nikolafilip/nibble/boards/03-sequencer/fab/sequencer-top.png

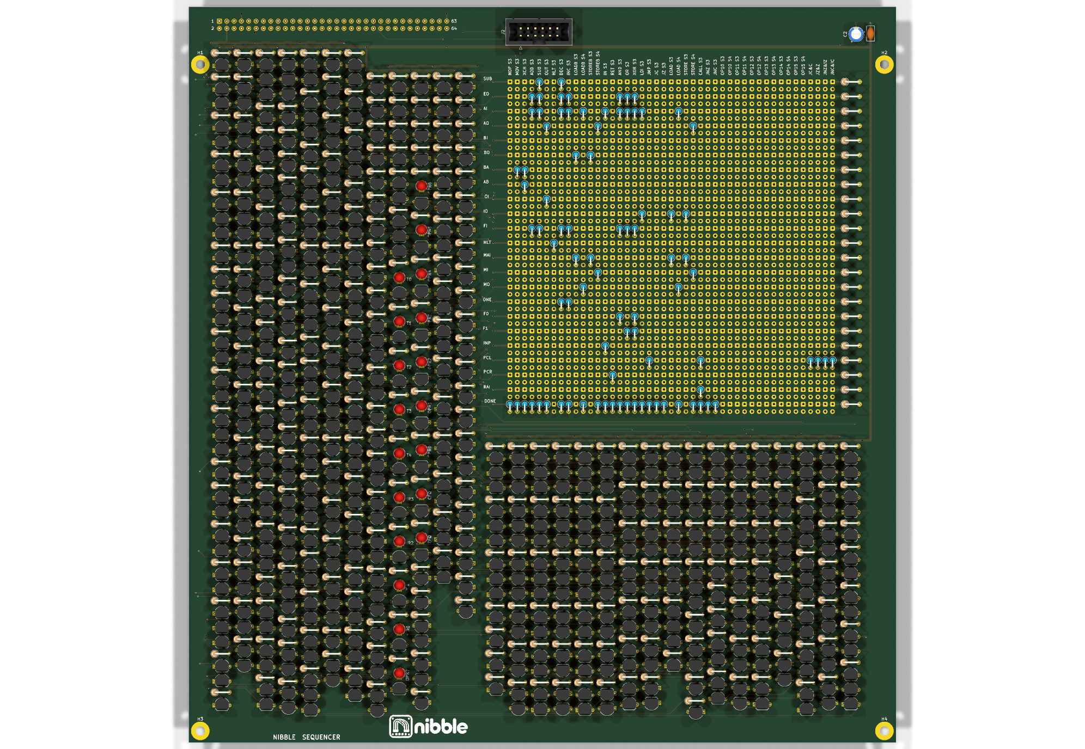
boards/03-sequencer/fab/sequencer-top.png
