nikolafilip/nibble/boards/01-alu/fab/alu-bottom.png

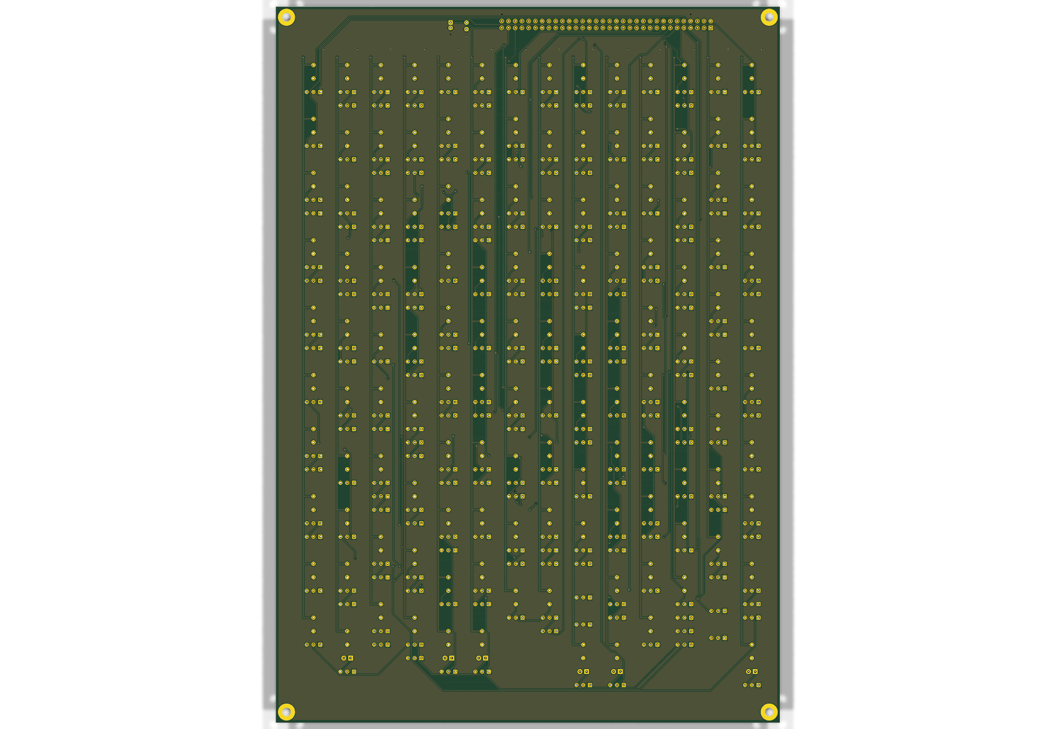
boards/01-alu/fab/alu-bottom.png
