nikolafilip/nibble/boards/01-alu/fab/alu-top.png

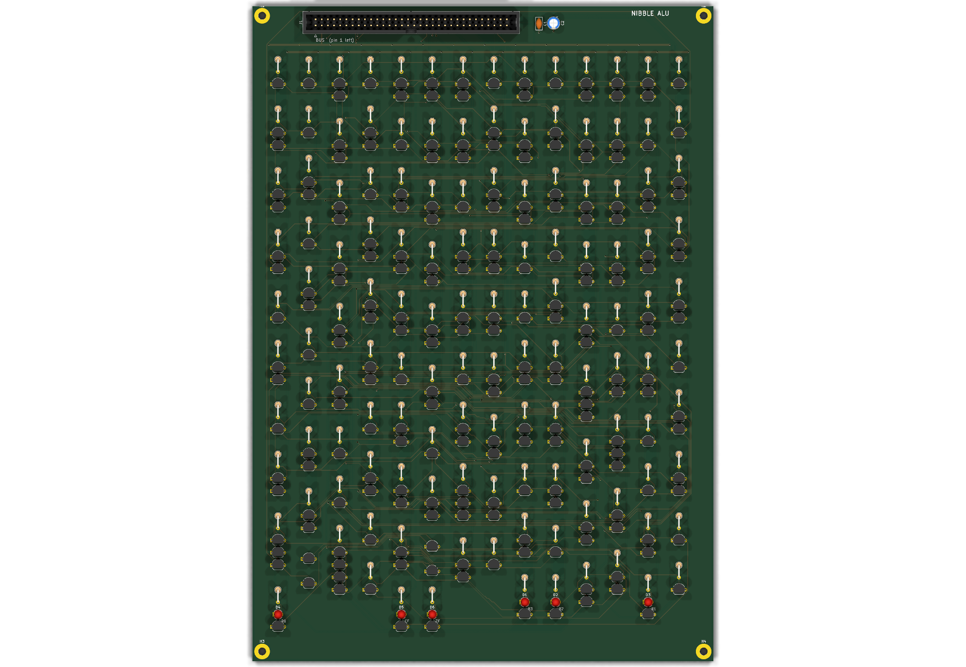
boards/01-alu/fab/alu-top.png
