nikolafilip/nibble/boards/03-sequencer/fab/sequencer-bottom.png

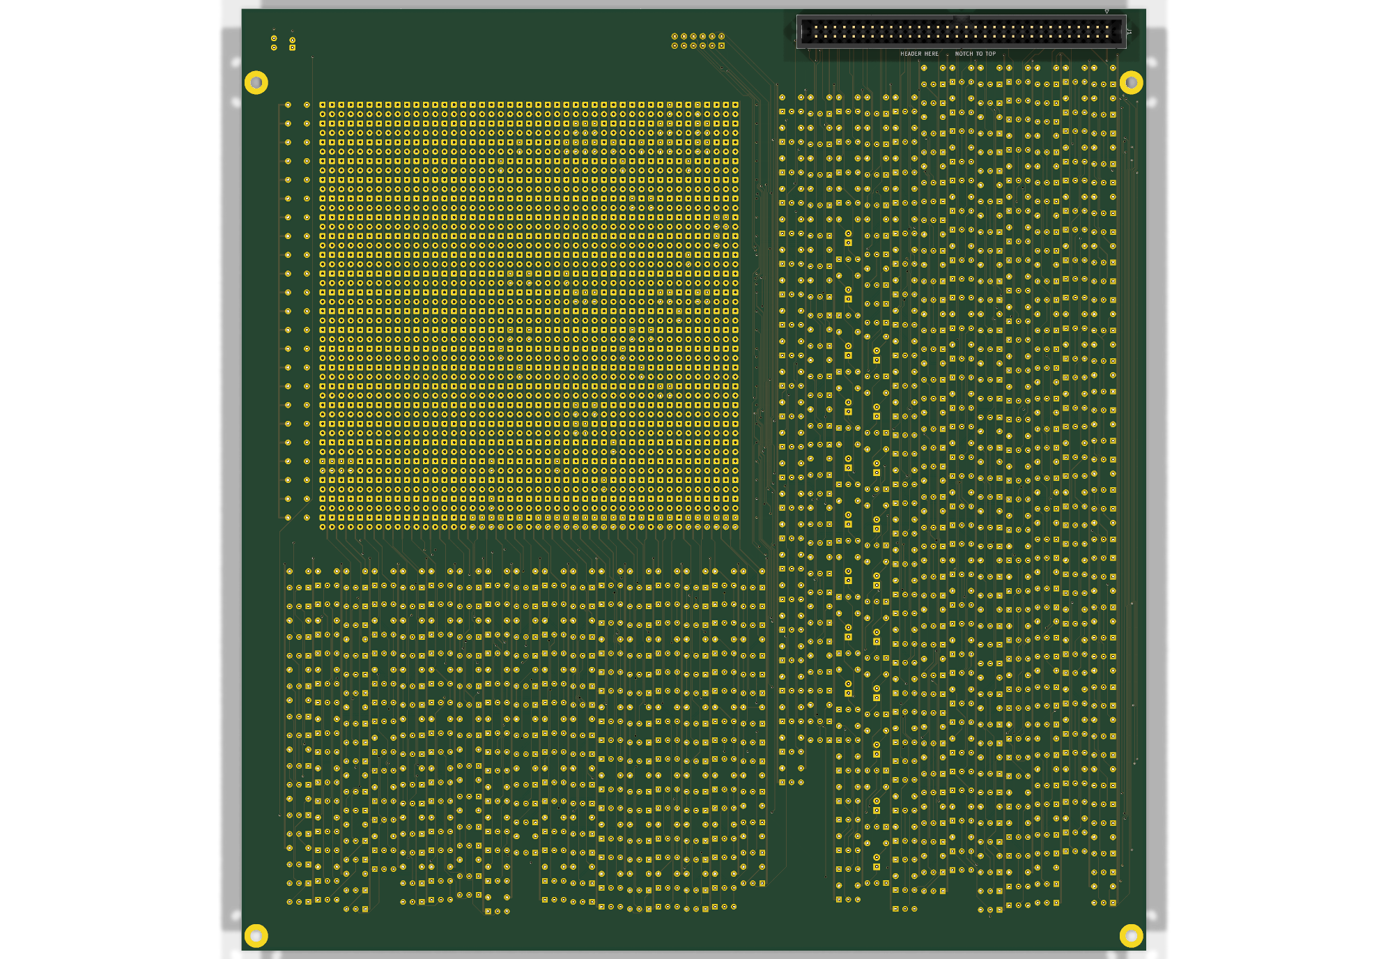
boards/03-sequencer/fab/sequencer-bottom.png
