nikolafilip/nibble/boards/06-panel/fab/panel-bottom.png

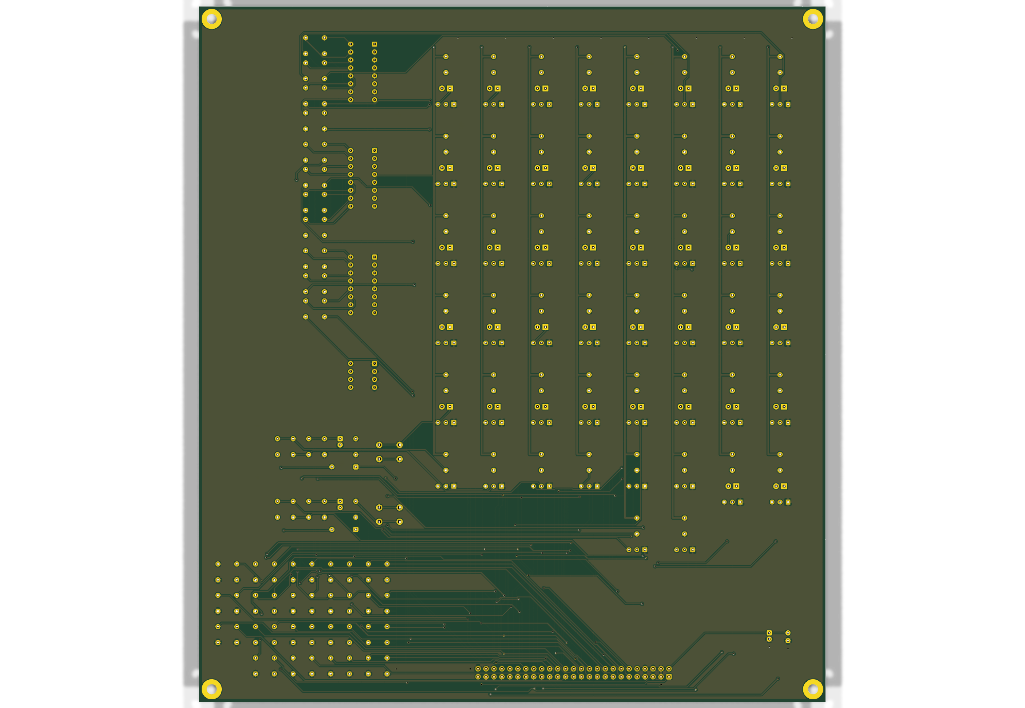
boards/06-panel/fab/panel-bottom.png
