nikolafilip/nibble/boards/06-panel/fab/panel-top.png

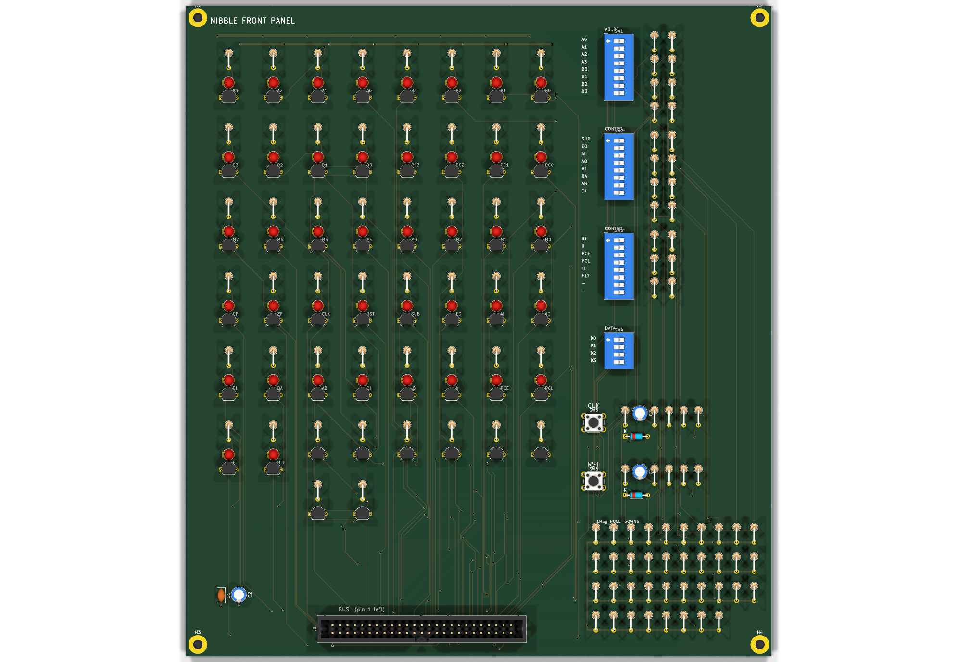
boards/06-panel/fab/panel-top.png
