nikolafilip/nibble/cards/alu0/fab/alu0-bottom.png

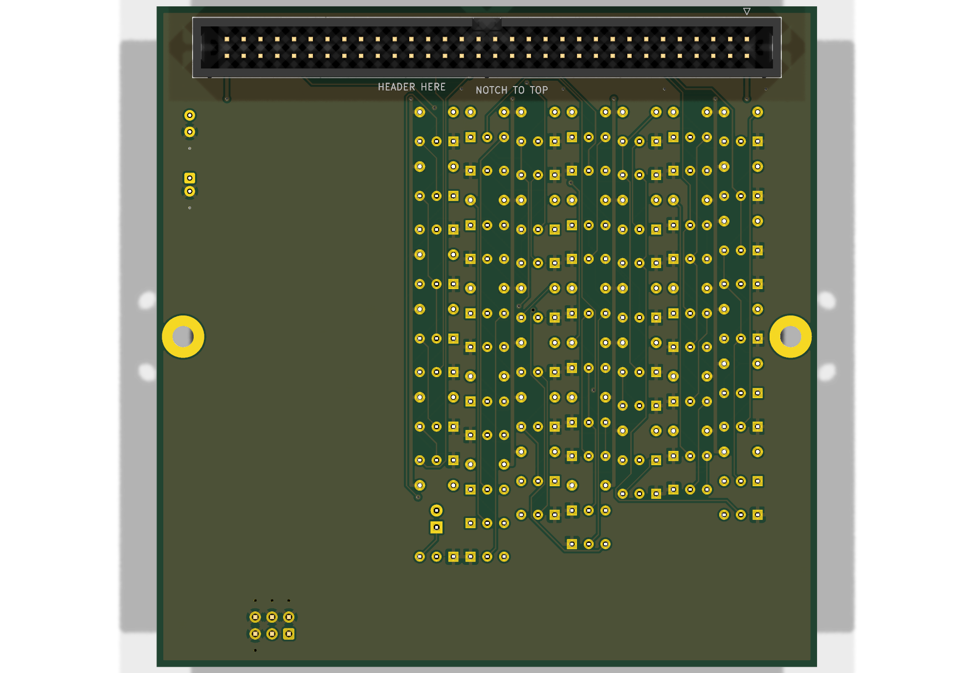
cards/alu0/fab/alu0-bottom.png
