nikolafilip/nibble/cards/alu0/fab/alu0-top.png

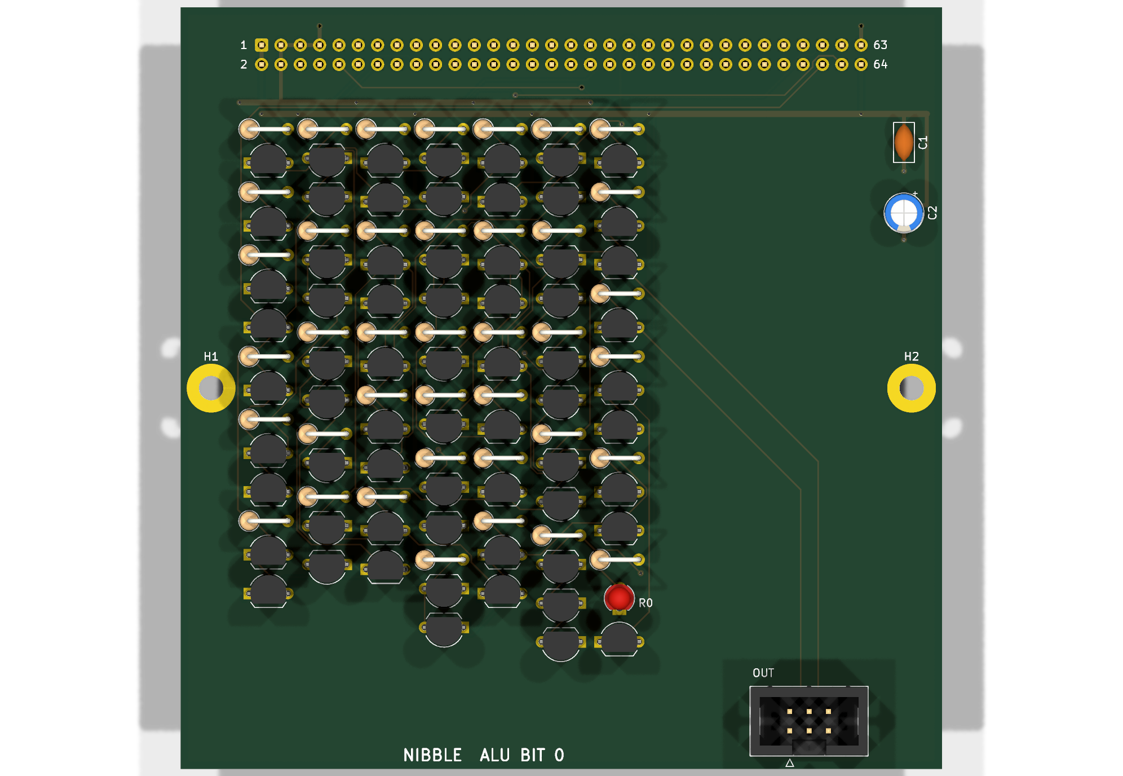
cards/alu0/fab/alu0-top.png
