nikolafilip/nibble/cards/alu1/fab/alu1-bottom.png

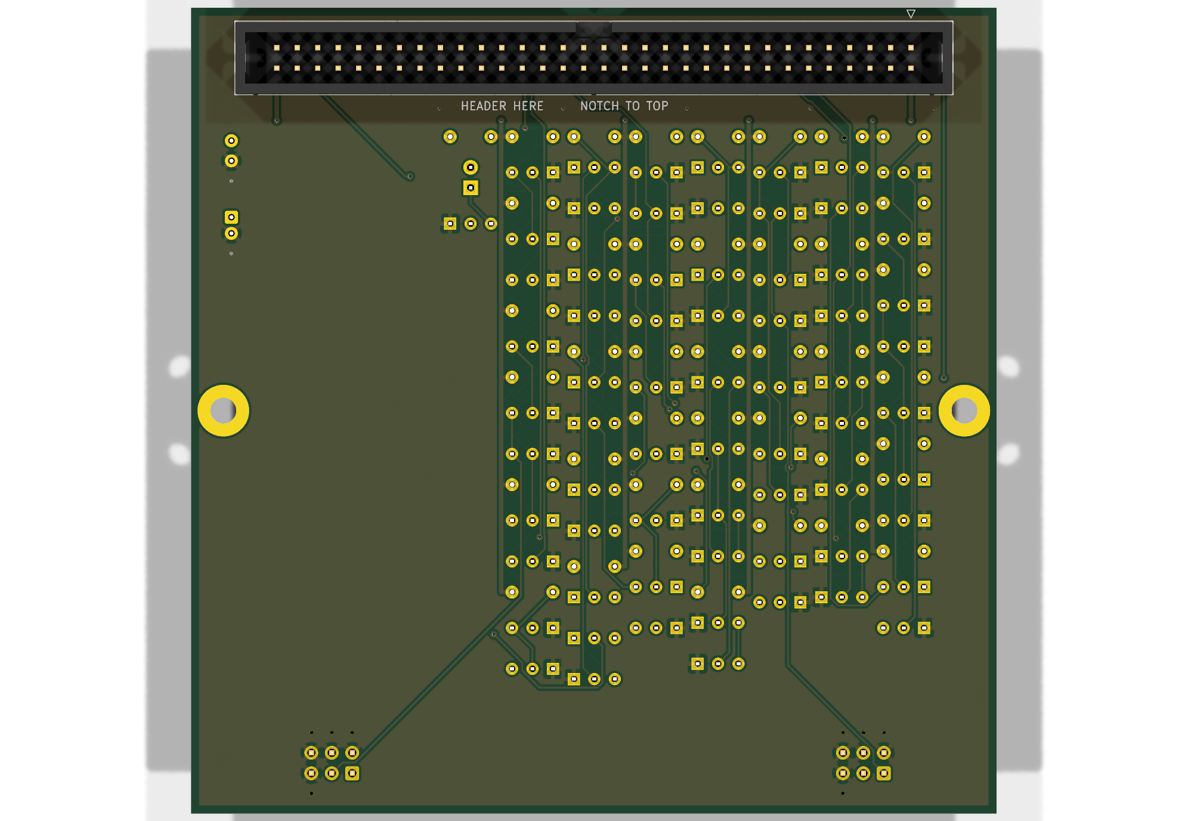
cards/alu1/fab/alu1-bottom.png
