nikolafilip/nibble/cards/alu2/fab/alu2-bottom.png

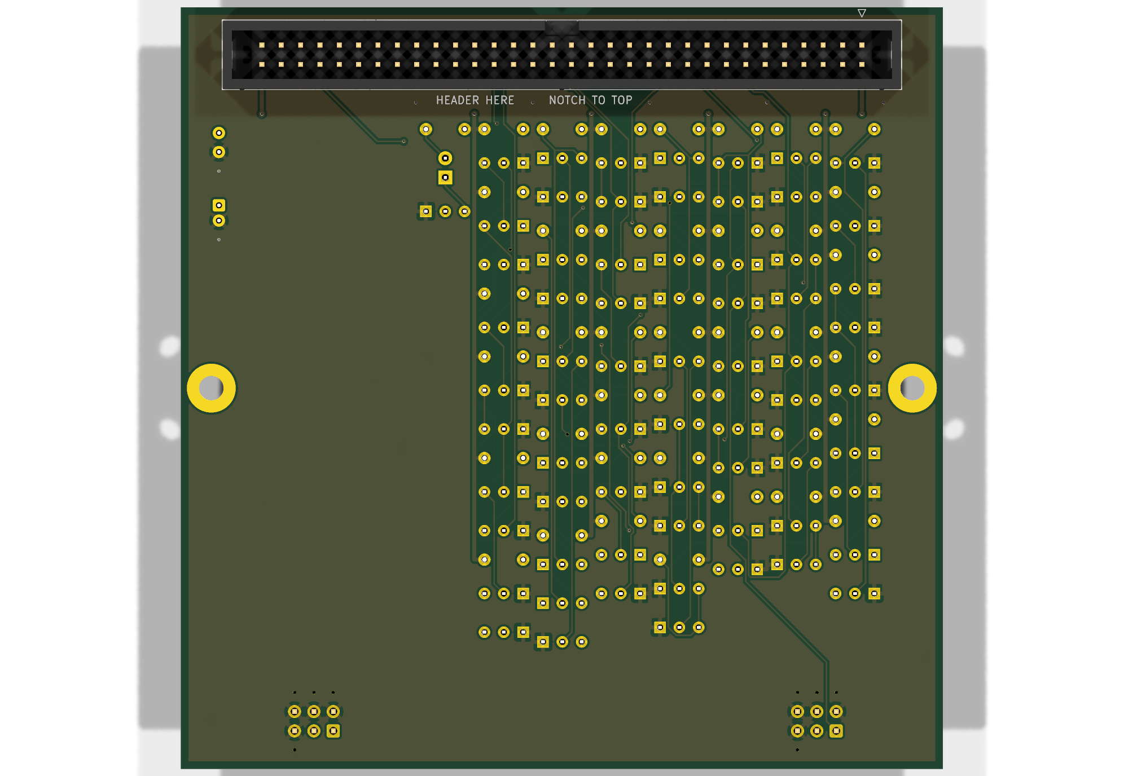
cards/alu2/fab/alu2-bottom.png
