nikolafilip/nibble/cards/clock/fab/clock-bottom.png

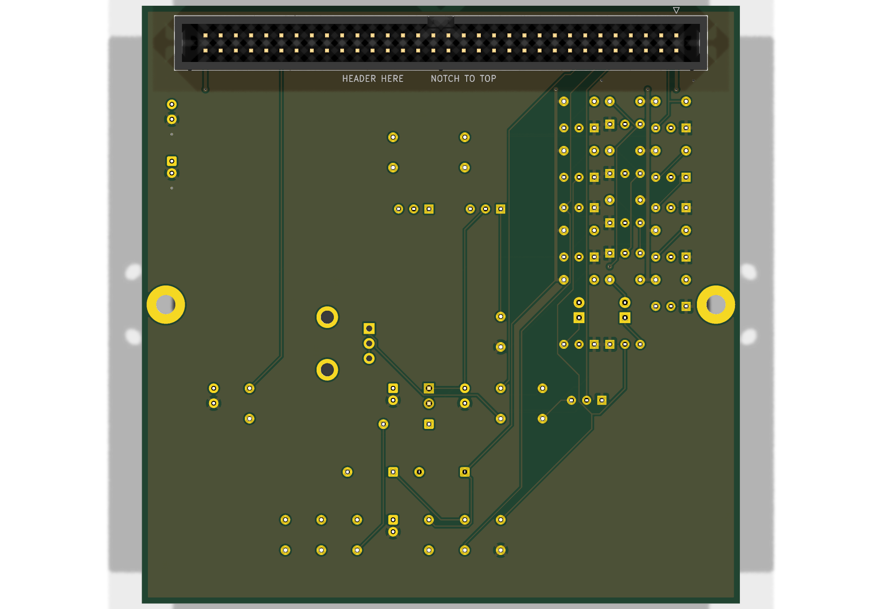
cards/clock/fab/clock-bottom.png
