nikolafilip/nibble/cards/clock/fab/clock-top.png

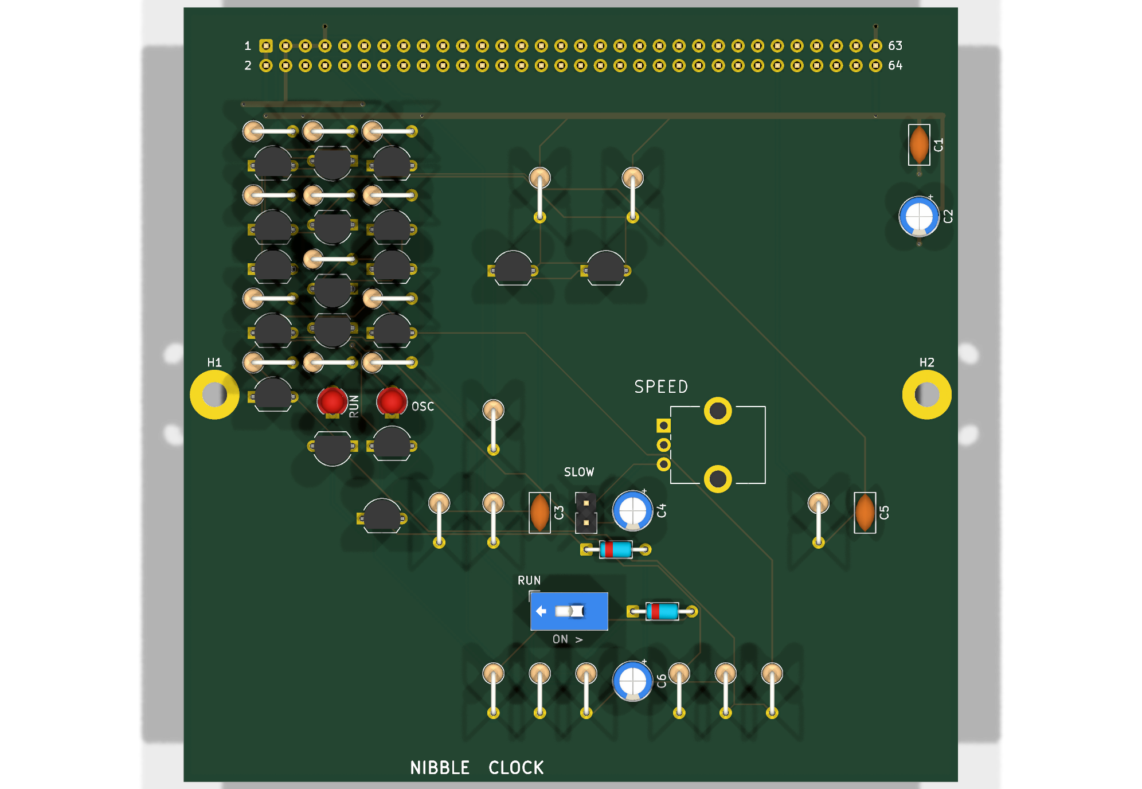
cards/clock/fab/clock-top.png
