nikolafilip/nibble/cards/coupon/fab/coupon-bottom.png

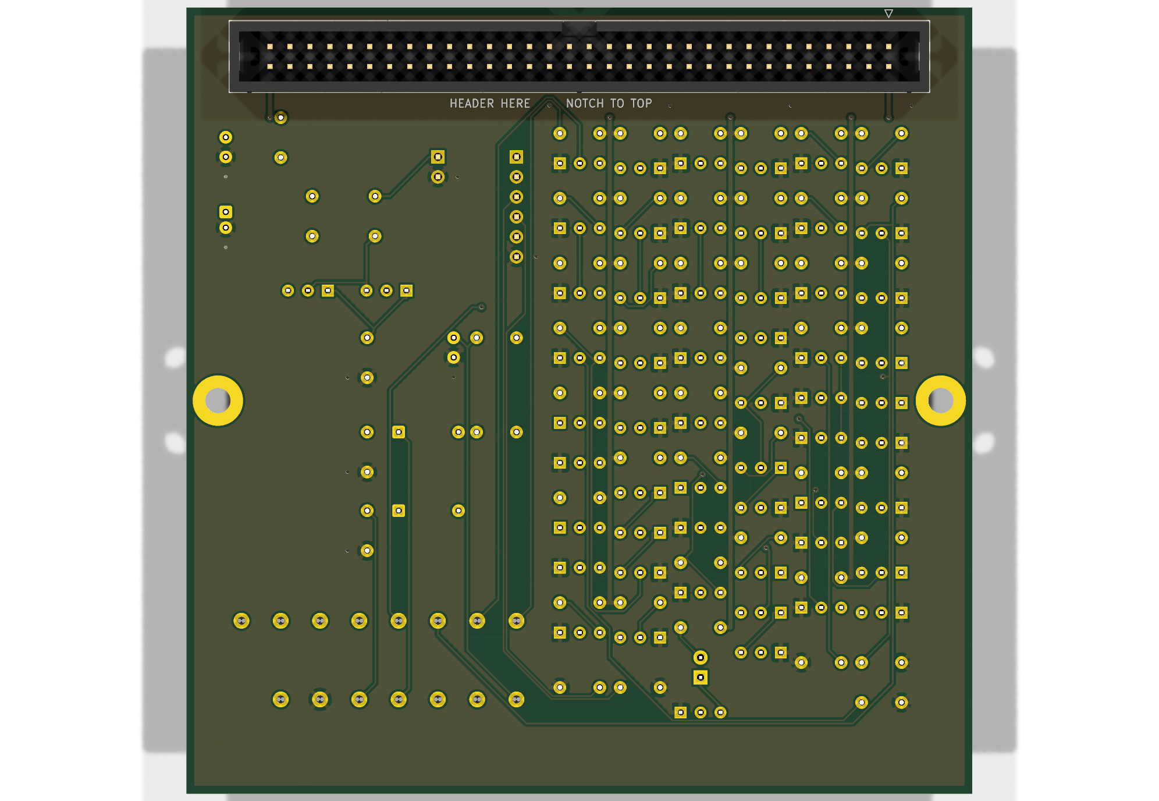
cards/coupon/fab/coupon-bottom.png
