nikolafilip/nibble/cards/coupon/fab/coupon-top.png

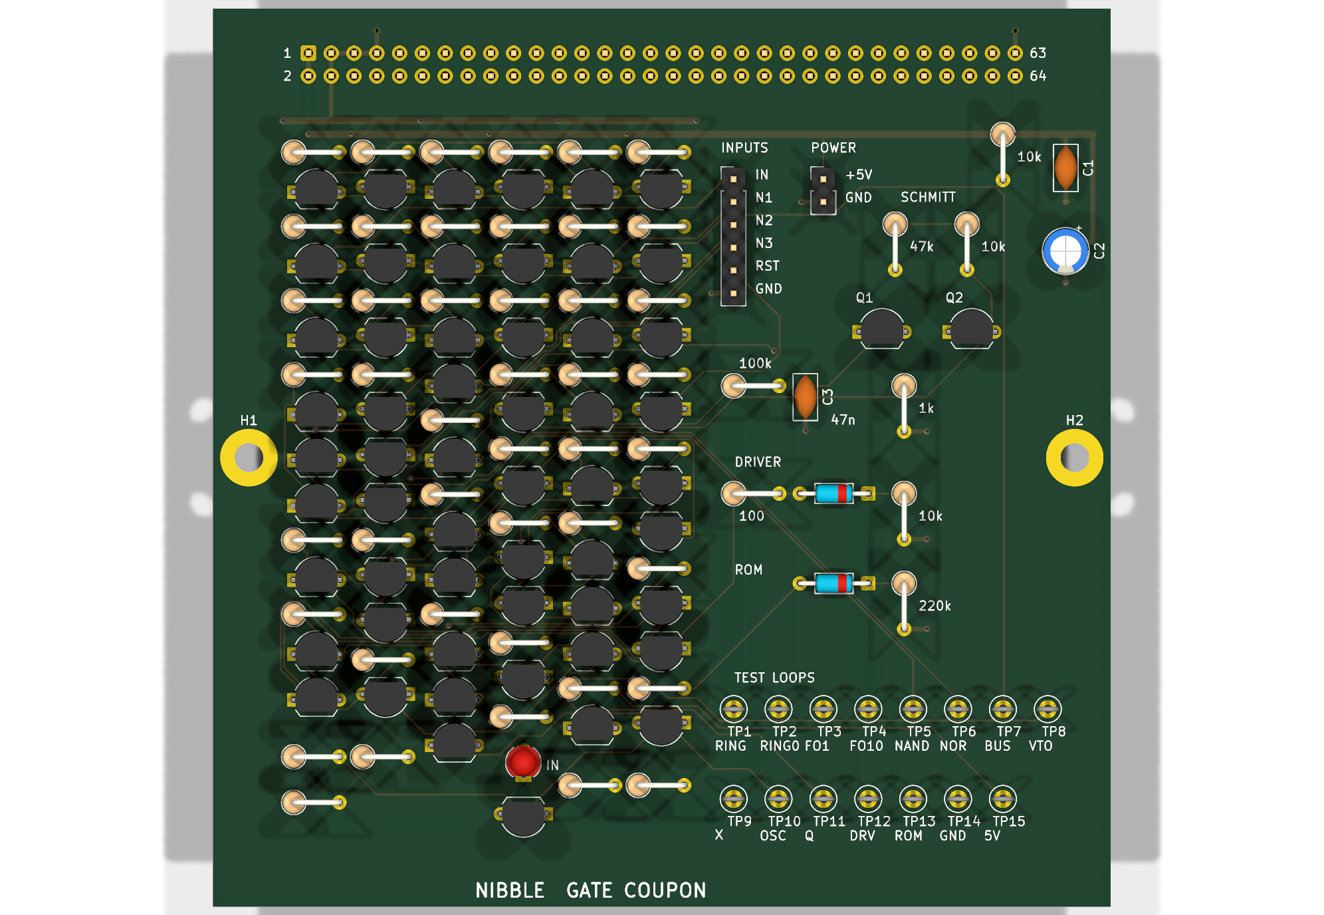
cards/coupon/fab/coupon-top.png
