nikolafilip/nibble/cards/ctr0/fab/ctr0-bottom.png

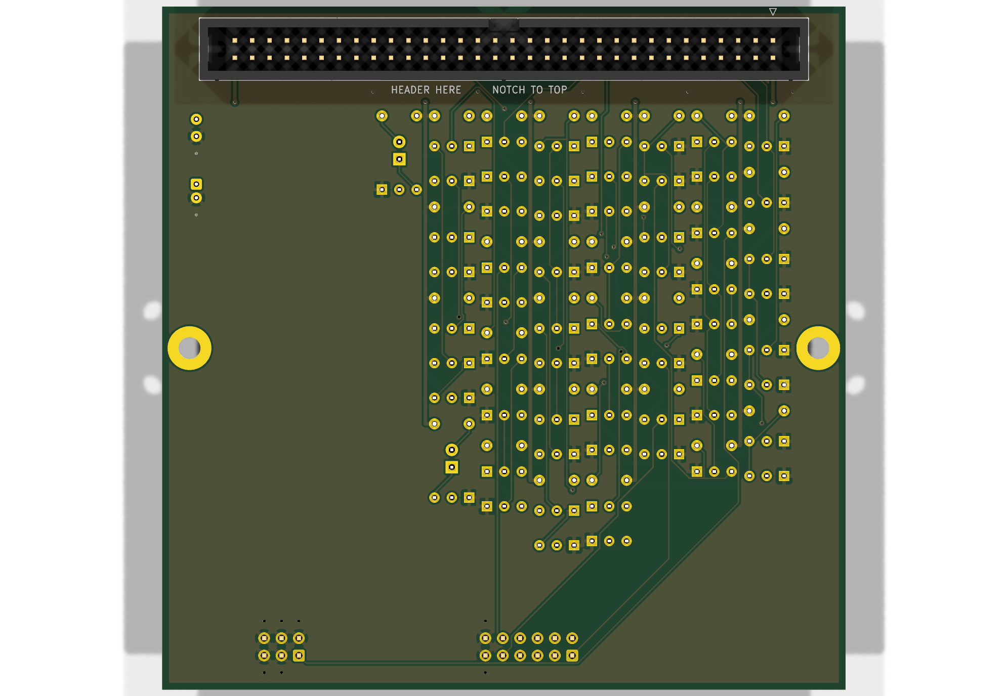
cards/ctr0/fab/ctr0-bottom.png
