nikolafilip/nibble/cards/ctr0/fab/ctr0-top.png

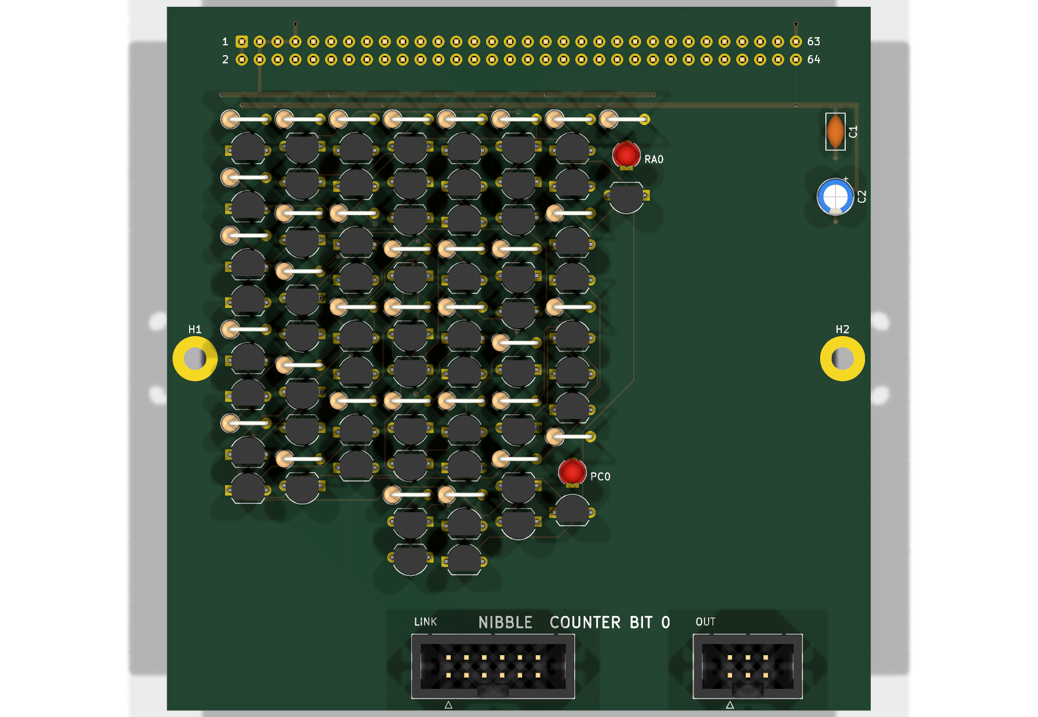
cards/ctr0/fab/ctr0-top.png
