nikolafilip/nibble/cards/ctr1/fab/ctr1-bottom.png

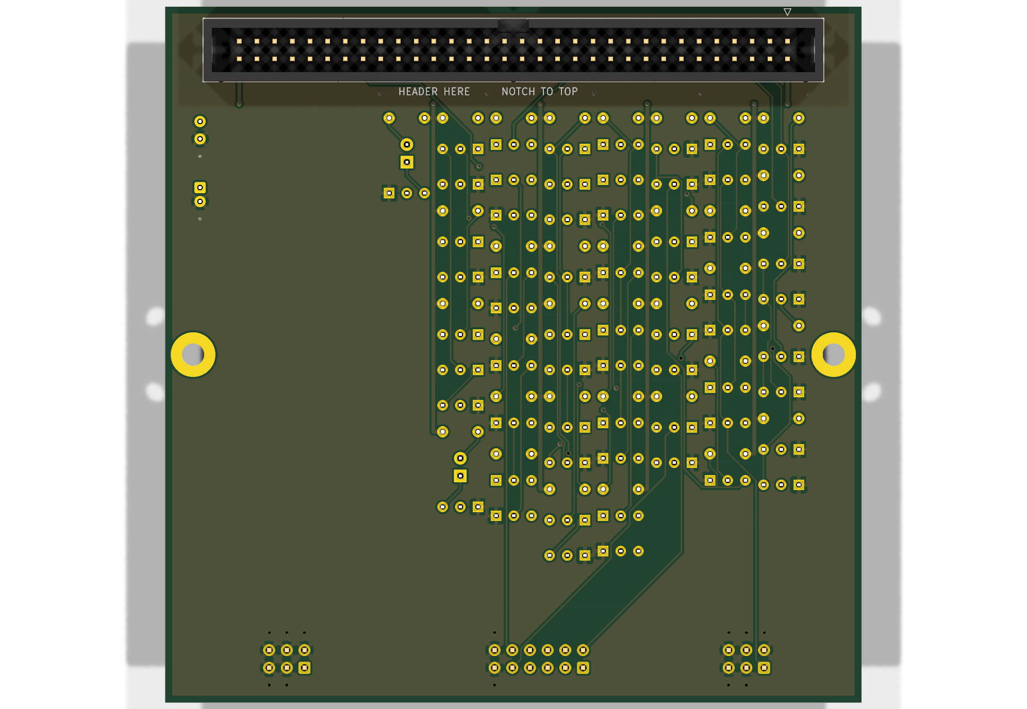
cards/ctr1/fab/ctr1-bottom.png
