nikolafilip/nibble/cards/ctr2/fab/ctr2-top.png

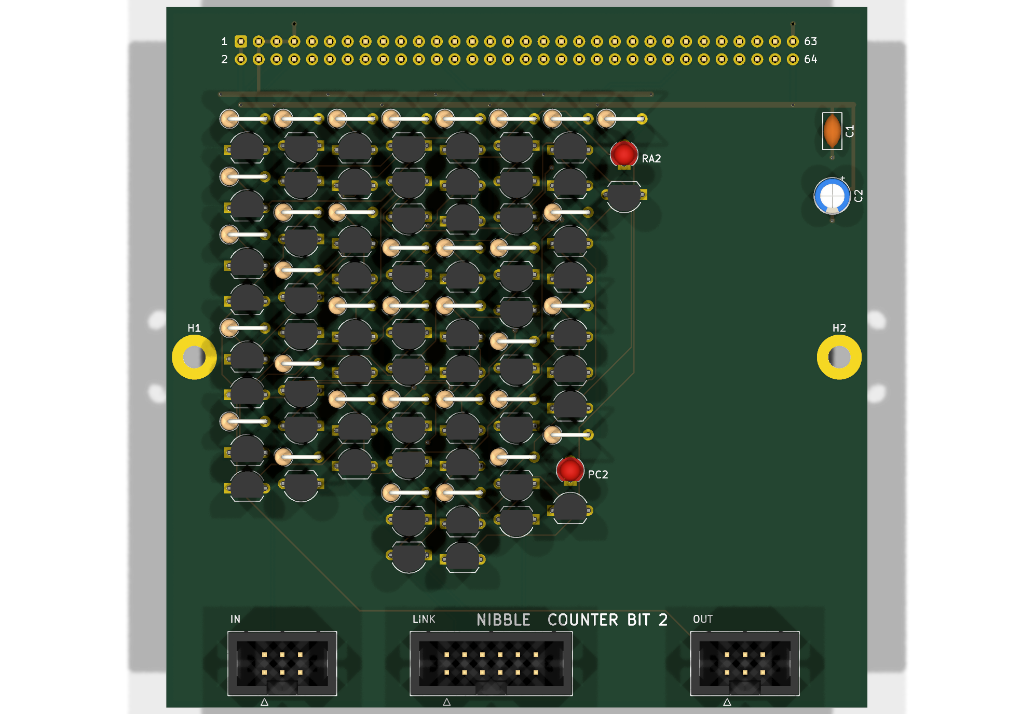
cards/ctr2/fab/ctr2-top.png
