nikolafilip/nibble/cards/ctr4/fab/ctr4-bottom.png

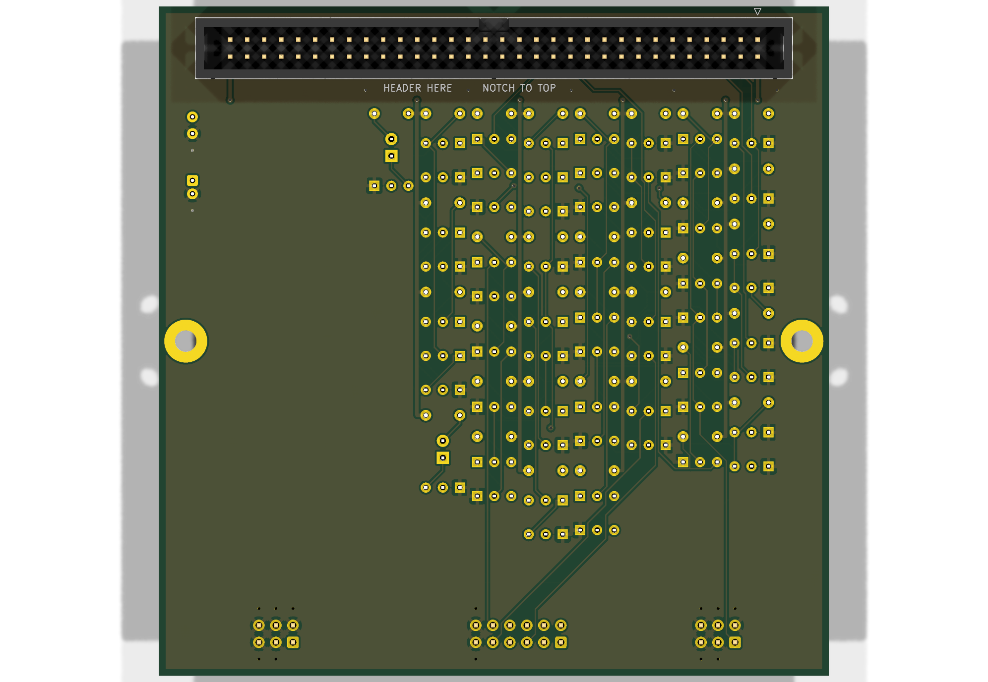
cards/ctr4/fab/ctr4-bottom.png
