nikolafilip/nibble/cards/ctr7/fab/ctr7-bottom.png

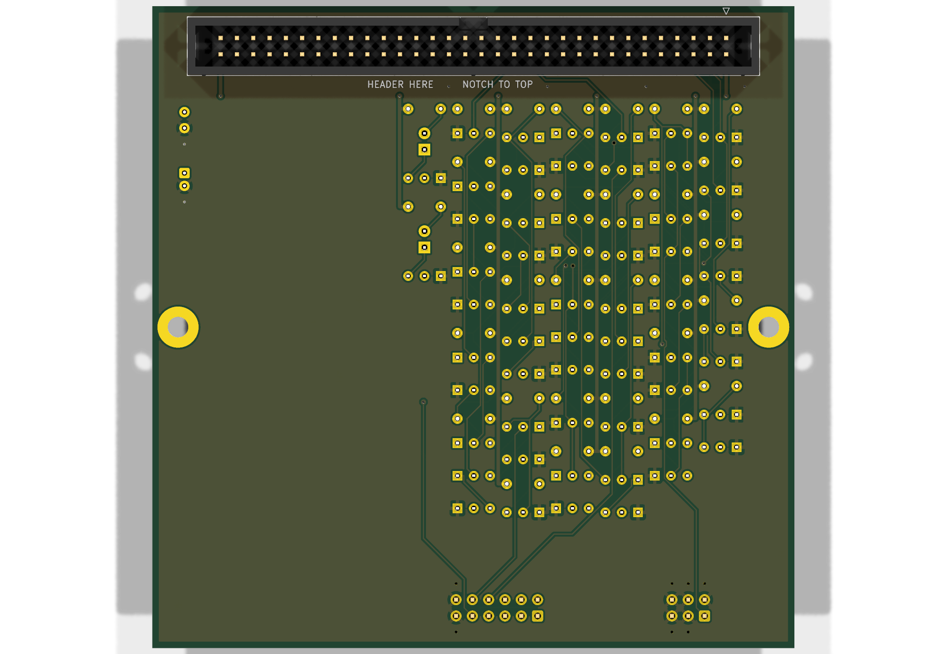
cards/ctr7/fab/ctr7-bottom.png
