nikolafilip/nibble/cards/ctr7/fab/ctr7-top.png

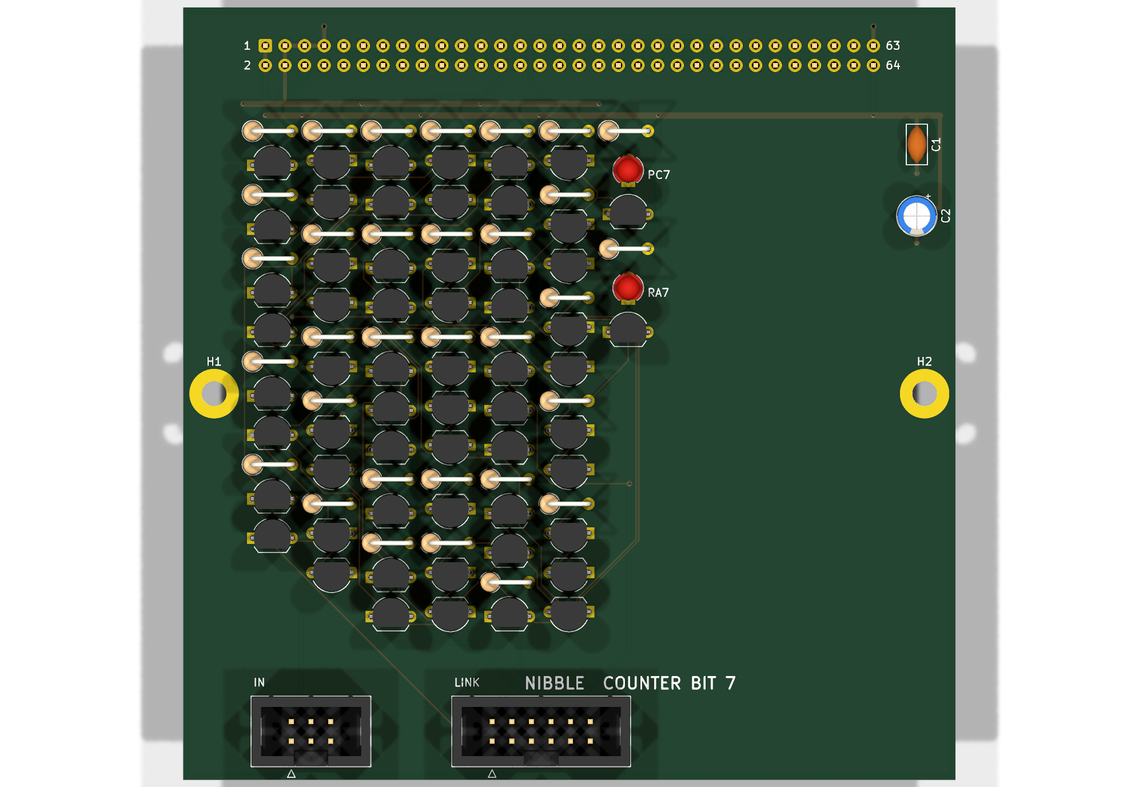
cards/ctr7/fab/ctr7-top.png
