nikolafilip/nibble/cards/hub/fab/hub-bottom.png

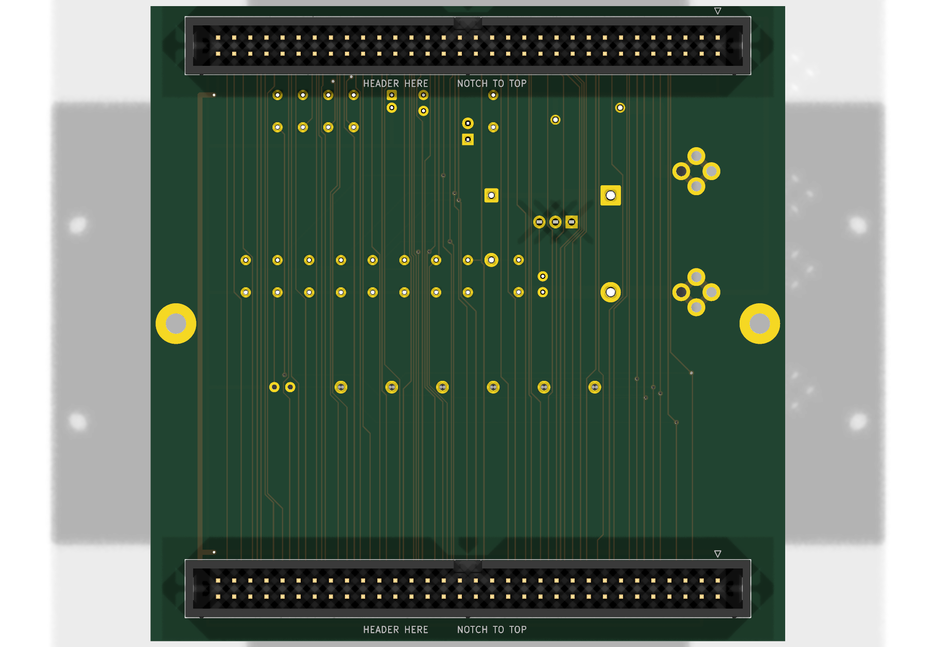
cards/hub/fab/hub-bottom.png
