nikolafilip/nibble/cards/hub/fab/hub-top.png

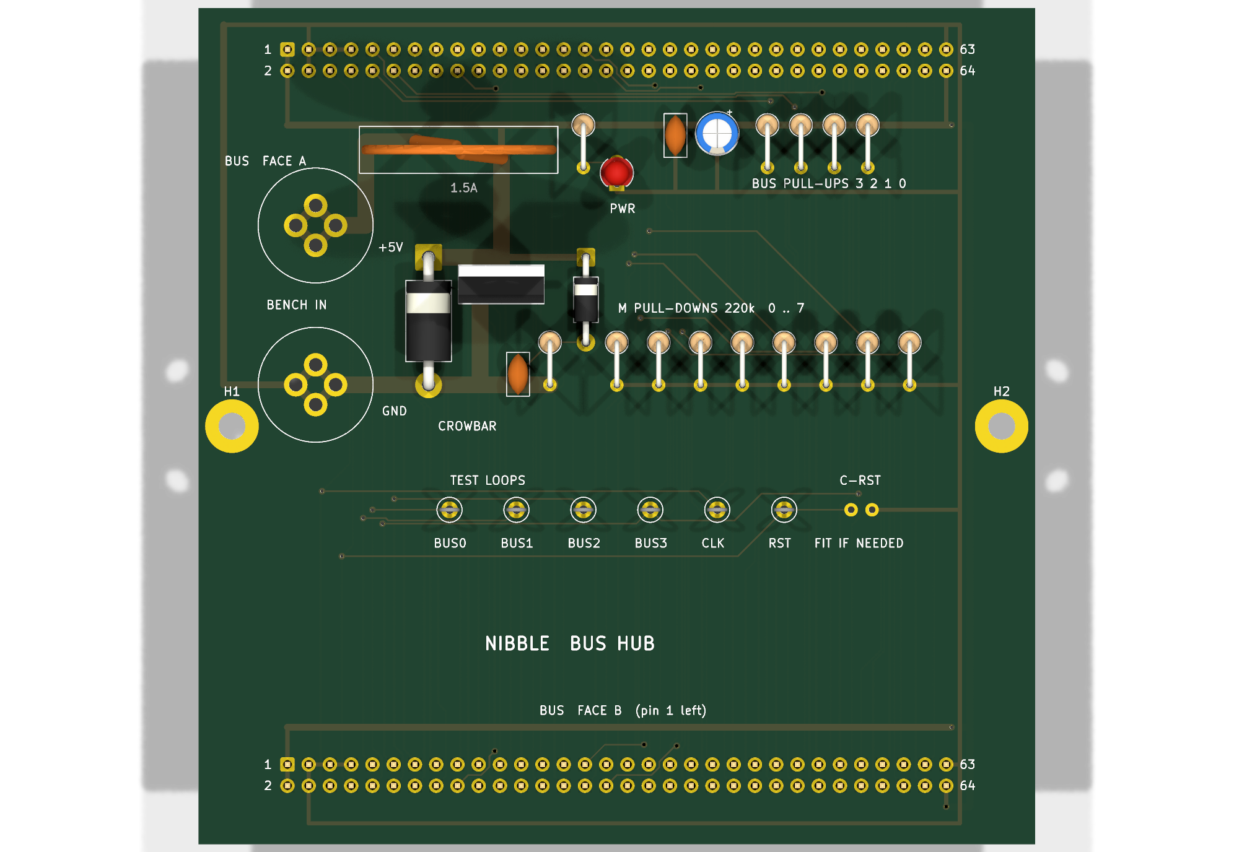
cards/hub/fab/hub-top.png
