nikolafilip/nibble/cards/memctl/fab/memctl-bottom.png

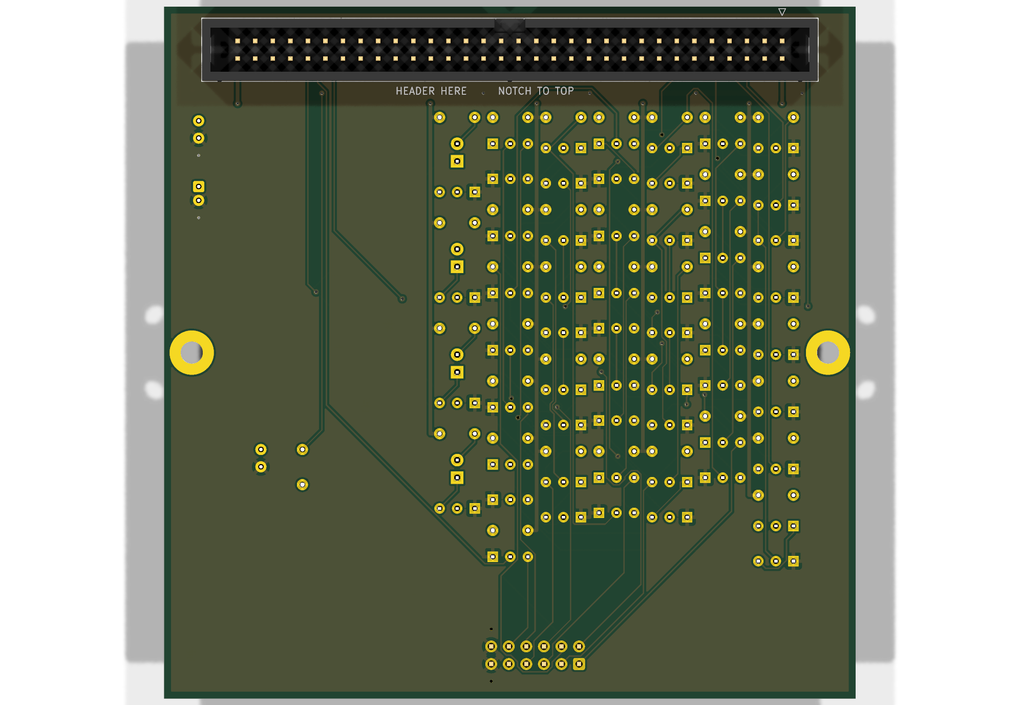
cards/memctl/fab/memctl-bottom.png
