nikolafilip/nibble/cards/memctl/fab/memctl-top.png

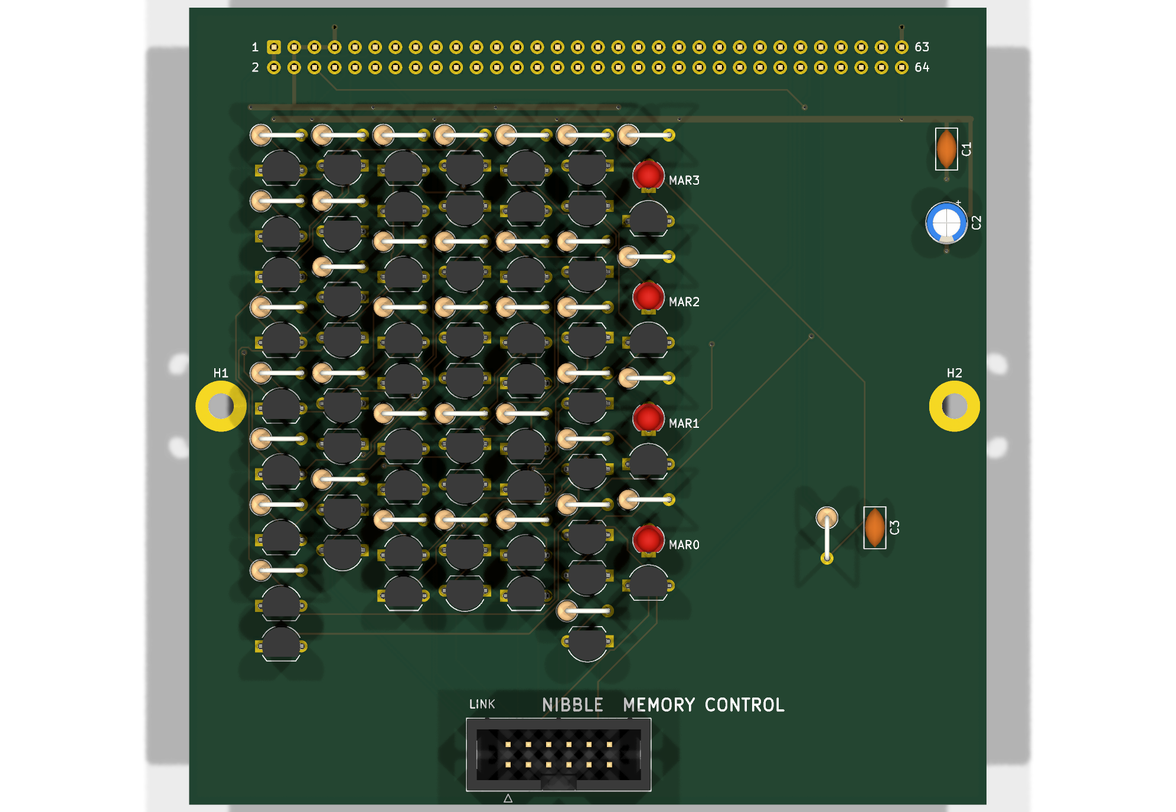
cards/memctl/fab/memctl-top.png
