nikolafilip/nibble/cards/memslot/fab/memslot-bottom.png

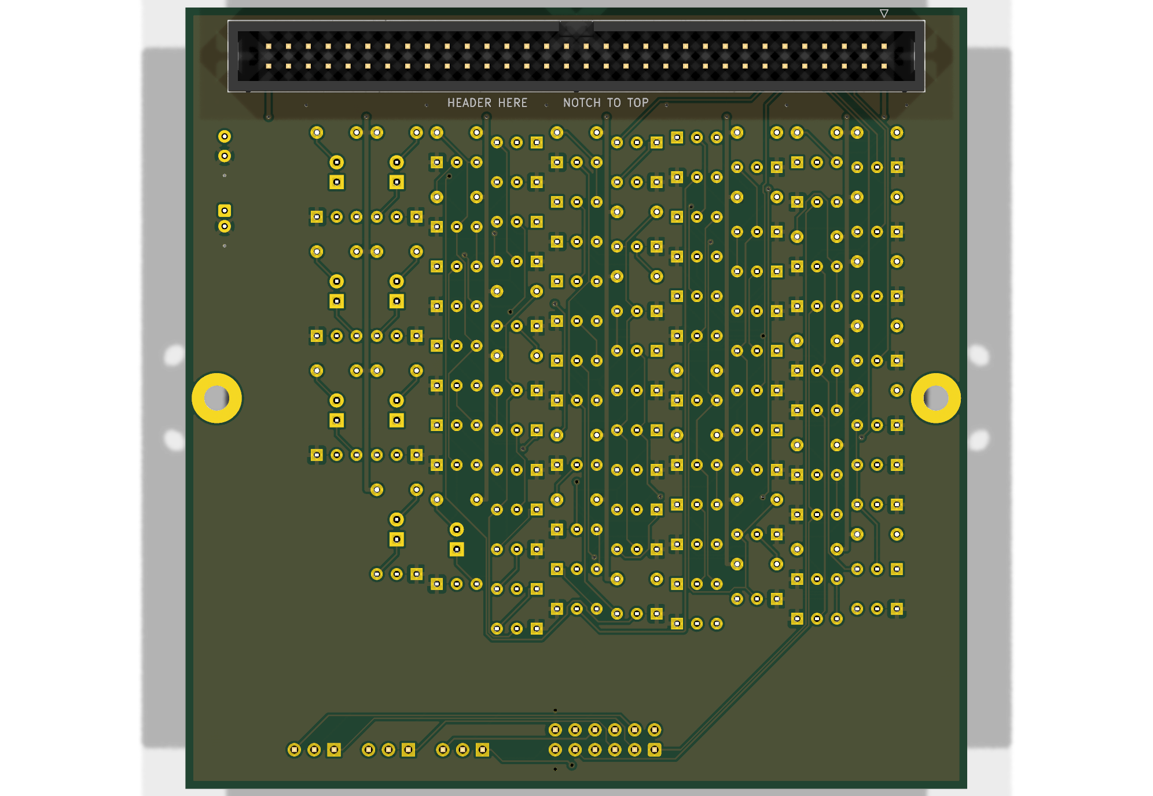
cards/memslot/fab/memslot-bottom.png
