nikolafilip/nibble/cards/memslot/fab/memslot-top.png

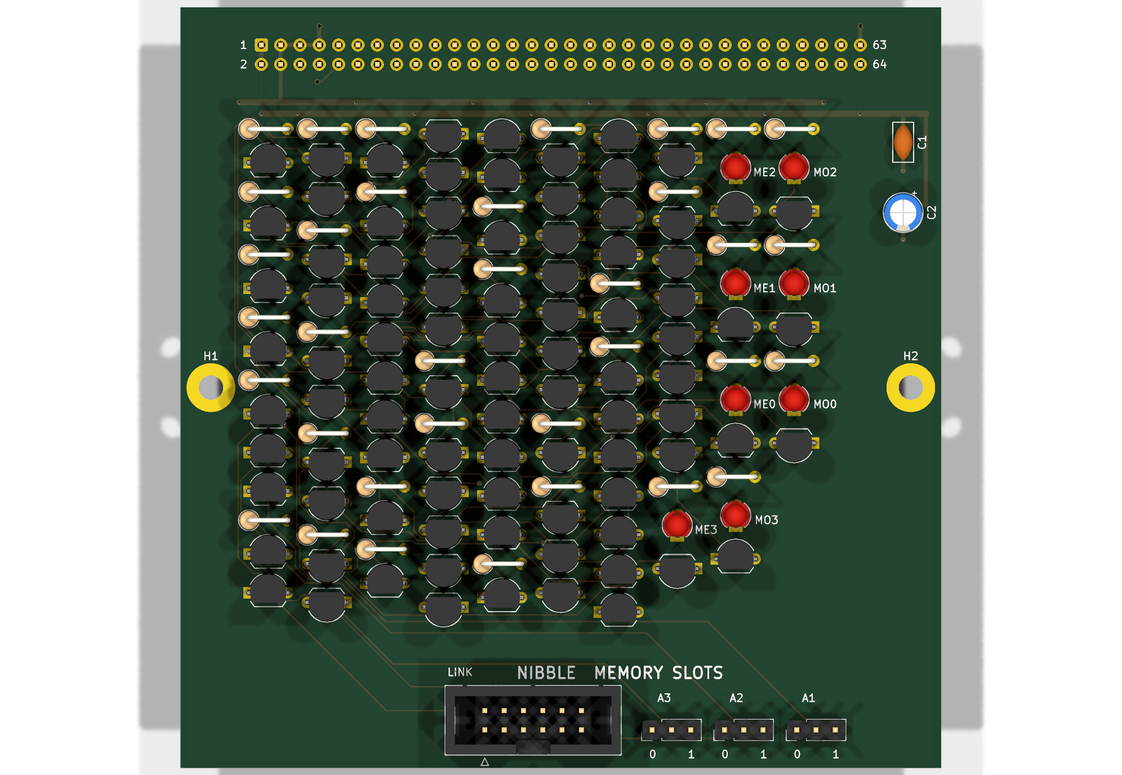
cards/memslot/fab/memslot-top.png
