nikolafilip/nibble/cards/panela/fab/panela-bottom.png

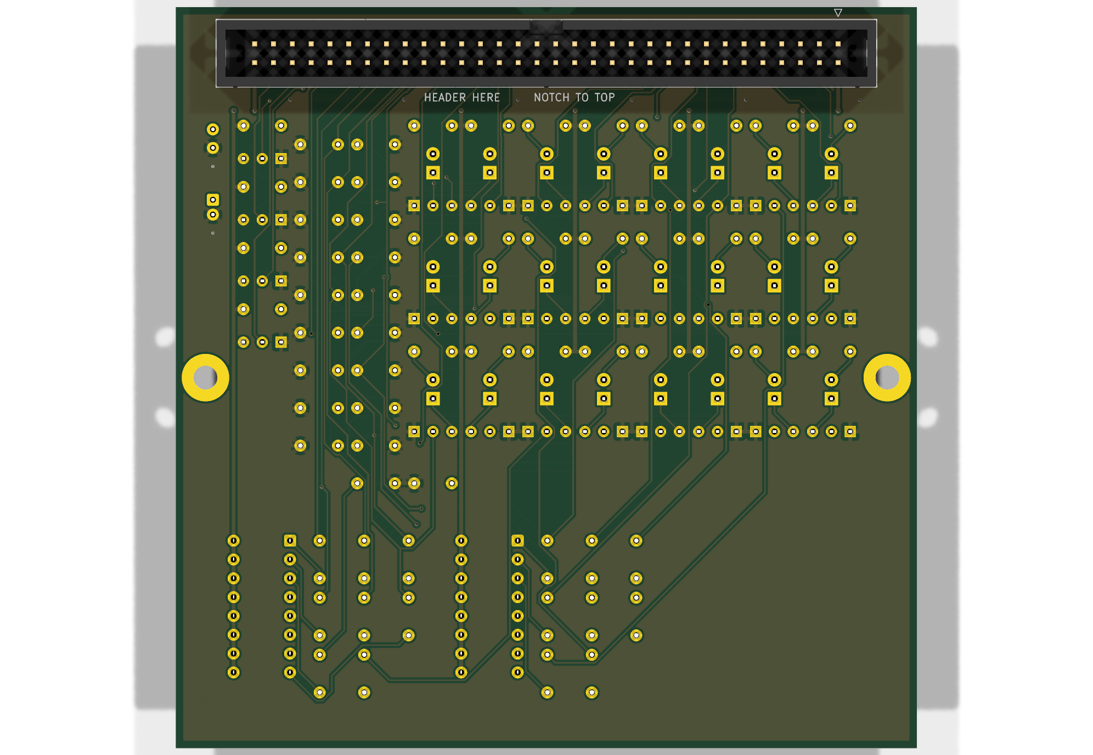
cards/panela/fab/panela-bottom.png
