nikolafilip/nibble/cards/panela/fab/panela-top.png

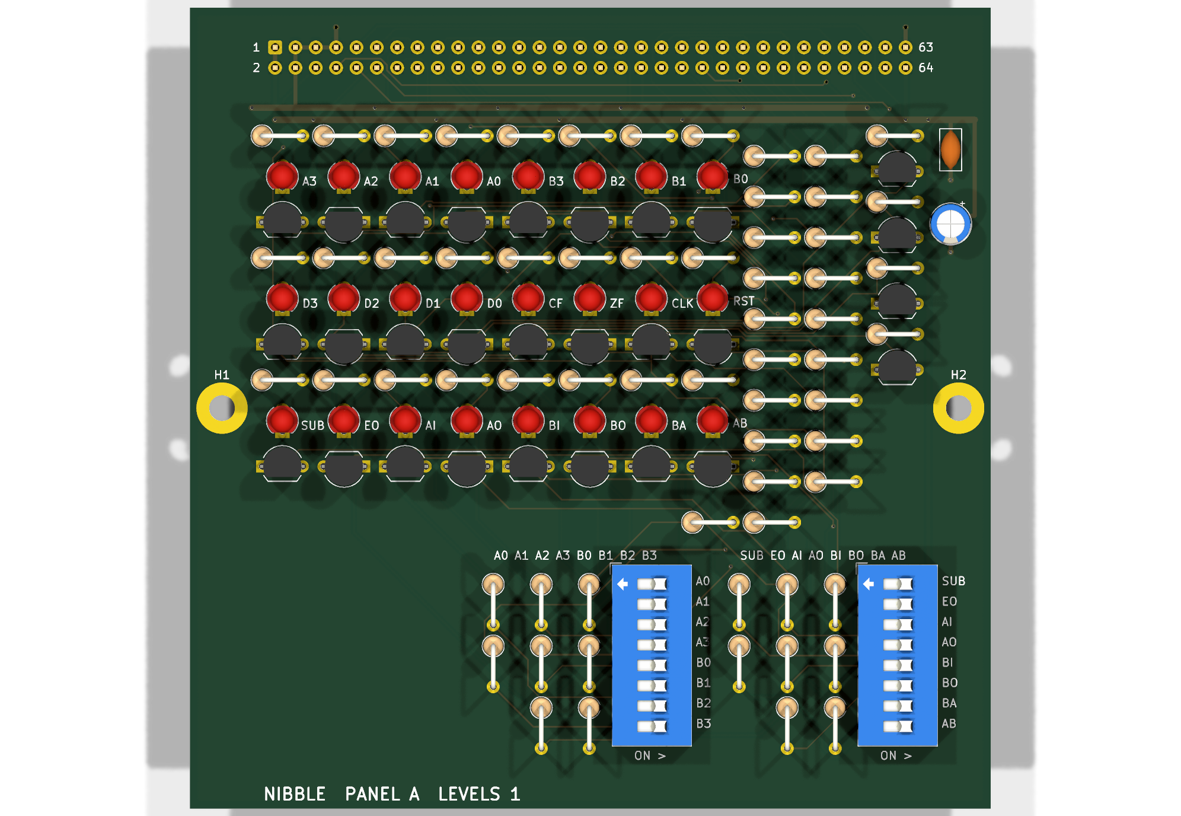
cards/panela/fab/panela-top.png
