nikolafilip/nibble/cards/panelb/fab/panelb-bottom.png

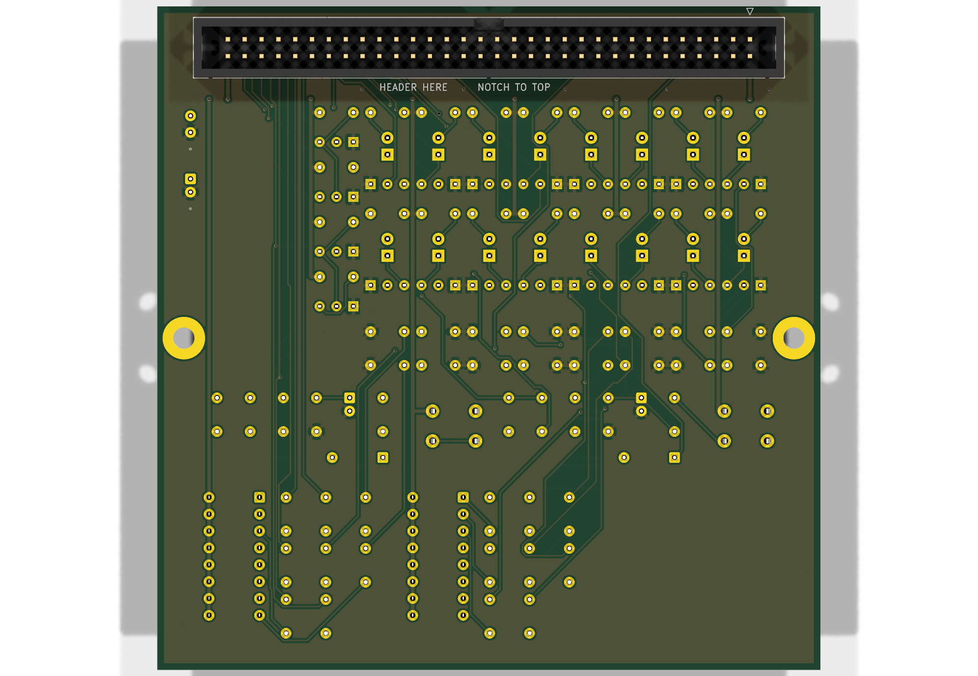
cards/panelb/fab/panelb-bottom.png
