nikolafilip/nibble/cards/panelb/fab/panelb-top.png

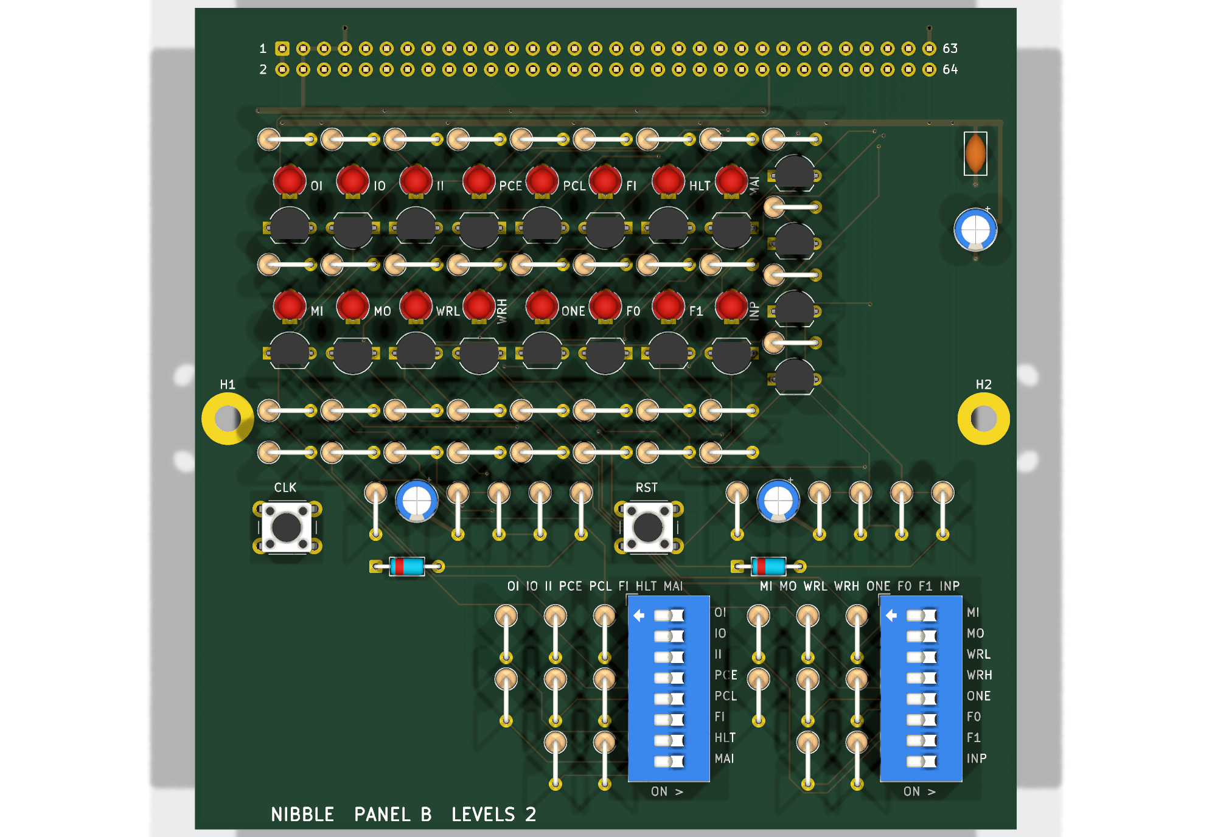
cards/panelb/fab/panelb-top.png
