nikolafilip/nibble/cards/panelc/fab/panelc-bottom.png

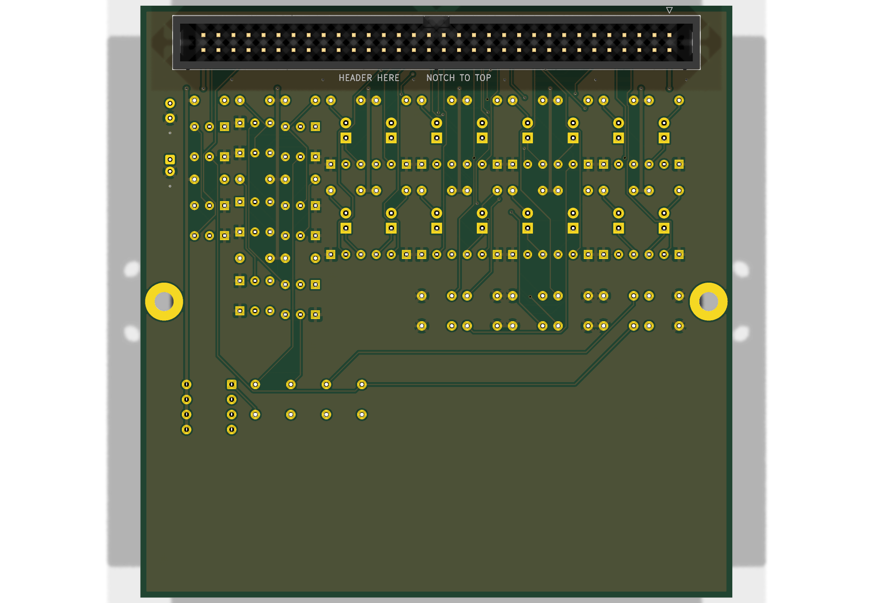
cards/panelc/fab/panelc-bottom.png
