nikolafilip/nibble/cards/panelc/fab/panelc-top.png

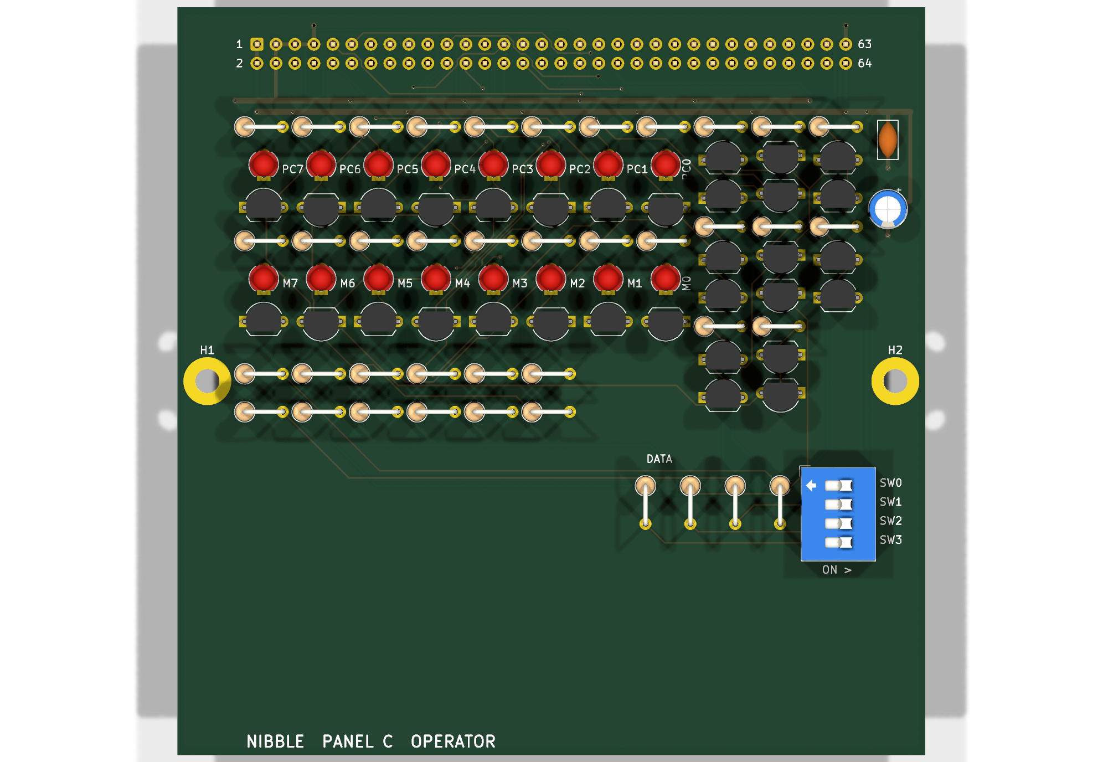
cards/panelc/fab/panelc-top.png
