nikolafilip/nibble/cards/prog/fab/prog-bottom.png

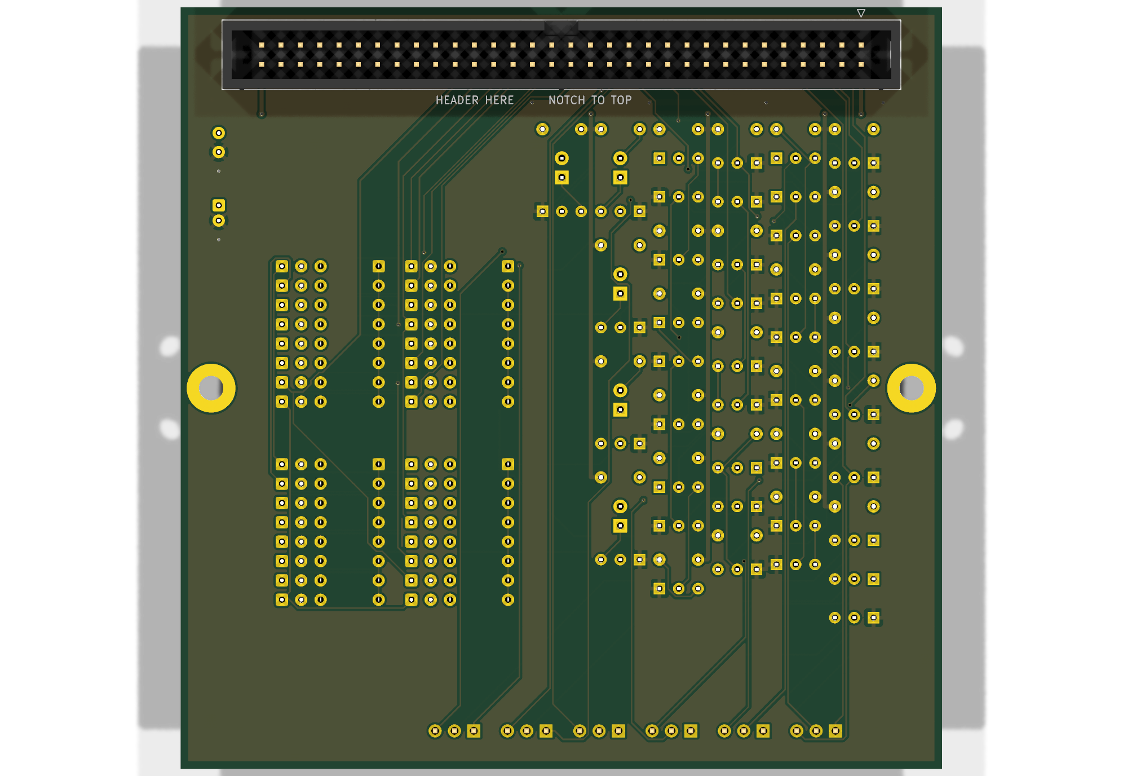
cards/prog/fab/prog-bottom.png
