nikolafilip/nibble/cards/prog/fab/prog-top.png

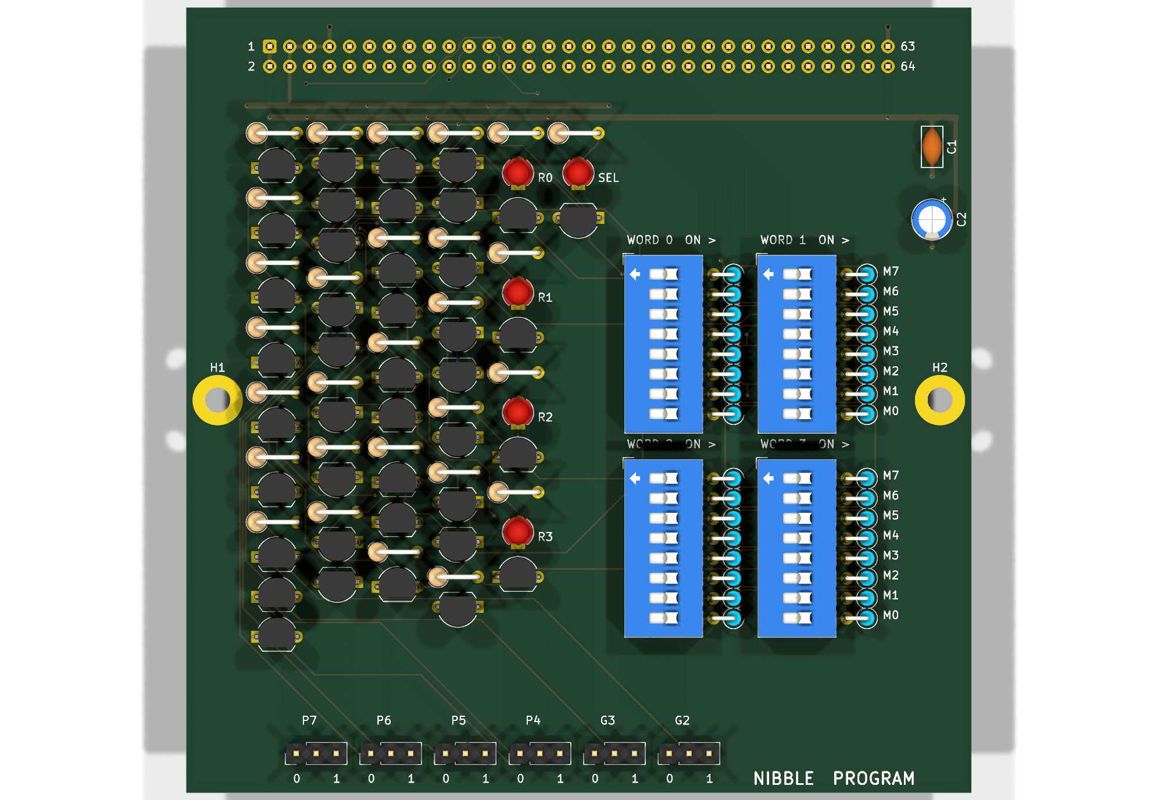
cards/prog/fab/prog-top.png
