nikolafilip/nibble/cards/reg0/fab/reg0-bottom.png

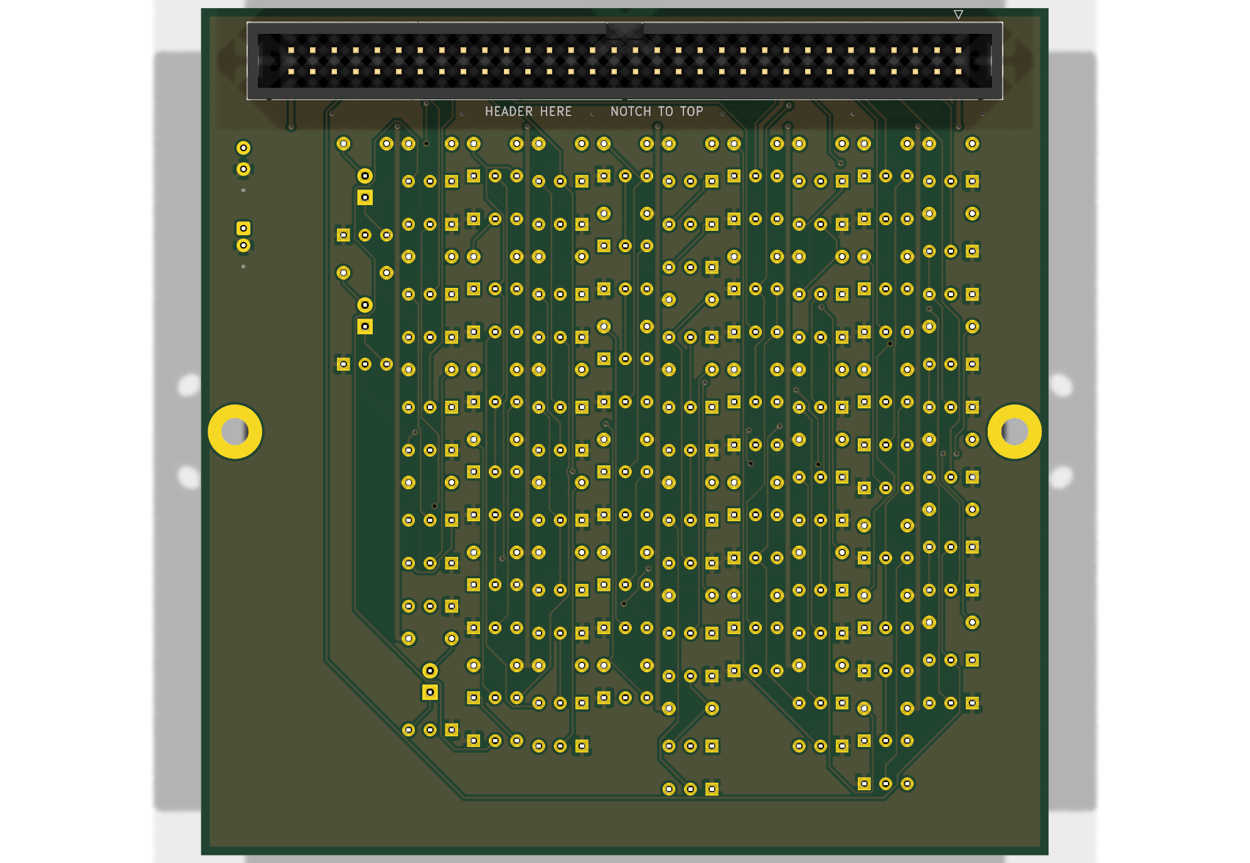
cards/reg0/fab/reg0-bottom.png
