nikolafilip/nibble/cards/reg0/fab/reg0-top.png

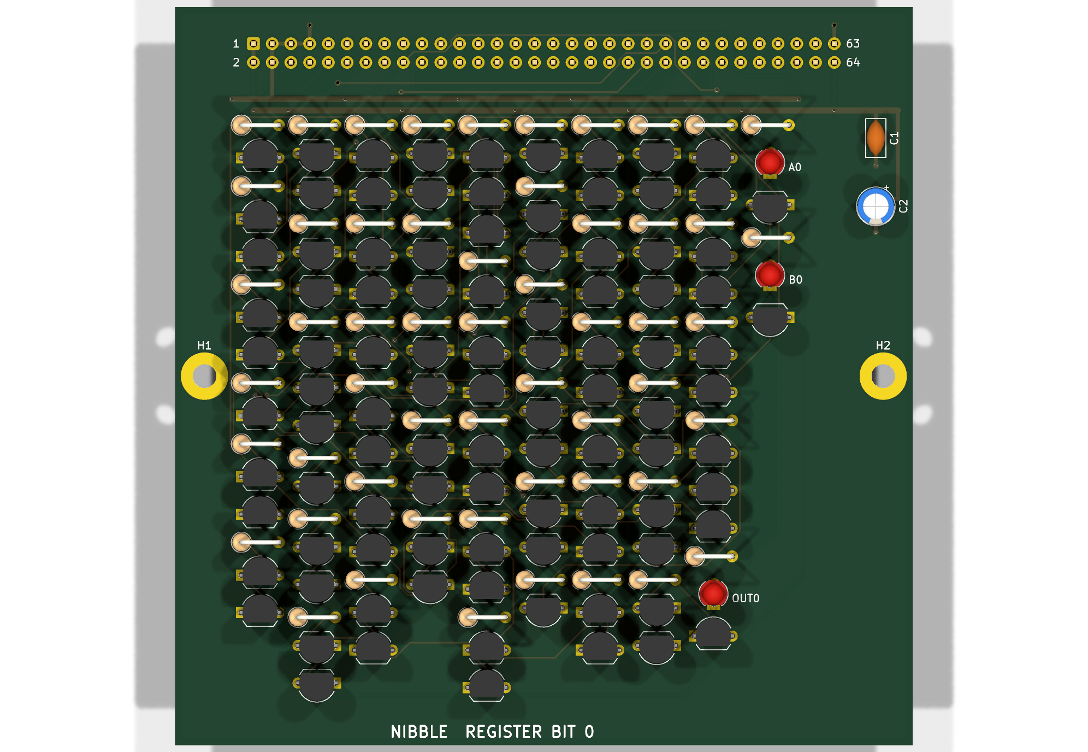
cards/reg0/fab/reg0-top.png
