nikolafilip/nibble/cards/reg2/fab/reg2-bottom.png

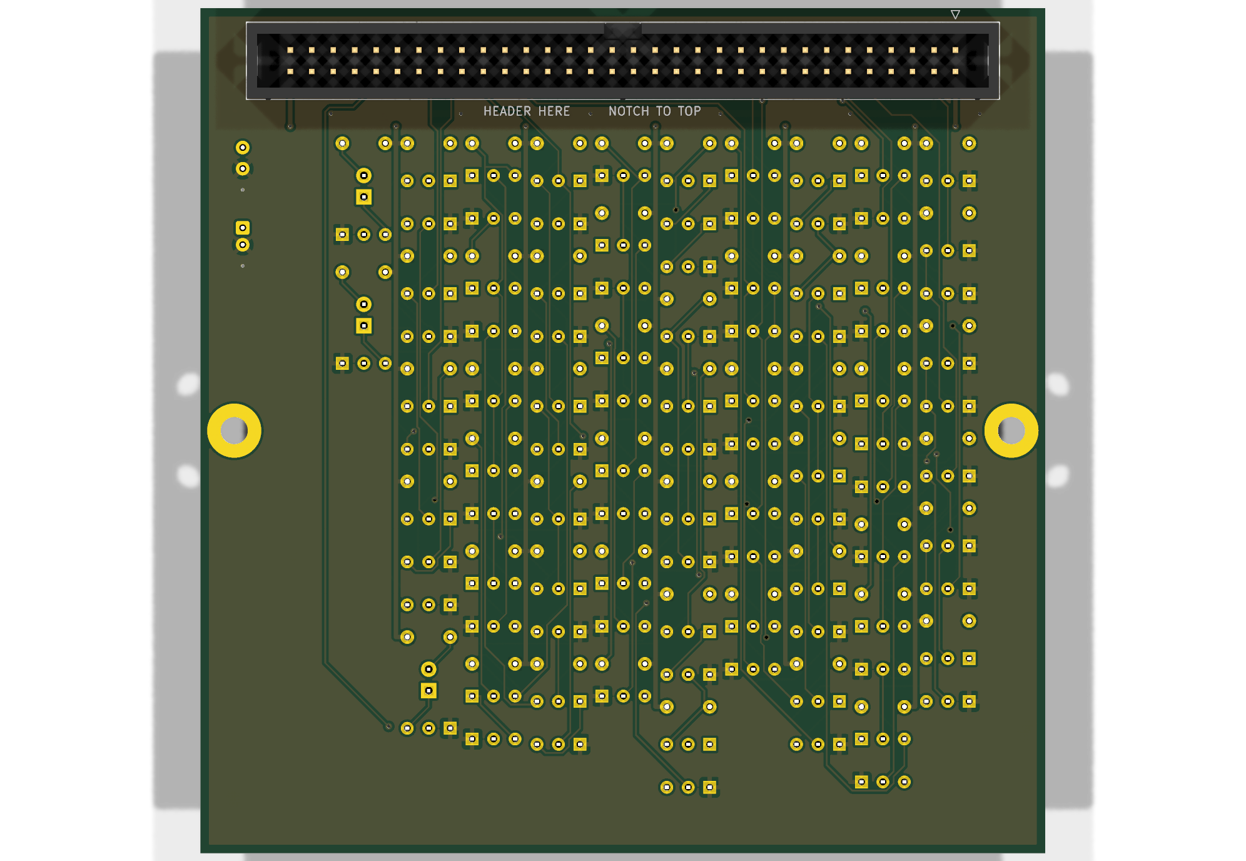
cards/reg2/fab/reg2-bottom.png
