nikolafilip/nibble/cards/reg3/fab/reg3-bottom.png

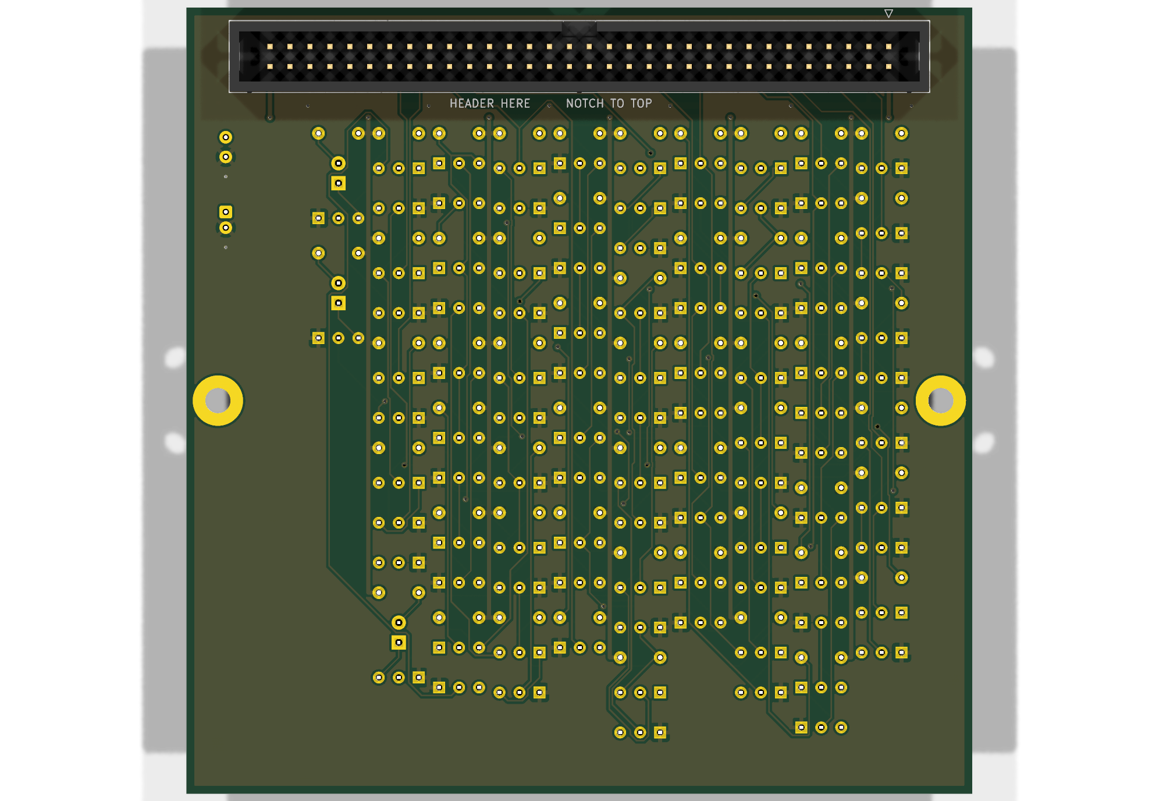
cards/reg3/fab/reg3-bottom.png
