nikolafilip/nibble/cards/reg1/fab/reg1-bom.csv

Reference | Value | Footprint | QUANTITY
C1 | 100n | Capacitor_THT:C_Disc_D5.0mm_W2.5mm_P2.50mm | 1
C2 | 10u | Capacitor_THT:CP_Radial_D5.0mm_P2.00mm | 1
D1-D3 | LED | LED_THT:LED_D3.0mm | 3
J1 | BUS | Connector_IDC:IDC-Header_2x32_P2.54mm_Vertical | 1
Q1-Q99 | 2N7000 | Package_TO_SOT_THT:TO-92_Inline_Wide | 99
R1,R4-R17,R19-R32,R34-R51 | 47k | Resistor_THT:R_Axial_DIN0207_L6.3mm_D2.5mm_P5.08mm_Vertical | 47
R2,R3 | 10k | Resistor_THT:R_Axial_DIN0207_L6.3mm_D2.5mm_P5.08mm_Vertical | 2
R18,R33 | 22k | Resistor_THT:R_Axial_DIN0207_L6.3mm_D2.5mm_P5.08mm_Vertical | 2
R52-R54 | 1k | Resistor_THT:R_Axial_DIN0207_L6.3mm_D2.5mm_P5.08mm_Vertical | 3
