nikolafilip/nibble/sim/results/gate25_nop.md

# Machine gate: boards aluc,hubc,regc,seq,ctrc,memc,progc,pnl,clkc
Generated 2026-09-26 04:11 by sim/gate.py. Corners: LO, HI; MIX seeds [1].

| program | corner | result | time |
|---|---|---|---|
| nop.asm | LO | pass: 33 ticks, 0 mismatches | 798 s |
| nop.asm | HI | pass: 33 ticks, 0 mismatches | 2303 s |
