nikolafilip/nibble/sim/results/gate25_vdd425.md

# Machine gate: boards aluc,hubc,regc,seq,ctrc,memc,progc,pnl,clkc
Generated 2026-09-27 21:29 by sim/gate.py. Corners: HI; MIX seeds [1].

| program | corner | result | time |
|---|---|---|---|
| fib.asm | HI | pass: 127 ticks, 0 mismatches | 4416 s |
| logic.asm | HI | pass: 986 ticks, 0 mismatches | 20611 s |
| call.asm | HI | pass: 84 ticks, 0 mismatches | 3840 s |
