nikolafilip/nibble/sim/results/gate26_mix34.md

# Machine gate: boards aluc,hubc,regc,seq,ctrc,memc,progc,pnl,clkc
Generated 2026-10-04 08:27 by sim/gate.py. Corners: MIX; MIX seeds [3, 4].

| program | corner | result | time |
|---|---|---|---|
| fib.asm | MIX3 | pass: 127 ticks, 0 mismatches | 3743 s |
| fib.asm | MIX4 | pass: 127 ticks, 0 mismatches | 3687 s |
| alu.asm | MIX3 | pass: 75 ticks, 0 mismatches | 2928 s |
| alu.asm | MIX4 | pass: 75 ticks, 0 mismatches | 2312 s |
| gcd.asm | MIX3 | pass: 160 ticks, 0 mismatches | 9620 s |
| gcd.asm | MIX4 | pass: 160 ticks, 0 mismatches | 9827 s |
| list.asm | MIX3 | pass: 210 ticks, 0 mismatches | 7553 s |
| list.asm | MIX4 | pass: 210 ticks, 0 mismatches | 6422 s |
| logic.asm | MIX3 | pass: 986 ticks, 0 mismatches | 29057 s |
| logic.asm | MIX4 | pass: 986 ticks, 0 mismatches | 28980 s |
| call.asm | MIX3 | pass: 84 ticks, 0 mismatches | 2470 s |
| call.asm | MIX4 | pass: 84 ticks, 0 mismatches | 2333 s |
