nikolafilip/nibble/sim/results/gate26_vdd45.md

# Machine gate: boards aluc,hubc,regc,seq,ctrc,memc,progc,pnl,clkc
Generated 2026-10-03 11:44 by sim/gate.py. Corners: TYP, HI; MIX seeds [1].

| program | corner | result | time |
|---|---|---|---|
| fib.asm | TYP | pass: 127 ticks, 0 mismatches | 2690 s |
| fib.asm | HI | pass: 127 ticks, 0 mismatches | 3233 s |
| alu.asm | TYP | pass: 75 ticks, 0 mismatches | 2114 s |
| alu.asm | HI | pass: 75 ticks, 0 mismatches | 2703 s |
| gcd.asm | TYP | pass: 160 ticks, 0 mismatches | 5542 s |
| gcd.asm | HI | pass: 160 ticks, 0 mismatches | 6168 s |
| list.asm | TYP | pass: 210 ticks, 0 mismatches | 4962 s |
| list.asm | HI | pass: 210 ticks, 0 mismatches | 5577 s |
| logic.asm | TYP | pass: 986 ticks, 0 mismatches | 19907 s |
| logic.asm | HI | pass: 986 ticks, 0 mismatches | 21240 s |
| call.asm | TYP | pass: 84 ticks, 0 mismatches | 2095 s |
| call.asm | HI | pass: 84 ticks, 0 mismatches | 2716 s |
