nikolafilip/nibble/sim/results/gate26_500pF_HI.md

# Machine gate: boards aluc,hubc,regc,seq,ctrc,memc,progc,pnl,clkc
Generated 2026-10-03 00:37 by sim/gate.py. Corners: HI; MIX seeds [1].

| program | corner | result | time |
|---|---|---|---|
| fib.asm | HI | pass: 127 ticks, 0 mismatches | 3117 s |
| alu.asm | HI | pass: 75 ticks, 0 mismatches | 2531 s |
| gcd.asm | HI | pass: 160 ticks, 0 mismatches | 6046 s |
| list.asm | HI | pass: 210 ticks, 0 mismatches | 5406 s |
| logic.asm | HI | pass: 986 ticks, 0 mismatches | 19912 s |
| call.asm | HI | pass: 84 ticks, 0 mismatches | 2510 s |
