nikolafilip/nibble/sim/results/gate26_corners.md

# Machine gate: boards aluc,hubc,regc,seq,ctrc,memc,progc,pnl,clkc
Generated 2026-10-02 16:22 by sim/gate.py. Corners: LO, HI, MIX; MIX seeds [1, 2].

| program | corner | result | time |
|---|---|---|---|
| fib.asm | LO | pass: 127 ticks, 0 mismatches | 3217 s |
| fib.asm | HI | pass: 127 ticks, 0 mismatches | 3753 s |
| fib.asm | MIX1 | pass: 127 ticks, 0 mismatches | 3806 s |
| fib.asm | MIX2 | pass: 127 ticks, 0 mismatches | 4500 s |
| alu.asm | LO | pass: 75 ticks, 0 mismatches | 1848 s |
| alu.asm | HI | pass: 75 ticks, 0 mismatches | 2562 s |
| alu.asm | MIX1 | pass: 75 ticks, 0 mismatches | 2765 s |
| alu.asm | MIX2 | pass: 75 ticks, 0 mismatches | 2461 s |
| gcd.asm | LO | pass: 160 ticks, 0 mismatches | 5067 s |
| gcd.asm | HI | pass: 160 ticks, 0 mismatches | 6035 s |
| gcd.asm | MIX1 | pass: 160 ticks, 0 mismatches | 8267 s |
| gcd.asm | MIX2 | pass: 160 ticks, 0 mismatches | 8696 s |
| list.asm | LO | pass: 210 ticks, 0 mismatches | 4944 s |
| list.asm | HI | pass: 210 ticks, 0 mismatches | 5488 s |
| list.asm | MIX1 | pass: 210 ticks, 0 mismatches | 6811 s |
| list.asm | MIX2 | pass: 210 ticks, 0 mismatches | 6533 s |
| logic.asm | LO | pass: 986 ticks, 0 mismatches | 21950 s |
| logic.asm | HI | pass: 986 ticks, 0 mismatches | 21035 s |
| logic.asm | MIX1 | pass: 986 ticks, 0 mismatches | 30968 s |
| logic.asm | MIX2 | pass: 986 ticks, 0 mismatches | 30673 s |
| call.asm | LO | pass: 84 ticks, 0 mismatches | 2047 s |
| call.asm | HI | pass: 84 ticks, 0 mismatches | 2476 s |
| call.asm | MIX1 | pass: 84 ticks, 0 mismatches | 3311 s |
| call.asm | MIX2 | pass: 84 ticks, 0 mismatches | 2915 s |
