nikolafilip/nibble/sim/results/gate26_TYP.md

# Machine gate: boards aluc,hubc,regc,seq,ctrc,memc,progc,pnl,clkc
Generated 2026-10-01 13:24 by sim/gate.py. Corners: TYP; MIX seeds [1].

| program | corner | result | time |
|---|---|---|---|
| alu.asm | TYP | pass: 75 ticks, 0 mismatches | 1992 s |
| calc.asm | TYP | pass: 616 ticks, 0 mismatches | 21444 s |
| call.asm | TYP | pass: 84 ticks, 0 mismatches | 1956 s |
| count.asm | TYP | pass: 444 ticks, 0 mismatches | 8957 s |
| fib.asm | TYP | pass: 127 ticks, 0 mismatches | 2576 s |
| gcd.asm | TYP | pass: 160 ticks, 0 mismatches | 5472 s |
| lfsr.asm | TYP | pass: 1497 ticks, 0 mismatches | 33191 s |
| list.asm | TYP | pass: 210 ticks, 0 mismatches | 4738 s |
| logic.asm | TYP | pass: 986 ticks, 0 mismatches | 19878 s |
| loops.asm | TYP | pass: 125 ticks, 0 mismatches | 2756 s |
| mul.asm | TYP | pass: 314 ticks, 0 mismatches | 7212 s |
| nop.asm | TYP | pass: 33 ticks, 0 mismatches | 1004 s |
| sort.asm | TYP | pass: 974 ticks, 0 mismatches | 38706 s |
