nikolafilip/nibble/sim/results/gate26_smoke.md

# Machine gate: boards aluc,hubc,regc,seq,ctrc,memc,progc,pnl,clkc, first 12 ticks of every program (smoke)
Generated 2026-09-30 11:19 by sim/gate.py. Corners: TYP; MIX seeds [1].

| program | corner | result | time |
|---|---|---|---|
| alu.asm | TYP | pass: 12 ticks, 0 mismatches | 1983 s |
| calc.asm | TYP | pass: 12 ticks, 0 mismatches | 3013 s |
| call.asm | TYP | pass: 12 ticks, 0 mismatches | 1896 s |
| count.asm | TYP | pass: 12 ticks, 0 mismatches | 1917 s |
| fib.asm | TYP | pass: 12 ticks, 0 mismatches | 1760 s |
| gcd.asm | TYP | pass: 12 ticks, 0 mismatches | 2923 s |
| lfsr.asm | TYP | pass: 12 ticks, 0 mismatches | 2010 s |
| list.asm | TYP | pass: 12 ticks, 0 mismatches | 2088 s |
| logic.asm | TYP | pass: 12 ticks, 0 mismatches | 1903 s |
| loops.asm | TYP | pass: 12 ticks, 0 mismatches | 1913 s |
| mul.asm | TYP | pass: 12 ticks, 0 mismatches | 1968 s |
| nop.asm | TYP | pass: 12 ticks, 0 mismatches | 969 s |
| sort.asm | TYP | pass: 12 ticks, 0 mismatches | 3159 s |
