nikolafilip/nibble/sim/results/gate25_500pF_HI.md

# Machine gate: boards aluc,hubc,regc,seq,ctrc,memc,progc,pnl,clkc
Generated 2026-09-26 12:35 by sim/gate.py. Corners: HI; MIX seeds [1].

| program | corner | result | time |
|---|---|---|---|
| fib.asm | HI | pass: 127 ticks, 0 mismatches | 3977 s |
| alu.asm | HI | pass: 75 ticks, 0 mismatches | 3625 s |
| gcd.asm | HI | pass: 160 ticks, 0 mismatches | 8043 s |
| list.asm | HI | pass: 210 ticks, 0 mismatches | 6251 s |
| logic.asm | HI | pass: 986 ticks, 0 mismatches | 19967 s |
| call.asm | HI | pass: 84 ticks, 0 mismatches | 3373 s |
