nikolafilip/nibble/sim/results/gate25_cross.md

# Machine gate: boards aluc,hubc,regc,seq,ctrc,memc,progc,pnl,clkc
Generated 2026-09-27 13:16 by sim/gate.py. Corners: TYP, HI; MIX seeds [1].

| program | corner | result | time |
|---|---|---|---|
| fib.asm | TYP | pass: 127 ticks, 0 mismatches | 3184 s |
| fib.asm | HI | pass: 127 ticks, 0 mismatches | 4126 s |
| alu.asm | TYP | pass: 75 ticks, 0 mismatches | 2640 s |
| alu.asm | HI | pass: 75 ticks, 0 mismatches | 3653 s |
| gcd.asm | TYP | pass: 160 ticks, 0 mismatches | 6649 s |
| gcd.asm | HI | pass: 160 ticks, 0 mismatches | 8194 s |
| list.asm | TYP | pass: 210 ticks, 0 mismatches | 5221 s |
| list.asm | HI | pass: 210 ticks, 0 mismatches | 6289 s |
| logic.asm | TYP | pass: 986 ticks, 0 mismatches | 20551 s |
| logic.asm | HI | pass: 986 ticks, 0 mismatches | 21875 s |
| call.asm | TYP | pass: 84 ticks, 0 mismatches | 2548 s |
| call.asm | HI | pass: 84 ticks, 0 mismatches | 3560 s |
