nikolafilip/nibble/sim/results/gate25_mix34.md

# Machine gate: boards aluc,hubc,regc,seq,ctrc,memc,progc,pnl,clkc
Generated 2026-09-28 14:03 by sim/gate.py. Corners: MIX; MIX seeds [3, 4].

| program | corner | result | time |
|---|---|---|---|
| fib.asm | MIX3 | pass: 127 ticks, 0 mismatches | 3501 s |
| fib.asm | MIX4 | pass: 127 ticks, 0 mismatches | 4750 s |
| alu.asm | MIX3 | pass: 75 ticks, 0 mismatches | 3814 s |
| alu.asm | MIX4 | pass: 75 ticks, 0 mismatches | 2662 s |
| gcd.asm | MIX3 | pass: 160 ticks, 0 mismatches | 11822 s |
| gcd.asm | MIX4 | pass: 160 ticks, 0 mismatches | 12008 s |
| list.asm | MIX3 | pass: 210 ticks, 0 mismatches | 7971 s |
| list.asm | MIX4 | pass: 210 ticks, 0 mismatches | 6431 s |
| logic.asm | MIX3 | pass: 986 ticks, 0 mismatches | 29270 s |
| logic.asm | MIX4 | pass: 986 ticks, 0 mismatches | 30026 s |
| call.asm | MIX3 | pass: 84 ticks, 0 mismatches | 2908 s |
| call.asm | MIX4 | pass: 84 ticks, 0 mismatches | 2471 s |
