nikolafilip/nibble/sim/results/gate25_vdd45.md

# Machine gate: boards aluc,hubc,regc,seq,ctrc,memc,progc,pnl,clkc
Generated 2026-09-27 00:57 by sim/gate.py. Corners: HI, TYP; MIX seeds [1].

| program | corner | result | time |
|---|---|---|---|
| fib.asm | HI | pass: 127 ticks, 0 mismatches | 4233 s |
| fib.asm | TYP | pass: 127 ticks, 0 mismatches | 3202 s |
| alu.asm | HI | pass: 75 ticks, 0 mismatches | 3923 s |
| alu.asm | TYP | pass: 75 ticks, 0 mismatches | 2737 s |
| gcd.asm | HI | pass: 160 ticks, 0 mismatches | 8331 s |
| gcd.asm | TYP | pass: 160 ticks, 0 mismatches | 6613 s |
| list.asm | HI | pass: 210 ticks, 0 mismatches | 6539 s |
| list.asm | TYP | pass: 210 ticks, 0 mismatches | 5260 s |
| logic.asm | HI | pass: 986 ticks, 0 mismatches | 21672 s |
| logic.asm | TYP | pass: 986 ticks, 0 mismatches | 19573 s |
| call.asm | HI | pass: 84 ticks, 0 mismatches | 3786 s |
| call.asm | TYP | pass: 84 ticks, 0 mismatches | 2564 s |
