nikolafilip/nibble/sim/results/gate25_corners.md

# Machine gate: boards aluc,hubc,regc,seq,ctrc,memc,progc,pnl,clkc
Generated 2026-09-26 03:31 by sim/gate.py. Corners: LO, HI, MIX; MIX seeds [1, 2].

| program | corner | result | time |
|---|---|---|---|
| fib.asm | LO | pass: 127 ticks, 0 mismatches | 2515 s |
| fib.asm | HI | pass: 127 ticks, 0 mismatches | 4031 s |
| fib.asm | MIX1 | pass: 127 ticks, 0 mismatches | 3727 s |
| fib.asm | MIX2 | pass: 127 ticks, 0 mismatches | 5567 s |
| alu.asm | LO | pass: 75 ticks, 0 mismatches | 1778 s |
| alu.asm | HI | pass: 75 ticks, 0 mismatches | 3611 s |
| alu.asm | MIX1 | pass: 75 ticks, 0 mismatches | 3694 s |
| alu.asm | MIX2 | pass: 75 ticks, 0 mismatches | 2574 s |
| gcd.asm | LO | pass: 160 ticks, 0 mismatches | 5064 s |
| gcd.asm | HI | pass: 160 ticks, 0 mismatches | 7986 s |
| gcd.asm | MIX1 | pass: 160 ticks, 0 mismatches | 8152 s |
| gcd.asm | MIX2 | pass: 160 ticks, 0 mismatches | 10077 s |
| list.asm | LO | pass: 210 ticks, 0 mismatches | 4663 s |
| list.asm | HI | pass: 210 ticks, 0 mismatches | 6360 s |
| list.asm | MIX1 | pass: 210 ticks, 0 mismatches | 7650 s |
| list.asm | MIX2 | pass: 210 ticks, 0 mismatches | 6418 s |
| logic.asm | LO | pass: 986 ticks, 0 mismatches | 20738 s |
| logic.asm | HI | pass: 986 ticks, 0 mismatches | 21488 s |
| logic.asm | MIX1 | pass: 986 ticks, 0 mismatches | 31538 s |
| logic.asm | MIX2 | pass: 986 ticks, 0 mismatches | 31658 s |
| call.asm | LO | pass: 84 ticks, 0 mismatches | 1850 s |
| call.asm | HI | pass: 84 ticks, 0 mismatches | 3595 s |
| call.asm | MIX1 | pass: 84 ticks, 0 mismatches | 5162 s |
| call.asm | MIX2 | pass: 84 ticks, 0 mismatches | 5030 s |
