nikolafilip/nibble/sim/results/gate25_smoke_t12.md

# Machine gate: boards aluc,hubc,regc,seq,ctrc,memc,progc,pnl,clkc, first 12 ticks of every program (smoke)
Generated 2026-09-23 19:19 by sim/gate.py. Corners: TYP; MIX seeds [1].

| program | corner | result | time |
|---|---|---|---|
| alu.asm | TYP | pass: 12 ticks, 0 mismatches | 2613 s |
| calc.asm | TYP | pass: 12 ticks, 0 mismatches | 4101 s |
| call.asm | TYP | pass: 12 ticks, 0 mismatches | 2461 s |
| count.asm | TYP | pass: 12 ticks, 0 mismatches | 2510 s |
| fib.asm | TYP | pass: 12 ticks, 0 mismatches | 2356 s |
| gcd.asm | TYP | pass: 12 ticks, 0 mismatches | 4005 s |
| lfsr.asm | TYP | pass: 12 ticks, 0 mismatches | 2713 s |
| list.asm | TYP | pass: 12 ticks, 0 mismatches | 2683 s |
| logic.asm | TYP | pass: 12 ticks, 0 mismatches | 2513 s |
| loops.asm | TYP | pass: 12 ticks, 0 mismatches | 2463 s |
| mul.asm | TYP | pass: 12 ticks, 0 mismatches | 2658 s |
| nop.asm | TYP | pass: 12 ticks, 0 mismatches | 1527 s |
| sort.asm | TYP | pass: 12 ticks, 0 mismatches | 4321 s |
