nikolafilip/nibble/sim/results/gate25_TYP.md

# Machine gate: boards aluc,hubc,regc,seq,ctrc,memc,progc,pnl,clkc
Generated 2026-09-24 22:59 by sim/gate.py. Corners: TYP; MIX seeds [1].

| program | corner | result | time |
|---|---|---|---|
| alu.asm | TYP | pass: 75 ticks, 0 mismatches | 2641 s |
| calc.asm | TYP | pass: 616 ticks, 0 mismatches | 22116 s |
| call.asm | TYP | pass: 84 ticks, 0 mismatches | 2526 s |
| count.asm | TYP | pass: 444 ticks, 0 mismatches | 9362 s |
| fib.asm | TYP | pass: 127 ticks, 0 mismatches | 3123 s |
| gcd.asm | TYP | pass: 160 ticks, 0 mismatches | 6561 s |
| lfsr.asm | TYP | pass: 1497 ticks, 0 mismatches | 34033 s |
| list.asm | TYP | pass: 210 ticks, 0 mismatches | 5245 s |
| logic.asm | TYP | pass: 986 ticks, 0 mismatches | 20020 s |
| loops.asm | TYP | pass: 125 ticks, 0 mismatches | 3291 s |
| mul.asm | TYP | pass: 314 ticks, 0 mismatches | 7807 s |
| nop.asm | TYP | pass: 33 ticks, 0 mismatches | 1561 s |
| sort.asm | TYP | pass: 974 ticks, 0 mismatches | 41866 s |
