nikolafilip/nibble/boards/01-alu/sim_results/tran_alu_demo.png

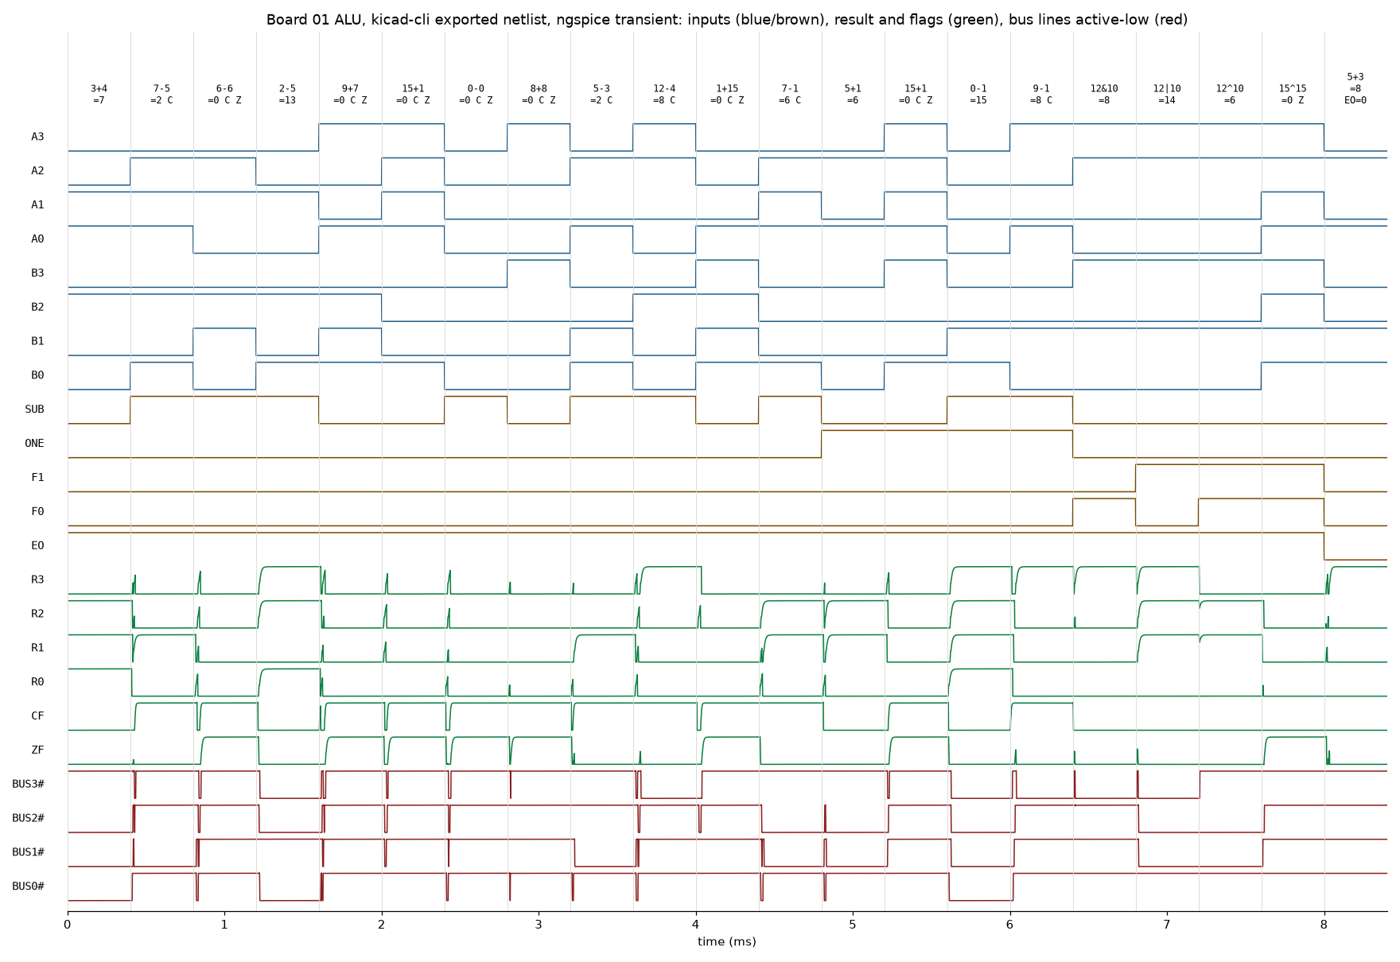
boards/01-alu/sim_results/tran_alu_demo.png
