nikolafilip/nibble/boards/01-alu/sim_results/tran_alu_zoom.png

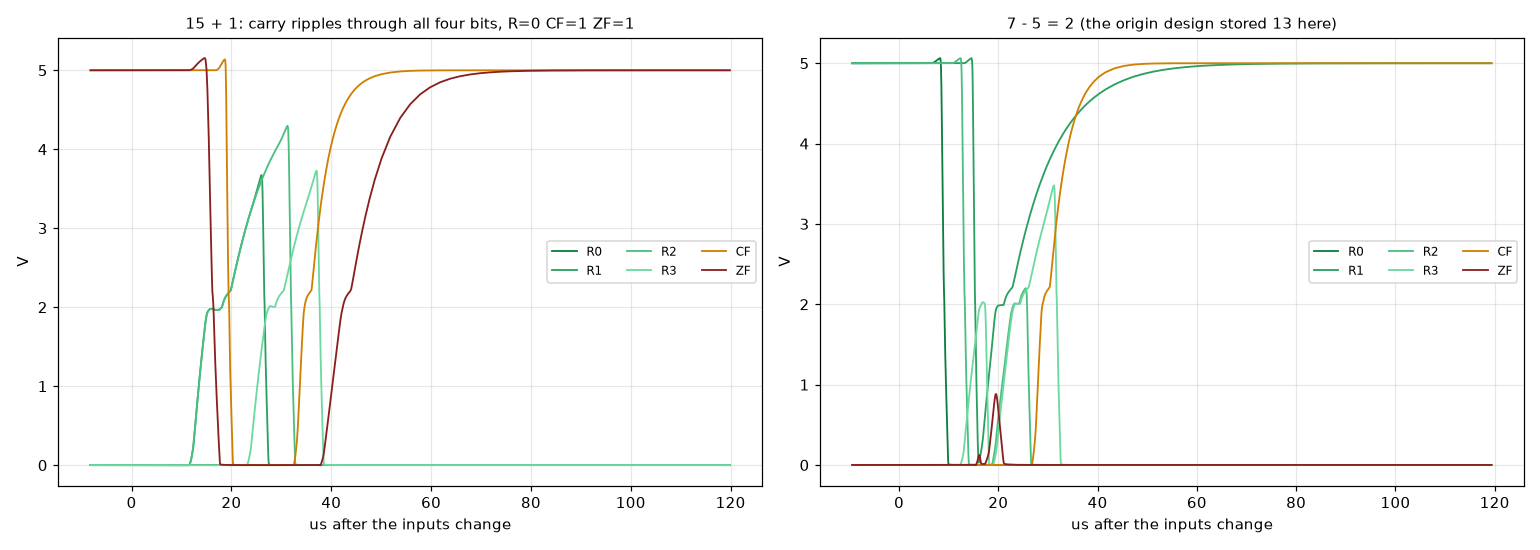
boards/01-alu/sim_results/tran_alu_zoom.png
