nikolafilip/nibble/experiments/muldiv/sim_results/tran_div_7by2.png

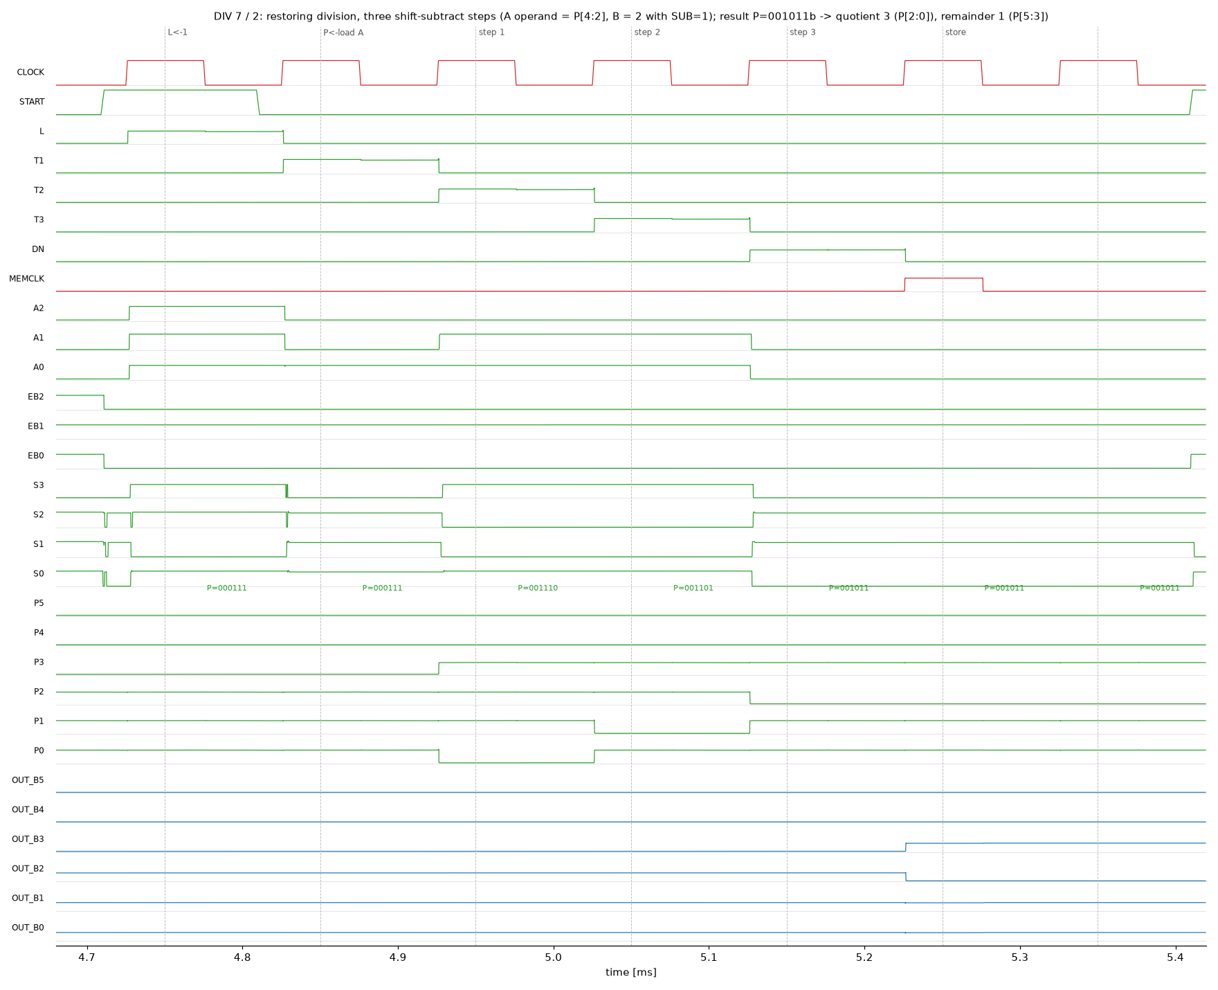
experiments/muldiv/sim_results/tran_div_7by2.png
