nikolafilip/nibble/experiments/muldiv/sim_results/tran_mul_7x7.png

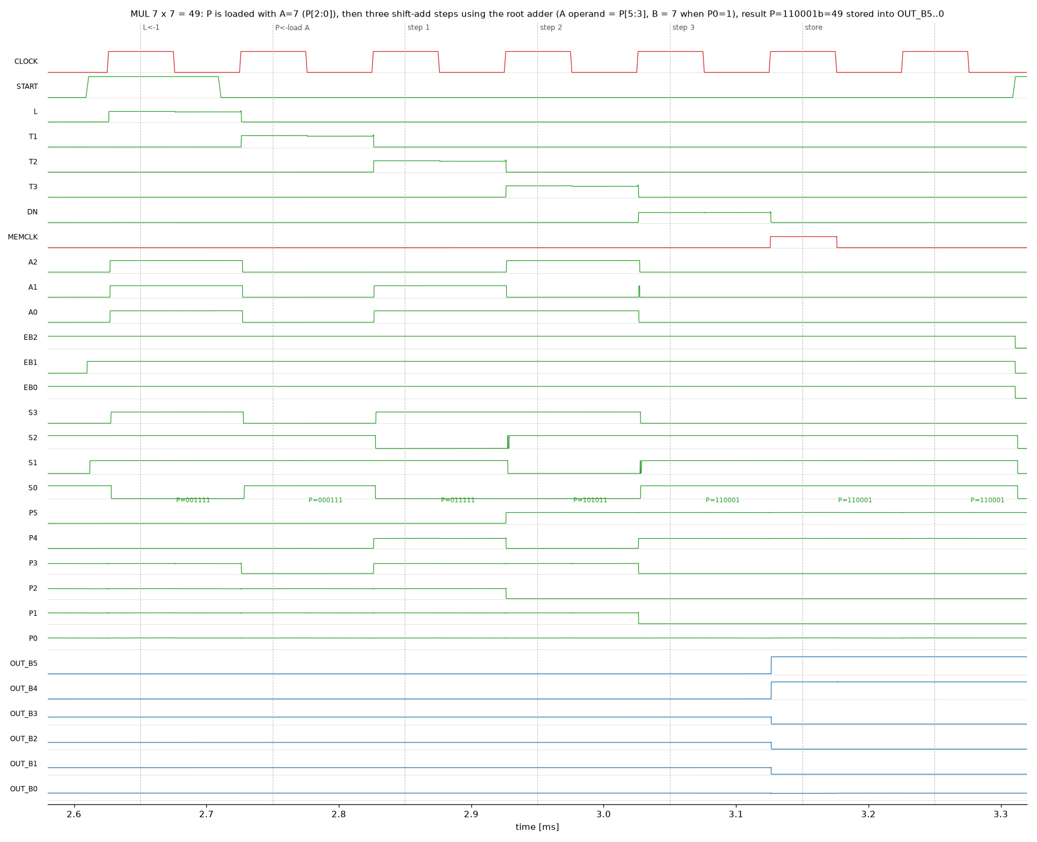
experiments/muldiv/sim_results/tran_mul_7x7.png
