nikolafilip/nibble/experiments/muldiv/sim_results/tran_sub_fix.png

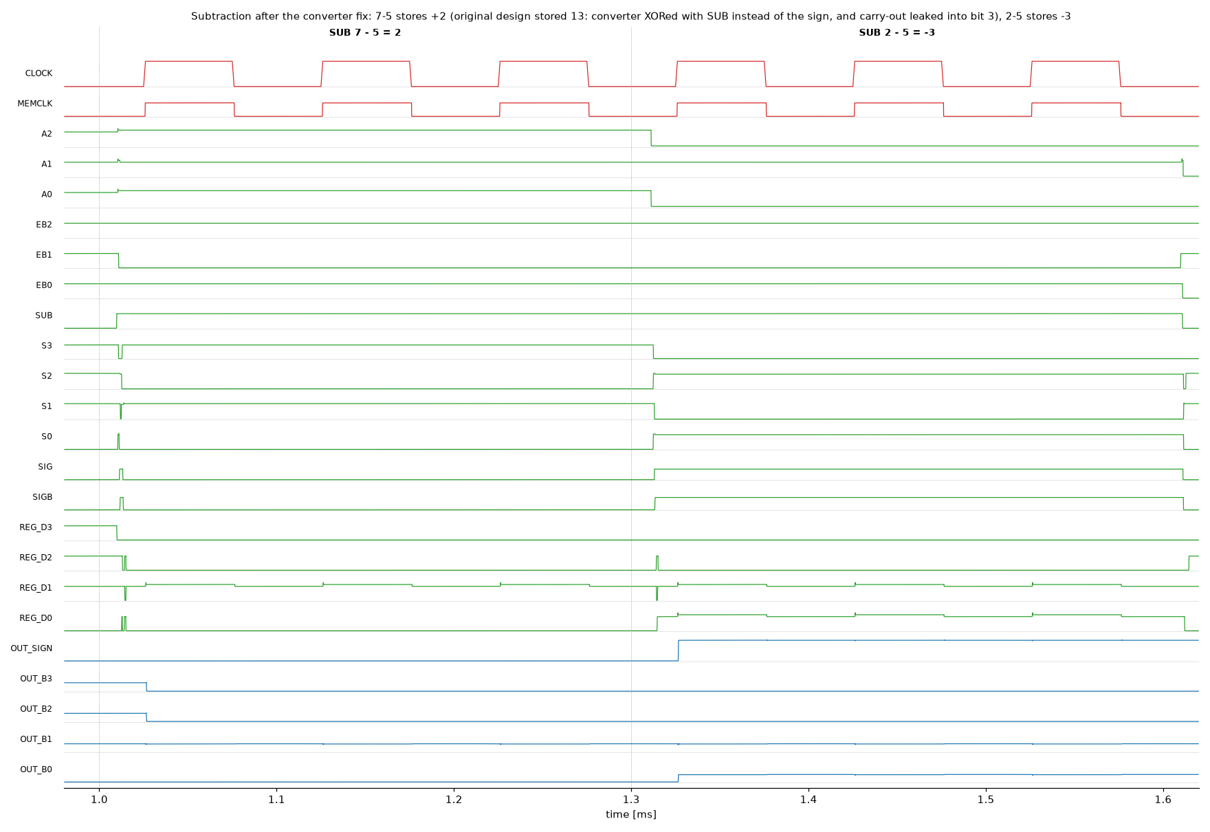
experiments/muldiv/sim_results/tran_sub_fix.png
