nikolafilip/nibble/experiments/muldiv/sim_results/kicad_exported_netlist.cir

.title KiCad schematic
.include "/Users/nikolafilip/Desktop/2N3904.lib"
.ic v(L)=0 v(T1)=0 v(T2)=0 v(T3)=0 v(DN)=0 v(P0)=0 v(P1)=0 v(P2)=0 v(P3)=0 v(P4)=0 v(P5)=0 v(OUT_B4)=0 v(OUT_B5)=0 v(OUT_SIGN)=0 v(OUT_B3)=0 v(OUT_B2)=0 v(OUT_B1)=0 v(OUT_B0)=0
.tran 1u 0.0093
R788 +5V Net-_Q300-C_ 4.7k
Q300 Net-_Q300-C_ Net-_Q300-B_ Net-_Q300-E_ 2N3904
Q295 Net-_Q295-C_ Net-_Q295-B_ Net-_Q295-E_ 2N3904
R766 Net-_Q290-C_ Net-_Q295-B_ 10k
R775 +5V Net-_Q295-C_ 4.7k
Q301 Net-_Q300-E_ Net-_Q301-B_ GND 2N3904
R797 GND Net-_Q306-B_ 22k
Q306 Net-_Q306-C_ Net-_Q306-B_ Net-_Q306-E_ 2N3904
Q307 Net-_Q306-E_ Net-_Q307-B_ GND 2N3904
R795 GND Net-_Q307-B_ 22k
R793 Net-_Q302-C_ Net-_Q307-B_ 10k
R799 +5V Net-_Q306-C_ 4.7k
R792 OUT_B0 Net-_Q306-B_ 10k
R789 +5V Net-_Q302-C_ 4.7k
Q303 Net-_Q302-E_ Net-_Q303-B_ GND 2N3904
Q302 Net-_Q302-C_ Net-_Q302-B_ Net-_Q302-E_ 2N3904
R794 GND Net-_Q305-B_ 22k
Q305 Net-_Q304-E_ Net-_Q305-B_ GND 2N3904
R791 Net-_Q306-C_ Net-_Q305-B_ 10k
R796 GND Net-_Q304-B_ 22k
R790 Net-_Q300-C_ Net-_Q304-B_ 10k
Q304 OUT_B0 Net-_Q304-B_ Net-_Q304-E_ 2N3904
R798 +5V OUT_B0 2.2k
R740 OUT_B1 Net-_Q286-B_ 10k
Q286 Net-_Q286-C_ Net-_Q286-B_ Net-_Q286-E_ 2N3904
R745 GND Net-_Q286-B_ 22k
R741 Net-_Q282-C_ Net-_Q287-B_ 10k
Q287 Net-_Q286-E_ Net-_Q287-B_ GND 2N3904
R743 GND Net-_Q287-B_ 22k
R733 GND Net-_Q283-B_ 22k
Q283 Net-_Q282-E_ Net-_Q283-B_ GND 2N3904
R725 Net-_Q275-C_ Net-_Q279-B_ 10k
R730 Net-_Q274-C_ Net-_Q282-B_ 10k
R731 Net-_Q279-C_ Net-_Q283-B_ 10k
R727 +5V Net-_Q279-C_ 4.7k
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
R895 +5V /F_OUT7 4.7k
Q339 Net-_Q338-E_ Net-_Q339-B_ GND 2N3904
R874 GND Net-_Q339-B_ 22k
R892 GND Net-_Q347-B_ 22k
Q340 Net-_Q340-C_ Net-_Q340-B_ Net-_Q340-E_ 2N3904
R879 GND Net-_Q340-B_ 22k
R884 +5V Net-_Q340-C_ 4.7k
R887 Net-_Q336-C_ Net-_Q346-B_ 10k
R882 +5V Net-_Q336-C_ 4.7k
Q335 Net-_Q334-E_ Net-_Q335-B_ GND 2N3904
R894 +5V /F_OUT6 4.7k
R890 GND Net-_Q346-B_ 22k
Q346 /F_OUT6 Net-_Q346-B_ GND 2N3904
R1037 GND Net-_Q394-B_ 22k
R1023 OUT_B0 Net-_Q395-B_ 10k
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
