nikolafilip/nibble/cards/panela/panela.kicad_pcb

## KiCad design cards/panela/panela.kicad_pcb (2026-10-01)

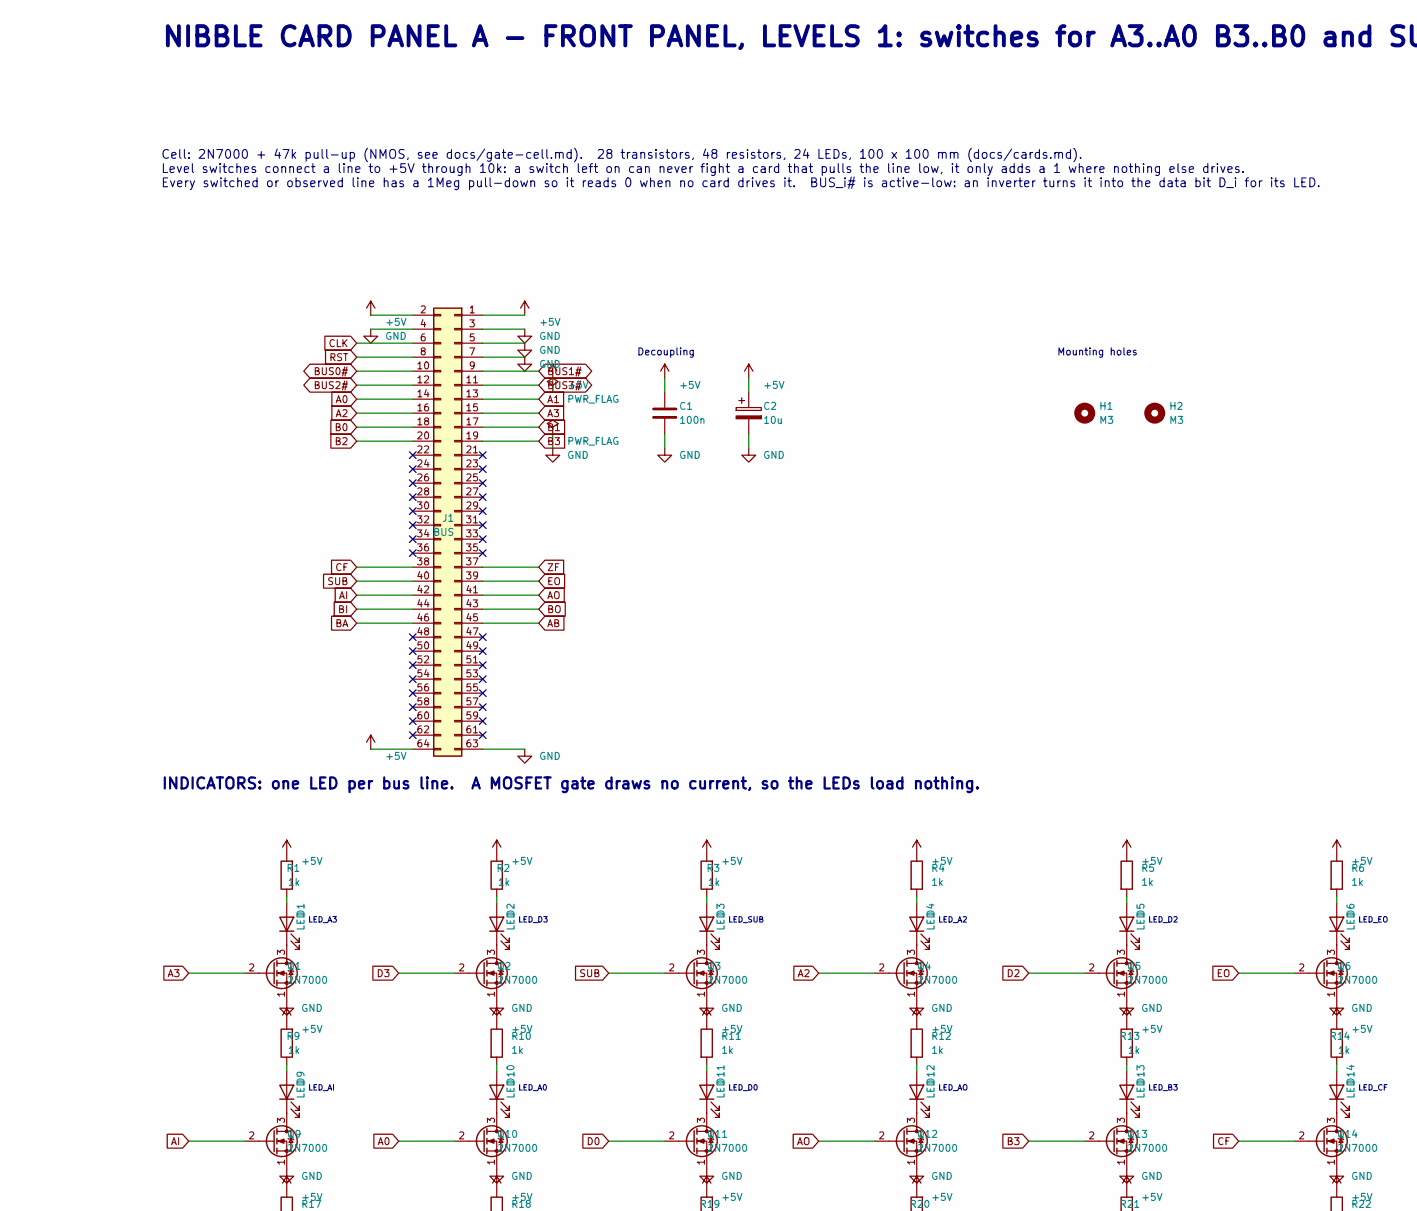
[picture p64: schematic panela.kicad_sch, part in row 1, column 1]

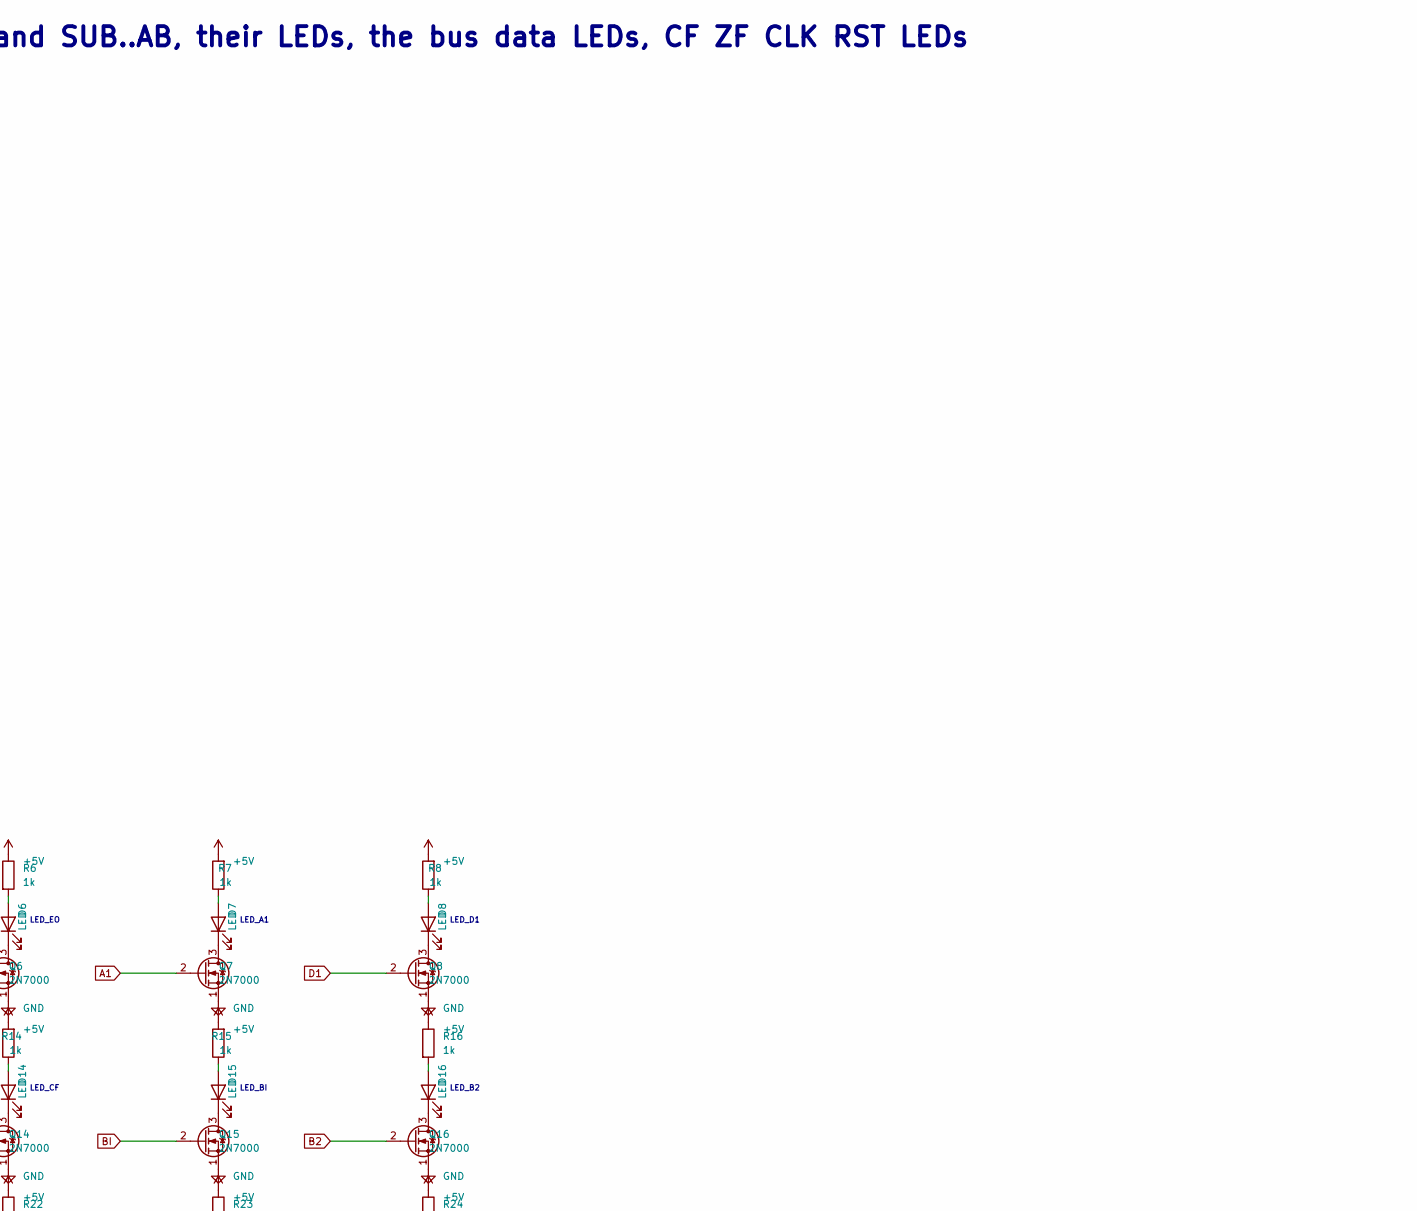
[picture p65: schematic panela.kicad_sch, part in row 1, column 2]

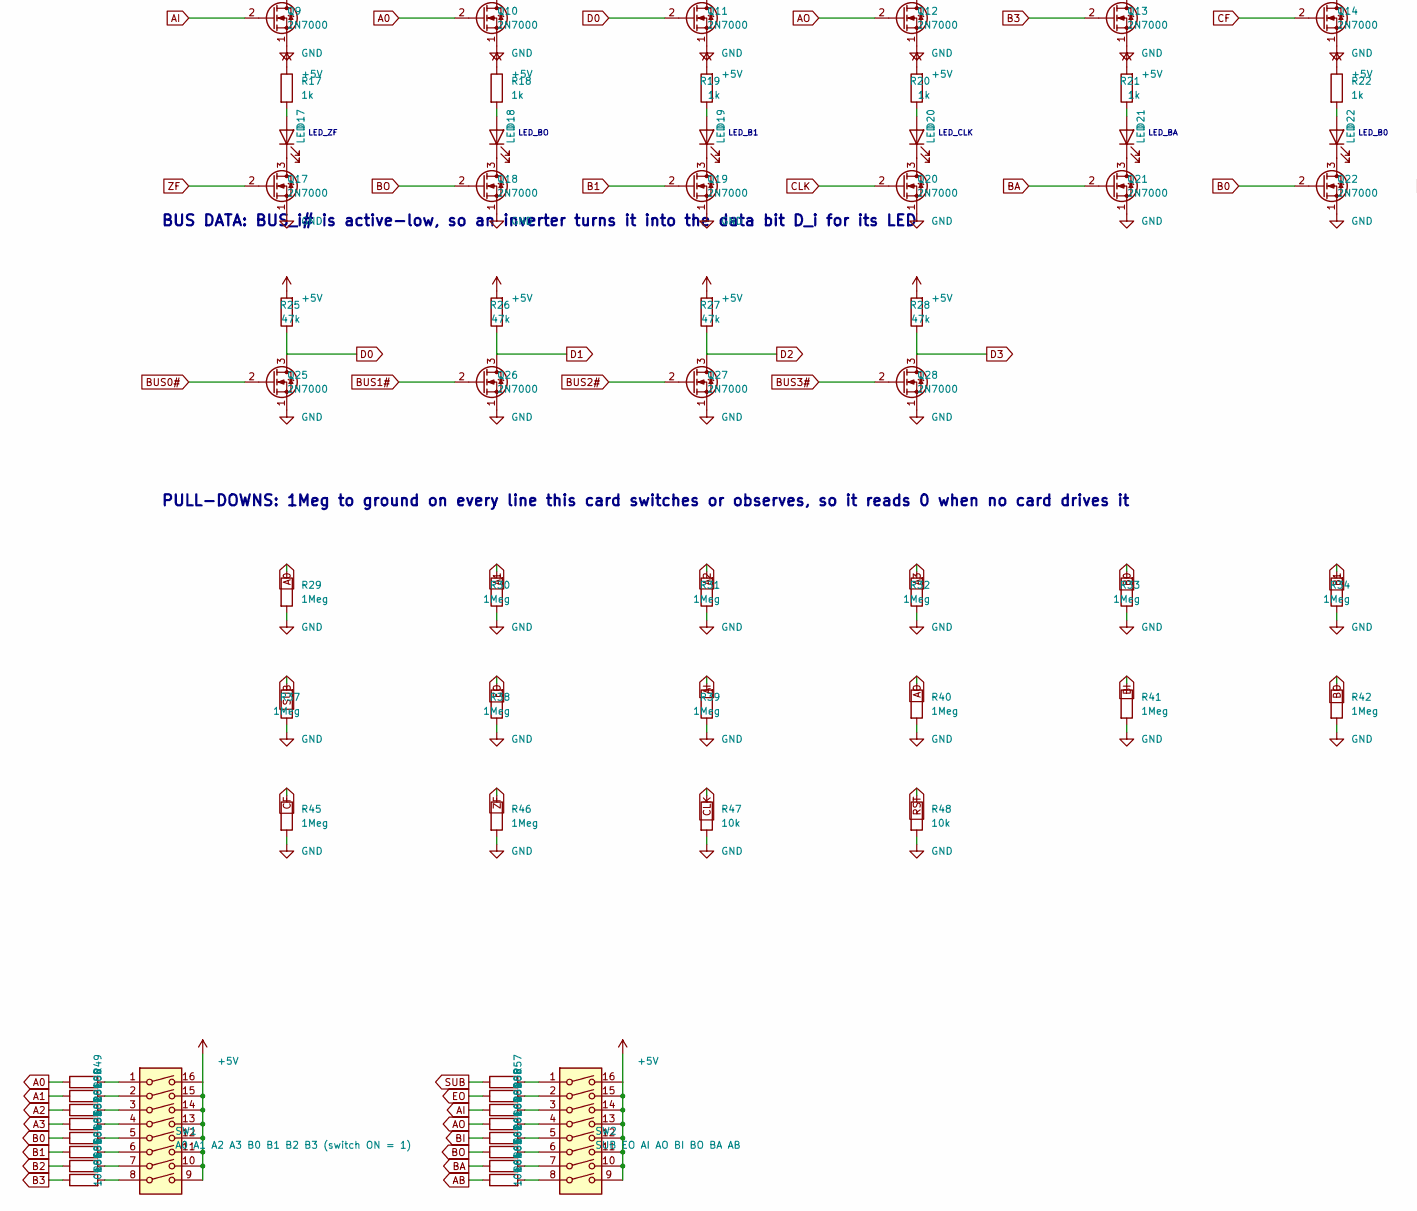
[picture p66: schematic panela.kicad_sch, part in row 2, column 1]

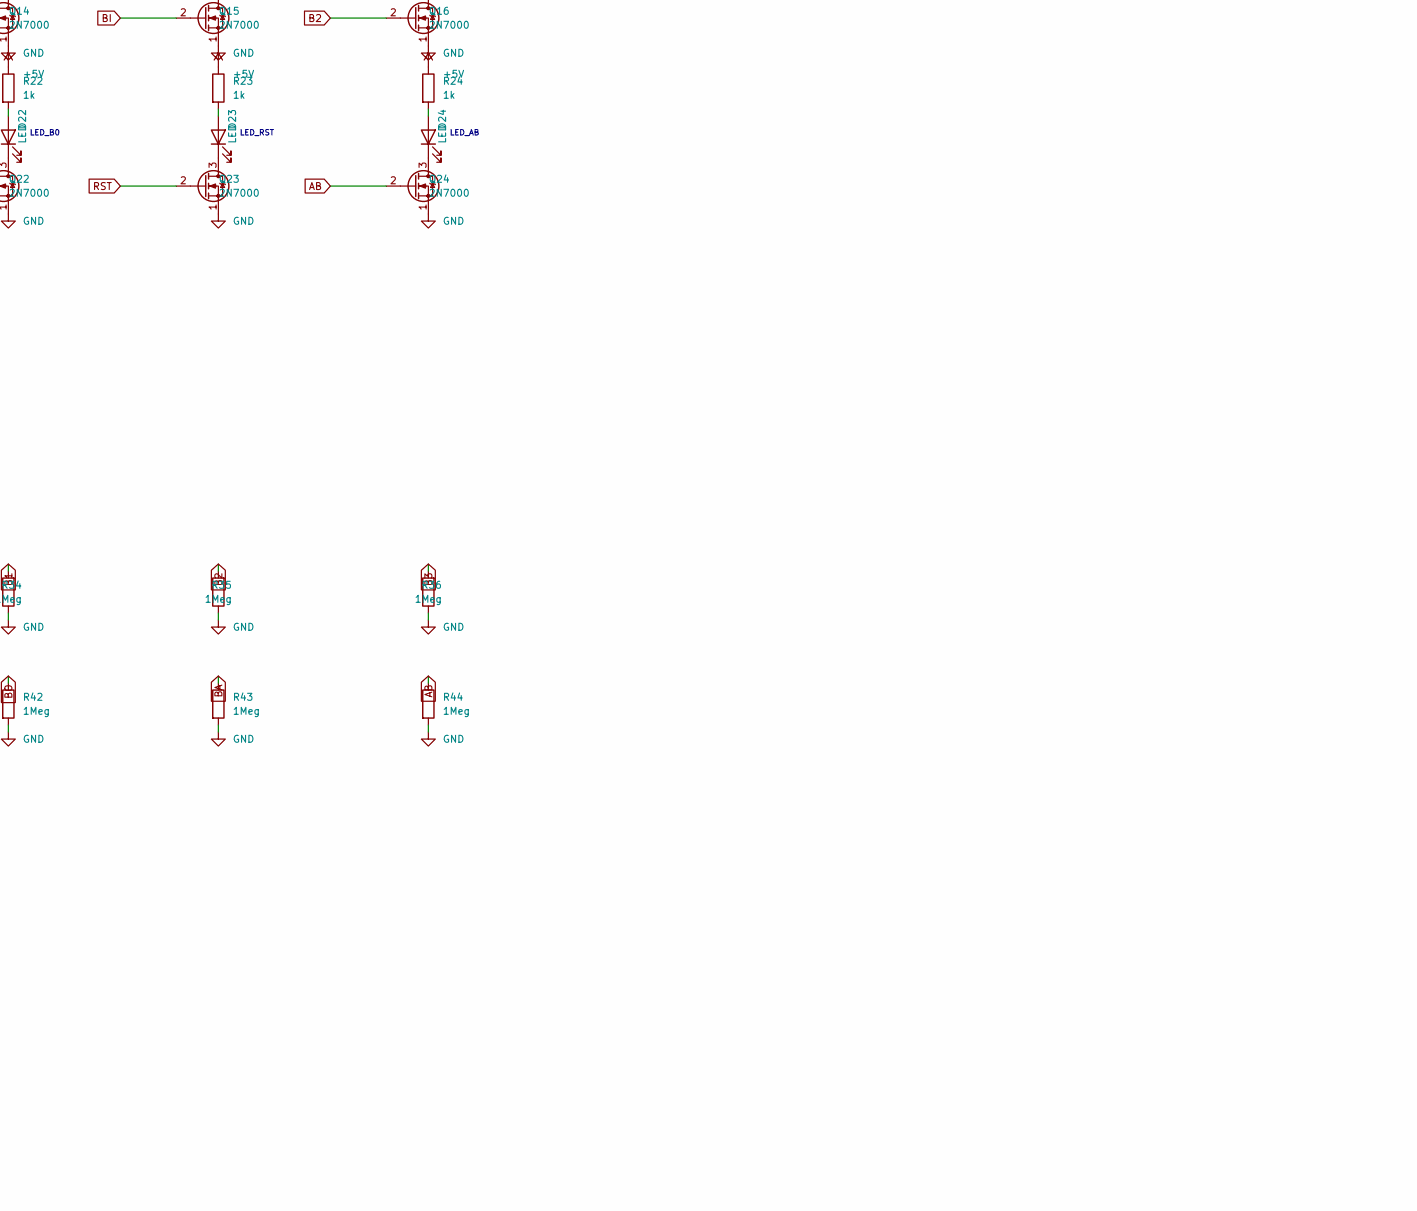
[picture p67: schematic panela.kicad_sch, part in row 2, column 2]

Parts:
C1: 100n; C_Disc_D5.0mm_W2.5mm_P2.50mm
C2: 10u; CP_Radial_D5.0mm_P2.00mm
D1, D2, D3, D4, D5, D6, D7, D8, D9, D10, D11, D12, D13, D14, D15, D16, D17, D18, D19, D20, D21, D22, D23, D24: LED; LED_D3.0mm
H1, H2: M3; MountingHole_3.2mm_M3_Pad
J1: BUS; IDC-Header_2x32_P2.54mm_Vertical
Q1, Q2, Q3, Q4, Q5, Q6, Q7, Q8, Q9, Q10, Q11, Q12, Q13, Q14, Q15, Q16, Q17, Q18, Q19, Q20, Q21, Q22, Q23, Q24, Q25, Q26, Q27, Q28: 2N7000; TO-92_Inline_Wide
R1, R2, R3, R4, R5, R6, R7, R8, R9, R10, R11, R12, R13, R14, R15, R16, R17, R18, R19, R20, R21, R22, R23, R24: 1k; R_Axial_DIN0207_L6.3mm_D2.5mm_P5.08mm_Vertical
R25, R26, R27, R28: 47k; R_Axial_DIN0207_L6.3mm_D2.5mm_P5.08mm_Vertical
R29, R30, R31, R32, R33, R34, R35, R36, R37, R38, R39, R40, R41, R42, R43, R44, R45, R46: 1Meg; R_Axial_DIN0207_L6.3mm_D2.5mm_P5.08mm_Vertical
R47, R48, R49, R50, R51, R52, R53, R54, R55, R56, R57, R58, R59, R60, R61, R62, R63, R64: 10k; R_Axial_DIN0207_L6.3mm_D2.5mm_P5.08mm_Vertical
SW1: A0 A1 A2 A3 B0 B1 B2 B3 (switch ON = 1); SW_DIP_SPSTx08_Slide_9.78x22.5mm_W7.62mm_P2.54mm
SW2: SUB EO AI AO BI BO BA AB; SW_DIP_SPSTx08_Slide_9.78x22.5mm_W7.62mm_P2.54mm

Connections:
+5V: C1.1, C2.1, J1.1, J1.2, J1.64, R1.2, R2.2, R3.2, R4.1, R5.1, R6.1, R7.2, R8.2, R9.2, R10.1, R11.1, R12.1, R13.2, R14.2, R15.2, R16.1, R17.1, R18.1, R19.2, R20.2, R21.2, R22.1, R23.1, R24.1, R25.2, R26.2, R27.2, R28.2, SW1.9, SW1.10, SW1.11, SW1.12, SW1.13, SW1.14, SW1.15, SW1.16, SW2.9, SW2.10, SW2.11, SW2.12, SW2.13, SW2.14, SW2.15, SW2.16
A0: J1.14, Q10.2 (G), R29.1, R49.1
A1: J1.13, Q7.2 (G), R30.2, R50.1
A2: J1.16, Q4.2 (G), R31.2, R51.1
A3: J1.15, Q1.2 (G), R32.2, R52.1
AB: J1.45, Q24.2 (G), R44.1, R64.1
AI: J1.42, Q9.2 (G), R39.2, R59.1
AO: J1.41, Q12.2 (G), R40.1, R60.1
B0: J1.18, Q22.2 (G), R33.2, R53.1
B1: J1.17, Q19.2 (G), R34.2, R54.1
B2: J1.20, Q16.2 (G), R35.2, R55.1
B3: J1.19, Q13.2 (G), R36.2, R56.1
BA: J1.46, Q21.2 (G), R43.1, R63.1
BI: J1.44, Q15.2 (G), R41.1, R61.1
BO: J1.43, Q18.2 (G), R42.1, R62.1
BUS0#: J1.10, Q25.2 (G)
BUS1#: J1.9, Q26.2 (G)
BUS2#: J1.12, Q27.2 (G)
BUS3#: J1.11, Q28.2 (G)
CF: J1.38, Q14.2 (G), R45.1
CLK: J1.6, Q20.2 (G), R47.1
D0: Q11.2 (G), Q25.3 (D), R25.1
D1: Q8.2 (G), Q26.3 (D), R26.1
D2: Q5.2 (G), Q27.3 (D), R27.1
D3: Q2.2 (G), Q28.3 (D), R28.1
EO: J1.39, Q6.2 (G), R38.2, R58.1
GND: C1.2, C2.2, J1.3, J1.4, J1.5, J1.7, J1.63, Q1.1 (S), Q2.1 (S), Q3.1 (S), Q4.1 (S), Q5.1 (S), Q6.1 (S), Q7.1 (S), Q8.1 (S), Q9.1 (S), Q10.1 (S), Q11.1 (S), Q12.1 (S), Q13.1 (S), Q14.1 (S), Q15.1 (S), Q16.1 (S), Q17.1 (S), Q18.1 (S), Q19.1 (S), Q20.1 (S), Q21.1 (S), Q22.1 (S), Q23.1 (S), Q24.1 (S), Q25.1 (S), Q26.1 (S), Q27.1 (S), Q28.1 (S), R29.2, R30.1, R31.1, R32.1, R33.1, R34.1, R35.1, R36.1, R37.1, R38.1, R39.1, R40.2, R41.2, R42.2, R43.2, R44.2, R45.2, R46.2, R47.2, R48.2
unnamed: D1.2 (A), R1.1
unnamed: D1.1 (K), Q1.3 (D)
unnamed: D2.2 (A), R2.1
unnamed: D2.1 (K), Q2.3 (D)
unnamed: D3.2 (A), R3.1
unnamed: D3.1 (K), Q3.3 (D)
unnamed: D4.2 (A), R4.2
unnamed: D4.1 (K), Q4.3 (D)
unnamed: D5.2 (A), R5.2
unnamed: D5.1 (K), Q5.3 (D)
unnamed: D6.2 (A), R6.2
unnamed: D6.1 (K), Q6.3 (D)
unnamed: D7.2 (A), R7.1
unnamed: D7.1 (K), Q7.3 (D)
unnamed: D8.2 (A), R8.1
unnamed: D8.1 (K), Q8.3 (D)
unnamed: D9.2 (A), R9.1
unnamed: D9.1 (K), Q9.3 (D)
unnamed: D10.2 (A), R10.2
unnamed: D10.1 (K), Q10.3 (D)
unnamed: D11.2 (A), R11.2
unnamed: D11.1 (K), Q11.3 (D)
unnamed: D12.2 (A), R12.2
unnamed: D12.1 (K), Q12.3 (D)
unnamed: D13.2 (A), R13.1
unnamed: D13.1 (K), Q13.3 (D)
unnamed: D14.2 (A), R14.1
unnamed: D14.1 (K), Q14.3 (D)
unnamed: D15.2 (A), R15.1
unnamed: D15.1 (K), Q15.3 (D)
unnamed: D16.2 (A), R16.2
unnamed: D16.1 (K), Q16.3 (D)
unnamed: D17.2 (A), R17.2
unnamed: D17.1 (K), Q17.3 (D)
unnamed: D18.2 (A), R18.2
unnamed: D18.1 (K), Q18.3 (D)
unnamed: D19.2 (A), R19.1
unnamed: D19.1 (K), Q19.3 (D)
unnamed: D20.2 (A), R20.1
unnamed: D20.1 (K), Q20.3 (D)
unnamed: D21.2 (A), R21.1
unnamed: D21.1 (K), Q21.3 (D)
unnamed: D22.2 (A), R22.2
unnamed: D22.1 (K), Q22.3 (D)
unnamed: D23.2 (A), R23.2
unnamed: D23.1 (K), Q23.3 (D)
unnamed: D24.2 (A), R24.2
unnamed: D24.1 (K), Q24.3 (D)
unnamed: R49.2, SW1.1
unnamed: R50.2, SW1.2
unnamed: R51.2, SW1.3
unnamed: R52.2, SW1.4
unnamed: R53.2, SW1.5
unnamed: R54.2, SW1.6
unnamed: R55.2, SW1.7
unnamed: R56.2, SW1.8
unnamed: R57.2, SW2.1
unnamed: R58.2, SW2.2
unnamed: R59.2, SW2.3
unnamed: R60.2, SW2.4
unnamed: R61.2, SW2.5
unnamed: R62.2, SW2.6
unnamed: R63.2, SW2.7
unnamed: R64.2, SW2.8
RST: J1.8, Q23.2 (G), R48.1
SUB: J1.40, Q3.2 (G), R37.2, R57.1
ZF: J1.37, Q17.2 (G), R46.1

Notes on the sheet:
NIBBLE CARD PANEL A - FRONT PANEL, LEVELS 1: switches for A3..A0 B3..B0 and SUB..AB, their LEDs, the bus data LEDs, CF ZF CLK RST LEDs
Cell: 2N7000 + 47k pull-up (NMOS, see docs/gate-cell.md). 28 transistors, 48 resistors, 24 LEDs, 100 x 100 mm (docs/cards.md). Level switches connect a line to +5V through 10k: a switch left on can never fight a card that pulls the line low, it only adds a 1 where nothing else drives. Every switche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
INDICATORS: one LED per bus line. A MOSFET gate draws no current, so the LEDs load nothing.
LED_A3
LED_D3
LED_SUB
LED_A2
LED_D2
LED_EO
LED_A1
LED_D1
LED_AI
LED_A0
LED_D0
LED_AO
LED_B3
LED_CF
LED_BI
LED_B2
LED_ZF
LED_BO
LED_B1
LED_CLK
LED_BA
LED_B0
LED_RST
LED_AB
BUS DATA: BUS_i# is active-low, so an inverter turns it into the data bit D_i for its LED
PULL-DOWNS: 1Meg to ground on every line this card switches or observes, so it reads 0 when no card drives it
Decoupling
Mounting holes

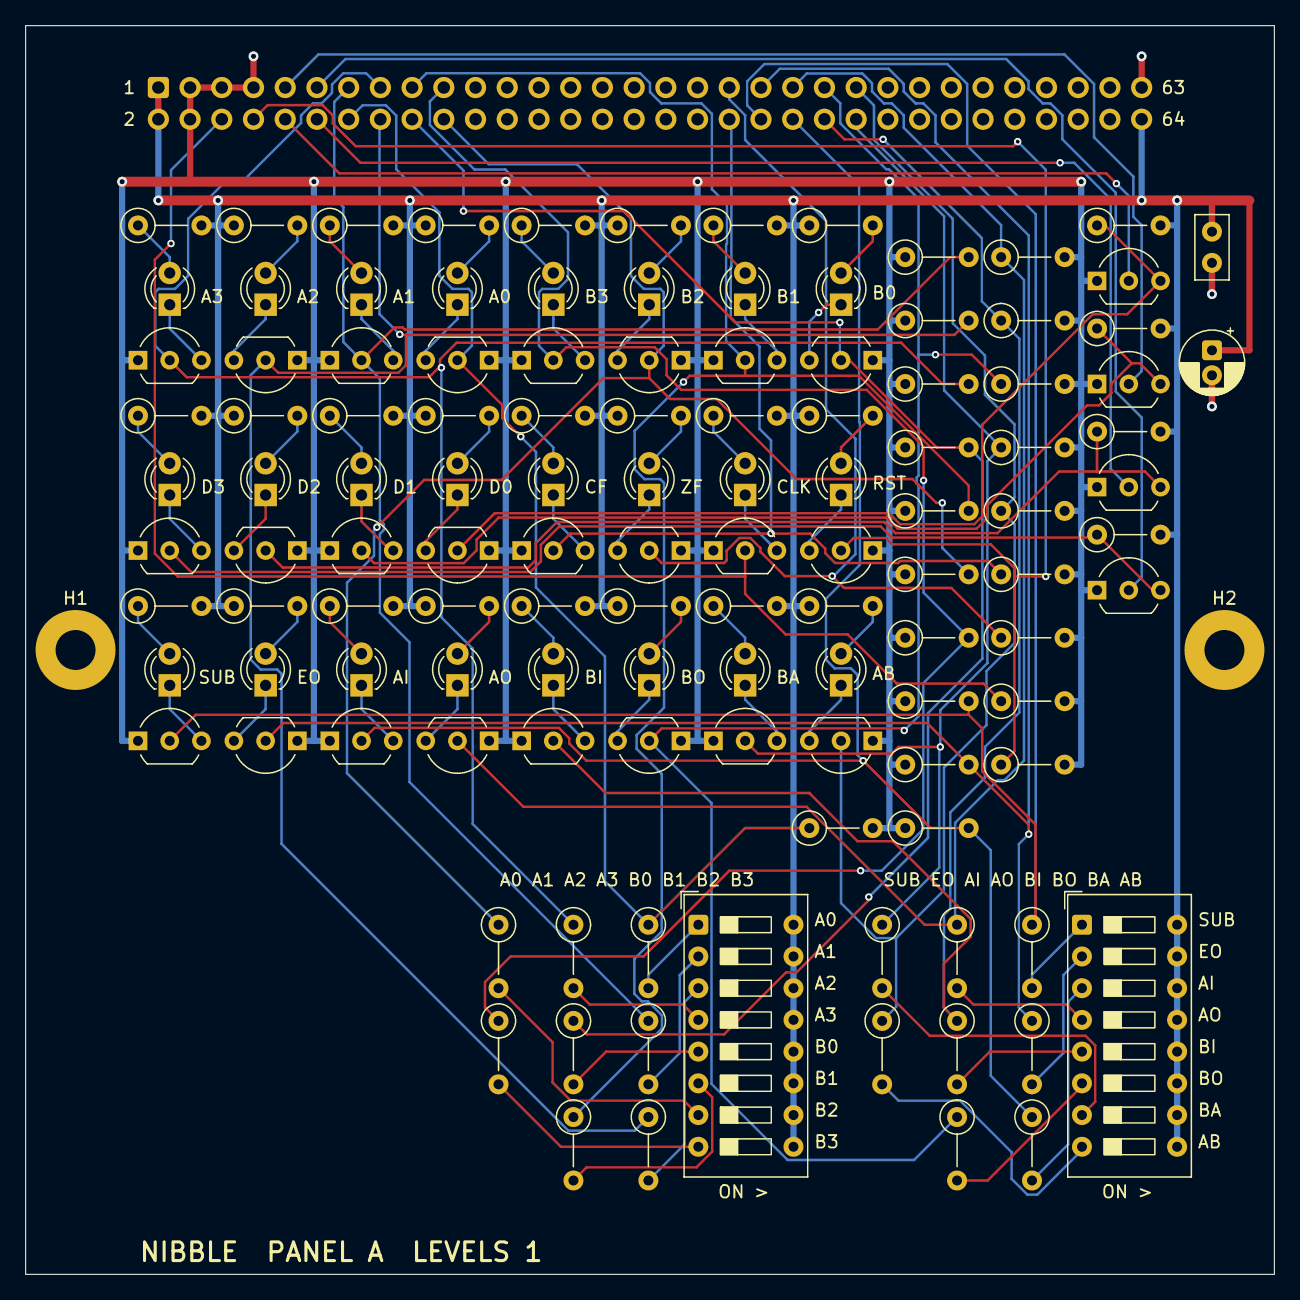
[picture p68: board panela.kicad_pcb from above]

Board: 2 copper layers, 100.0 x 100.0 mm, 123 parts (1 on the bottom side), 94 nets.
