nikolafilip/nibble/cards/prog/prog.kicad_pcb

## KiCad design cards/prog/prog.kicad_pcb (2026-10-01)

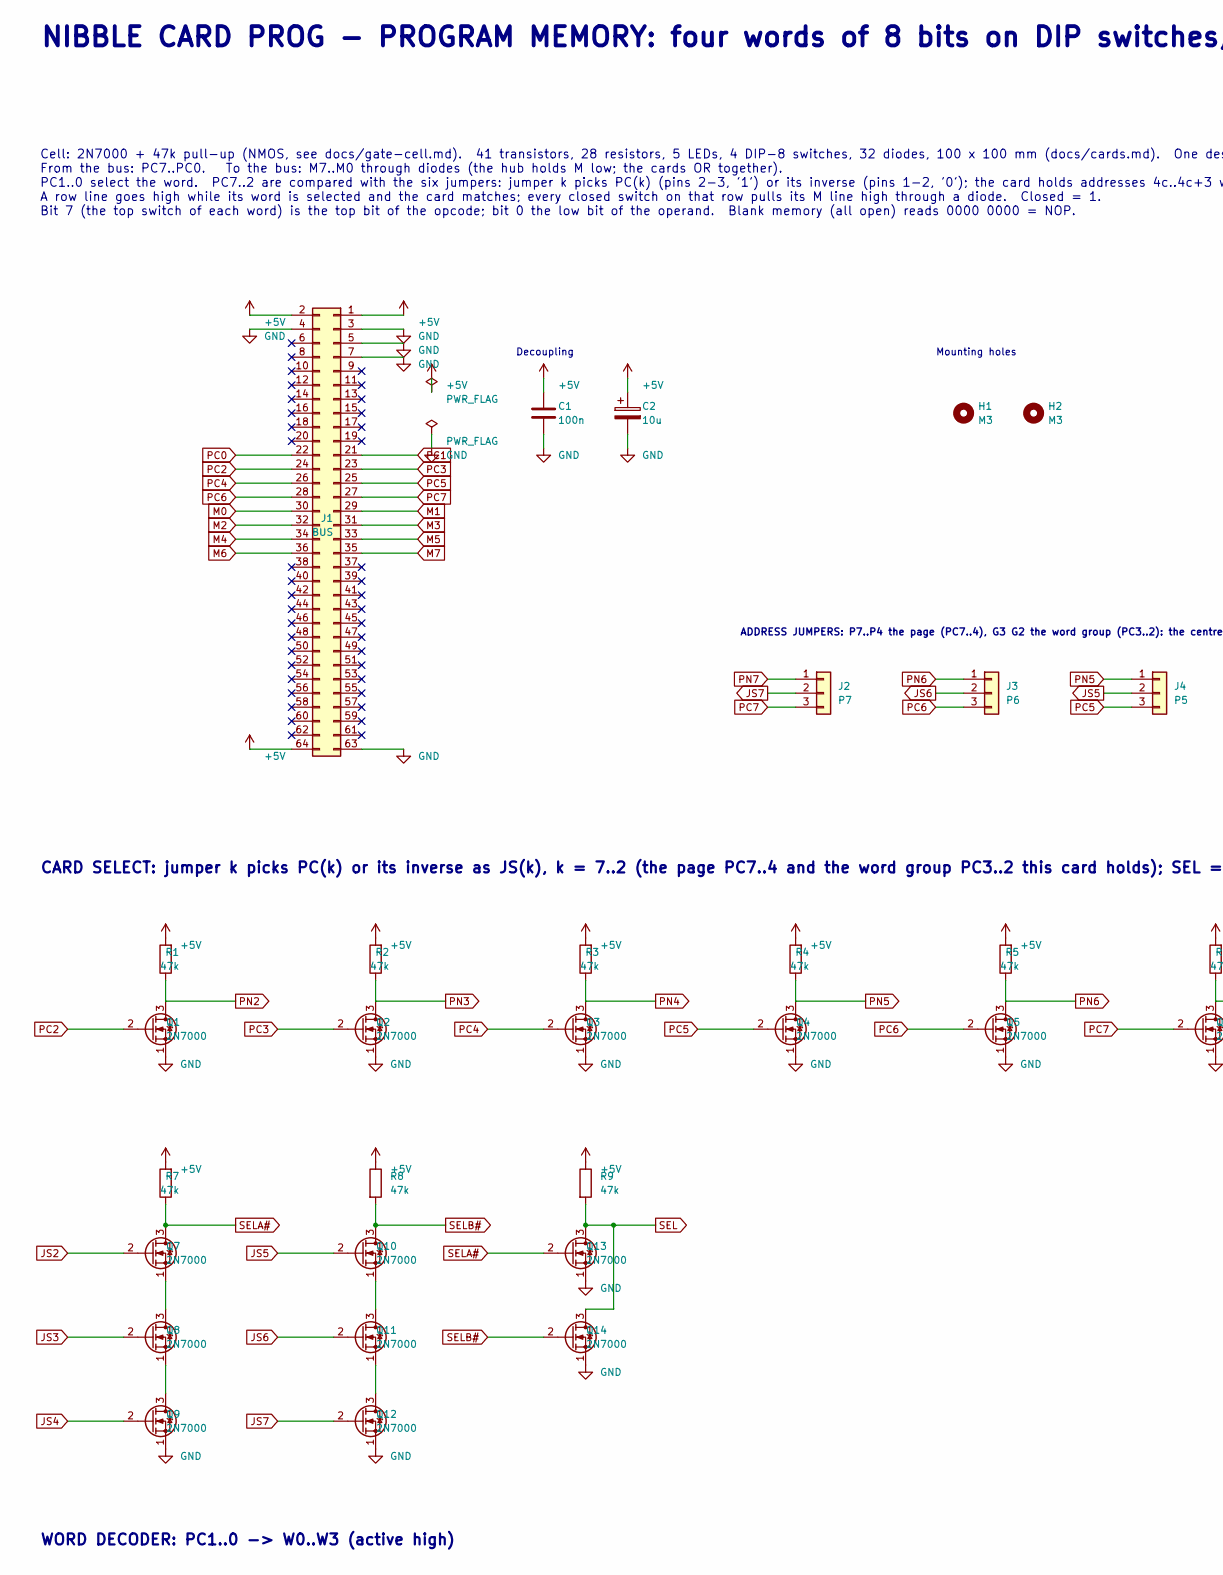
[picture p69: schematic prog.kicad_sch, part in row 1, column 1]

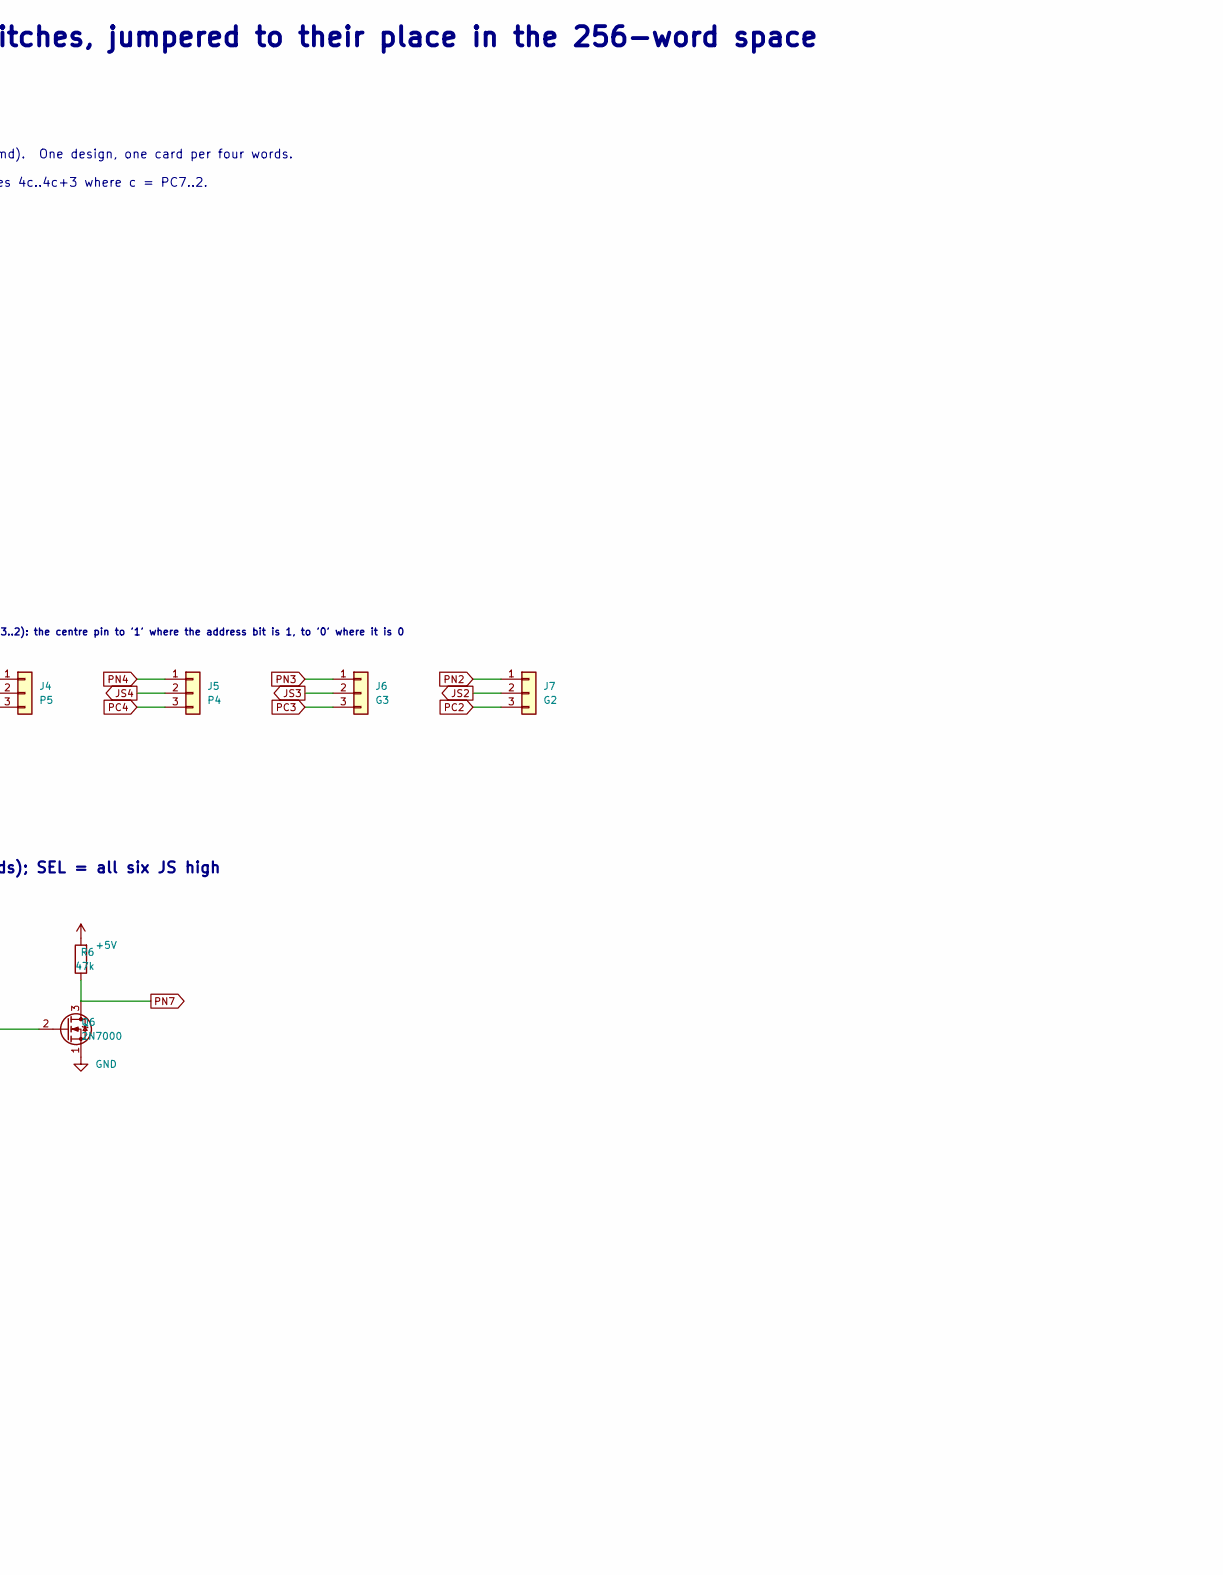
[picture p70: schematic prog.kicad_sch, part in row 1, column 2]

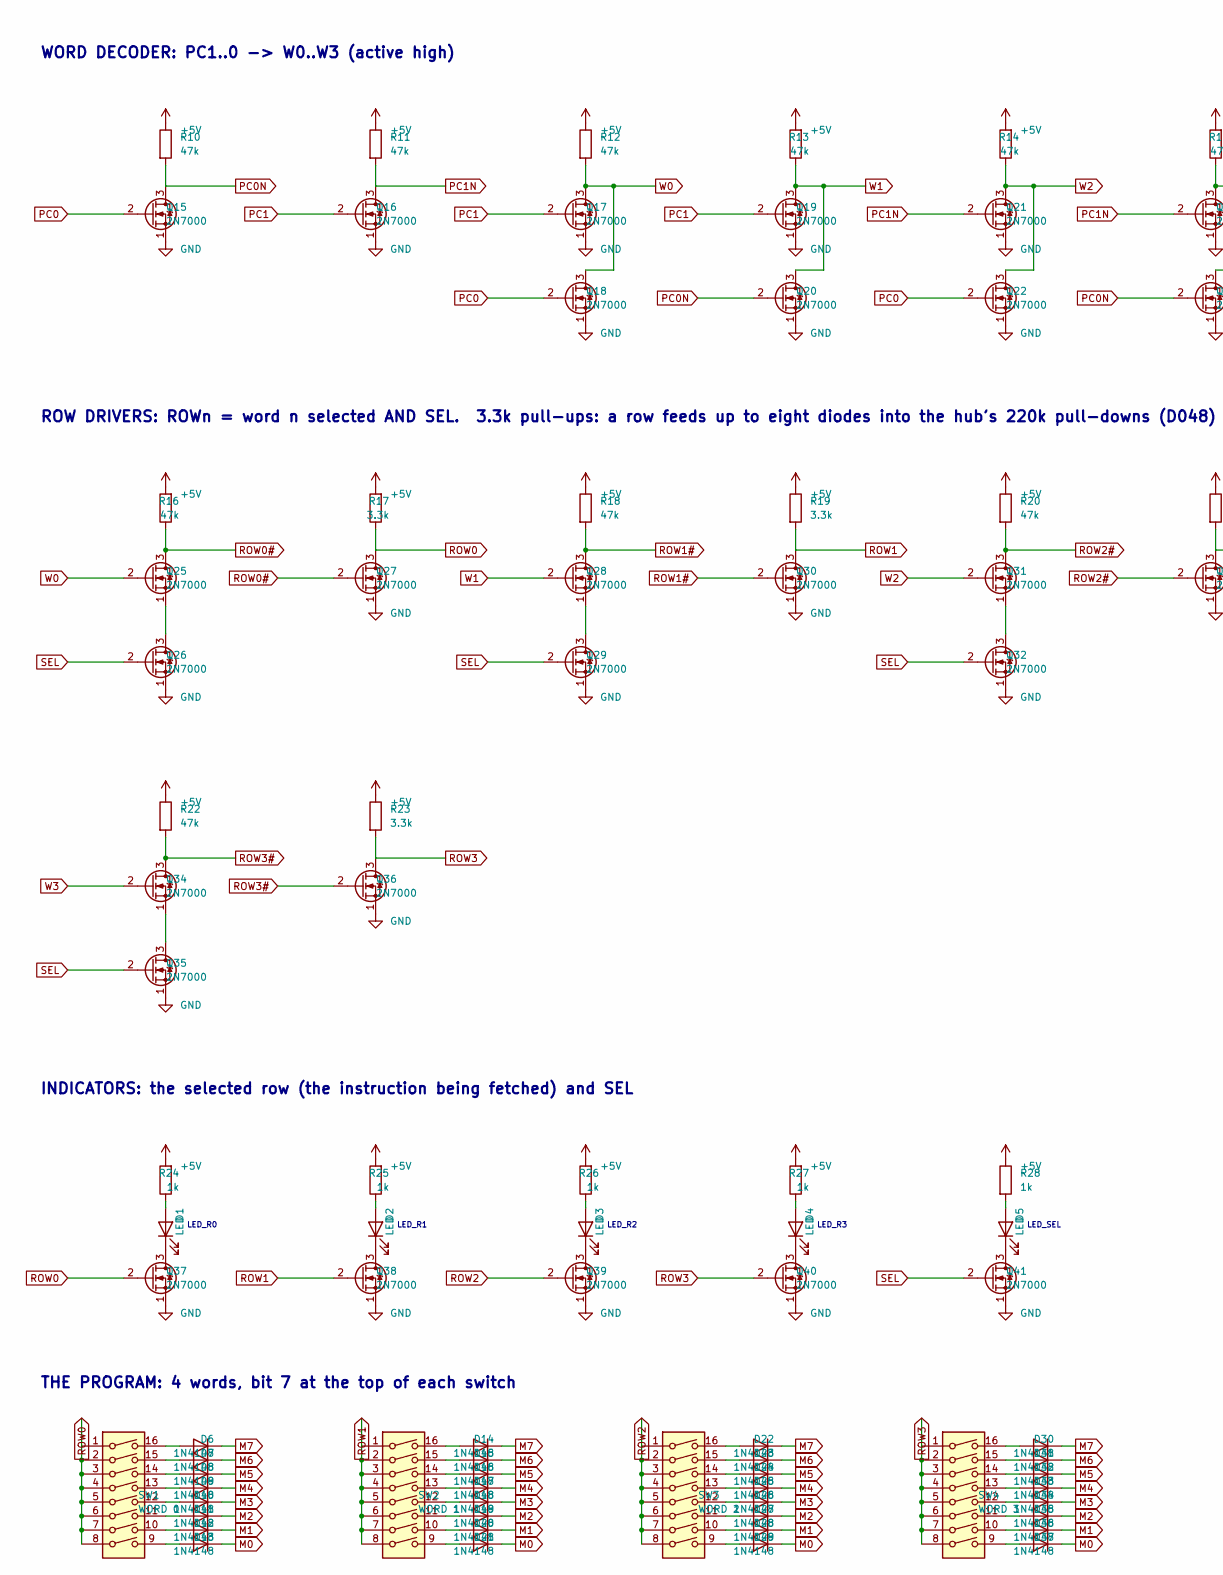
[picture p71: schematic prog.kicad_sch, part in row 2, column 1]

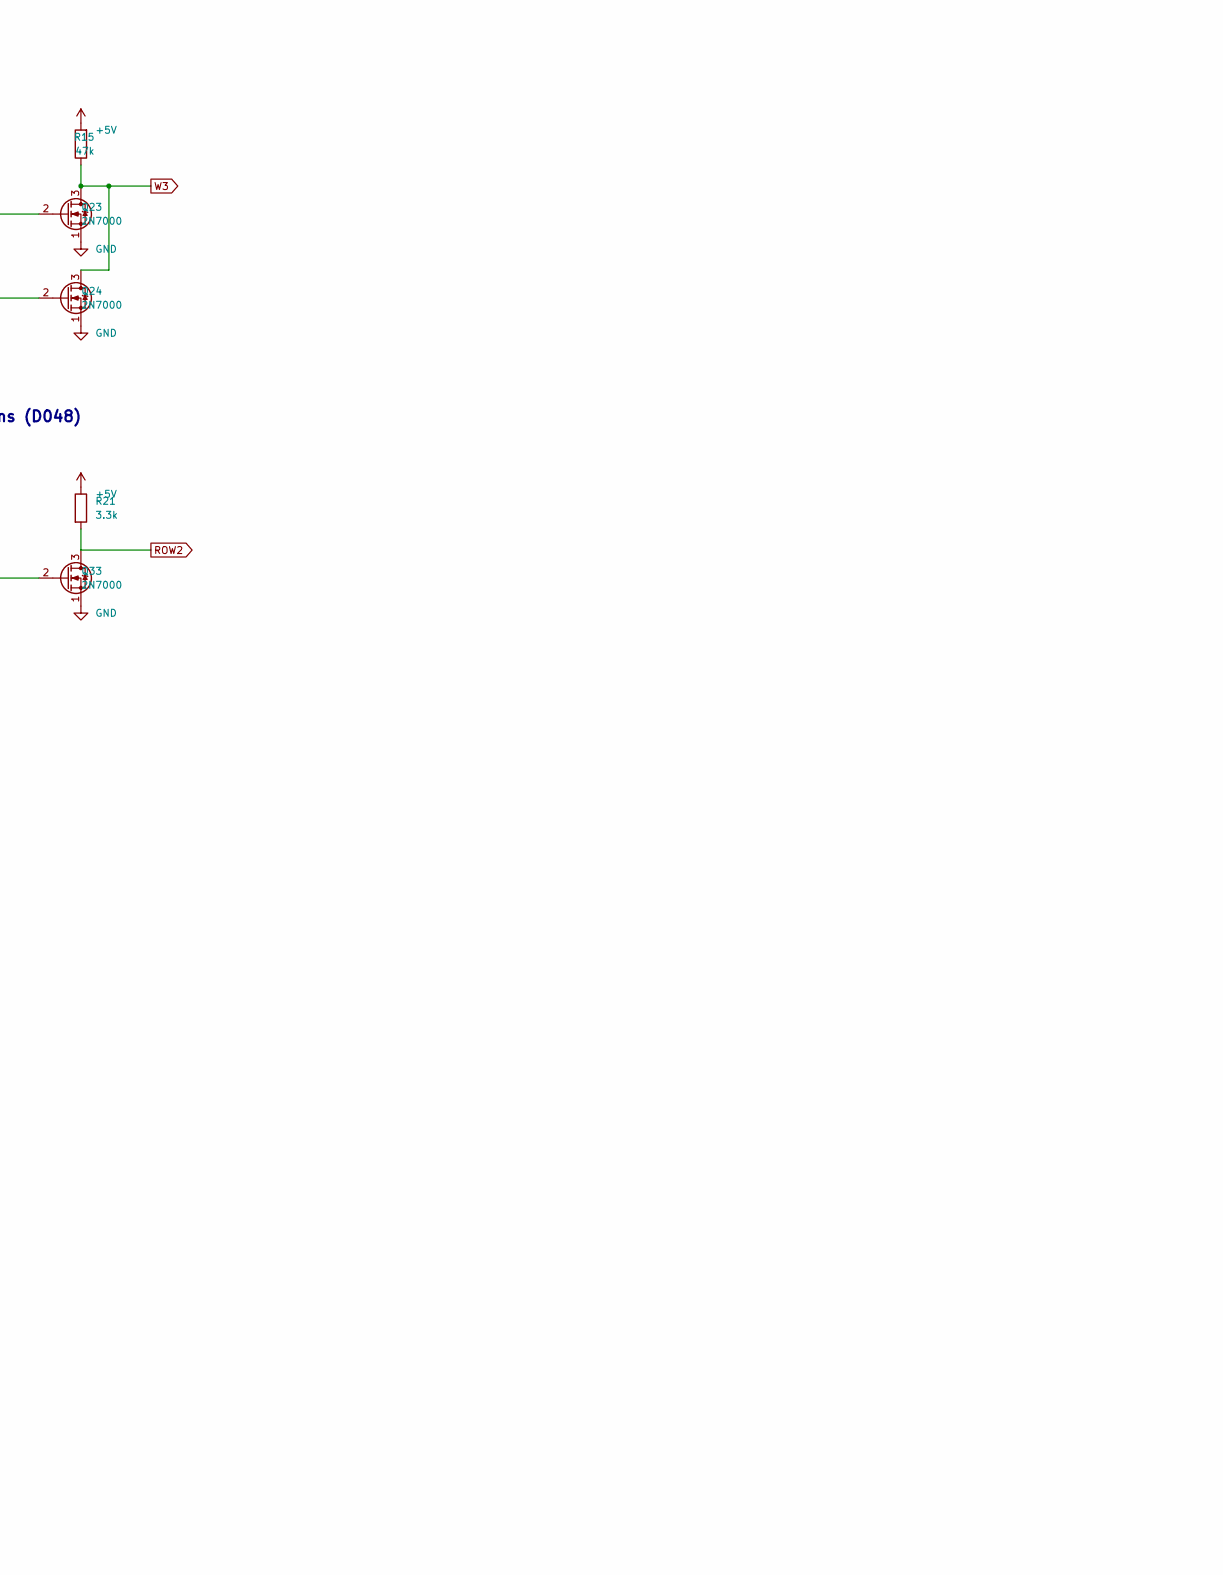
[picture p72: schematic prog.kicad_sch, part in row 2, column 2]

Parts:
C1: 100n; C_Disc_D5.0mm_W2.5mm_P2.50mm
C2: 10u; CP_Radial_D5.0mm_P2.00mm
D1, D2, D3, D4, D5: LED; LED_D3.0mm
D6, D7, D8, D9, D10, D11, D12, D13, D14, D15, D16, D17, D18, D19, D20, D21, D22, D23, D24, D25, D26, D27, D28, D29, D30, D31, D32, D33, D34, D35, D36, D37: 1N4148; D_DO-35_SOD27_P2.54mm_Vertical_AnodeUp
H1, H2: M3; MountingHole_3.2mm_M3_Pad
J1: BUS; IDC-Header_2x32_P2.54mm_Vertical
J2: P7; PinHeader_1x03_P2.54mm_Vertical
J3: P6; PinHeader_1x03_P2.54mm_Vertical
J4: P5; PinHeader_1x03_P2.54mm_Vertical
J5: P4; PinHeader_1x03_P2.54mm_Vertical
J6: G3; PinHeader_1x03_P2.54mm_Vertical
J7: G2; PinHeader_1x03_P2.54mm_Vertical
Q1, Q2, Q3, Q4, Q5, Q6, Q7, Q8, Q9, Q10, Q11, Q12, Q13, Q14, Q15, Q16, Q17, Q18, Q19, Q20, Q21, Q22, Q23, Q24, Q25, Q26, Q27, Q28, Q29, Q30, Q31, Q32, Q33, Q34, Q35, Q36, Q37, Q38, Q39, Q40, Q41: 2N7000; TO-92_Inline_Wide
R1, R2, R3, R4, R5, R6, R7, R8, R9, R10, R11, R12, R13, R14, R15, R16, R18, R20, R22: 47k; R_Axial_DIN0207_L6.3mm_D2.5mm_P5.08mm_Vertical
R17, R19, R21, R23: 3.3k; R_Axial_DIN0207_L6.3mm_D2.5mm_P5.08mm_Vertical
R24, R25, R26, R27, R28: 1k; R_Axial_DIN0207_L6.3mm_D2.5mm_P5.08mm_Vertical
SW1: WORD 0; SW_DIP_SPSTx08_Slide_9.78x22.5mm_W7.62mm_P2.54mm
SW2: WORD 1; SW_DIP_SPSTx08_Slide_9.78x22.5mm_W7.62mm_P2.54mm
SW3: WORD 2; SW_DIP_SPSTx08_Slide_9.78x22.5mm_W7.62mm_P2.54mm
SW4: WORD 3; SW_DIP_SPSTx08_Slide_9.78x22.5mm_W7.62mm_P2.54mm

Connections:
+5V: C1.1, C2.1, J1.1, J1.2, J1.64, R1.2, R2.2, R3.2, R4.2, R5.2, R6.2, R7.2, R8.1, R9.1, R10.1, R11.1, R12.1, R13.2, R14.2, R15.2, R16.2, R17.2, R18.1, R19.1, R20.1, R21.1, R22.1, R23.1, R24.2, R25.2, R26.2, R27.2, R28.1
GND: C1.2, C2.2, J1.3, J1.4, J1.5, J1.7, J1.63, Q1.1 (S), Q2.1 (S), Q3.1 (S), Q4.1 (S), Q5.1 (S), Q6.1 (S), Q9.1 (S), Q12.1 (S), Q13.1 (S), Q14.1 (S), Q15.1 (S), Q16.1 (S), Q17.1 (S), Q18.1 (S), Q19.1 (S), Q20.1 (S), Q21.1 (S), Q22.1 (S), Q23.1 (S), Q24.1 (S), Q26.1 (S), Q27.1 (S), Q29.1 (S), Q30.1 (S), Q32.1 (S), Q33.1 (S), Q35.1 (S), Q36.1 (S), Q37.1 (S), Q38.1 (S), Q39.1 (S), Q40.1 (S), Q41.1 (S)
JS2: J7.2, Q7.2 (G)
JS3: J6.2, Q8.2 (G)
JS4: J5.2, Q9.2 (G)
JS5: J4.2, Q10.2 (G)
JS6: J3.2, Q11.2 (G)
JS7: J2.2, Q12.2 (G)
M0: D13.1 (K), D21.1 (K), D29.1 (K), D37.1 (K), J1.30
M1: D12.1 (K), D20.1 (K), D28.1 (K), D36.1 (K), J1.29
M2: D11.1 (K), D19.1 (K), D27.1 (K), D35.1 (K), J1.32
M3: D10.1 (K), D18.1 (K), D26.1 (K), D34.1 (K), J1.31
M4: D9.1 (K), D17.1 (K), D25.1 (K), D33.1 (K), J1.34
M5: D8.1 (K), D16.1 (K), D24.1 (K), D32.1 (K), J1.33
M6: D7.1 (K), D15.1 (K), D23.1 (K), D31.1 (K), J1.36
M7: D6.1 (K), D14.1 (K), D22.1 (K), D30.1 (K), J1.35
unnamed: D1.2 (A), R24.1
unnamed: D1.1 (K), Q37.3 (D)
unnamed: D2.2 (A), R25.1
unnamed: D2.1 (K), Q38.3 (D)
unnamed: D3.2 (A), R26.1
unnamed: D3.1 (K), Q39.3 (D)
unnamed: D4.2 (A), R27.1
unnamed: D4.1 (K), Q40.3 (D)
unnamed: D5.2 (A), R28.2
unnamed: D5.1 (K), Q41.3 (D)
unnamed: D6.2 (A), SW1.16
unnamed: D7.2 (A), SW1.15
unnamed: D8.2 (A), SW1.14
unnamed: D9.2 (A), SW1.13
unnamed: D10.2 (A), SW1.12
unnamed: D11.2 (A), SW1.11
unnamed: D12.2 (A), SW1.10
unnamed: D13.2 (A), SW1.9
unnamed: D14.2 (A), SW2.16
unnamed: D15.2 (A), SW2.15
unnamed: D16.2 (A), SW2.14
unnamed: D17.2 (A), SW2.13
unnamed: D18.2 (A), SW2.12
unnamed: D19.2 (A), SW2.11
unnamed: D20.2 (A), SW2.10
unnamed: D21.2 (A), SW2.9
unnamed: D22.2 (A), SW3.16
unnamed: D23.2 (A), SW3.15
unnamed: D24.2 (A), SW3.14
unnamed: D25.2 (A), SW3.13
unnamed: D26.2 (A), SW3.12
unnamed: D27.2 (A), SW3.11
unnamed: D28.2 (A), SW3.10
unnamed: D29.2 (A), SW3.9
unnamed: D30.2 (A), SW4.16
unnamed: D31.2 (A), SW4.15
unnamed: D32.2 (A), SW4.14
unnamed: D33.2 (A), SW4.13
unnamed: D34.2 (A), SW4.12
unnamed: D35.2 (A), SW4.11
unnamed: D36.2 (A), SW4.10
unnamed: D37.2 (A), SW4.9
unnamed: Q7.1 (S), Q8.3 (D)
unnamed: Q8.1 (S), Q9.3 (D)
unnamed: Q10.1 (S), Q11.3 (D)
unnamed: Q11.1 (S), Q12.3 (D)
unnamed: Q25.1 (S), Q26.3 (D)
unnamed: Q28.1 (S), Q29.3 (D)
unnamed: Q31.1 (S), Q32.3 (D)
unnamed: Q34.1 (S), Q35.3 (D)
PC0: J1.22, Q15.2 (G), Q18.2 (G), Q22.2 (G)
PC0N: Q15.3 (D), Q20.2 (G), Q24.2 (G), R10.2
PC1: J1.21, Q16.2 (G), Q17.2 (G), Q19.2 (G)
PC1N: Q16.3 (D), Q21.2 (G), Q23.2 (G), R11.2
PC2: J1.24, J7.3, Q1.2 (G)
PC3: J1.23, J6.3, Q2.2 (G)
PC4: J1.26, J5.3, Q3.2 (G)
PC5: J1.25, J4.3, Q4.2 (G)
PC6: J1.28, J3.3, Q5.2 (G)
PC7: J1.27, J2.3, Q6.2 (G)
PN2: J7.1, Q1.3 (D), R1.1
PN3: J6.1, Q2.3 (D), R2.1
PN4: J5.1, Q3.3 (D), R3.1
PN5: J4.1, Q4.3 (D), R4.1
PN6: J3.1, Q5.3 (D), R5.1
PN7: J2.1, Q6.3 (D), R6.1
ROW0: Q27.3 (D), Q37.2 (G), R17.1, SW1.1, SW1.2, SW1.3, SW1.4, SW1.5, SW1.6, SW1.7, SW1.8
ROW0#: Q25.3 (D), Q27.2 (G), R16.1
ROW1: Q30.3 (D), Q38.2 (G), R19.2, SW2.1, SW2.2, SW2.3, SW2.4, SW2.5, SW2.6, SW2.7, SW2.8
ROW1#: Q28.3 (D), Q30.2 (G), R18.2
ROW2: Q33.3 (D), Q39.2 (G), R21.2, SW3.1, SW3.2, SW3.3, SW3.4, SW3.5, SW3.6, SW3.7, SW3.8
ROW2#: Q31.3 (D), Q33.2 (G), R20.2
ROW3: Q36.3 (D), Q40.2 (G), R23.2, SW4.1, SW4.2, SW4.3, SW4.4, SW4.5, SW4.6, SW4.7, SW4.8
ROW3#: Q34.3 (D), Q36.2 (G), R22.2
SEL: Q13.3 (D), Q14.3 (D), Q26.2 (G), Q29.2 (G), Q32.2 (G), Q35.2 (G), Q41.2 (G), R9.2
SELA#: Q7.3 (D), Q13.2 (G), R7.1
SELB#: Q10.3 (D), Q14.2 (G), R8.2
W0: Q17.3 (D), Q18.3 (D), Q25.2 (G), R12.2
W1: Q19.3 (D), Q20.3 (D), Q28.2 (G), R13.1
W2: Q21.3 (D), Q22.3 (D), Q31.2 (G), R14.1
W3: Q23.3 (D), Q24.3 (D), Q34.2 (G), R15.1

Notes on the sheet:
NIBBLE CARD PROG - PROGRAM MEMORY: four words of 8 bits on DIP switches, jumpered to their place in the 256-word space
Cell: 2N7000 + 47k pull-up (NMOS, see docs/gate-cell.md). 41 transistors, 28 resistors, 5 LEDs, 4 DIP-8 switches, 32 diodes, 100 x 100 mm (docs/cards.md). One design, one card per four words. From the bus: PC7..PC0. To the bus: M7..M0 through diodes (the hub holds M low; the cards OR together). PC1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
CARD SELECT: jumper k picks PC(k) or its inverse as JS(k), k = 7..2 (the page PC7..4 and the word group PC3..2 this card holds); SEL = all six JS high
WORD DECODER: PC1..0 -> W0..W3 (active high)
ROW DRIVERS: ROWn = word n selected AND SEL. 3.3k pull-ups: a row feeds up to eight diodes into the hub's 220k pull-downs (D048)
INDICATORS: the selected row (the instruction being fetched) and SEL
LED_R0
LED_R1
LED_R2
LED_R3
LED_SEL
Decoupling
Mounting holes
ADDRESS JUMPERS: P7..P4 the page (PC7..4), G3 G2 the word group (PC3..2): the centre pin to '1' where the address bit is 1, to '0' where it is 0
THE PROGRAM: 4 words, bit 7 at the top of each switch

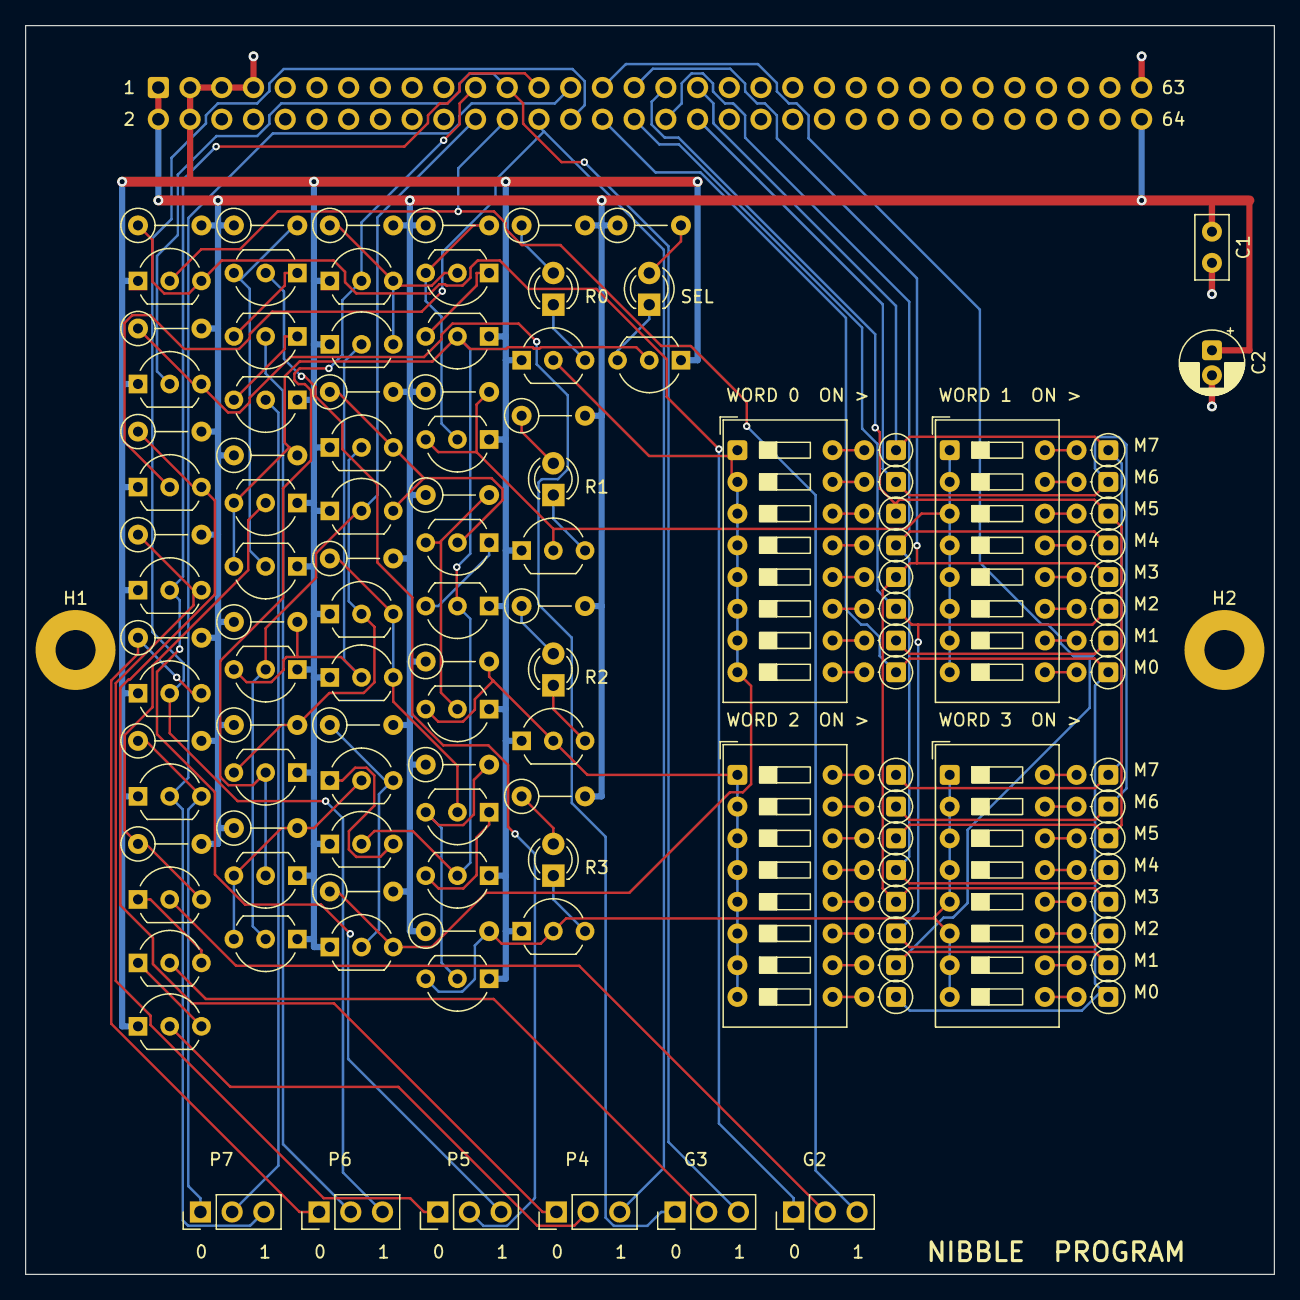
[picture p73: board prog.kicad_pcb from above]

Board: 2 copper layers, 100.0 x 100.0 mm, 121 parts (1 on the bottom side), 97 nets.
