nikolafilip/nibble/cards/hub/hub.kicad_pcb

## KiCad design cards/hub/hub.kicad_pcb (2026-10-01)

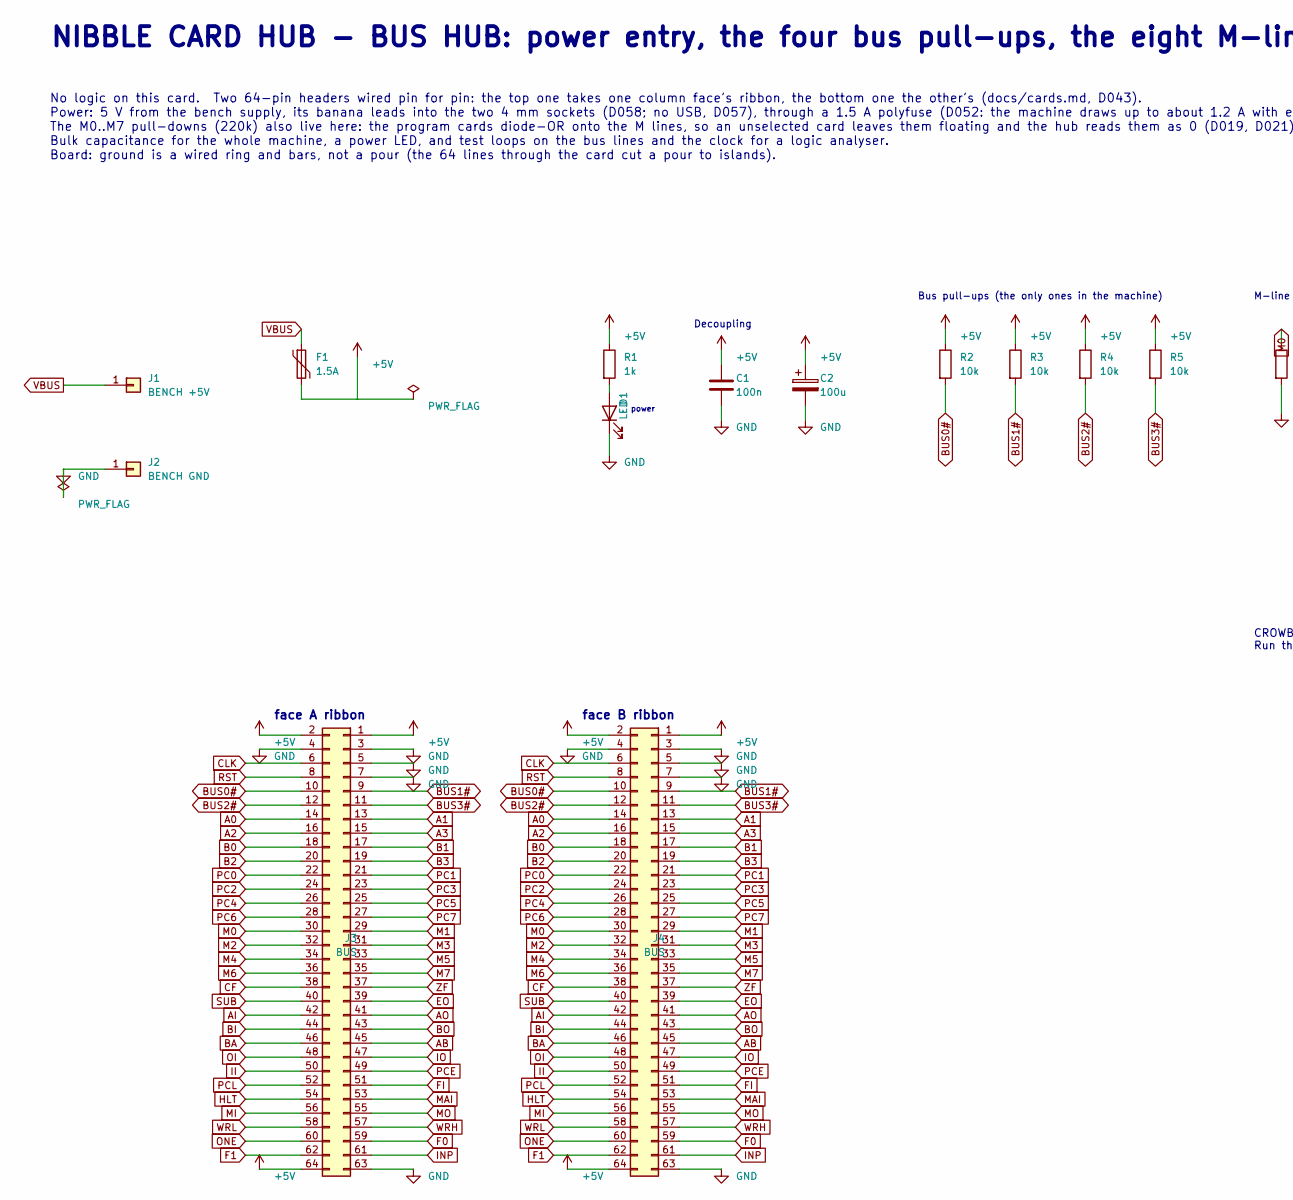
[picture p74: schematic hub.kicad_sch, part in row 1, column 1]

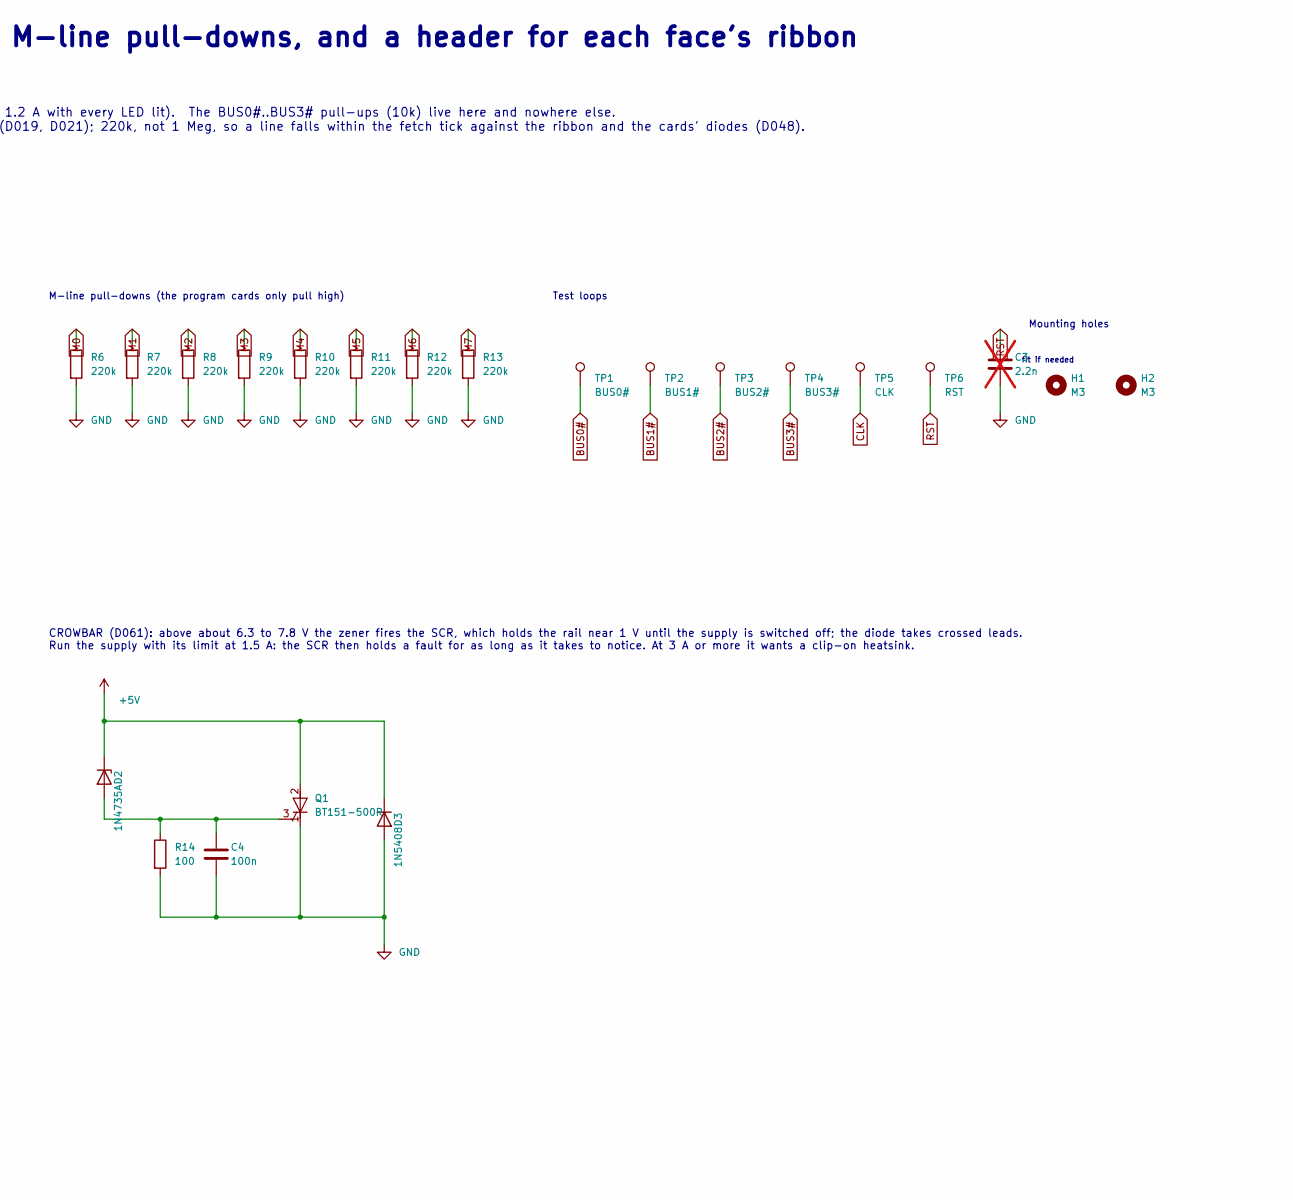
[picture p75: schematic hub.kicad_sch, part in row 1, column 2]

Parts:
C1, C4: 100n; C_Disc_D5.0mm_W2.5mm_P2.50mm
C2: 100u; CP_Radial_D5.0mm_P2.00mm
C3: 2.2n; C_Disc_D5.0mm_W2.5mm_P2.50mm; not fitted
D1: LED; LED_D3.0mm
D2: 1N4735A; D_DO-41_SOD81_P10.16mm_Horizontal
D3: 1N5408; D_DO-201AD_P15.24mm_Horizontal
F1: 1.5A; Fuse_BelFuse_0ZRE0150FF_L23.4mm_W5.3mm
H1, H2: M3; MountingHole_3.2mm_M3_Pad
J1: BENCH +5V; Banana_CalTest_CT3151V1_Vertical
J2: BENCH GND; Banana_CalTest_CT3151V1_Vertical
J3, J4: BUS; IDC-Header_2x32_P2.54mm_Vertical
Q1: BT151-500R; TO-220-3_Vertical
R1: 1k; R_Axial_DIN0207_L6.3mm_D2.5mm_P5.08mm_Vertical
R2, R3, R4, R5: 10k; R_Axial_DIN0207_L6.3mm_D2.5mm_P5.08mm_Vertical
R6, R7, R8, R9, R10, R11, R12, R13: 220k; R_Axial_DIN0207_L6.3mm_D2.5mm_P5.08mm_Vertical
R14: 100; R_Axial_DIN0207_L6.3mm_D2.5mm_P5.08mm_Vertical
TP1: BUS0#; TestPoint_Loop_D2.50mm_Drill1.0mm
TP2: BUS1#; TestPoint_Loop_D2.50mm_Drill1.0mm
TP3: BUS2#; TestPoint_Loop_D2.50mm_Drill1.0mm
TP4: BUS3#; TestPoint_Loop_D2.50mm_Drill1.0mm
TP5: CLK; TestPoint_Loop_D2.50mm_Drill1.0mm
TP6: RST; TestPoint_Loop_D2.50mm_Drill1.0mm

Connections:
+5V: C1.1, C2.1, D2.1 (K), D3.1 (K), F1.2, J3.1, J3.2, J3.64, J4.1, J4.2, J4.64, Q1.2 (A), R1.1, R2.1, R3.1, R4.1, R5.1
A0: J3.14, J4.14
A1: J3.13, J4.13
A2: J3.16, J4.16
A3: J3.15, J4.15
AB: J3.45, J4.45
AI: J3.42, J4.42
AO: J3.41, J4.41
B0: J3.18, J4.18
B1: J3.17, J4.17
B2: J3.20, J4.20
B3: J3.19, J4.19
BA: J3.46, J4.46
BI: J3.44, J4.44
BO: J3.43, J4.43
BUS0#: J3.10, J4.10, R2.2, TP1.1
BUS1#: J3.9, J4.9, R3.2, TP2.1
BUS2#: J3.12, J4.12, R4.2, TP3.1
BUS3#: J3.11, J4.11, R5.2, TP4.1
CF: J3.38, J4.38
CLK: J3.6, J4.6, TP5.1
EO: J3.39, J4.39
F0: J3.59, J4.59
F1: J3.62, J4.62
FI: J3.51, J4.51
GND: C1.2, C2.2, C3.2, C4.2, D1.1 (K), D3.2 (A), J2.1, J3.3, J3.4, J3.5, J3.7, J3.63, J4.3, J4.4, J4.5, J4.7, J4.63, Q1.1 (K), R6.2, R7.2, R8.2, R9.2, R10.2, R11.2, R12.2, R13.2, R14.2
HLT: J3.54, J4.54
II: J3.50, J4.50
INP: J3.61, J4.61
IO: J3.47, J4.47
M0: J3.30, J4.30, R6.1
M1: J3.29, J4.29, R7.1
M2: J3.32, J4.32, R8.1
M3: J3.31, J4.31, R9.1
M4: J3.34, J4.34, R10.1
M5: J3.33, J4.33, R11.1
M6: J3.36, J4.36, R12.1
M7: J3.35, J4.35, R13.1
MAI: J3.53, J4.53
MI: J3.56, J4.56
MO: J3.55, J4.55
unnamed: D1.2 (A), R1.2
unnamed: C4.1, D2.2 (A), Q1.3 (G), R14.1
OI: J3.48, J4.48
ONE: J3.60, J4.60
PC0: J3.22, J4.22
PC1: J3.21, J4.21
PC2: J3.24, J4.24
PC3: J3.23, J4.23
PC4: J3.26, J4.26
PC5: J3.25, J4.25
PC6: J3.28, J4.28
PC7: J3.27, J4.27
PCE: J3.49, J4.49
PCL: J3.52, J4.52
RST: C3.1, J3.8, J4.8, TP6.1
SUB: J3.40, J4.40
VBUS: F1.1, J1.1
WRH: J3.57, J4.57
WRL: J3.58, J4.58
ZF: J3.37, J4.37

Notes on the sheet:
NIBBLE CARD HUB - BUS HUB: power entry, the four bus pull-ups, the eight M-line pull-downs, and a header for each face's ribbon
No logic on this card. Two 64-pin headers wired pin for pin: the top one takes one column face's ribbon, the bottom one the other's (docs/cards.md, D043). Power: 5 V from the bench supply, its banana leads into the two 4 mm sockets (D058; no USB, D057), through a 1.5 A polyfuse (D052: the machine d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
power
Decoupling
Bus pull-ups (the only ones in the machine)
M-line pull-downs (the program cards only pull high)
Test loops
fit if needed
Mounting holes
face A ribbon
face B ribbon
CROWBAR (D061): above about 6.3 to 7.8 V the zener fires the SCR, which holds the rail near 1 V until the supply is switched off; the diode takes crossed leads. Run the supply with its limit at 1.5 A: the SCR then holds a fault for as long as it takes to notice. At 3 A or more it wants a clip-on he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

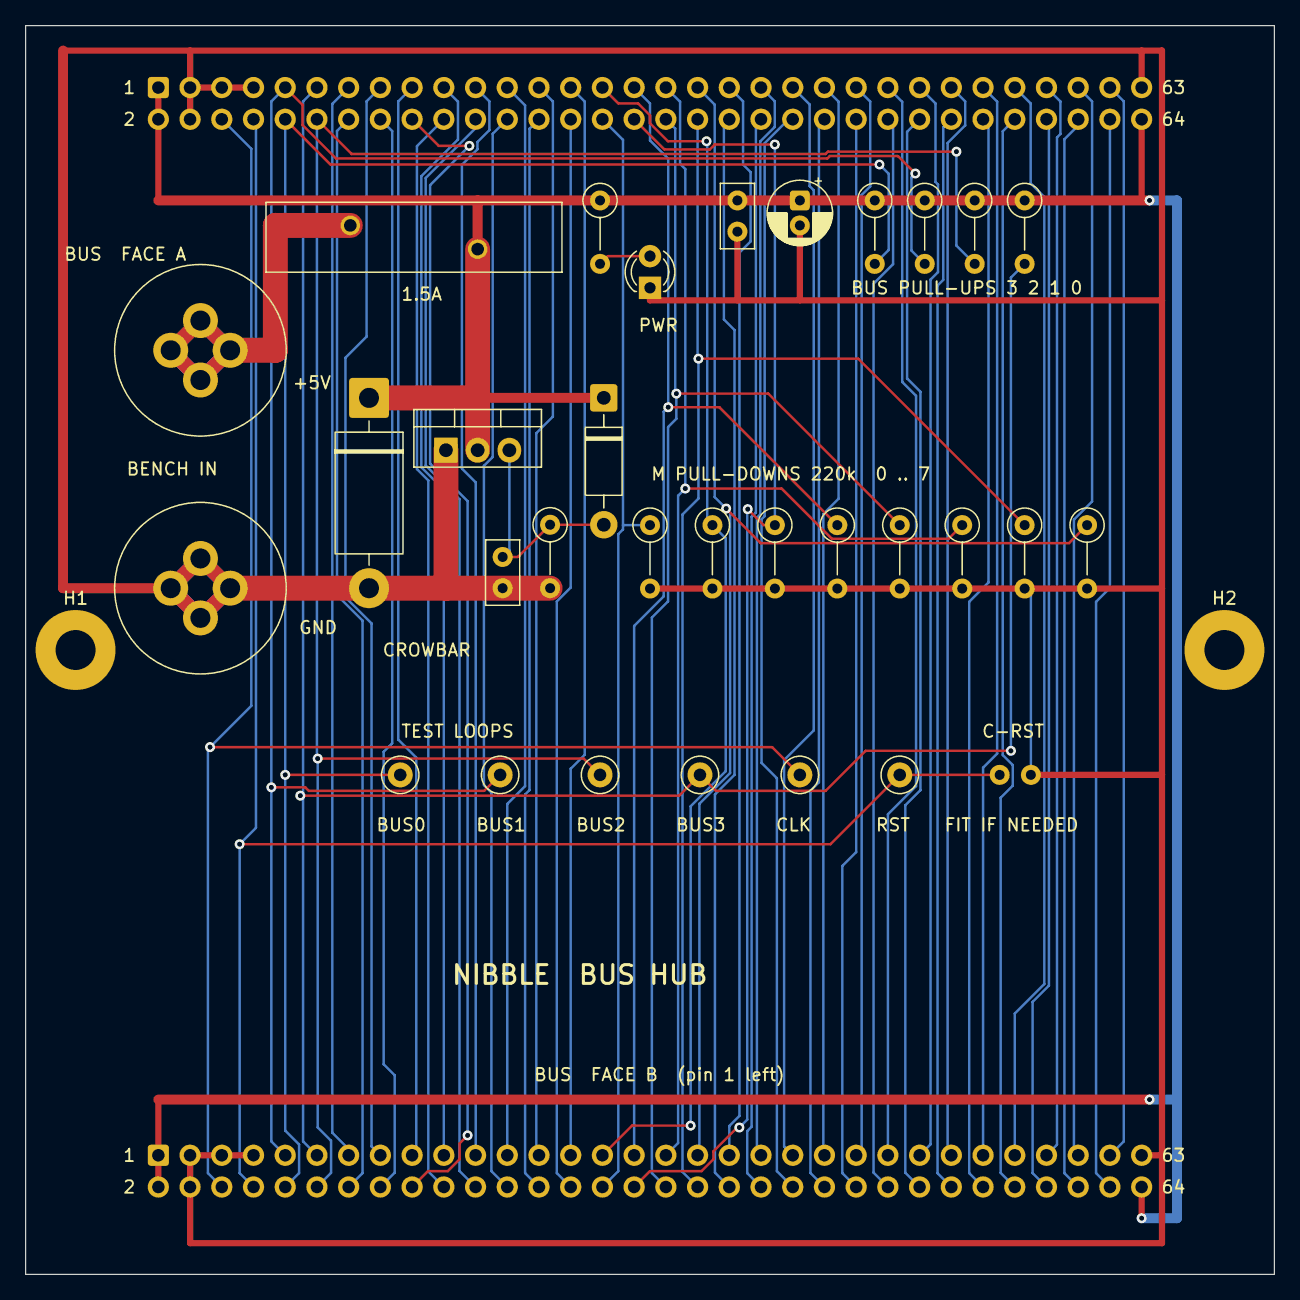
[picture p76: board cards/hub/hub.kicad_pcb from above]

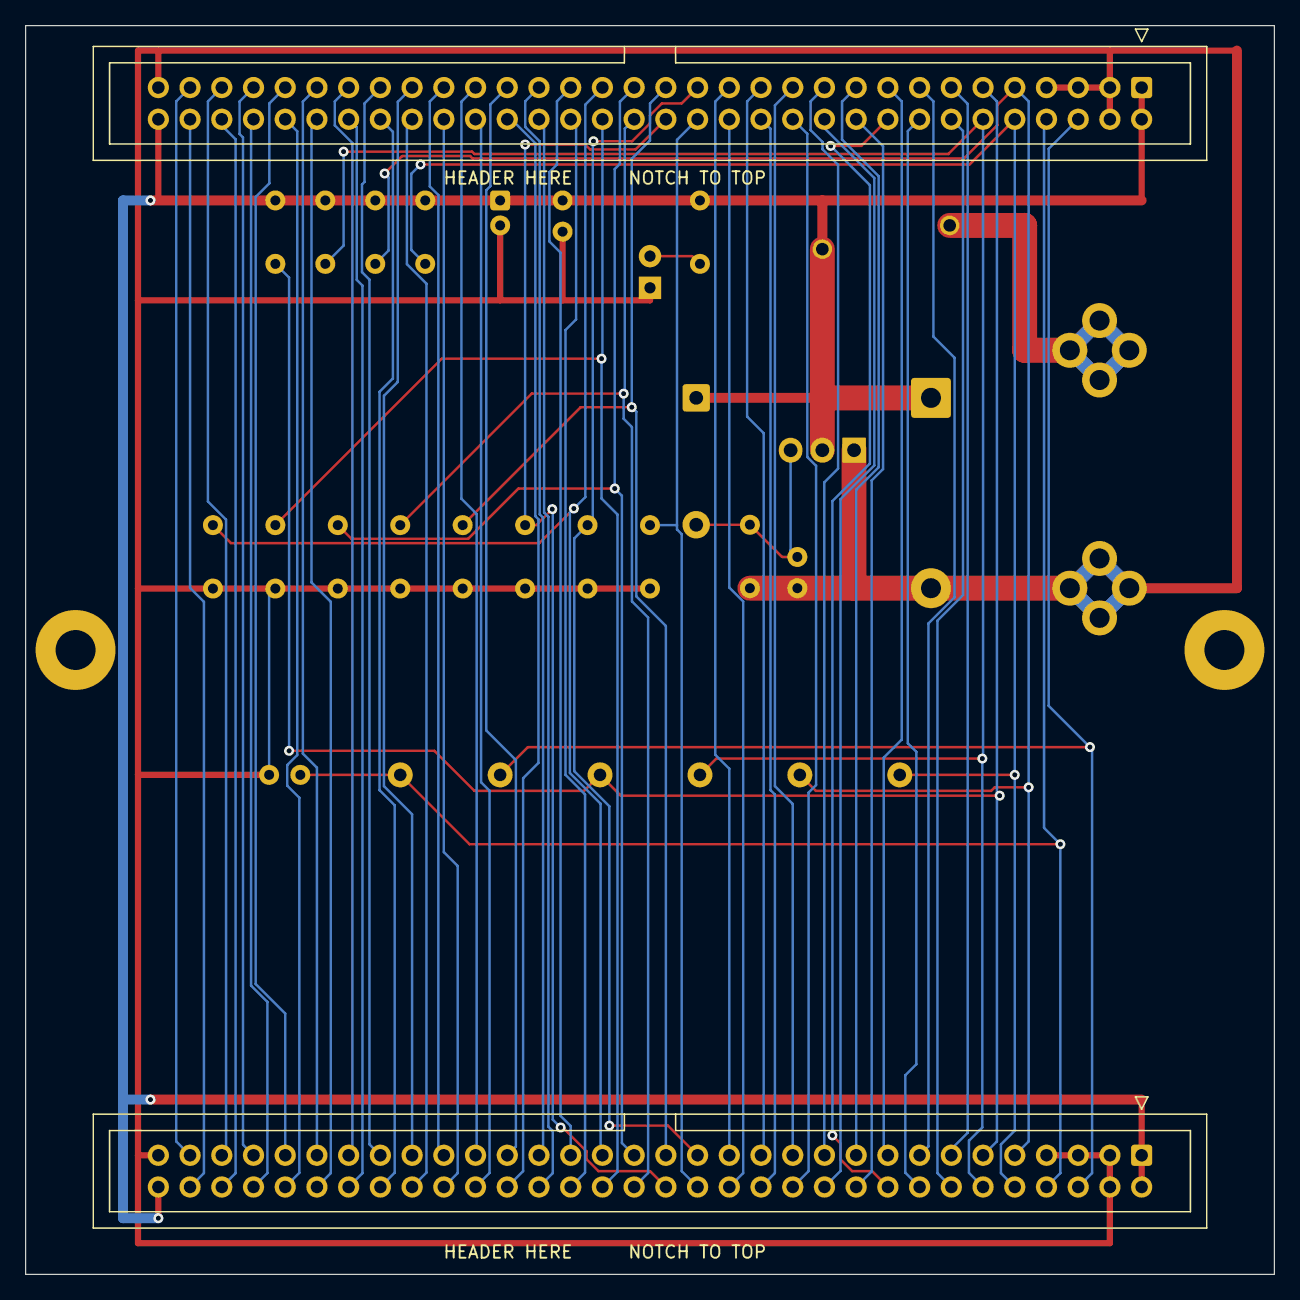
[picture p77: board cards/hub/hub.kicad_pcb from below]

Board: 2 copper layers, 100.0 x 100.0 mm, 35 parts (2 on the bottom side), 61 nets.
