nikolafilip/nibble/cards/panelb/panelb.kicad_pcb

## KiCad design cards/panelb/panelb.kicad_pcb (2026-10-01)

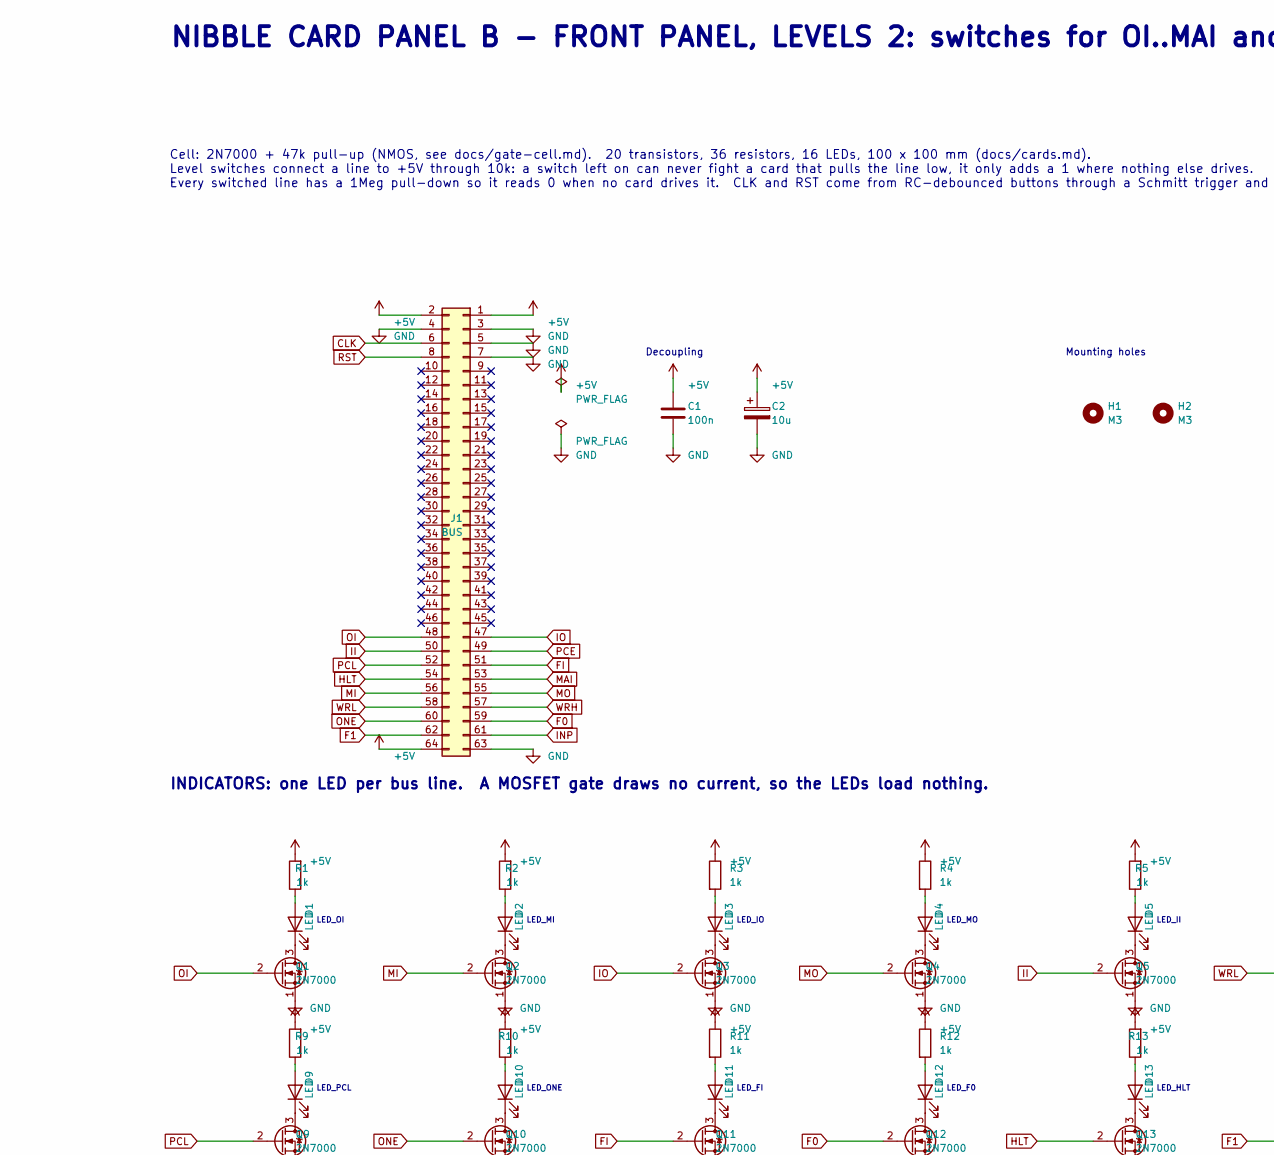
[picture p78: schematic panelb.kicad_sch, part in row 1, column 1]

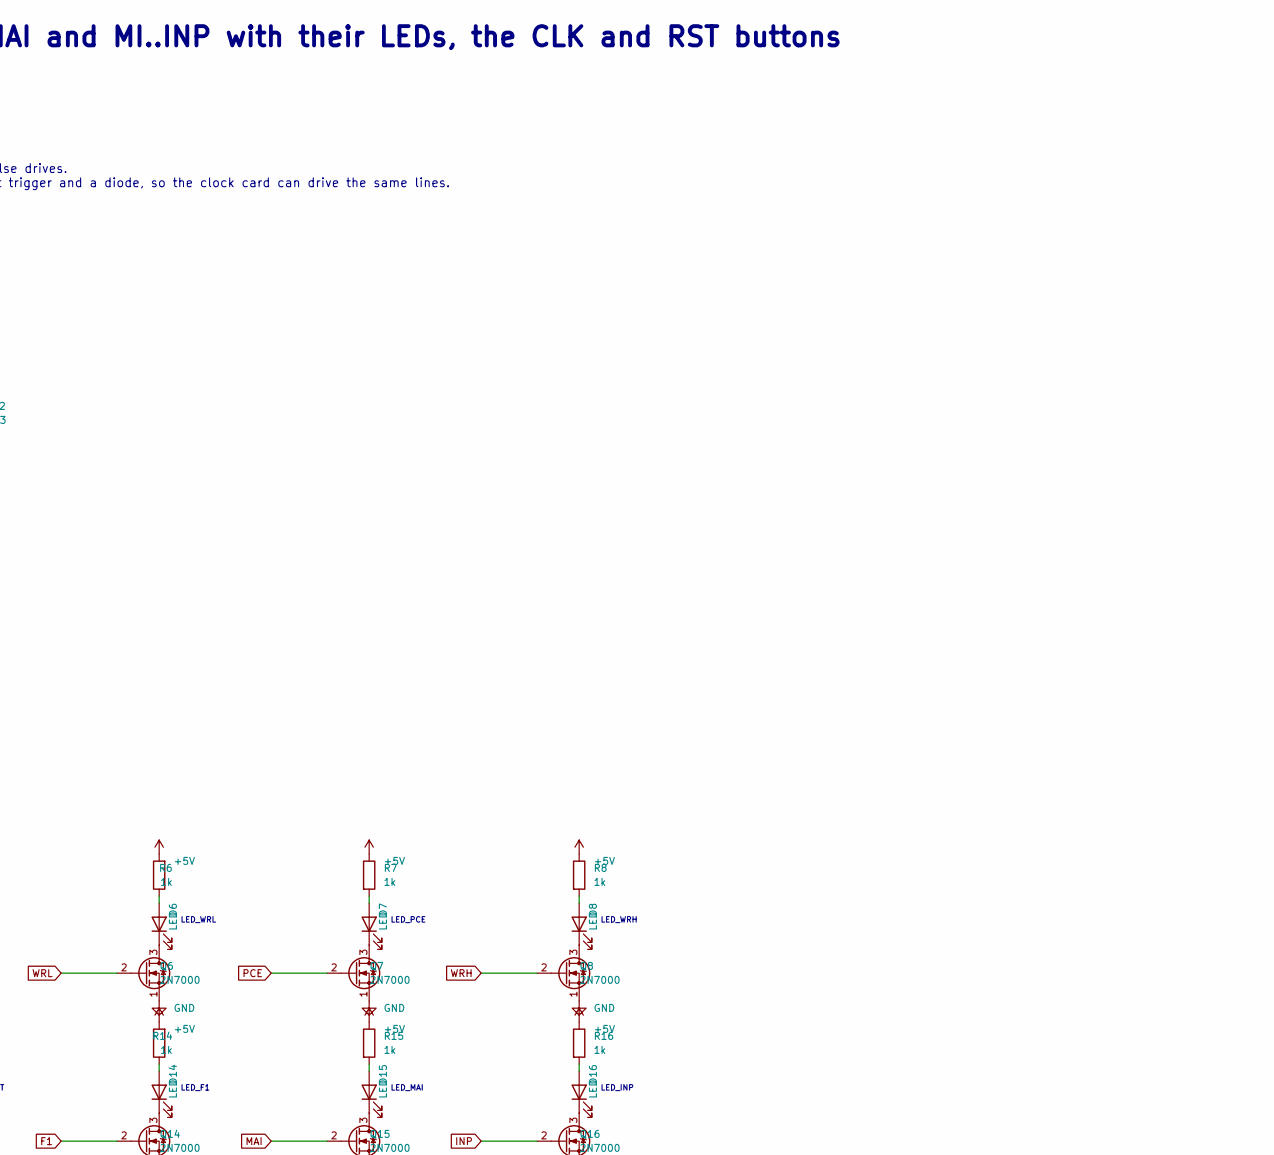
[picture p79: schematic panelb.kicad_sch, part in row 1, column 2]

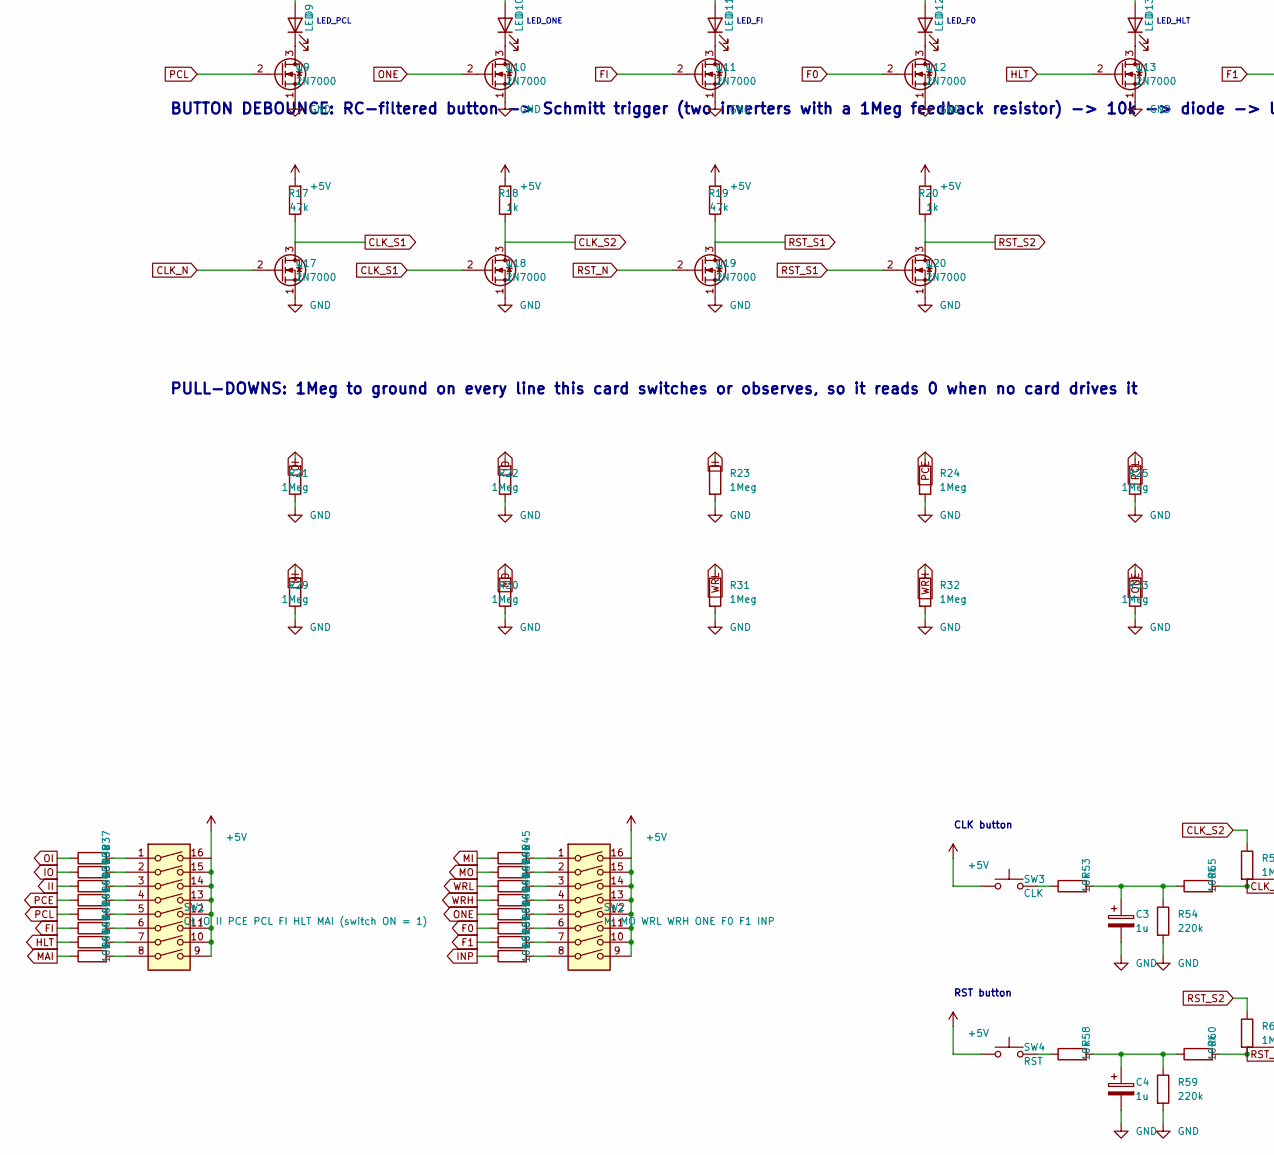
[picture p80: schematic panelb.kicad_sch, part in row 2, column 1]

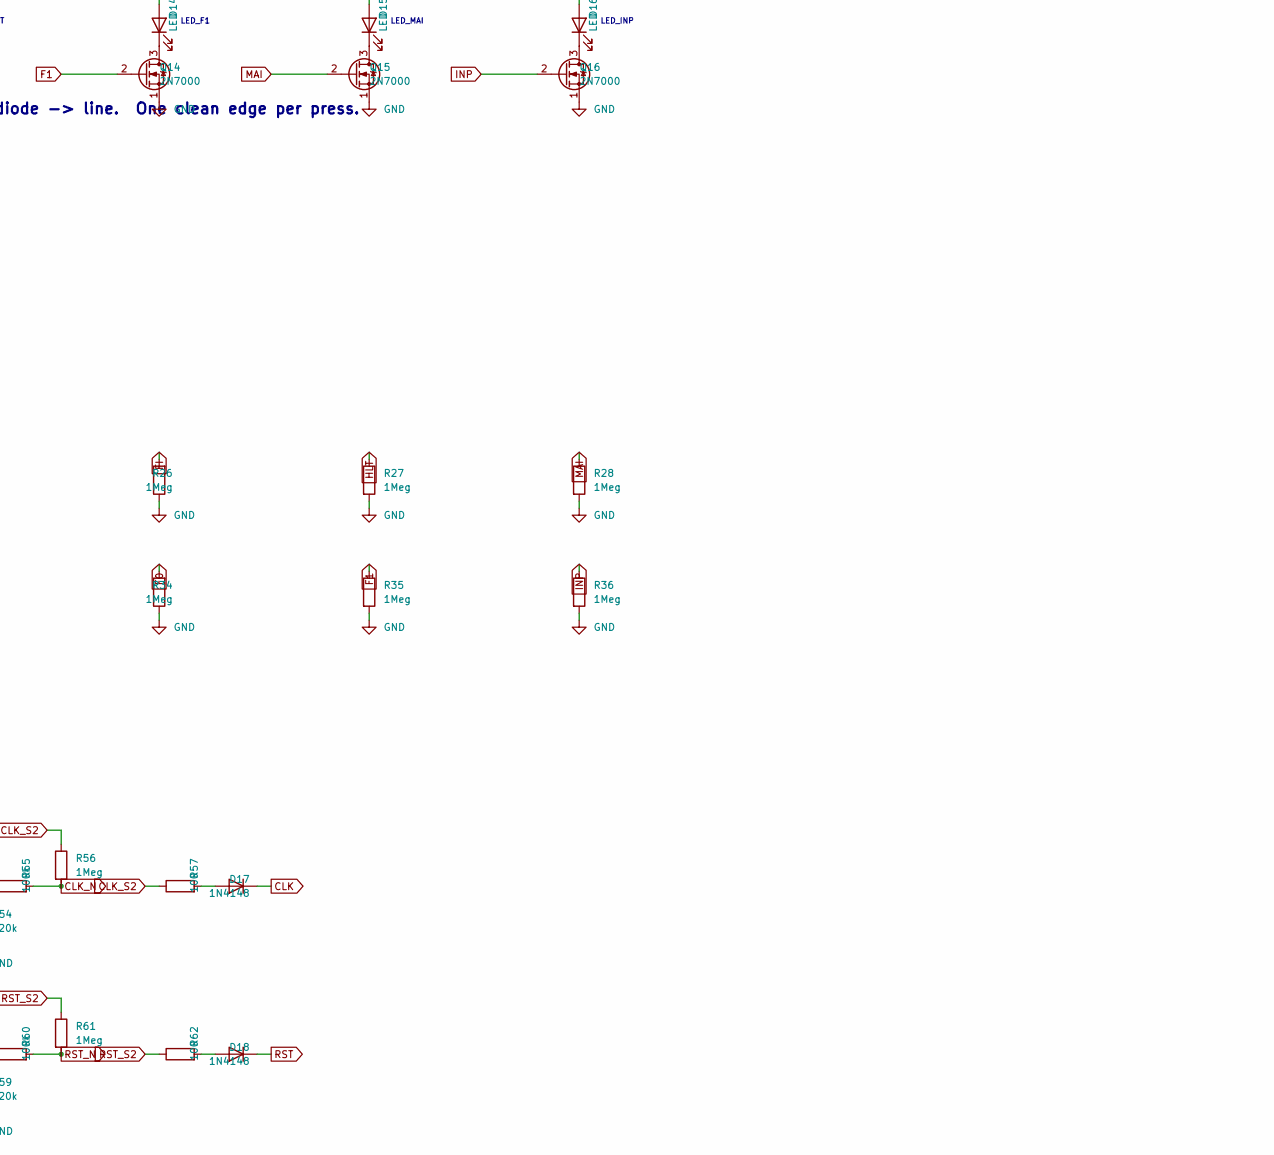
[picture p81: schematic panelb.kicad_sch, part in row 2, column 2]

Parts:
C1: 100n; C_Disc_D5.0mm_W2.5mm_P2.50mm
C2: 10u; CP_Radial_D5.0mm_P2.00mm
C3, C4: 1u; CP_Radial_D5.0mm_P2.00mm
D1, D2, D3, D4, D5, D6, D7, D8, D9, D10, D11, D12, D13, D14, D15, D16: LED; LED_D3.0mm
D17, D18: 1N4148; D_DO-35_SOD27_P7.62mm_Horizontal
H1, H2: M3; MountingHole_3.2mm_M3_Pad
J1: BUS; IDC-Header_2x32_P2.54mm_Vertical
Q1, Q2, Q3, Q4, Q5, Q6, Q7, Q8, Q9, Q10, Q11, Q12, Q13, Q14, Q15, Q16, Q17, Q18, Q19, Q20: 2N7000; TO-92_Inline_Wide
R1, R2, R3, R4, R5, R6, R7, R8, R9, R10, R11, R12, R13, R14, R15, R16, R18, R20: 1k; R_Axial_DIN0207_L6.3mm_D2.5mm_P5.08mm_Vertical
R17, R19: 47k; R_Axial_DIN0207_L6.3mm_D2.5mm_P5.08mm_Vertical
R21, R22, R23, R24, R25, R26, R27, R28, R29, R30, R31, R32, R33, R34, R35, R36, R56, R61: 1Meg; R_Axial_DIN0207_L6.3mm_D2.5mm_P5.08mm_Vertical
R37, R38, R39, R40, R41, R42, R43, R44, R45, R46, R47, R48, R49, R50, R51, R52, R53, R58: 10k; R_Axial_DIN0207_L6.3mm_D2.5mm_P5.08mm_Vertical
R54, R59: 220k; R_Axial_DIN0207_L6.3mm_D2.5mm_P5.08mm_Vertical
R55, R60: 100k; R_Axial_DIN0207_L6.3mm_D2.5mm_P5.08mm_Vertical
R57, R62: 100; R_Axial_DIN0207_L6.3mm_D2.5mm_P5.08mm_Vertical
SW1: OI IO II PCE PCL FI HLT MAI (switch ON = 1); SW_DIP_SPSTx08_Slide_9.78x22.5mm_W7.62mm_P2.54mm
SW2: MI MO WRL WRH ONE F0 F1 INP; SW_DIP_SPSTx08_Slide_9.78x22.5mm_W7.62mm_P2.54mm
SW3: CLK; SW_PUSH_6mm
SW4: RST; SW_PUSH_6mm

Connections:
+5V: C1.1, C2.1, J1.1, J1.2, J1.64, R1.2, R2.2, R3.1, R4.1, R5.2, R6.2, R7.1, R8.1, R9.2, R10.2, R11.1, R12.1, R13.2, R14.2, R15.1, R16.1, R17.2, R18.2, R19.2, R20.2, SW1.9, SW1.10, SW1.11, SW1.12, SW1.13, SW1.14, SW1.15, SW1.16, SW2.9, SW2.10, SW2.11, SW2.12, SW2.13, SW2.14, SW2.15, SW2.16, SW3.1, SW4.1
CLK: D17.1 (K), J1.6
CLK_N: Q17.2 (G), R55.2, R56.2
CLK_S1: Q17.3 (D), Q18.2 (G), R17.1
CLK_S2: Q18.3 (D), R18.1, R56.1, R57.1
F0: J1.59, Q12.2 (G), R34.2, R50.1
F1: J1.62, Q14.2 (G), R35.1, R51.1
FI: J1.51, Q11.2 (G), R26.2, R42.1
GND: C1.2, C2.2, C3.2, C4.2, J1.3, J1.4, J1.5, J1.7, J1.63, Q1.1 (S), Q2.1 (S), Q3.1 (S), Q4.1 (S), Q5.1 (S), Q6.1 (S), Q7.1 (S), Q8.1 (S), Q9.1 (S), Q10.1 (S), Q11.1 (S), Q12.1 (S), Q13.1 (S), Q14.1 (S), Q15.1 (S), Q16.1 (S), Q17.1 (S), Q18.1 (S), Q19.1 (S), Q20.1 (S), R21.1, R22.1, R23.2, R24.2, R25.1, R26.1, R27.2, R28.2, R29.1, R30.1, R31.2, R32.2, R33.1, R34.1, R35.2, R36.2, R54.2, R59.2
HLT: J1.54, Q13.2 (G), R27.1, R43.1
II: J1.50, Q5.2 (G), R23.1, R39.1
INP: J1.61, Q16.2 (G), R36.1, R52.1
IO: J1.47, Q3.2 (G), R22.2, R38.1
MAI: J1.53, Q15.2 (G), R28.1, R44.1
MI: J1.56, Q2.2 (G), R29.2, R45.1
MO: J1.55, Q4.2 (G), R30.2, R46.1
unnamed: C3.1, R53.2, R54.1, R55.1
unnamed: C4.1, R58.2, R59.1, R60.1
unnamed: D1.2 (A), R1.1
unnamed: D1.1 (K), Q1.3 (D)
unnamed: D2.2 (A), R2.1
unnamed: D2.1 (K), Q2.3 (D)
unnamed: D3.2 (A), R3.2
unnamed: D3.1 (K), Q3.3 (D)
unnamed: D4.2 (A), R4.2
unnamed: D4.1 (K), Q4.3 (D)
unnamed: D5.2 (A), R5.1
unnamed: D5.1 (K), Q5.3 (D)
unnamed: D6.2 (A), R6.1
unnamed: D6.1 (K), Q6.3 (D)
unnamed: D7.2 (A), R7.2
unnamed: D7.1 (K), Q7.3 (D)
unnamed: D8.2 (A), R8.2
unnamed: D8.1 (K), Q8.3 (D)
unnamed: D9.2 (A), R9.1
unnamed: D9.1 (K), Q9.3 (D)
unnamed: D10.2 (A), R10.1
unnamed: D10.1 (K), Q10.3 (D)
unnamed: D11.2 (A), R11.2
unnamed: D11.1 (K), Q11.3 (D)
unnamed: D12.2 (A), R12.2
unnamed: D12.1 (K), Q12.3 (D)
unnamed: D13.2 (A), R13.1
unnamed: D13.1 (K), Q13.3 (D)
unnamed: D14.2 (A), R14.1
unnamed: D14.1 (K), Q14.3 (D)
unnamed: D15.2 (A), R15.2
unnamed: D15.1 (K), Q15.3 (D)
unnamed: D16.2 (A), R16.2
unnamed: D16.1 (K), Q16.3 (D)
unnamed: D17.2 (A), R57.2
unnamed: D18.2 (A), R62.2
unnamed: R37.2, SW1.1
unnamed: R38.2, SW1.2
unnamed: R39.2, SW1.3
unnamed: R40.2, SW1.4
unnamed: R41.2, SW1.5
unnamed: R42.2, SW1.6
unnamed: R43.2, SW1.7
unnamed: R44.2, SW1.8
unnamed: R45.2, SW2.1
unnamed: R46.2, SW2.2
unnamed: R47.2, SW2.3
unnamed: R48.2, SW2.4
unnamed: R49.2, SW2.5
unnamed: R50.2, SW2.6
unnamed: R51.2, SW2.7
unnamed: R52.2, SW2.8
unnamed: R53.1, SW3.2
unnamed: R58.1, SW4.2
OI: J1.48, Q1.2 (G), R21.2, R37.1
ONE: J1.60, Q10.2 (G), R33.2, R49.1
PCE: J1.49, Q7.2 (G), R24.1, R40.1
PCL: J1.52, Q9.2 (G), R25.2, R41.1
RST: D18.1 (K), J1.8
RST_N: Q19.2 (G), R60.2, R61.2
RST_S1: Q19.3 (D), Q20.2 (G), R19.1
RST_S2: Q20.3 (D), R20.1, R61.1, R62.1
WRH: J1.57, Q8.2 (G), R32.1, R48.1
WRL: J1.58, Q6.2 (G), R31.1, R47.1

Notes on the sheet:
NIBBLE CARD PANEL B - FRONT PANEL, LEVELS 2: switches for OI..MAI and MI..INP with their LEDs, the CLK and RST buttons
Cell: 2N7000 + 47k pull-up (NMOS, see docs/gate-cell.md). 20 transistors, 36 resistors, 16 LEDs, 100 x 100 mm (docs/cards.md). Level switches connect a line to +5V through 10k: a switch left on can never fight a card that pulls the line low, it only adds a 1 where nothing else drives. Every switche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
INDICATORS: one LED per bus line. A MOSFET gate draws no current, so the LEDs load nothing.
LED_OI
LED_MI
LED_IO
LED_MO
LED_II
LED_WRL
LED_PCE
LED_WRH
LED_PCL
LED_ONE
LED_FI
LED_F0
LED_HLT
LED_F1
LED_MAI
LED_INP
BUTTON DEBOUNCE: RC-filtered button -> Schmitt trigger (two inverters with a 1Meg feedback resistor) -> 10k -> diode -> line. One clean edge per press.
PULL-DOWNS: 1Meg to ground on every line this card switches or observes, so it reads 0 when no card drives it
Decoupling
Mounting holes
CLK button
RST button

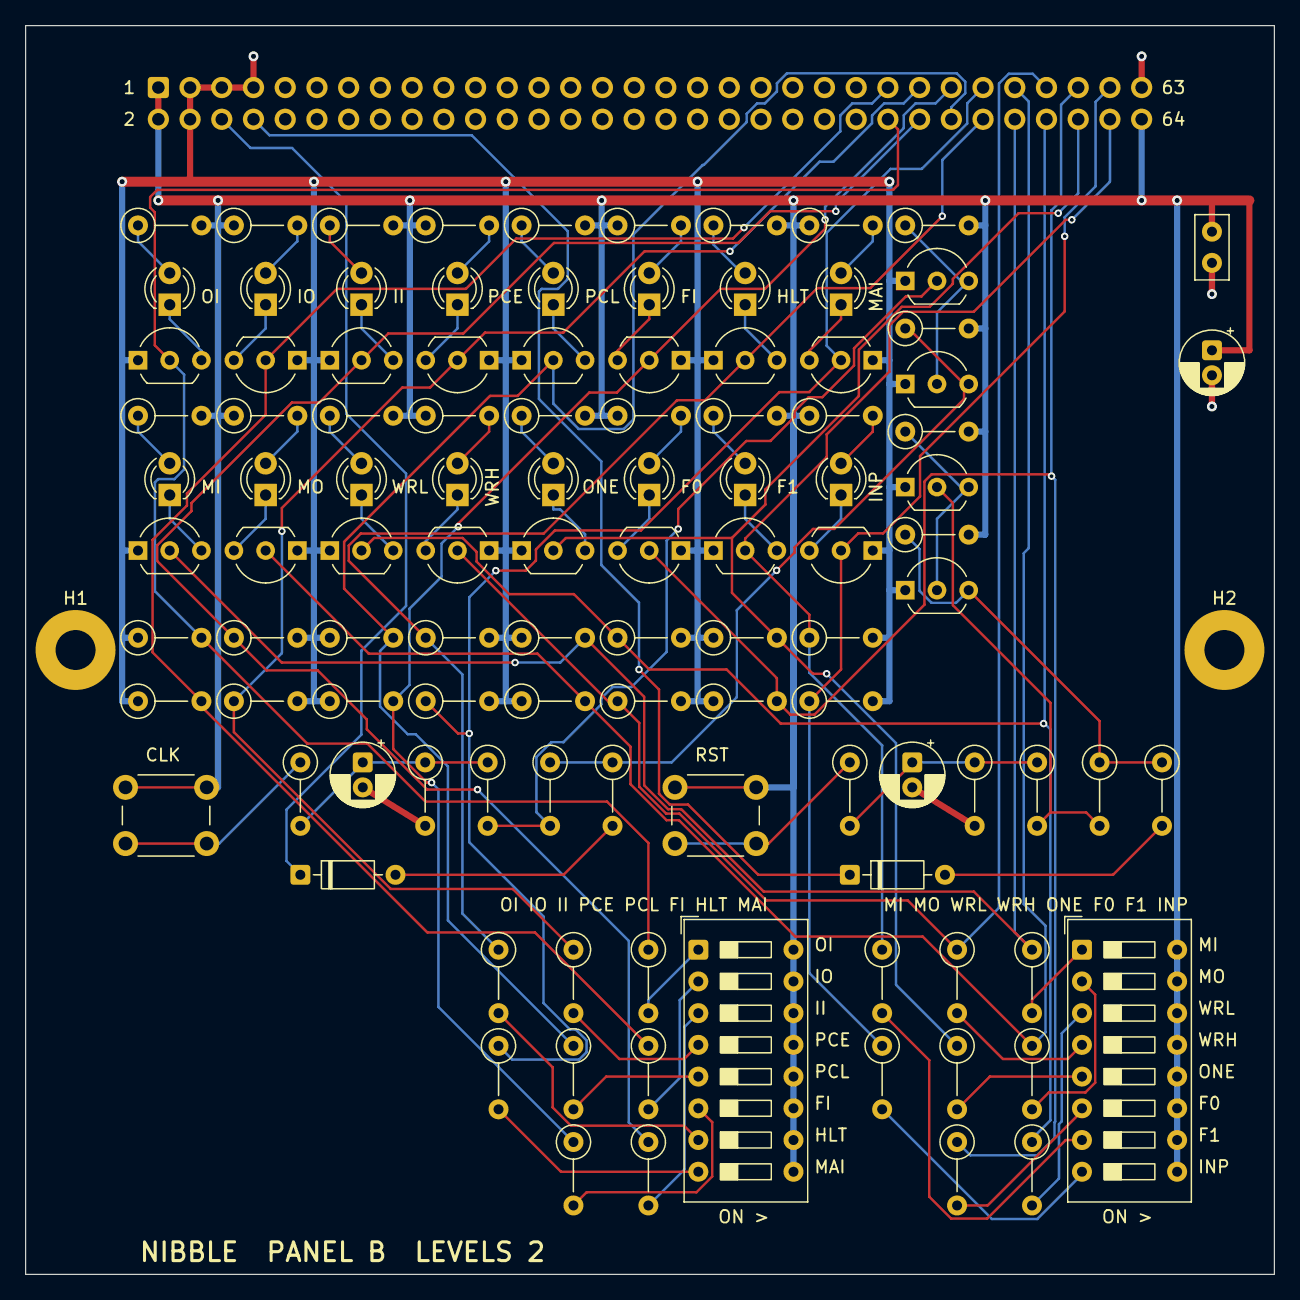
[picture p82: board panelb.kicad_pcb from above]

Board: 2 copper layers, 100.0 x 100.0 mm, 111 parts (1 on the bottom side), 80 nets.
