nikolafilip/nibble/cards/memslot/memslot.kicad_pcb

## KiCad design cards/memslot/memslot.kicad_pcb (2026-10-01)

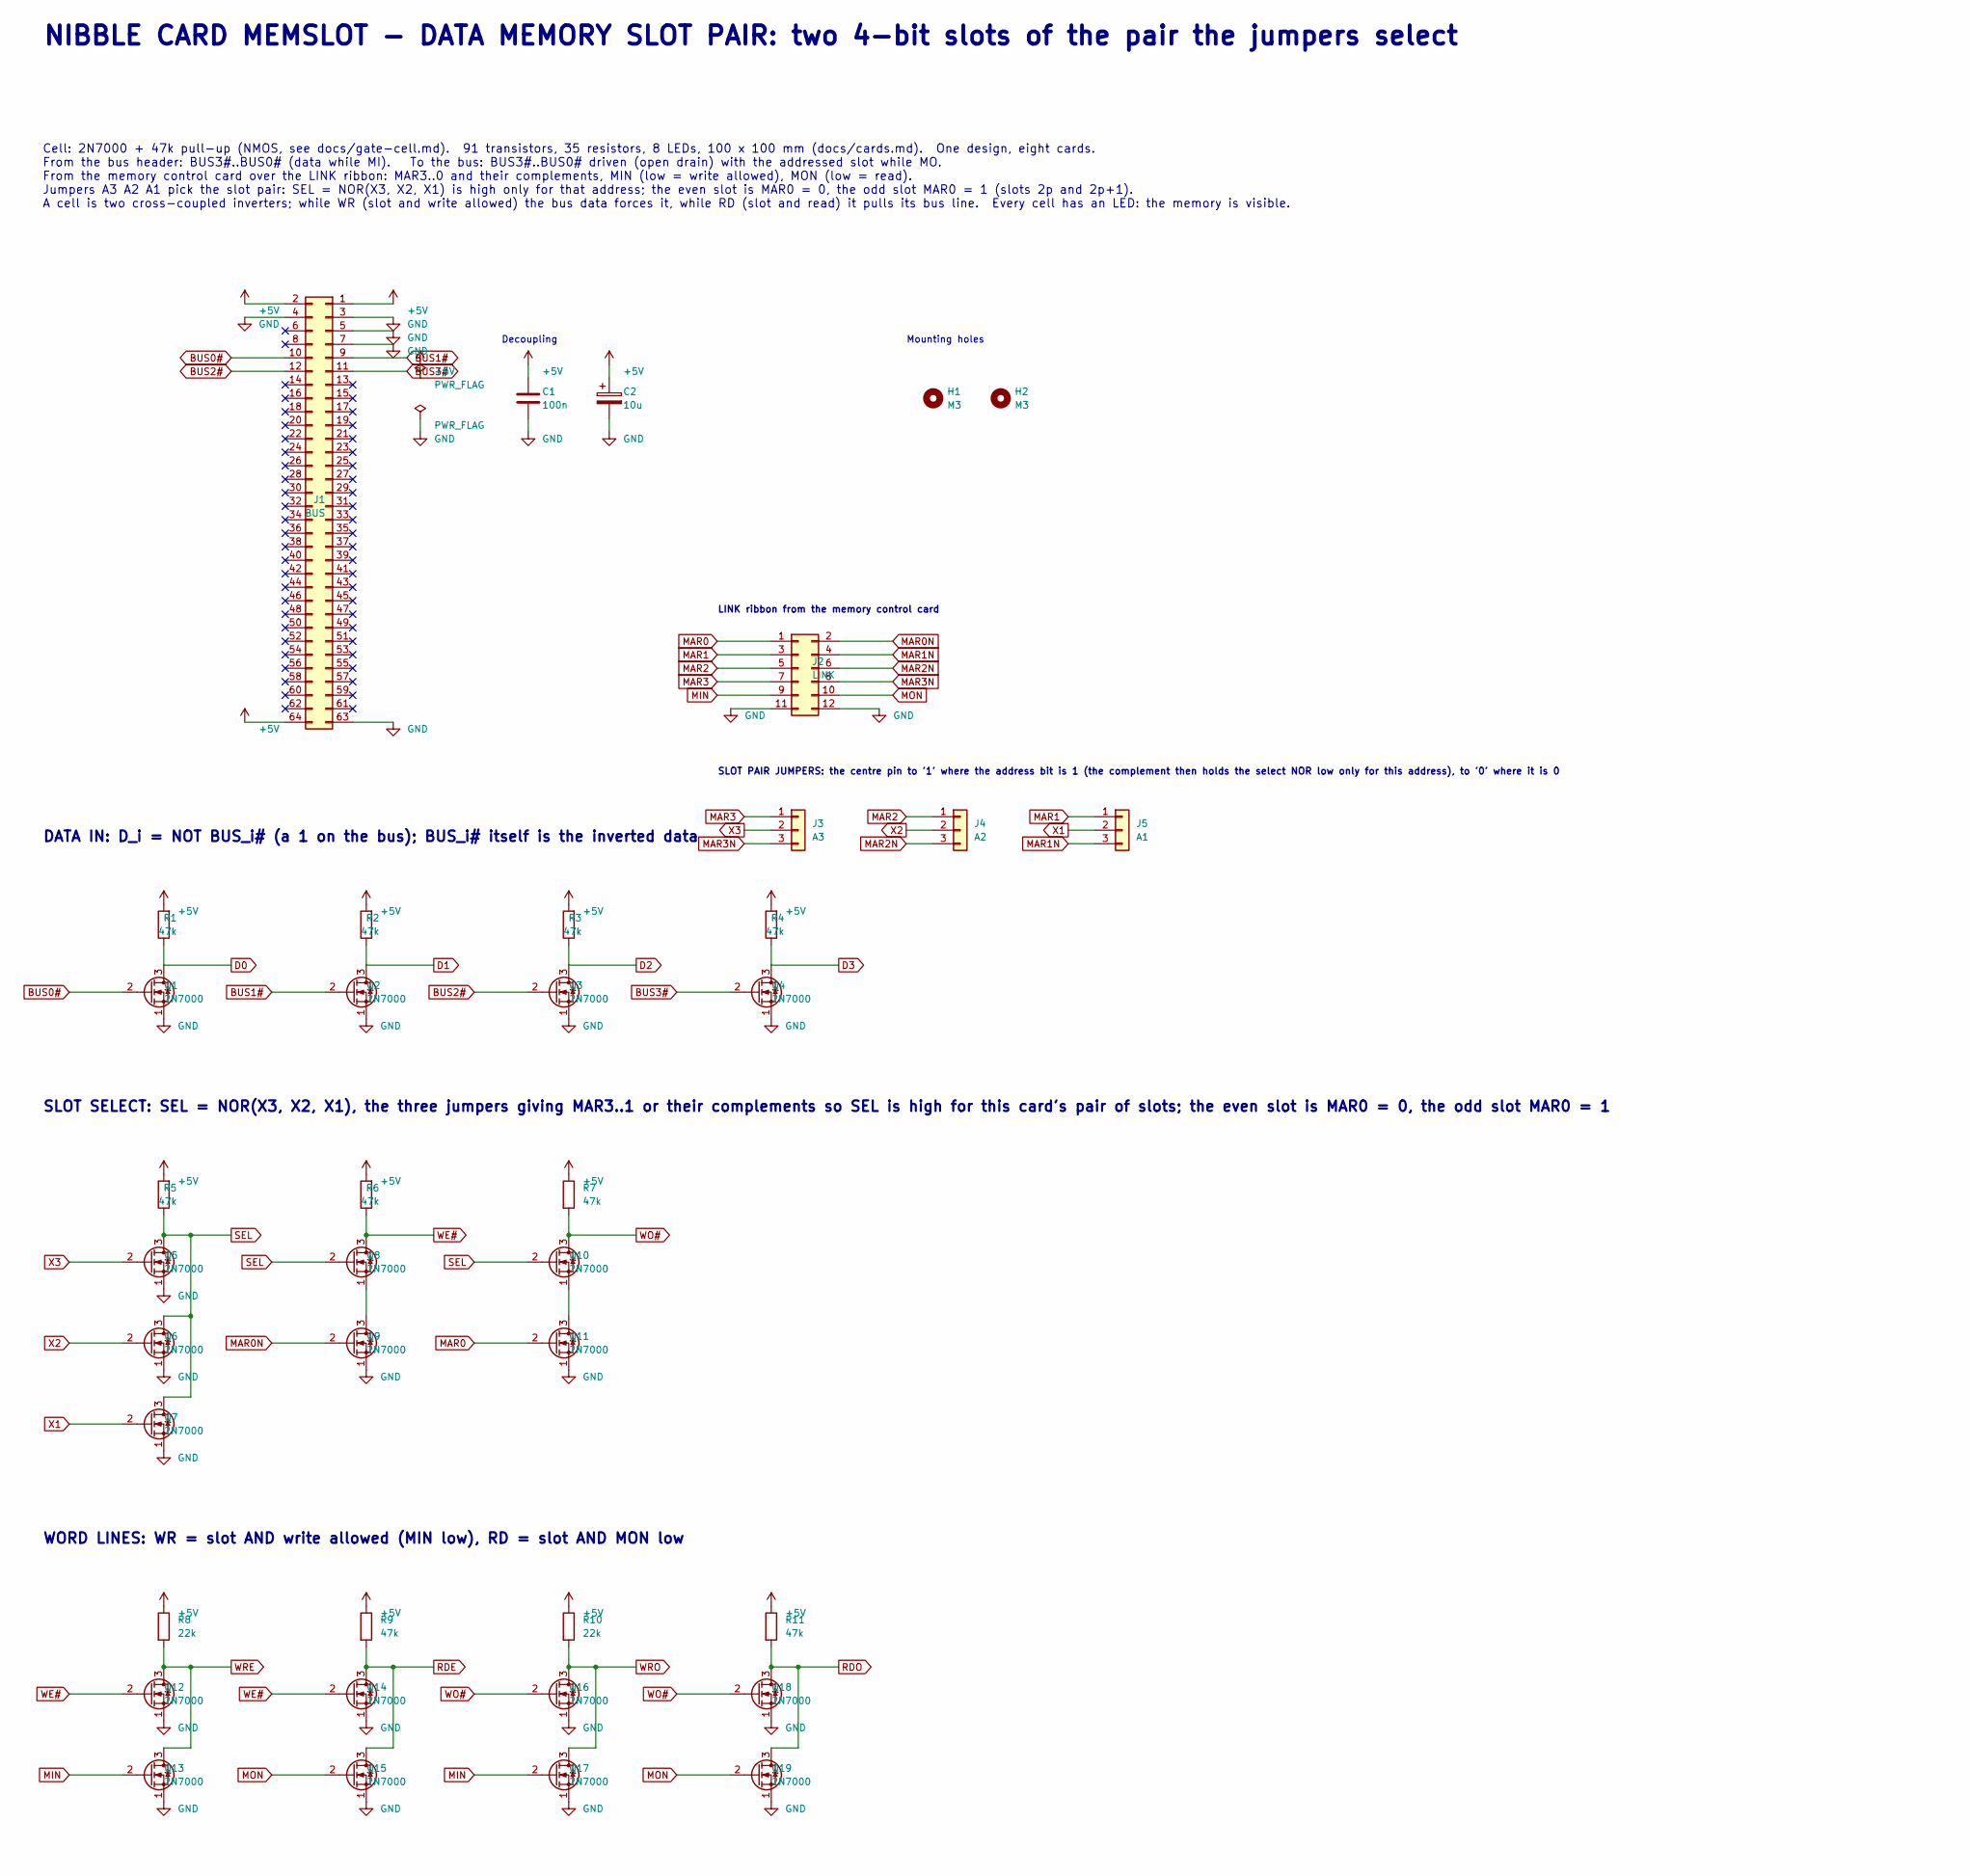
[picture p83: schematic memslot.kicad_sch, part in row 1, column 1]

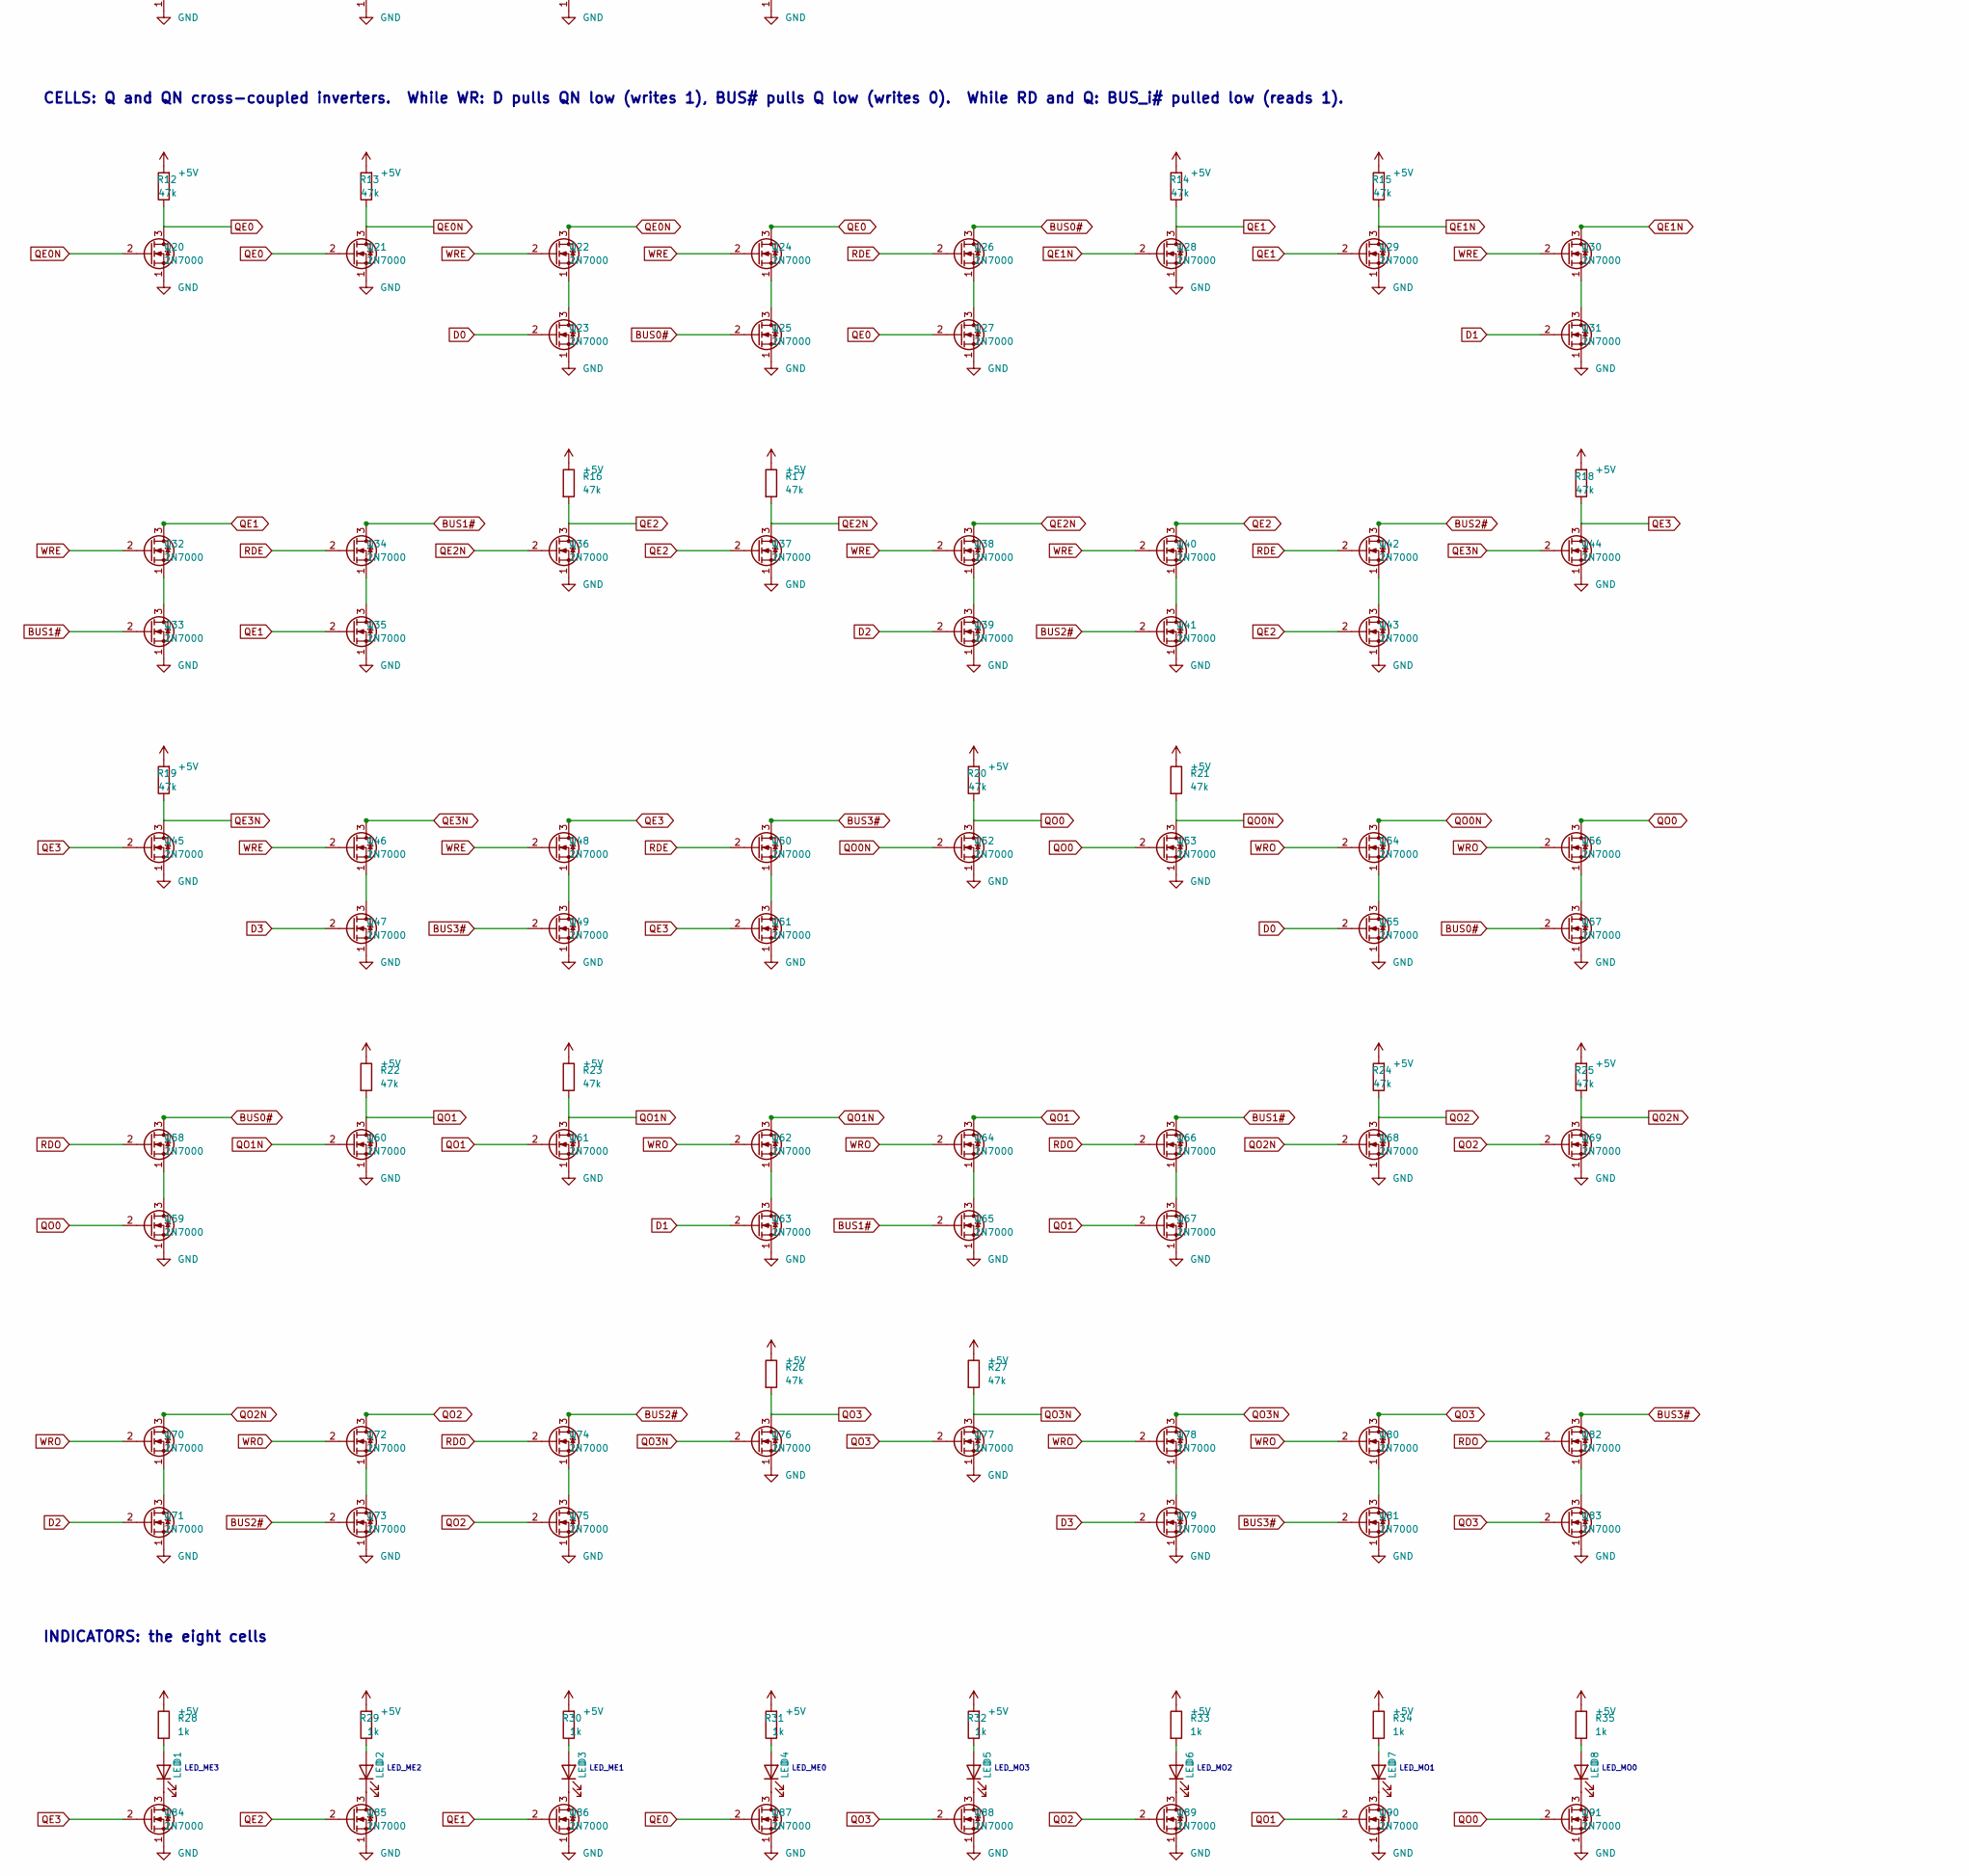
[picture p84: schematic memslot.kicad_sch, part in row 2, column 1]

Parts:
C1: 100n; C_Disc_D5.0mm_W2.5mm_P2.50mm
C2: 10u; CP_Radial_D5.0mm_P2.00mm
D1, D2, D3, D4, D5, D6, D7, D8: LED; LED_D3.0mm
H1, H2: M3; MountingHole_3.2mm_M3_Pad
J1: BUS; IDC-Header_2x32_P2.54mm_Vertical
J2: LINK; IDC-Header_2x06_P2.54mm_Vertical
J3: A3; PinHeader_1x03_P2.54mm_Vertical
J4: A2; PinHeader_1x03_P2.54mm_Vertical
J5: A1; PinHeader_1x03_P2.54mm_Vertical
Q1, Q2, Q3, Q4, Q5, Q6, Q7, Q8, Q9, Q10, Q11, Q12, Q13, Q14, Q15, Q16, Q17, Q18, Q19, Q20, Q21, Q22, Q23, Q24, Q25, Q26, Q27, Q28, Q29, Q30, Q31, Q32, Q33, Q34, Q35, Q36, Q37, Q38, Q39, Q40, Q41, Q42, Q43, Q44, Q45, Q46, Q47, Q48, Q49, Q50, Q51, Q52, Q53, Q54, Q55, Q56, Q57, Q58, Q59, Q60, Q61, Q62, Q63, Q64, Q65, Q66, Q67, Q68, Q69, Q70, Q71, Q72, Q73, Q74, Q75, Q76, Q77, Q78, Q79, Q80, Q81, Q82, Q83, Q84, Q85, Q86, Q87, Q88, Q89, Q90, Q91: 2N7000; TO-92_Inline_Wide
R1, R2, R3, R4, R5, R6, R7, R9, R11, R12, R13, R14, R15, R16, R17, R18, R19, R20, R21, R22, R23, R24, R25, R26, R27: 47k; R_Axial_DIN0207_L6.3mm_D2.5mm_P5.08mm_Vertical
R8, R10: 22k; R_Axial_DIN0207_L6.3mm_D2.5mm_P5.08mm_Vertical
R28, R29, R30, R31, R32, R33, R34, R35: 1k; R_Axial_DIN0207_L6.3mm_D2.5mm_P5.08mm_Vertical

Connections:
+5V: C1.1, C2.1, J1.1, J1.2, J1.64, R1.2, R2.2, R3.2, R4.2, R5.2, R6.2, R7.1, R8.1, R9.1, R10.1, R11.1, R12.2, R13.2, R14.2, R15.2, R16.1, R17.1, R18.2, R19.2, R20.2, R21.1, R22.1, R23.1, R24.2, R25.2, R26.1, R27.1, R28.1, R29.2, R30.2, R31.2, R32.2, R33.1, R34.1, R35.1
BUS0#: J1.10, Q1.2 (G), Q25.2 (G), Q26.3 (D), Q57.2 (G), Q58.3 (D)
BUS1#: J1.9, Q2.2 (G), Q33.2 (G), Q34.3 (D), Q65.2 (G), Q66.3 (D)
BUS2#: J1.12, Q3.2 (G), Q41.2 (G), Q42.3 (D), Q73.2 (G), Q74.3 (D)
BUS3#: J1.11, Q4.2 (G), Q49.2 (G), Q50.3 (D), Q81.2 (G), Q82.3 (D)
D0: Q1.3 (D), Q23.2 (G), Q55.2 (G), R1.1
D1: Q2.3 (D), Q31.2 (G), Q63.2 (G), R2.1
D2: Q3.3 (D), Q39.2 (G), Q71.2 (G), R3.1
D3: Q4.3 (D), Q47.2 (G), Q79.2 (G), R4.1
GND: C1.2, C2.2, J1.3, J1.4, J1.5, J1.7, J1.63, J2.11, J2.12, Q1.1 (S), Q2.1 (S), Q3.1 (S), Q4.1 (S), Q5.1 (S), Q6.1 (S), Q7.1 (S), Q9.1 (S), Q11.1 (S), Q12.1 (S), Q13.1 (S), Q14.1 (S), Q15.1 (S), Q16.1 (S), Q17.1 (S), Q18.1 (S), Q19.1 (S), Q20.1 (S), Q21.1 (S), Q23.1 (S), Q25.1 (S), Q27.1 (S), Q28.1 (S), Q29.1 (S), Q31.1 (S), Q33.1 (S), Q35.1 (S), Q36.1 (S), Q37.1 (S), Q39.1 (S), Q41.1 (S), Q43.1 (S), Q44.1 (S), Q45.1 (S), Q47.1 (S), Q49.1 (S), Q51.1 (S), Q52.1 (S), Q53.1 (S), Q55.1 (S), Q57.1 (S), Q59.1 (S), Q60.1 (S), Q61.1 (S), Q63.1 (S), Q65.1 (S), Q67.1 (S), Q68.1 (S), Q69.1 (S), Q71.1 (S), Q73.1 (S), Q75.1 (S), Q76.1 (S), Q77.1 (S), Q79.1 (S), Q81.1 (S), Q83.1 (S), Q84.1 (S), Q85.1 (S), Q86.1 (S), Q87.1 (S), Q88.1 (S), Q89.1 (S), Q90.1 (S), Q91.1 (S)
MAR0: J2.1, Q11.2 (G)
MAR0N: J2.2, Q9.2 (G)
MAR1: J2.3, J5.1
MAR1N: J2.4, J5.3
MAR2: J2.5, J4.1
MAR2N: J2.6, J4.3
MAR3: J2.7, J3.1
MAR3N: J2.8, J3.3
MIN: J2.9, Q13.2 (G), Q17.2 (G)
MON: J2.10, Q15.2 (G), Q19.2 (G)
unnamed: D1.2 (A), R28.2
unnamed: D1.1 (K), Q84.3 (D)
unnamed: D2.2 (A), R29.1
unnamed: D2.1 (K), Q85.3 (D)
unnamed: D3.2 (A), R30.1
unnamed: D3.1 (K), Q86.3 (D)
unnamed: D4.2 (A), R31.1
unnamed: D4.1 (K), Q87.3 (D)
unnamed: D5.2 (A), R32.1
unnamed: D5.1 (K), Q88.3 (D)
unnamed: D6.2 (A), R33.2
unnamed: D6.1 (K), Q89.3 (D)
unnamed: D7.2 (A), R34.2
unnamed: D7.1 (K), Q90.3 (D)
unnamed: D8.2 (A), R35.2
unnamed: D8.1 (K), Q91.3 (D)
unnamed: Q8.1 (S), Q9.3 (D)
unnamed: Q10.1 (S), Q11.3 (D)
unnamed: Q22.1 (S), Q23.3 (D)
unnamed: Q24.1 (S), Q25.3 (D)
unnamed: Q26.1 (S), Q27.3 (D)
unnamed: Q30.1 (S), Q31.3 (D)
unnamed: Q32.1 (S), Q33.3 (D)
unnamed: Q34.1 (S), Q35.3 (D)
unnamed: Q38.1 (S), Q39.3 (D)
unnamed: Q40.1 (S), Q41.3 (D)
unnamed: Q42.1 (S), Q43.3 (D)
unnamed: Q46.1 (S), Q47.3 (D)
unnamed: Q48.1 (S), Q49.3 (D)
unnamed: Q50.1 (S), Q51.3 (D)
unnamed: Q54.1 (S), Q55.3 (D)
unnamed: Q56.1 (S), Q57.3 (D)
unnamed: Q58.1 (S), Q59.3 (D)
unnamed: Q62.1 (S), Q63.3 (D)
unnamed: Q64.1 (S), Q65.3 (D)
unnamed: Q66.1 (S), Q67.3 (D)
unnamed: Q70.1 (S), Q71.3 (D)
unnamed: Q72.1 (S), Q73.3 (D)
unnamed: Q74.1 (S), Q75.3 (D)
unnamed: Q78.1 (S), Q79.3 (D)
unnamed: Q80.1 (S), Q81.3 (D)
unnamed: Q82.1 (S), Q83.3 (D)
QE0: Q20.3 (D), Q21.2 (G), Q24.3 (D), Q27.2 (G), Q87.2 (G), R12.1
QE0N: Q20.2 (G), Q21.3 (D), Q22.3 (D), R13.1
QE1: Q28.3 (D), Q29.2 (G), Q32.3 (D), Q35.2 (G), Q86.2 (G), R14.1
QE1N: Q28.2 (G), Q29.3 (D), Q30.3 (D), R15.1
QE2: Q36.3 (D), Q37.2 (G), Q40.3 (D), Q43.2 (G), Q85.2 (G), R16.2
QE2N: Q36.2 (G), Q37.3 (D), Q38.3 (D), R17.2
QE3: Q44.3 (D), Q45.2 (G), Q48.3 (D), Q51.2 (G), Q84.2 (G), R18.1
QE3N: Q44.2 (G), Q45.3 (D), Q46.3 (D), R19.1
QO0: Q52.3 (D), Q53.2 (G), Q56.3 (D), Q59.2 (G), Q91.2 (G), R20.1
QO0N: Q52.2 (G), Q53.3 (D), Q54.3 (D), R21.2
QO1: Q60.3 (D), Q61.2 (G), Q64.3 (D), Q67.2 (G), Q90.2 (G), R22.2
QO1N: Q60.2 (G), Q61.3 (D), Q62.3 (D), R23.2
QO2: Q68.3 (D), Q69.2 (G), Q72.3 (D), Q75.2 (G), Q89.2 (G), R24.1
QO2N: Q68.2 (G), Q69.3 (D), Q70.3 (D), R25.1
QO3: Q76.3 (D), Q77.2 (G), Q80.3 (D), Q83.2 (G), Q88.2 (G), R26.2
QO3N: Q76.2 (G), Q77.3 (D), Q78.3 (D), R27.2
RDE: Q14.3 (D), Q15.3 (D), Q26.2 (G), Q34.2 (G), Q42.2 (G), Q50.2 (G), R9.2
RDO: Q18.3 (D), Q19.3 (D), Q58.2 (G), Q66.2 (G), Q74.2 (G), Q82.2 (G), R11.2
SEL: Q5.3 (D), Q6.3 (D), Q7.3 (D), Q8.2 (G), Q10.2 (G), R5.1
WE#: Q8.3 (D), Q12.2 (G), Q14.2 (G), R6.1
WO#: Q10.3 (D), Q16.2 (G), Q18.2 (G), R7.2
WRE: Q12.3 (D), Q13.3 (D), Q22.2 (G), Q24.2 (G), Q30.2 (G), Q32.2 (G), Q38.2 (G), Q40.2 (G), Q46.2 (G), Q48.2 (G), R8.2
WRO: Q16.3 (D), Q17.3 (D), Q54.2 (G), Q56.2 (G), Q62.2 (G), Q64.2 (G), Q70.2 (G), Q72.2 (G), Q78.2 (G), Q80.2 (G), R10.2
X1: J5.2, Q7.2 (G)
X2: J4.2, Q6.2 (G)
X3: J3.2, Q5.2 (G)

Notes on the sheet:
NIBBLE CARD MEMSLOT - DATA MEMORY SLOT PAIR: two 4-bit slots of the pair the jumpers select
Cell: 2N7000 + 47k pull-up (NMOS, see docs/gate-cell.md). 91 transistors, 35 resistors, 8 LEDs, 100 x 100 mm (docs/cards.md). One design, eight cards. From the bus header: BUS3#..BUS0# (data while MI). To the bus: BUS3#..BUS0# driven (open drain) with the addressed slot while MO. From the memory co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
DATA IN: D_i = NOT BUS_i# (a 1 on the bus); BUS_i# itself is the inverted data
SLOT SELECT: SEL = NOR(X3, X2, X1), the three jumpers giving MAR3..1 or their complements so SEL is high for this card's pair of slots; the even slot is MAR0 = 0, the odd slot MAR0 = 1
WORD LINES: WR = slot AND write allowed (MIN low), RD = slot AND MON low
CELLS: Q and QN cross-coupled inverters. While WR: D pulls QN low (writes 1), BUS# pulls Q low (writes 0). While RD and Q: BUS_i# pulled low (reads 1).
INDICATORS: the eight cells
LED_ME3
LED_ME2
LED_ME1
LED_ME0
LED_MO3
LED_MO2
LED_MO1
LED_MO0
Decoupling
Mounting holes
LINK ribbon from the memory control card
SLOT PAIR JUMPERS: the centre pin to '1' where the address bit is 1 (the complement then holds the select NOR low only for this address), to '0' where it is 0
