nikolafilip/nibble/cards/memslot/memslot.kicad_pcb

## KiCad design cards/memslot/memslot.kicad_pcb (continued)

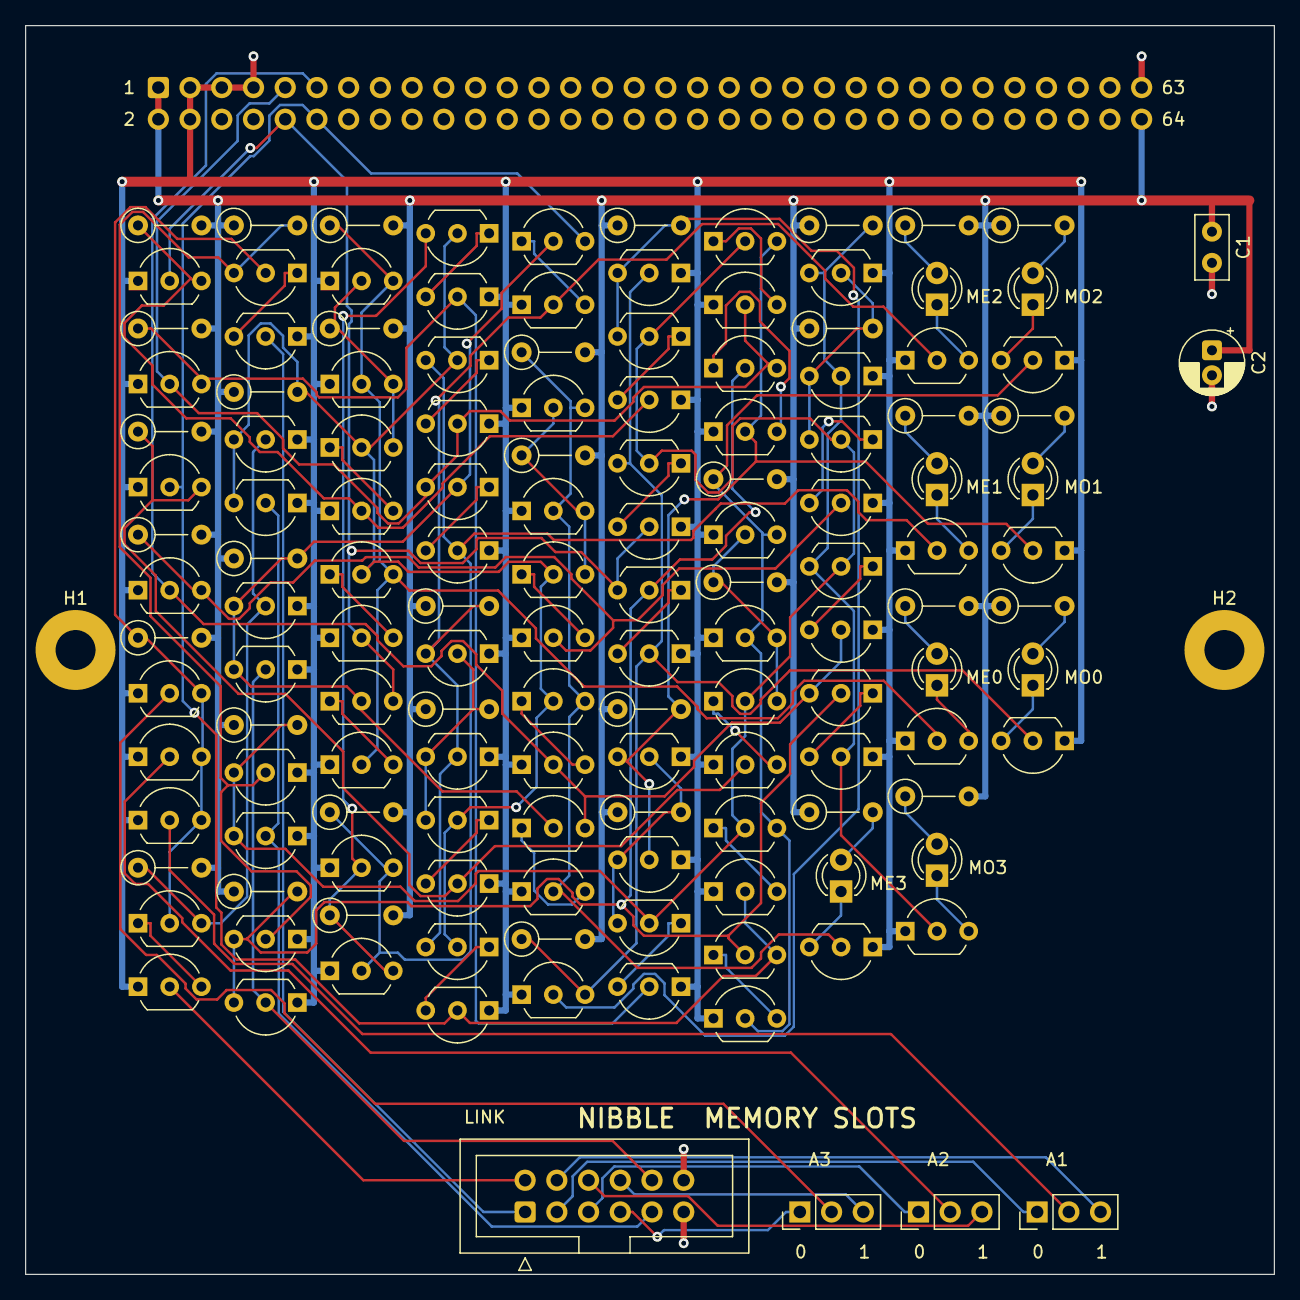
[picture p85: board memslot.kicad_pcb from above]

Board: 2 copper layers, 100.0 x 100.0 mm, 143 parts (1 on the bottom side), 88 nets.
