nikolafilip/nibble/boards/05-clock/clock.kicad_pcb

## KiCad design boards/05-clock/clock.kicad_pcb (2026-09-10, an earlier design)

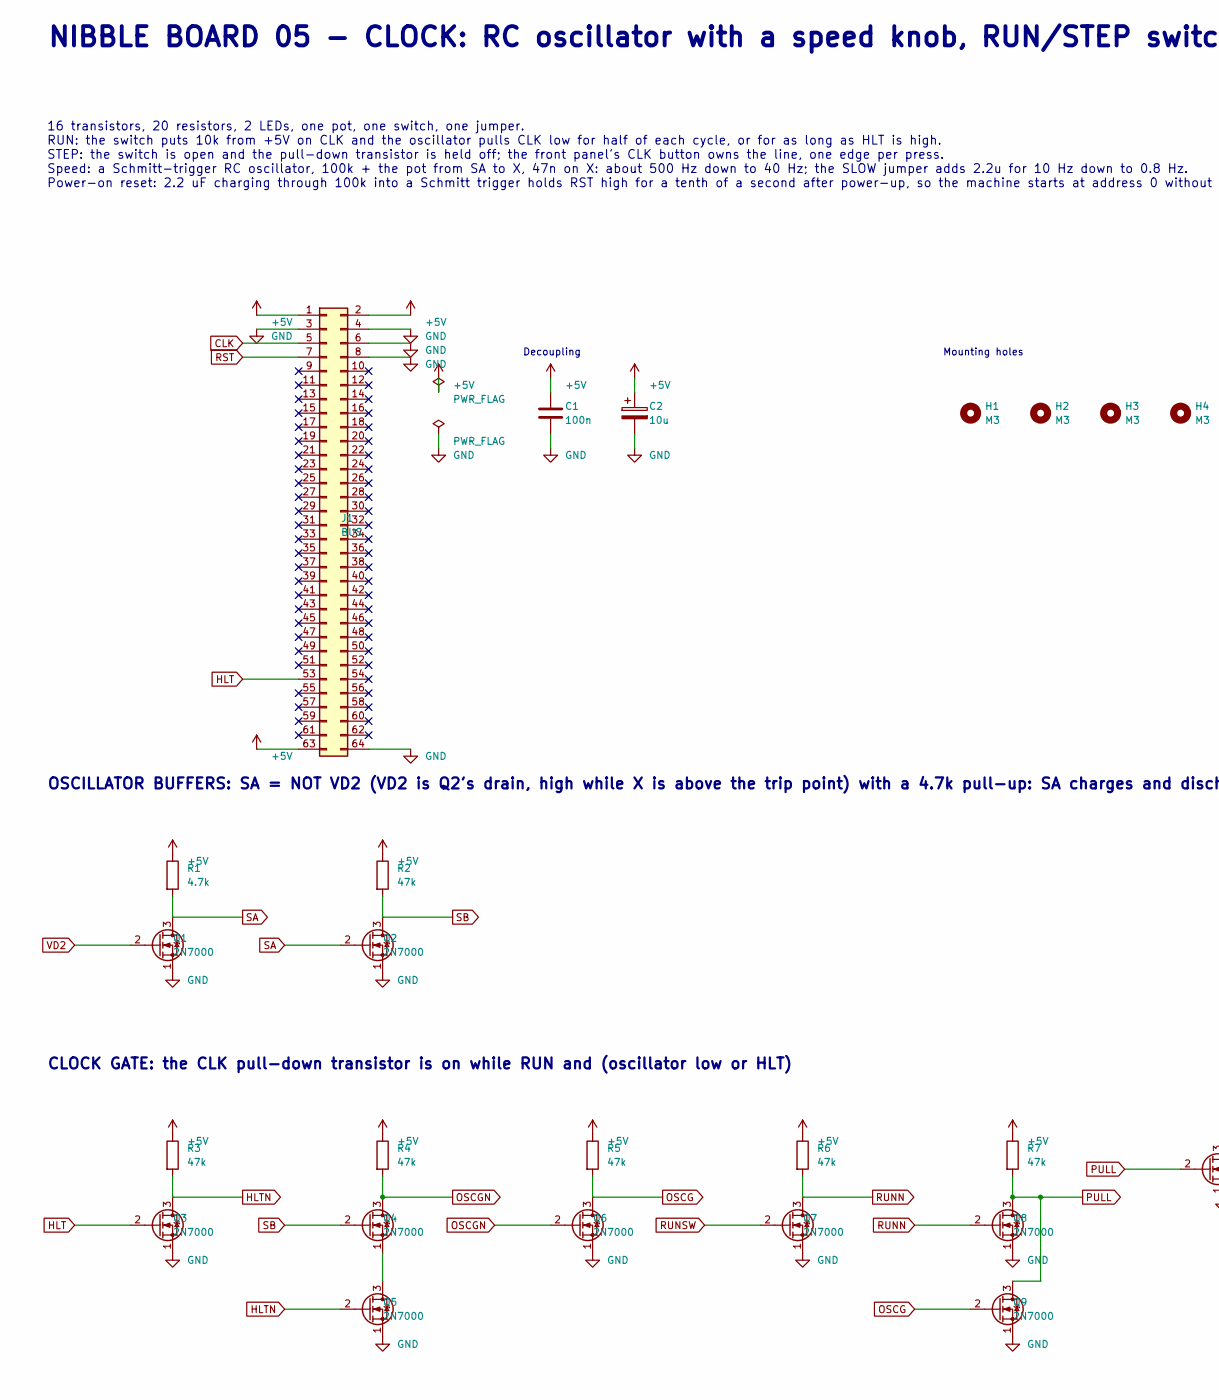
[picture p86: schematic clock.kicad_sch, part in row 1, column 1]

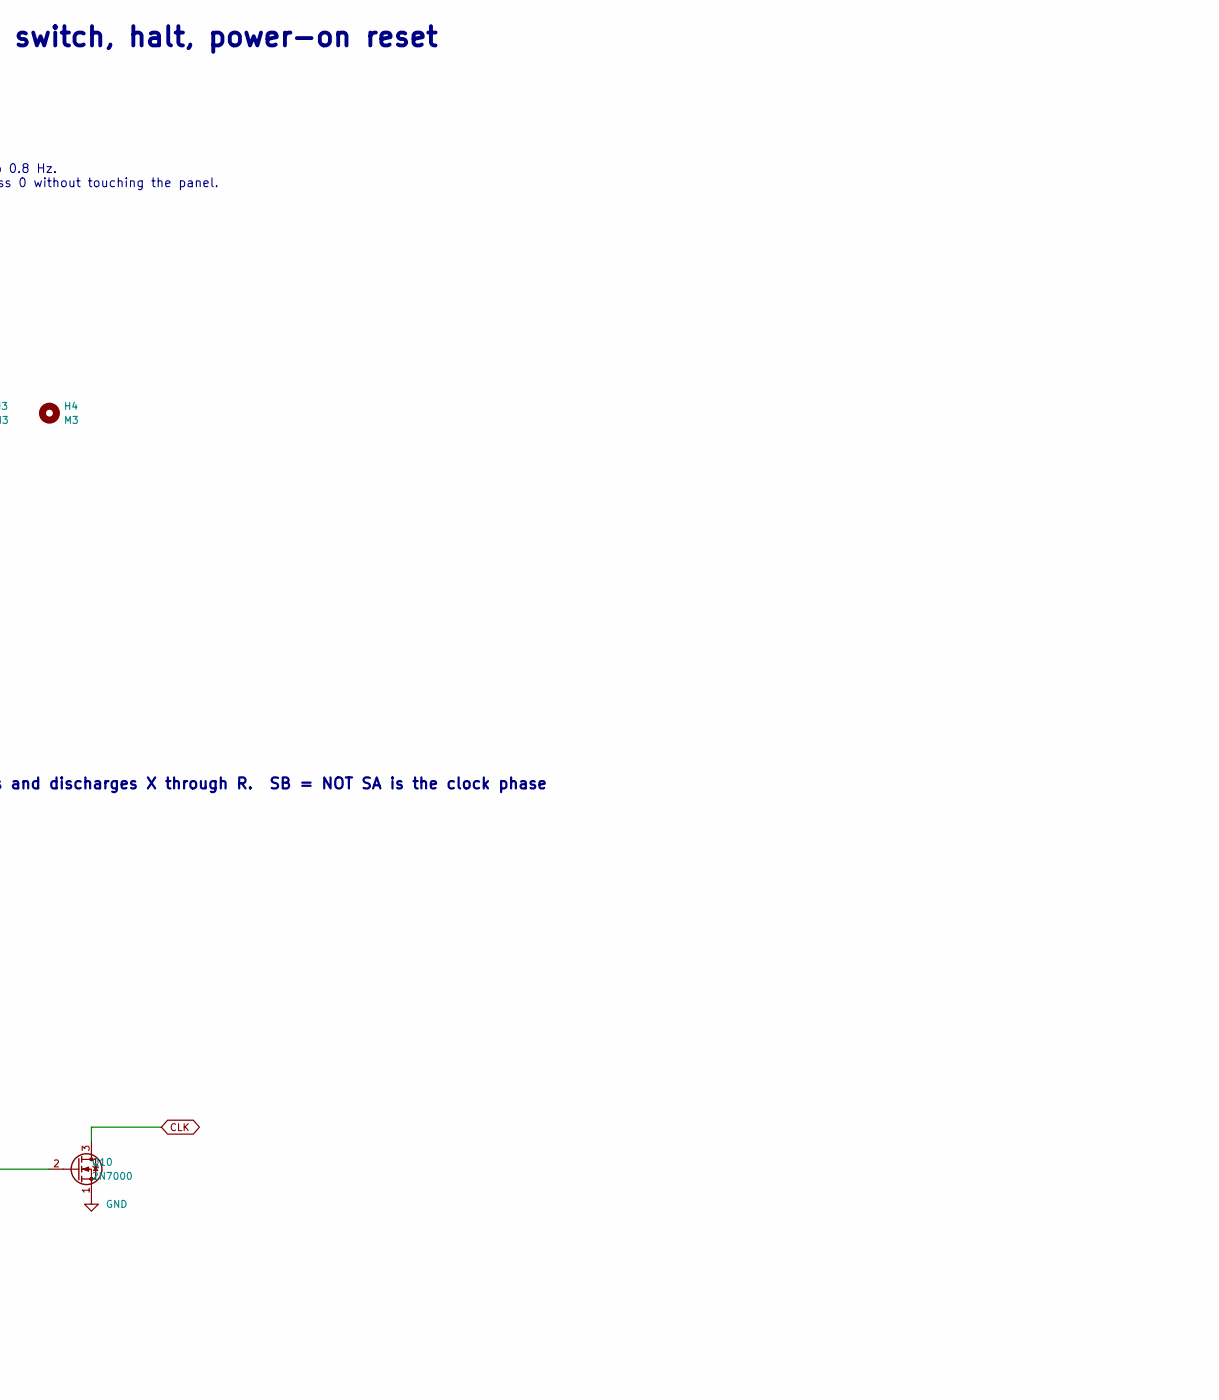
[picture p87: schematic clock.kicad_sch, part in row 1, column 2]

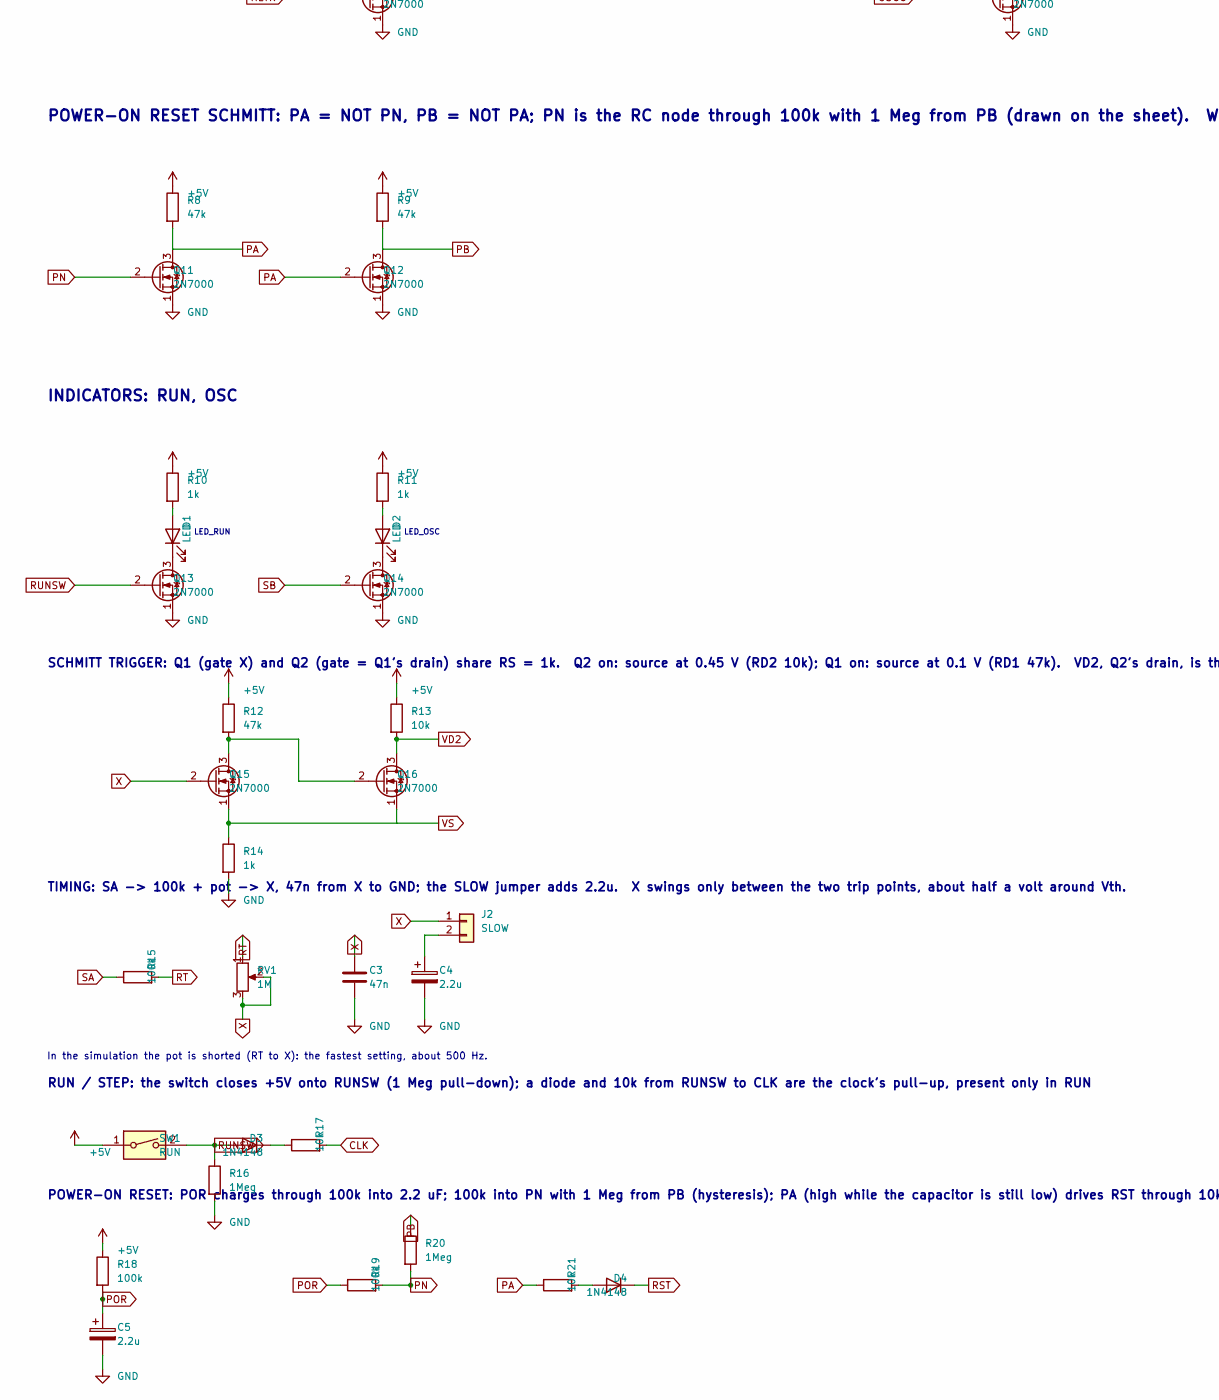
[picture p88: schematic clock.kicad_sch, part in row 2, column 1]

Parts:
C1: 100n; C_Disc_D5.0mm_W2.5mm_P2.50mm
C2: 10u; CP_Radial_D5.0mm_P2.00mm
C3: 47n; C_Disc_D5.0mm_W2.5mm_P2.50mm
C4, C5: 2.2u; CP_Radial_D5.0mm_P2.00mm
D1, D2: LED; LED_D3.0mm
D3, D4: 1N4148; D_DO-35_SOD27_P7.62mm_Horizontal
H1, H2, H3, H4: M3; MountingHole_3.2mm_M3_Pad
J1: BUS; IDC-Header_2x32_P2.54mm_Vertical
J2: SLOW; PinHeader_1x02_P2.54mm_Vertical
Q1, Q2, Q3, Q4, Q5, Q6, Q7, Q8, Q9, Q10, Q11, Q12, Q13, Q14, Q15, Q16: 2N7000; TO-92_Inline_Wide
R1: 4.7k; R_Axial_DIN0207_L6.3mm_D2.5mm_P5.08mm_Vertical
R2, R3, R4, R5, R6, R7, R8, R9, R12: 47k; R_Axial_DIN0207_L6.3mm_D2.5mm_P5.08mm_Vertical
R10, R11, R14: 1k; R_Axial_DIN0207_L6.3mm_D2.5mm_P5.08mm_Vertical
R13, R17, R21: 10k; R_Axial_DIN0207_L6.3mm_D2.5mm_P5.08mm_Vertical
R15, R18, R19: 100k; R_Axial_DIN0207_L6.3mm_D2.5mm_P5.08mm_Vertical
R16, R20: 1Meg; R_Axial_DIN0207_L6.3mm_D2.5mm_P5.08mm_Vertical
RV1: 1M; Potentiometer_Alpha_RD901F-40-00D_Single_Vertical
SW1: RUN; SW_DIP_SPSTx01_Slide_9.78x4.72mm_W7.62mm_P2.54mm

Connections:
+5V: C1.1, C2.1, J1.1, J1.2, J1.63, R1.1, R2.1, R3.1, R4.1, R5.1, R6.1, R7.1, R8.1, R9.1, R10.1, R11.1, R12.1, R13.1, R18.1, SW1.1
CLK: J1.5, Q10.3 (D), R17.2
GND: C1.2, C2.2, C3.2, C4.2, C5.2, J1.3, J1.4, J1.6, J1.8, J1.64, Q1.1 (S), Q2.1 (S), Q3.1 (S), Q5.1 (S), Q6.1 (S), Q7.1 (S), Q8.1 (S), Q9.1 (S), Q10.1 (S), Q11.1 (S), Q12.1 (S), Q13.1 (S), Q14.1 (S), R14.2, R16.2
HLT: J1.53, Q3.2 (G)
HLTN: Q3.3 (D), Q5.2 (G), R3.2
unnamed: D1.2 (A), R10.2
unnamed: D1.1 (K), Q13.3 (D)
unnamed: D2.2 (A), R11.2
unnamed: D2.1 (K), Q14.3 (D)
unnamed: D3.1 (K), R17.1
unnamed: D4.2 (A), R21.2
unnamed: C4.1, J2.2
unnamed: Q4.1 (S), Q5.3 (D)
unnamed: Q15.3 (D), Q16.2 (G), R12.2
OSCG: Q6.3 (D), Q9.2 (G), R5.2
OSCGN: Q4.3 (D), Q6.2 (G), R4.2
PA: Q11.3 (D), Q12.2 (G), R8.2, R21.1
PB: Q12.3 (D), R9.2, R20.1
PN: Q11.2 (G), R19.2, R20.2
POR: C5.1, R18.2, R19.1
PULL: Q8.3 (D), Q9.3 (D), Q10.2 (G), R7.2
RST: D4.1 (K), J1.7
RT: R15.2, RV1.1
RUNN: Q7.3 (D), Q8.2 (G), R6.2
RUNSW: D3.2 (A), Q7.2 (G), Q13.2 (G), R16.1, SW1.2
SA: Q1.3 (D), Q2.2 (G), R1.2, R15.1
SB: Q2.3 (D), Q4.2 (G), Q14.2 (G), R2.2
VD2: Q1.2 (G), Q16.3 (D), R13.2
VS: Q15.1 (S), Q16.1 (S), R14.1
X: C3.1, J2.1, Q15.2 (G), RV1.2, RV1.3

Notes on the sheet:
NIBBLE BOARD 05 - CLOCK: RC oscillator with a speed knob, RUN/STEP switch, halt, power-on reset
16 transistors, 20 resistors, 2 LEDs, one pot, one switch, one jumper. RUN: the switch puts 10k from +5V on CLK and the oscillator pulls CLK low for half of each cycle, or for as long as HLT is high. STEP: the switch is open and the pull-down transistor is held off; the front panel's CLK button own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
Decoupling
Mounting holes
OSCILLATOR BUFFERS: SA = NOT VD2 (VD2 is Q2's drain, high while X is above the trip point) with a 4.7k pull-up: SA charges and discharges X through R. SB = NOT SA is the clock phase
CLOCK GATE: the CLK pull-down transistor is on while RUN and (oscillator low or HLT)
POWER-ON RESET SCHMITT: PA = NOT PN, PB = NOT PA; PN is the RC node through 100k with 1 Meg from PB (drawn on the sheet). While PA is high (the capacitor still low) RST is pulled high through 10k and a diode
INDICATORS: RUN, OSC
LED_RUN
LED_OSC
SCHMITT TRIGGER: Q1 (gate X) and Q2 (gate = Q1's drain) share RS = 1k. Q2 on: source at 0.45 V (RD2 10k); Q1 on: source at 0.1 V (RD1 47k). VD2, Q2's drain, is the output: 0.5 V with X low, 5 V with X high.
TIMING: SA -> 100k + pot -> X, 47n from X to GND; the SLOW jumper adds 2.2u. X swings only between the two trip points, about half a volt around Vth.
In the simulation the pot is shorted (RT to X): the fastest setting, about 500 Hz.
RUN / STEP: the switch closes +5V onto RUNSW (1 Meg pull-down); a diode and 10k from RUNSW to CLK are the clock's pull-up, present only in RUN
POWER-ON RESET: POR charges through 100k into 2.2 uF; 100k into PN with 1 Meg from PB (hysteresis); PA (high while the capacitor is still low) drives RST through 10k and a diode

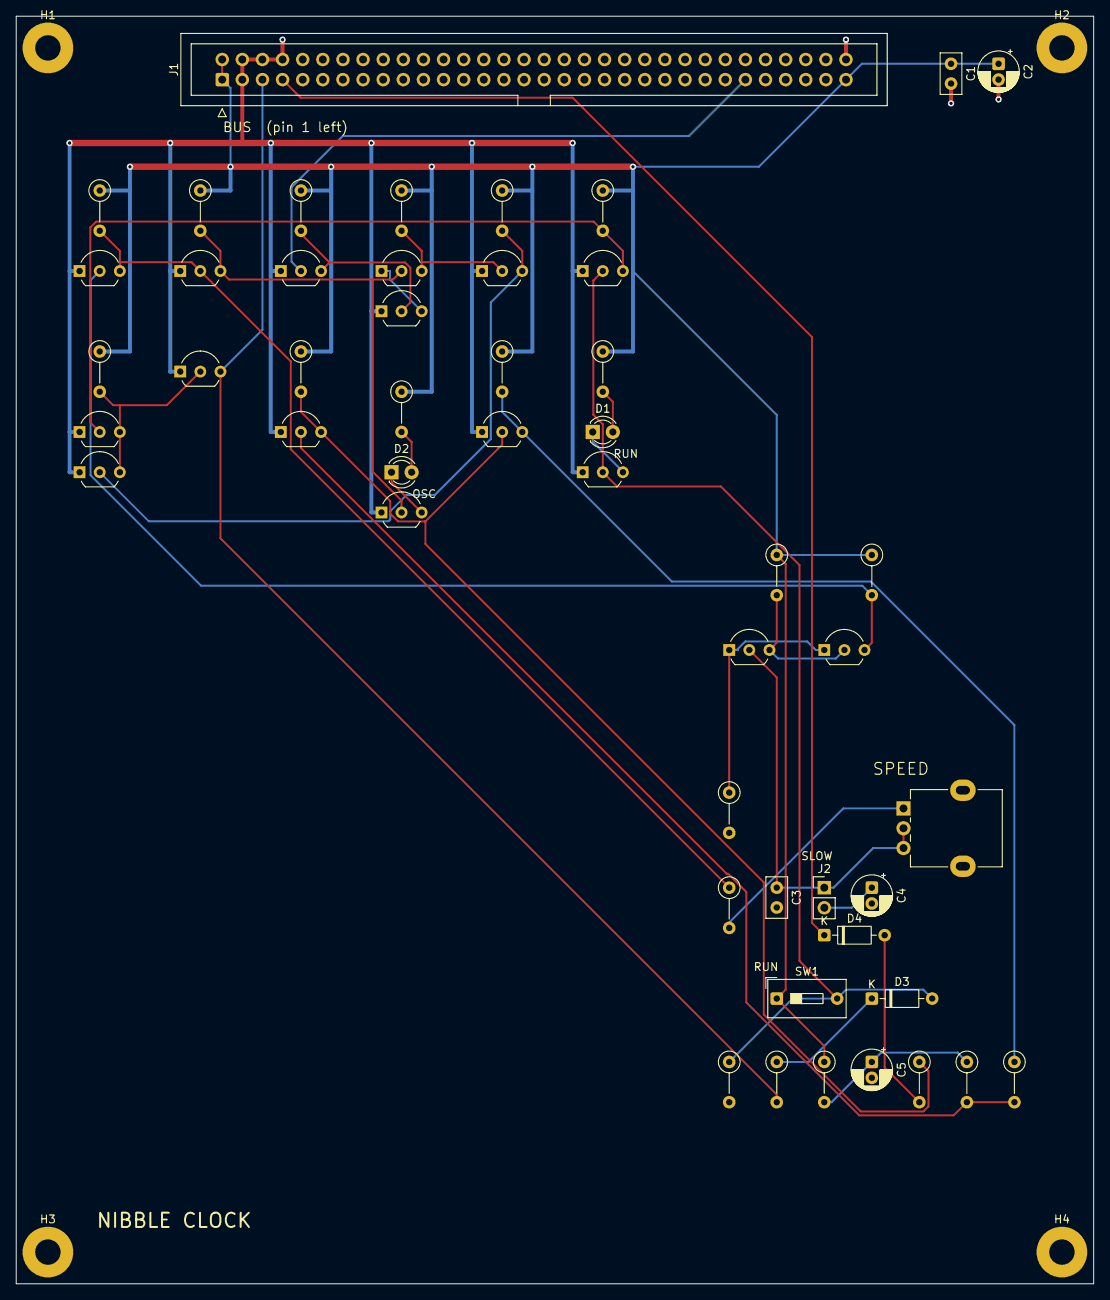
[picture p89: board boards/05-clock/clock.kicad_pcb from above]

Board: 2 copper layers, 136.0 x 160.0 mm, 54 parts (0 on the bottom side), 30 nets.
