nikolafilip/nibble/boards/01-alu/alu.kicad_pcb

## KiCad design boards/01-alu/alu.kicad_pcb (2026-09-10)

Schematic: alu.kicad_sch

Parts:
C1: 100n; C_Disc_D5.0mm_W2.5mm_P2.50mm
C2: 10u; CP_Radial_D5.0mm_P2.00mm
D1, D2, D3, D4, D5, D6: LED; LED_D3.0mm
H1, H2, H3, H4: M3; MountingHole_3.2mm_M3_Pad
J1: BUS; IDC-Header_2x32_P2.54mm_Vertical
Q1, Q2, Q3, Q4, Q5, Q6, Q7, Q8, Q9, Q10, Q11, Q12, Q13, Q14, Q15, Q16, Q17, Q18, Q19, Q20, Q21, Q22, Q23, Q24, Q25, Q26, Q27, Q28, Q29, Q30, Q31, Q32, Q33, Q34, Q35, Q36, Q37, Q38, Q39, Q40, Q41, Q42, Q43, Q44, Q45, Q46, Q47, Q48, Q49, Q50, Q51, Q52, Q53, Q54, Q55, Q56, Q57, Q58, Q59, Q60, Q61, Q62, Q63, Q64, Q65, Q66, Q67, Q68, Q69, Q70, Q71, Q72, Q73, Q74, Q75, Q76, Q77, Q78, Q79, Q80, Q81, Q82, Q83, Q84, Q85, Q86, Q87, Q88, Q89, Q90, Q91, Q92, Q93, Q94, Q95, Q96, Q97, Q98, Q99, Q100, Q101, Q102, Q103, Q104, Q105, Q106, Q107, Q108, Q109, Q110, Q111, Q112, Q113, Q114, Q115, Q116, Q117, Q118, Q119, Q120, Q121, Q122, Q123, Q124, Q125, Q126, Q127, Q128, Q129, Q130, Q131, Q132, Q133, Q134, Q135, Q136, Q137, Q138, Q139, Q140, Q141, Q142, Q143, Q144, Q145, Q146, Q147, Q148, Q149, Q150, Q151, Q152, Q153, Q154, Q155, Q156, Q157, Q158, Q159, Q160, Q161, Q162, Q163, Q164, Q165, Q166, Q167, Q168, Q169, Q170, Q171, Q172, Q173, Q174, Q175, Q176, Q177, Q178, Q179, Q180, Q181, Q182, Q183, Q184, Q185, Q186, Q187, Q188, Q189, Q190, Q191, Q192, Q193, Q194, Q195, Q196, Q197, Q198, Q199, Q200, Q201, Q202, Q203, Q204, Q205, Q206, Q207, Q208, Q209, Q210, Q211, Q212, Q213, Q214, Q215, Q216, Q217, Q218, Q219, Q220, Q221, Q222, Q223, Q224, Q225, Q226, Q227, Q228, Q229, Q230, Q231, Q232, Q233: 2N7000; TO-92_Inline_Wide
R1, R2, R3, R4, R5, R6, R7, R8, R9, R10, R11, R12, R13, R14, R15, R16, R17, R18, R19, R20, R21, R22, R23, R24, R25, R26, R27, R28, R29, R30, R31, R32, R33, R34, R35, R36, R37, R38, R39, R40, R41, R42, R43, R44, R45, R46, R47, R48, R49, R50, R51, R52, R53, R54, R55, R56, R57, R58, R59, R60, R61, R62, R63, R64, R65, R66, R67, R68, R69, R70, R71, R72, R73, R74, R75, R76, R77, R78, R79, R80, R81, R82, R83, R84, R85, R86, R87, R88, R89, R90, R91, R92, R93, R94, R95, R96, R97, R98, R99, R100, R101, R102, R103, R104, R105, R106, R107, R108, R109, R110, R111, R112, R113, R114, R115, R116, R117, R118, R119, R120, R121, R122, R123, R124, R125, R126, R127: 47k; R_Axial_DIN0207_L6.3mm_D2.5mm_P5.08mm_Vertical
R128, R129, R130, R131, R132, R133: 1k; R_Axial_DIN0207_L6.3mm_D2.5mm_P5.08mm_Vertical

Connections:
+5V: C1.1, C2.1, J1.1, J1.2, J1.63, R1.1, R2.1, R3.1, R4.1, R5.1, R6.1, R7.1, R8.1, R9.1, R10.1, R11.1, R12.1, R13.1, R14.1, R15.1, R16.1, R17.1, R18.1, R19.1, R20.1, R21.1, R22.1, R23.1, R24.1, R25.1, R26.1, R27.1, R28.1, R29.1, R30.1, R31.1, R32.1, R33.1, R34.1, R35.1, R36.1, R37.1, R38.1, R39.1, R40.1, R41.1, R42.1, R43.1, R44.1, R45.1, R46.1, R47.1, R48.1, R49.1, R50.1, R51.1, R52.1, R53.1, R54.1, R55.1, R56.1, R57.1, R58.1, R59.1, R60.1, R61.1, R62.1, R63.1, R64.1, R65.1, R66.1, R67.1, R68.1, R69.1, R70.1, R71.1, R72.1, R73.1, R74.1, R75.1, R76.1, R77.1, R78.1, R79.1, R80.1, R81.1, R82.1, R83.1, R84.1, R85.1, R86.1, R87.1, R88.1, R89.1, R90.1, R91.1, R92.1, R93.1, R94.1, R95.1, R96.1, R97.1, R98.1, R99.1, R100.1, R101.1, R102.1, R103.1, R104.1, R105.1, R106.1, R107.1, R108.1, R109.1, R110.1, R111.1, R112.1, R113.1, R114.1, R115.1, R116.1, R117.1, R118.1, R119.1, R120.1, R121.1, R122.1, R123.1, R124.1, R125.1, R126.1, R127.1, R128.1, R129.1, R130.1, R131.1, R132.1, R133.1
A0: J1.13, Q42.2 (G), Q44.2 (G), Q56.2 (G)
A1: J1.14, Q62.2 (G), Q64.2 (G), Q76.2 (G)
A2: J1.15, Q82.2 (G), Q84.2 (G), Q96.2 (G)
A3: J1.16, Q102.2 (G), Q104.2 (G), Q116.2 (G)
AND0: Q133.3 (D), Q140.2 (G), R77.2
AND1: Q151.3 (D), Q158.2 (G), R87.2
AND2: Q169.3 (D), Q176.2 (G), R97.2
AND3: Q187.3 (D), Q194.2 (G), R107.2
B0: J1.17, Q2.2 (G), Q3.2 (G)
B1: J1.18, Q12.2 (G)
B2: J1.19, Q22.2 (G)
B3: J1.20, Q32.2 (G)
BB0: Q5.3 (D), Q6.2 (G), R4.2
BB0N: Q3.3 (D), Q4.3 (D), Q5.2 (G), Q8.2 (G), R3.2
BB1: Q13.3 (D), Q14.3 (D), Q15.2 (G), Q16.2 (G), R9.2
BB1N: Q15.3 (D), Q18.2 (G), R10.2
BB2: Q23.3 (D), Q24.3 (D), Q25.2 (G), Q26.2 (G), R15.2
BB2N: Q25.3 (D), Q28.2 (G), R16.2
BB3: Q33.3 (D), Q34.3 (D), Q35.2 (G), Q36.2 (G), R21.2
BB3N: Q35.3 (D), Q38.2 (G), R22.2
BD0: Q214.3 (D), Q215.2 (G), R121.2
BD1: Q218.3 (D), Q219.2 (G), R123.2
BD2: Q222.3 (D), Q223.2 (G), R125.2
BD3: Q226.3 (D), Q227.2 (G), R127.2
BDN0: Q212.3 (D), Q214.2 (G), R120.2
BDN1: Q216.3 (D), Q218.2 (G), R122.2
BDN2: Q220.3 (D), Q222.2 (G), R124.2
BDN3: Q224.3 (D), Q226.2 (G), R126.2
BN0: Q2.3 (D), R2.2
BN1: Q12.3 (D), Q13.2 (G), R8.2
BN2: Q22.3 (D), Q23.2 (G), R14.2
BN3: Q32.3 (D), Q33.2 (G), R20.2
BUS0#: J1.9, Q215.3 (D)
BUS1#: J1.10, Q219.3 (D)
BUS2#: J1.11, Q223.3 (D)
BUS3#: J1.12, Q227.3 (D)
C1: Q60.3 (D), Q70.2 (G), Q72.2 (G), Q79.2 (G), R36.2
C2: Q80.3 (D), Q90.2 (G), Q92.2 (G), Q99.2 (G), R47.2
C3: Q100.3 (D), Q110.2 (G), Q112.2 (G), Q119.2 (G), R58.2
C4: Q120.3 (D), Q205.2 (G), R69.2
CF: J1.37, Q207.3 (D), Q232.2 (G), R118.2
CFN: Q205.3 (D), Q207.2 (G), R117.2
EO: J1.40, Q213.2 (G), Q217.2 (G), Q221.2 (G), Q225.2 (G)
F0: J1.60, Q122.2 (G), Q125.2 (G), Q129.2 (G), Q131.2 (G)
F0N: Q122.3 (D), Q127.2 (G), R70.2
F1: J1.61, Q123.2 (G), Q124.2 (G), Q126.2 (G), Q130.2 (G)
F1N: Q123.3 (D), Q128.2 (G), R71.2
FA: Q126.3 (D), Q127.3 (D), Q139.2 (G), Q157.2 (G), Q175.2 (G), Q193.2 (G), R73.2
FO: Q128.3 (D), Q129.3 (D), Q141.2 (G), Q159.2 (G), Q177.2 (G), Q195.2 (G), R74.2
FS: Q124.3 (D), Q125.3 (D), Q137.2 (G), Q155.2 (G), Q173.2 (G), Q191.2 (G), Q206.2 (G), R72.2
FX: Q132.3 (D), Q143.2 (G), Q161.2 (G), Q179.2 (G), Q197.2 (G), R76.2
FXN: Q130.3 (D), Q132.2 (G), R75.2
G0: Q56.3 (D), Q60.2 (G), Q133.2 (G), Q136.2 (G), R34.2
G1: Q76.3 (D), Q80.2 (G), Q151.2 (G), Q154.2 (G), R45.2
G2: Q96.3 (D), Q100.2 (G), Q169.2 (G), Q172.2 (G), R56.2
G3: Q116.3 (D), Q120.2 (G), Q187.2 (G), Q190.2 (G), R67.2
GND: C1.2, C2.2, J1.3, J1.4, J1.6, J1.8, J1.64, Q1.1 (S), Q2.1 (S), Q3.1 (S), Q4.1 (S), Q5.1 (S), Q7.1 (S), Q9.1 (S), Q11.1 (S), Q12.1 (S), Q13.1 (S), Q14.1 (S), Q15.1 (S), Q17.1 (S), Q19.1 (S), Q21.1 (S), Q22.1 (S), Q23.1 (S), Q24.1 (S), Q25.1 (S), Q27.1 (S), Q29.1 (S), Q31.1 (S), Q32.1 (S), Q33.1 (S), Q34.1 (S), Q35.1 (S), Q37.1 (S), Q39.1 (S), Q41.1 (S), Q42.1 (S), Q43.1 (S), Q45.1 (S), Q46.1 (S), Q47.1 (S), Q48.1 (S), Q49.1 (S), Q50.1 (S), Q52.1 (S), Q53.1 (S), Q54.1 (S), Q55.1 (S), Q57.1 (S), Q59.1 (S), Q61.1 (S), Q62.1 (S), Q63.1 (S), Q65.1 (S), Q66.1 (S), Q67.1 (S), Q68.1 (S), Q69.1 (S), Q70.1 (S), Q72.1 (S), Q73.1 (S), Q74.1 (S), Q75.1 (S), Q77.1 (S), Q79.1 (S), Q81.1 (S), Q82.1 (S), Q83.1 (S), Q85.1 (S), Q86.1 (S), Q87.1 (S), Q88.1 (S), Q89.1 (S), Q90.1 (S), Q92.1 (S), Q93.1 (S), Q94.1 (S), Q95.1 (S), Q97.1 (S), Q99.1 (S), Q101.1 (S), Q102.1 (S), Q103.1 (S), Q105.1 (S), Q106.1 (S), Q107.1 (S), Q108.1 (S), Q109.1 (S), Q110.1 (S), Q112.1 (S), Q113.1 (S), Q114.1 (S), Q115.1 (S), Q117.1 (S), Q119.1 (S), Q121.1 (S), Q122.1 (S), Q123.1 (S), Q124.1 (S), Q125.1 (S), Q126.1 (S), Q127.1 (S), Q128.1 (S), Q129.1 (S), Q131.1 (S), Q132.1 (S), Q133.1 (S), Q134.1 (S), Q136.1 (S), Q138.1 (S), Q140.1 (S), Q142.1 (S), Q144.1 (S), Q147.1 (S), Q148.1 (S), Q150.1 (S), Q151.1 (S), Q152.1 (S), Q154.1 (S), Q156.1 (S), Q158.1 (S), Q160.1 (S), Q162.1 (S), Q165.1 (S), Q166.1 (S), Q168.1 (S), Q169.1 (S), Q170.1 (S), Q172.1 (S), Q174.1 (S), Q176.1 (S), Q178.1 (S), Q180.1 (S), Q183.1 (S), Q184.1 (S), Q186.1 (S), Q187.1 (S), Q188.1 (S), Q190.1 (S), Q192.1 (S), Q194.1 (S), Q196.1 (S), Q198.1 (S), Q201.1 (S), Q202.1 (S), Q204.1 (S), Q206.1 (S), Q207.1 (S), Q208.1 (S), Q209.1 (S), Q210.1 (S), Q211.1 (S), Q213.1 (S), Q214.1 (S), Q215.1 (S), Q217.1 (S), Q218.1 (S), Q219.1 (S), Q221.1 (S), Q222.1 (S), Q223.1 (S), Q225.1 (S), Q226.1 (S), Q227.1 (S), Q228.1 (S), Q229.1 (S), Q230.1 (S), Q231.1 (S), Q232.1 (S), Q233.1 (S)
unnamed: D1.2 (A), R128.2
unnamed: D1.1 (K), Q228.3 (D)
unnamed: D2.2 (A), R129.2
unnamed: D2.1 (K), Q229.3 (D)
unnamed: D3.2 (A), R130.2
unnamed: D3.1 (K), Q230.3 (D)
unnamed: D4.2 (A), R131.2
unnamed: D4.1 (K), Q231.3 (D)
unnamed: D5.2 (A), R132.2
unnamed: D5.1 (K), Q232.3 (D)
unnamed: D6.2 (A), R133.2
unnamed: D6.1 (K), Q233.3 (D)
unnamed: Q6.1 (S), Q7.3 (D)
unnamed: Q8.1 (S), Q9.3 (D)
unnamed: Q10.1 (S), Q11.3 (D)
unnamed: Q16.1 (S), Q17.3 (D)
unnamed: Q18.1 (S), Q19.3 (D)
unnamed: Q20.1 (S), Q21.3 (D)
unnamed: Q26.1 (S), Q27.3 (D)
unnamed: Q28.1 (S), Q29.3 (D)
unnamed: Q30.1 (S), Q31.3 (D)
unnamed: Q36.1 (S), Q37.3 (D)
unnamed: Q38.1 (S), Q39.3 (D)
unnamed: Q40.1 (S), Q41.3 (D)
unnamed: Q44.1 (S), Q45.3 (D)
unnamed: Q51.1 (S), Q52.3 (D)
unnamed: Q56.1 (S), Q57.3 (D)
unnamed: Q58.1 (S), Q59.3 (D)
unnamed: Q60.1 (S), Q61.3 (D)
unnamed: Q64.1 (S), Q65.3 (D)
unnamed: Q71.1 (S), Q72.3 (D)
unnamed: Q76.1 (S), Q77.3 (D)
unnamed: Q78.1 (S), Q79.3 (D)
unnamed: Q80.1 (S), Q81.3 (D)
unnamed: Q84.1 (S), Q85.3 (D)
unnamed: Q91.1 (S), Q92.3 (D)
unnamed: Q96.1 (S), Q97.3 (D)
unnamed: Q98.1 (S), Q99.3 (D)
unnamed: Q100.1 (S), Q101.3 (D)
unnamed: Q104.1 (S), Q105.3 (D)
unnamed: Q111.1 (S), Q112.3 (D)
unnamed: Q116.1 (S), Q117.3 (D)
unnamed: Q118.1 (S), Q119.3 (D)
unnamed: Q120.1 (S), Q121.3 (D)
unnamed: Q130.1 (S), Q131.3 (D)
unnamed: Q135.1 (S), Q136.3 (D)
unnamed: Q137.1 (S), Q138.3 (D)
unnamed: Q139.1 (S), Q140.3 (D)
unnamed: Q141.1 (S), Q142.3 (D)
unnamed: Q143.1 (S), Q144.3 (D)
unnamed: Q145.1 (S), Q146.3 (D)
unnamed: Q146.1 (S), Q147.3 (D)
unnamed: Q149.1 (S), Q150.3 (D)
unnamed: Q153.1 (S), Q154.3 (D)
unnamed: Q155.1 (S), Q156.3 (D)
unnamed: Q157.1 (S), Q158.3 (D)
unnamed: Q159.1 (S), Q160.3 (D)
unnamed: Q161.1 (S), Q162.3 (D)
unnamed: Q163.1 (S), Q164.3 (D)
unnamed: Q164.1 (S), Q165.3 (D)
unnamed: Q167.1 (S), Q168.3 (D)
unnamed: Q171.1 (S), Q172.3 (D)
unnamed: Q173.1 (S), Q174.3 (D)
unnamed: Q175.1 (S), Q176.3 (D)
unnamed: Q177.1 (S), Q178.3 (D)
unnamed: Q179.1 (S), Q180.3 (D)
unnamed: Q181.1 (S), Q182.3 (D)
unnamed: Q182.1 (S), Q183.3 (D)
unnamed: Q185.1 (S), Q186.3 (D)
unnamed: Q189.1 (S), Q190.3 (D)
unnamed: Q191.1 (S), Q192.3 (D)
unnamed: Q193.1 (S), Q194.3 (D)
unnamed: Q195.1 (S), Q196.3 (D)
unnamed: Q197.1 (S), Q198.3 (D)
unnamed: Q199.1 (S), Q200.3 (D)
unnamed: Q200.1 (S), Q201.3 (D)
unnamed: Q203.1 (S), Q204.3 (D)
unnamed: Q205.1 (S), Q206.3 (D)
unnamed: Q212.1 (S), Q213.3 (D)
unnamed: Q216.1 (S), Q217.3 (D)
unnamed: Q220.1 (S), Q221.3 (D)
unnamed: Q224.1 (S), Q225.3 (D)
ONE: J1.59, Q4.2 (G), Q14.2 (G), Q24.2 (G), Q34.2 (G)
OR0: Q135.3 (D), Q142.2 (G), R79.2
OR1: Q153.3 (D), Q160.2 (G), R89.2
OR2: Q171.3 (D), Q178.2 (G), R99.2
OR3: Q189.3 (D), Q196.2 (G), R109.2
P0: Q47.3 (D), Q48.3 (D), Q49.2 (G), Q51.2 (G), Q58.2 (G), Q134.2 (G), Q144.2 (G), R29.2
P0_a: Q44.3 (D), Q46.2 (G), R27.2
P0_d: Q46.3 (D), Q48.2 (G), R28.2
P0_n: Q42.3 (D), Q43.3 (D), Q47.2 (G), R26.2
P1: Q67.3 (D), Q68.3 (D), Q69.2 (G), Q71.2 (G), Q78.2 (G), Q152.2 (G), Q162.2 (G), R40.2
P1_a: Q64.3 (D), Q66.2 (G), R38.2
P1_d: Q66.3 (D), Q68.2 (G), R39.2
P1_n: Q62.3 (D), Q63.3 (D), Q67.2 (G), R37.2
P2: Q87.3 (D), Q88.3 (D), Q89.2 (G), Q91.2 (G), Q98.2 (G), Q170.2 (G), Q180.2 (G), R51.2
P2_a: Q84.3 (D), Q86.2 (G), R49.2
P2_d: Q86.3 (D), Q88.2 (G), R50.2
P2_n: Q82.3 (D), Q83.3 (D), Q87.2 (G), R48.2
P3: Q107.3 (D), Q108.3 (D), Q109.2 (G), Q111.2 (G), Q118.2 (G), Q188.2 (G), Q198.2 (G), R62.2
P3_a: Q104.3 (D), Q106.2 (G), R60.2
P3_d: Q106.3 (D), Q108.2 (G), R61.2
P3_n: Q102.3 (D), Q103.3 (D), Q107.2 (G), R59.2
PN0: Q134.3 (D), Q135.2 (G), R78.2
PN1: Q152.3 (D), Q153.2 (G), R88.2
PN2: Q170.3 (D), Q171.2 (G), R98.2
PN3: Q188.3 (D), Q189.2 (G), R108.2
R0: Q149.3 (D), Q208.2 (G), Q212.2 (G), Q231.2 (G), R86.2
R1: Q167.3 (D), Q209.2 (G), Q216.2 (G), Q230.2 (G), R96.2
R2: Q185.3 (D), Q210.2 (G), Q220.2 (G), Q229.2 (G), R106.2
R3: Q203.3 (D), Q211.2 (G), Q224.2 (G), Q228.2 (G), R116.2
RA0: Q139.3 (D), Q146.2 (G), R81.2
RA1: Q157.3 (D), Q164.2 (G), R91.2
RA2: Q175.3 (D), Q182.2 (G), R101.2
RA3: Q193.3 (D), Q200.2 (G), R111.2
RM0: Q145.3 (D), Q148.2 (G), R84.2
RM1: Q163.3 (D), Q166.2 (G), R94.2
RM2: Q181.3 (D), Q184.2 (G), R104.2
RM3: Q199.3 (D), Q202.2 (G), R114.2
RMN0: Q148.3 (D), Q149.2 (G), R85.2
RMN1: Q166.3 (D), Q167.2 (G), R95.2
RMN2: Q184.3 (D), Q185.2 (G), R105.2
RMN3: Q202.3 (D), Q203.2 (G), R115.2
RO0: Q141.3 (D), Q147.2 (G), R82.2
RO1: Q159.3 (D), Q165.2 (G), R92.2
RO2: Q177.3 (D), Q183.2 (G), R102.2
RO3: Q195.3 (D), Q201.2 (G), R112.2
RS0: Q137.3 (D), Q145.2 (G), R80.2
RS1: Q155.3 (D), Q163.2 (G), R90.2
RS2: Q173.3 (D), Q181.2 (G), R100.2
RS3: Q191.3 (D), Q199.2 (G), R110.2
RX0: Q143.3 (D), Q150.2 (G), R83.2
RX1: Q161.3 (D), Q168.2 (G), R93.2
RX2: Q179.3 (D), Q186.2 (G), R103.2
RX3: Q197.3 (D), Q204.2 (G), R113.2
S0: Q54.3 (D), Q55.3 (D), Q138.2 (G), R33.2
S0_a: Q51.3 (D), Q53.2 (G), R31.2
S0_d: Q53.3 (D), Q55.2 (G), R32.2
S0_n: Q49.3 (D), Q50.3 (D), Q54.2 (G), R30.2
S1: Q74.3 (D), Q75.3 (D), Q156.2 (G), R44.2
S1_a: Q71.3 (D), Q73.2 (G), R42.2
S1_d: Q73.3 (D), Q75.2 (G), R43.2
S1_n: Q69.3 (D), Q70.3 (D), Q74.2 (G), R41.2
S2: Q94.3 (D), Q95.3 (D), Q174.2 (G), R55.2
S2_a: Q91.3 (D), Q93.2 (G), R53.2
S2_d: Q93.3 (D), Q95.2 (G), R54.2
S2_n: Q89.3 (D), Q90.3 (D), Q94.2 (G), R52.2
S3: Q114.3 (D), Q115.3 (D), Q192.2 (G), R66.2
S3_a: Q111.3 (D), Q113.2 (G), R64.2
S3_d: Q113.3 (D), Q115.2 (G), R65.2
S3_n: Q109.3 (D), Q110.3 (D), Q114.2 (G), R63.2
SUB: J1.39, Q1.2 (G), Q9.2 (G), Q19.2 (G), Q29.2 (G), Q39.2 (G), Q50.2 (G), Q52.2 (G), Q59.2 (G)
SUBN: Q1.3 (D), Q7.2 (G), Q17.2 (G), Q27.2 (G), Q37.2 (G), R1.2
T0: Q58.3 (D), Q61.2 (G), R35.2
T1: Q78.3 (D), Q81.2 (G), R46.2
T2: Q98.3 (D), Q101.2 (G), R57.2
T3: Q118.3 (D), Q121.2 (G), R68.2
XB0: Q10.3 (D), Q43.2 (G), Q45.2 (G), Q57.2 (G), R7.2
XB1: Q20.3 (D), Q63.2 (G), Q65.2 (G), Q77.2 (G), R13.2
XB2: Q30.3 (D), Q83.2 (G), Q85.2 (G), Q97.2 (G), R19.2
XB3: Q40.3 (D), Q103.2 (G), Q105.2 (G), Q117.2 (G), R25.2
XBA0: Q6.3 (D), Q10.2 (G), R5.2
XBA1: Q16.3 (D), Q20.2 (G), R11.2
XBA2: Q26.3 (D), Q30.2 (G), R17.2
XBA3: Q36.3 (D), Q40.2 (G), R23.2
XBB0: Q8.3 (D), Q11.2 (G), R6.2
XBB1: Q18.3 (D), Q21.2 (G), R12.2
XBB2: Q28.3 (D), Q31.2 (G), R18.2
XBB3: Q38.3 (D), Q41.2 (G), R24.2
ZF: J1.38, Q208.3 (D), Q209.3 (D), Q210.3 (D), Q211.3 (D), Q233.2 (G), R119.2

Notes on the sheet:
NIBBLE BOARD 01 - ALU: 4-bit adder/subtractor, AND, OR, XOR, with carry and zero flags
Cell: 2N7000 + 47k pull-up (NMOS, see docs/gate-cell.md). 233 transistors, 133 resistors, 6 LEDs. Inputs from the bus header: A3..A0, B3..B0 (register contents), SUB (1 = subtract), ONE (B input replaced by 0001: INC, DEC), F1 F0 (function), EO (1 = drive the result onto the bus). Outputs: CF (carr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
Decoupling
Mounting holes
B INPUT: BB = B, or 0001 when ONE=1 (INC, DEC). Then the conditional invert: XB = BB when SUB=0, NOT BB when SUB=1 (two's complement: A - B = A + NOT B + 1, the +1 is SUB fed into the carry-in)
RIPPLE-CARRY FULL ADDERS, bit 0 to bit 3: P = A xor XB, S = P xor Cin, Cout = A.XB + P.Cin. G = NAND(A, XB) is also NOT (A and XB), P is A xor XB, and A or XB = NAND(NOT P, G): the logic functions fall out of the adder
FUNCTION DECODE: FS = add/sub (F1 F0 = 00), FA = and (01), FO = or (10), FX = xor (11)
RESULT SELECT, per bit: R = FS.S + FA.AND + FO.OR + FX.P. NAND-NAND form with the four-way OR split as NAND3 then NAND2 (never more than three transistors in series)
FLAGS: CF = carry out of bit 3, only for add/sub (0 for the logic functions); ZF = all result bits zero
BUS DRIVERS: pull BUS_i# low when EO=1 and R_i=1 (open drain, pull-ups live on the hub board)
INDICATORS: result R3..R0, CF, ZF
LED_R3
LED_R2
LED_R1
LED_R0
LED_CF
LED_ZF

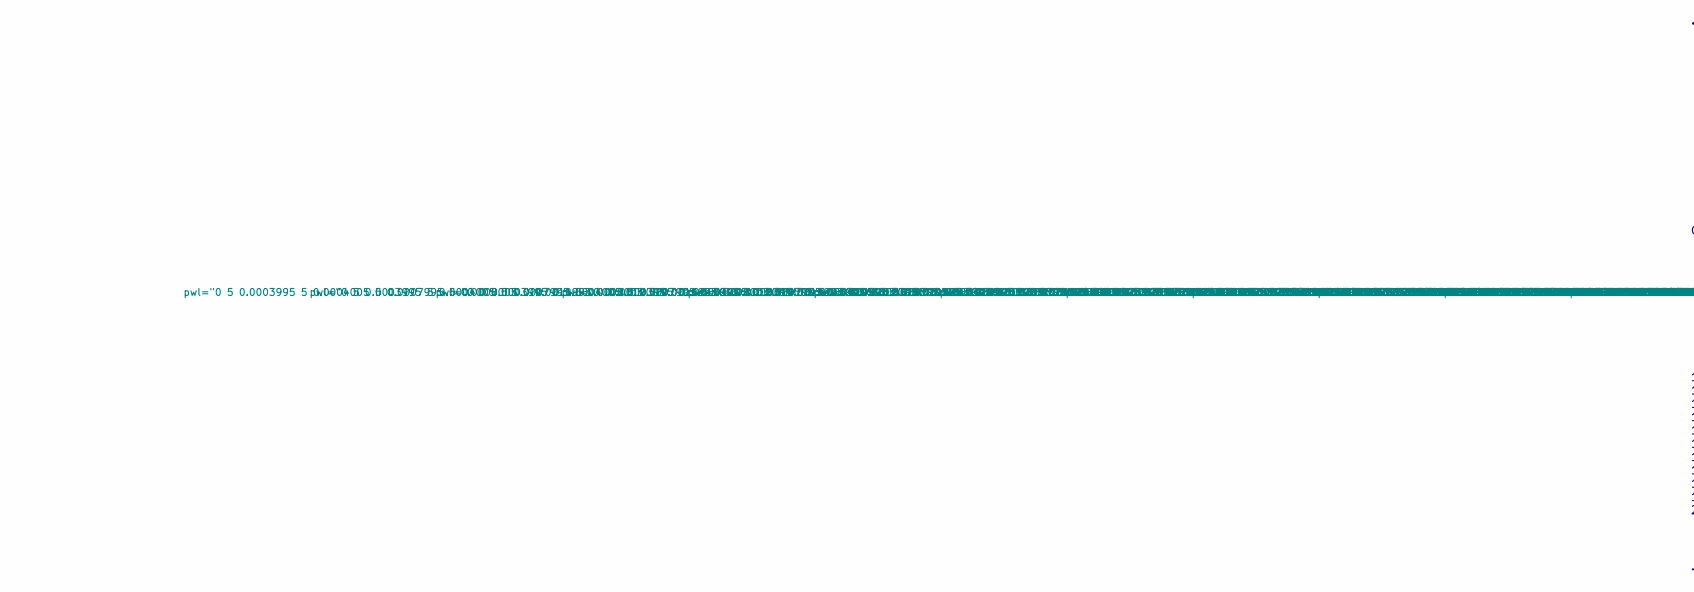
[picture p90: schematic alu-testbench.kicad_sch, part in row 1, column 1]

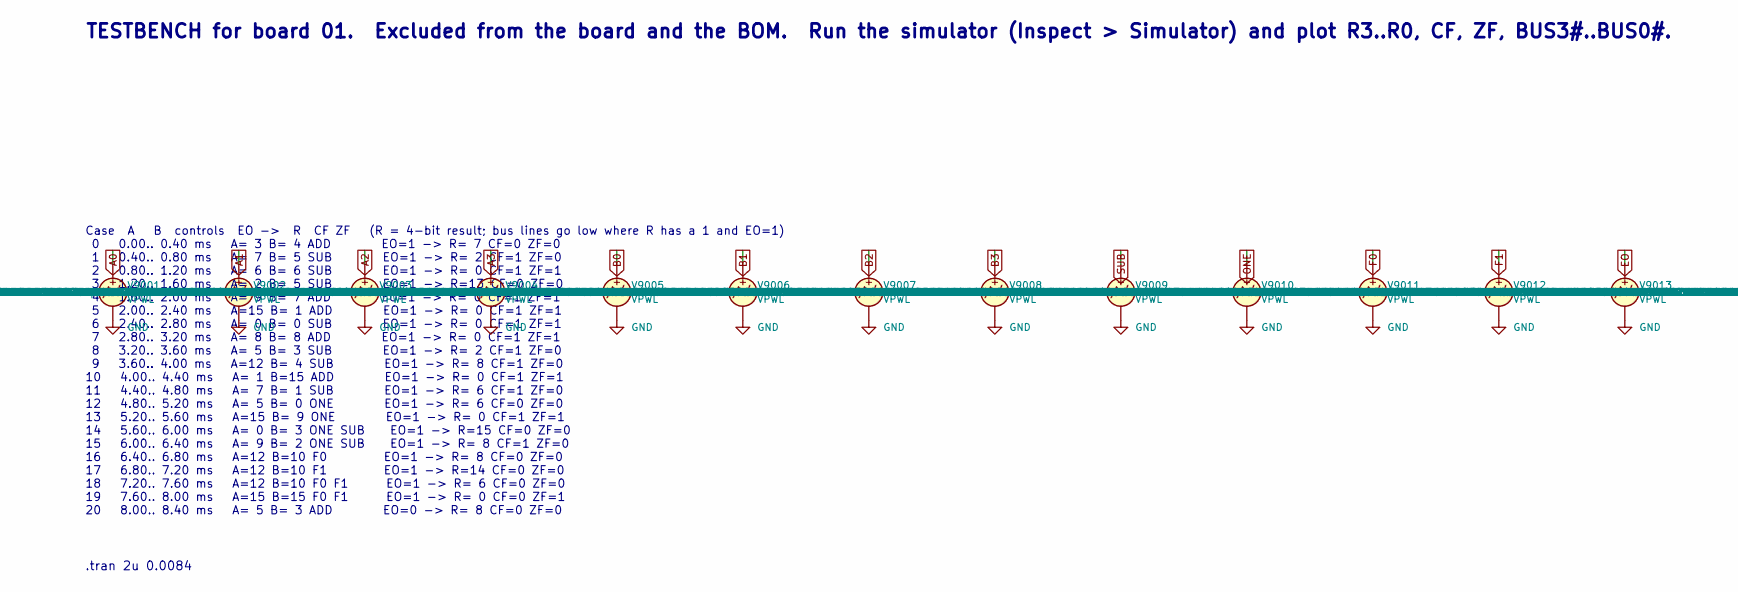
[picture p91: schematic alu-testbench.kicad_sch, part in row 1, column 2]

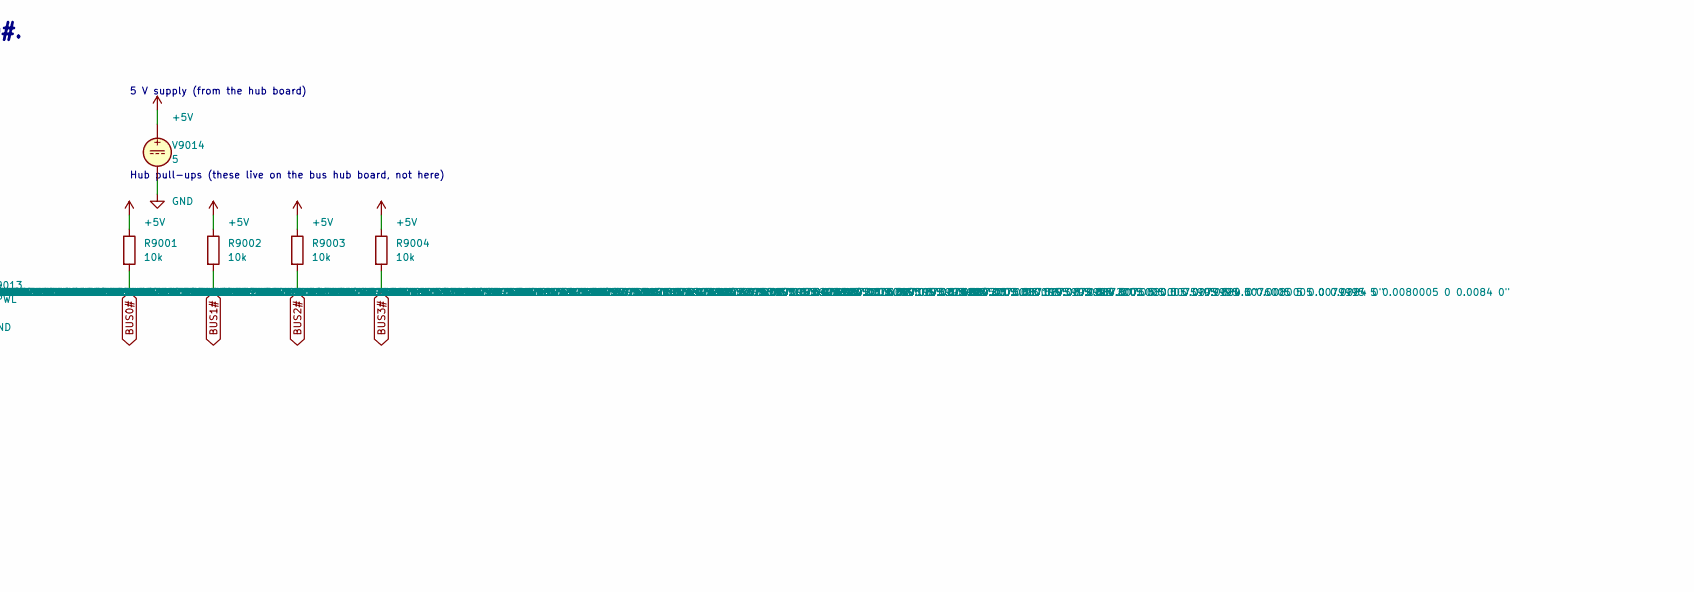
[picture p92: schematic alu-testbench.kicad_sch, part in row 1, column 3]

Parts:
R9001, R9002, R9003, R9004: 10k
V9001, V9002, V9003, V9004, V9005, V9006, V9007, V9008, V9009, V9010, V9011, V9012, V9013: VPWL
V9014: 5

Connections:
unnamed: R9001.1, R9002.1, R9003.1, R9004.1, V9014.1
unnamed: V9001.2, V9002.2, V9003.2, V9004.2, V9005.2, V9006.2, V9007.2, V9008.2, V9009.2, V9010.2, V9011.2, V9012.2, V9013.2, V9014.2

Notes on the sheet:
TESTBENCH for board 01. Excluded from the board and the BOM. Run the simulator (Inspect > Simulator) and plot R3..R0, CF, ZF, BUS3#..BUS0#.
Case A B controls EO -> R CF ZF (R = 4-bit result; bus lines go low where R has a 1 and EO=1) 0 0.00.. 0.40 ms A= 3 B= 4 ADD EO=1 -> R= 7 CF=0 ZF=0 1 0.40.. 0.80 ms A= 7 B= 5 SUB EO=1 -> R= 2 CF=1 ZF=0 2 0.80.. 1.20 ms A= 6 B= 6 SUB EO=1 -> R= 0 CF=1 ZF=1 3 1.20.. 1.60 ms A= 2 B= 5 SUB EO=1 -> R=13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
.tran 2u 0.0084
5 V supply (from the hub board)
Hub pull-ups (these live on the bus hub board, not here)
