nikolafilip/nibble/boards/01-alu/alu.kicad_pcb

## KiCad design boards/01-alu/alu.kicad_pcb (continued)

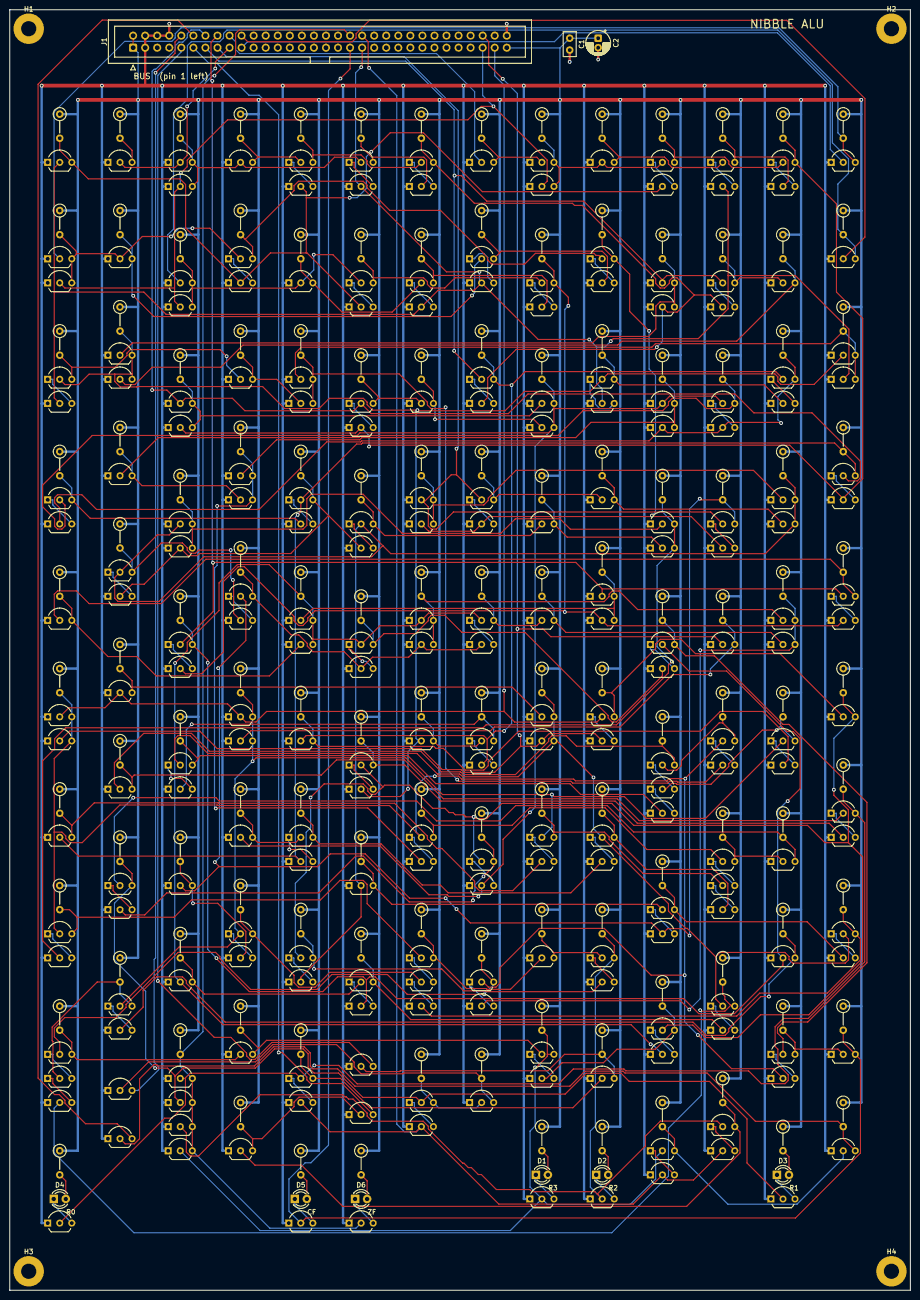
[picture p93: board alu.kicad_pcb from above]

Board: 2 copper layers, 189.8 x 269.8 mm, 379 parts (0 on the bottom side), 228 nets.
