nikolafilip/nibble/boards/07-hub/hub.kicad_pcb

## KiCad design boards/07-hub/hub.kicad_pcb (2026-09-10, an earlier design)

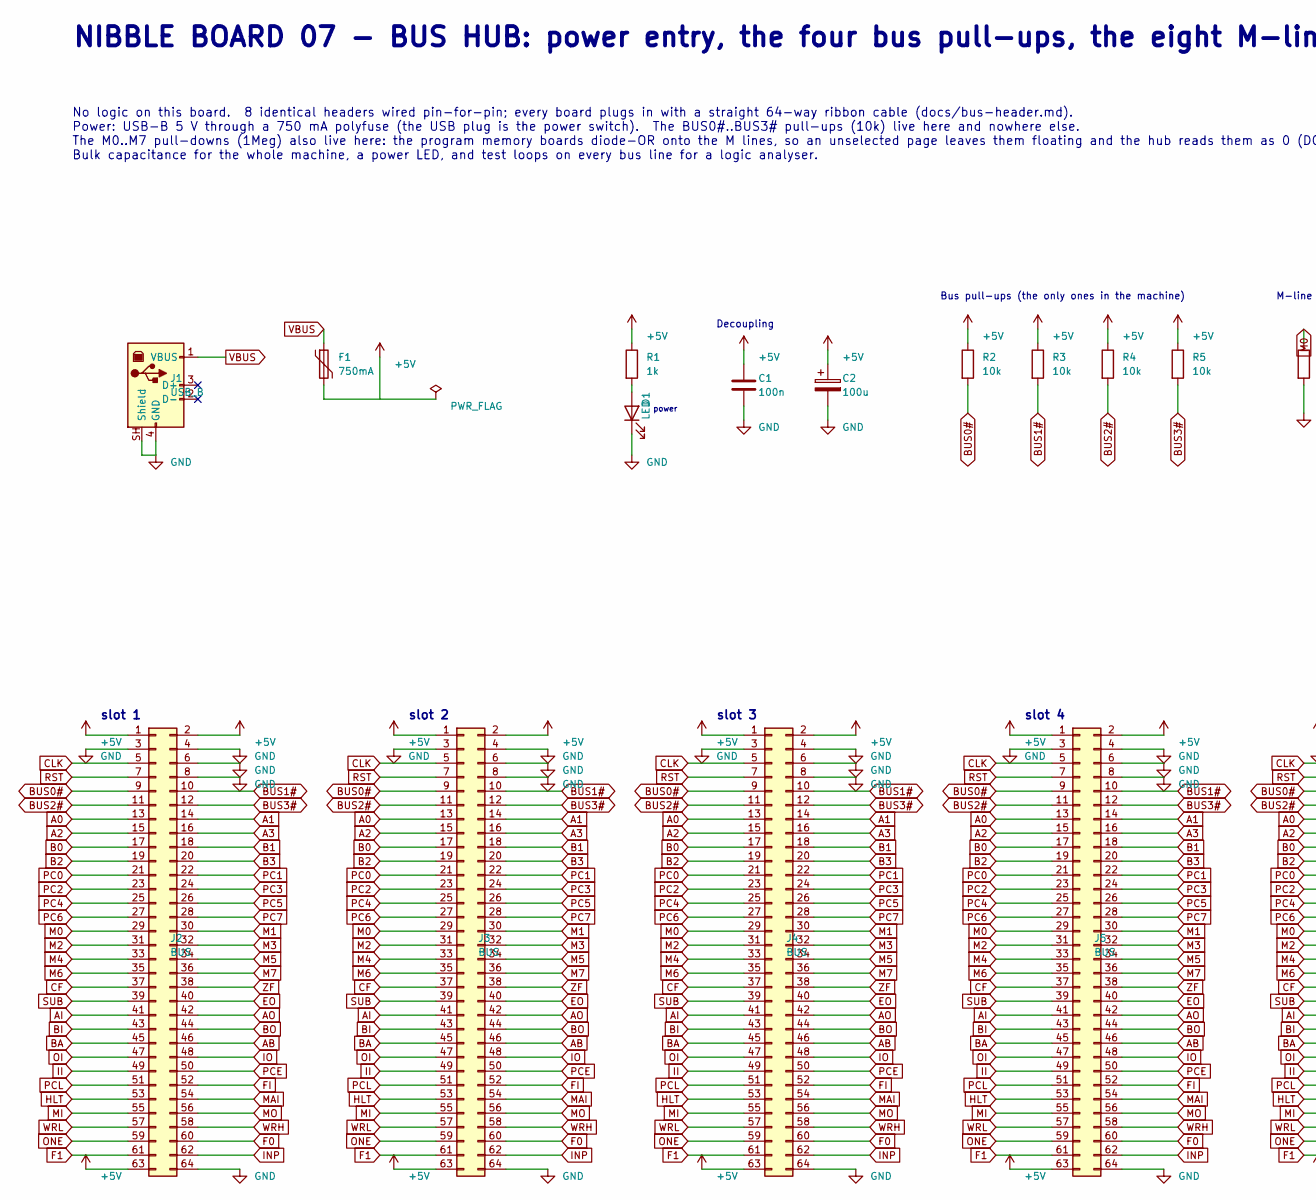
[picture p94: schematic hub.kicad_sch, part in row 1, column 1]

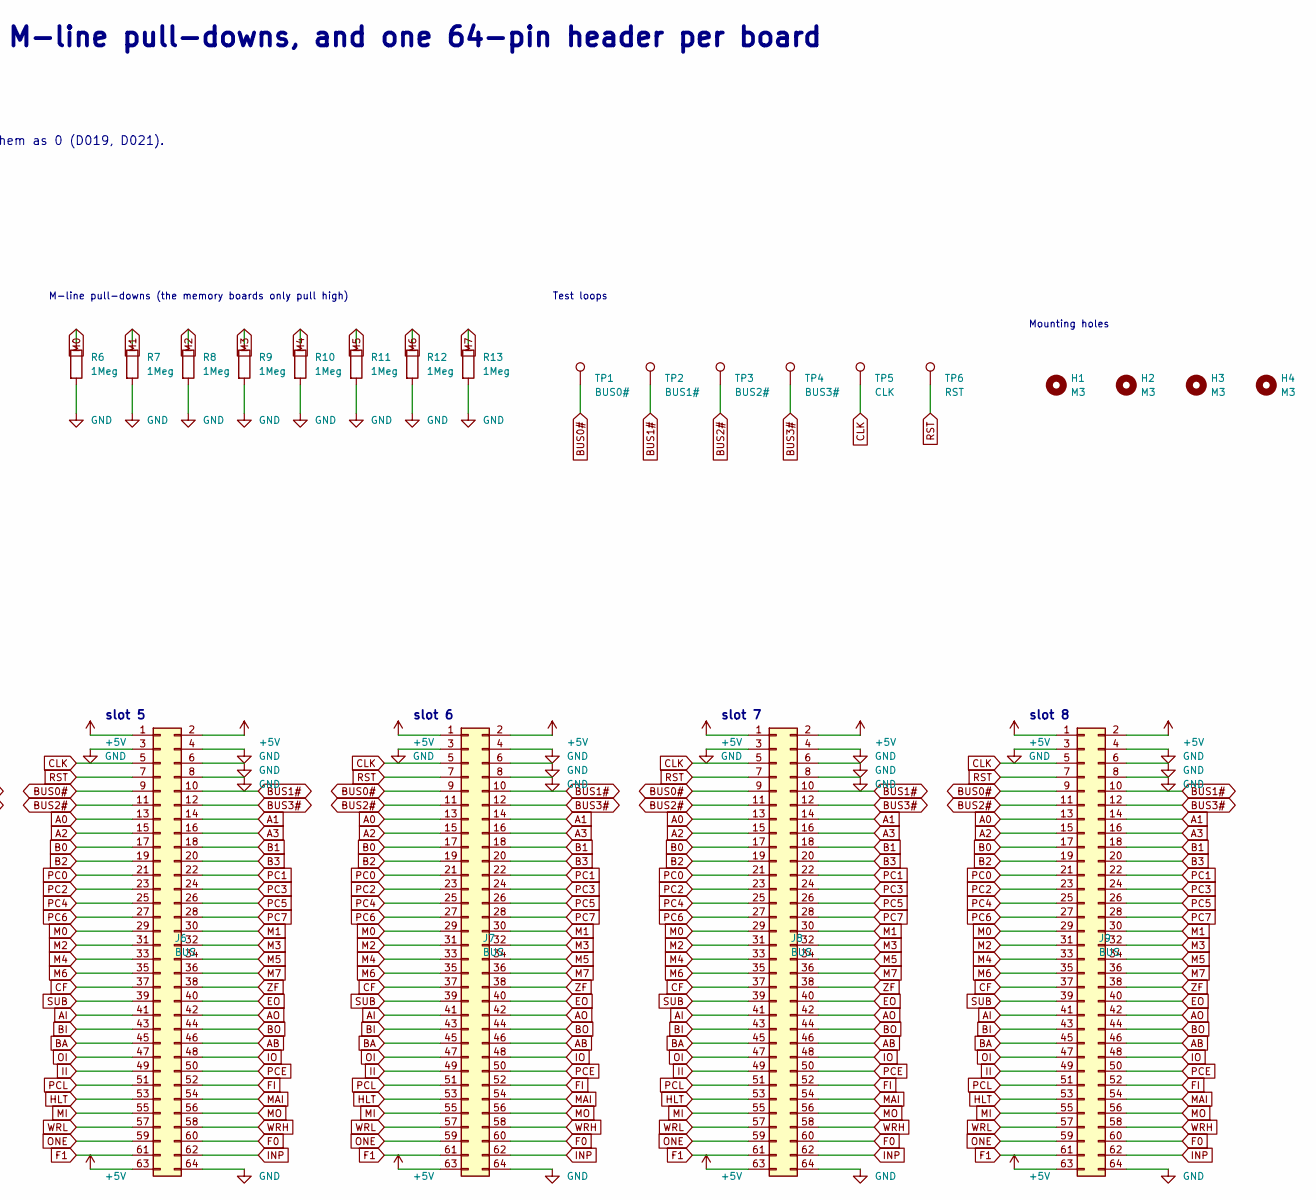
[picture p95: schematic hub.kicad_sch, part in row 1, column 2]

Parts:
C1: 100n; C_Disc_D5.0mm_W2.5mm_P2.50mm
C2: 100u; CP_Radial_D5.0mm_P2.00mm
D1: LED; LED_D3.0mm
F1: 750mA; Fuse_BelFuse_0ZRE0075FF_L11.5mm_W4.8mm
H1, H2, H3, H4: M3; MountingHole_3.2mm_M3_Pad
J1: USB_B; USB_B_OST_USB-B1HSxx_Horizontal
J2, J3, J4, J5, J6, J7, J8, J9: BUS; IDC-Header_2x32_P2.54mm_Vertical
R1: 1k; R_Axial_DIN0207_L6.3mm_D2.5mm_P5.08mm_Vertical
R2, R3, R4, R5: 10k; R_Axial_DIN0207_L6.3mm_D2.5mm_P5.08mm_Vertical
R6, R7, R8, R9, R10, R11, R12, R13: 1Meg; R_Axial_DIN0207_L6.3mm_D2.5mm_P5.08mm_Vertical
TP1: BUS0#; TestPoint_Loop_D2.50mm_Drill1.0mm
TP2: BUS1#; TestPoint_Loop_D2.50mm_Drill1.0mm
TP3: BUS2#; TestPoint_Loop_D2.50mm_Drill1.0mm
TP4: BUS3#; TestPoint_Loop_D2.50mm_Drill1.0mm
TP5: CLK; TestPoint_Loop_D2.50mm_Drill1.0mm
TP6: RST; TestPoint_Loop_D2.50mm_Drill1.0mm

Connections:
+5V: C1.1, C2.1, F1.2, J2.1, J2.2, J2.63, J3.1, J3.2, J3.63, J4.1, J4.2, J4.63, J5.1, J5.2, J5.63, J6.1, J6.2, J6.63, J7.1, J7.2, J7.63, J8.1, J8.2, J8.63, J9.1, J9.2, J9.63, R1.1, R2.1, R3.1, R4.1, R5.1
A0: J2.13, J3.13, J4.13, J5.13, J6.13, J7.13, J8.13, J9.13
A1: J2.14, J3.14, J4.14, J5.14, J6.14, J7.14, J8.14, J9.14
A2: J2.15, J3.15, J4.15, J5.15, J6.15, J7.15, J8.15, J9.15
A3: J2.16, J3.16, J4.16, J5.16, J6.16, J7.16, J8.16, J9.16
AB: J2.46, J3.46, J4.46, J5.46, J6.46, J7.46, J8.46, J9.46
AI: J2.41, J3.41, J4.41, J5.41, J6.41, J7.41, J8.41, J9.41
AO: J2.42, J3.42, J4.42, J5.42, J6.42, J7.42, J8.42, J9.42
B0: J2.17, J3.17, J4.17, J5.17, J6.17, J7.17, J8.17, J9.17
B1: J2.18, J3.18, J4.18, J5.18, J6.18, J7.18, J8.18, J9.18
B2: J2.19, J3.19, J4.19, J5.19, J6.19, J7.19, J8.19, J9.19
B3: J2.20, J3.20, J4.20, J5.20, J6.20, J7.20, J8.20, J9.20
BA: J2.45, J3.45, J4.45, J5.45, J6.45, J7.45, J8.45, J9.45
BI: J2.43, J3.43, J4.43, J5.43, J6.43, J7.43, J8.43, J9.43
BO: J2.44, J3.44, J4.44, J5.44, J6.44, J7.44, J8.44, J9.44
BUS0#: J2.9, J3.9, J4.9, J5.9, J6.9, J7.9, J8.9, J9.9, R2.2, TP1.1
BUS1#: J2.10, J3.10, J4.10, J5.10, J6.10, J7.10, J8.10, J9.10, R3.2, TP2.1
BUS2#: J2.11, J3.11, J4.11, J5.11, J6.11, J7.11, J8.11, J9.11, R4.2, TP3.1
BUS3#: J2.12, J3.12, J4.12, J5.12, J6.12, J7.12, J8.12, J9.12, R5.2, TP4.1
CF: J2.37, J3.37, J4.37, J5.37, J6.37, J7.37, J8.37, J9.37
CLK: J2.5, J3.5, J4.5, J5.5, J6.5, J7.5, J8.5, J9.5, TP5.1
EO: J2.40, J3.40, J4.40, J5.40, J6.40, J7.40, J8.40, J9.40
F0: J2.60, J3.60, J4.60, J5.60, J6.60, J7.60, J8.60, J9.60
F1: J2.61, J3.61, J4.61, J5.61, J6.61, J7.61, J8.61, J9.61
FI: J2.52, J3.52, J4.52, J5.52, J6.52, J7.52, J8.52, J9.52
GND: C1.2, C2.2, D1.1 (K), J1.4 (GND), J1.SH (Shield), J2.3, J2.4, J2.6, J2.8, J2.64, J3.3, J3.4, J3.6, J3.8, J3.64, J4.3, J4.4, J4.6, J4.8, J4.64, J5.3, J5.4, J5.6, J5.8, J5.64, J6.3, J6.4, J6.6, J6.8, J6.64, J7.3, J7.4, J7.6, J7.8, J7.64, J8.3, J8.4, J8.6, J8.8, J8.64, J9.3, J9.4, J9.6, J9.8, J9.64, R6.2, R7.2, R8.2, R9.2, R10.2, R11.2, R12.2, R13.2
HLT: J2.53, J3.53, J4.53, J5.53, J6.53, J7.53, J8.53, J9.53
II: J2.49, J3.49, J4.49, J5.49, J6.49, J7.49, J8.49, J9.49
INP: J2.62, J3.62, J4.62, J5.62, J6.62, J7.62, J8.62, J9.62
IO: J2.48, J3.48, J4.48, J5.48, J6.48, J7.48, J8.48, J9.48
M0: J2.29, J3.29, J4.29, J5.29, J6.29, J7.29, J8.29, J9.29, R6.1
M1: J2.30, J3.30, J4.30, J5.30, J6.30, J7.30, J8.30, J9.30, R7.1
M2: J2.31, J3.31, J4.31, J5.31, J6.31, J7.31, J8.31, J9.31, R8.1
M3: J2.32, J3.32, J4.32, J5.32, J6.32, J7.32, J8.32, J9.32, R9.1
M4: J2.33, J3.33, J4.33, J5.33, J6.33, J7.33, J8.33, J9.33, R10.1
M5: J2.34, J3.34, J4.34, J5.34, J6.34, J7.34, J8.34, J9.34, R11.1
M6: J2.35, J3.35, J4.35, J5.35, J6.35, J7.35, J8.35, J9.35, R12.1
M7: J2.36, J3.36, J4.36, J5.36, J6.36, J7.36, J8.36, J9.36, R13.1
MAI: J2.54, J3.54, J4.54, J5.54, J6.54, J7.54, J8.54, J9.54
MI: J2.55, J3.55, J4.55, J5.55, J6.55, J7.55, J8.55, J9.55
MO: J2.56, J3.56, J4.56, J5.56, J6.56, J7.56, J8.56, J9.56
unnamed: D1.2 (A), R1.2
OI: J2.47, J3.47, J4.47, J5.47, J6.47, J7.47, J8.47, J9.47
ONE: J2.59, J3.59, J4.59, J5.59, J6.59, J7.59, J8.59, J9.59
PC0: J2.21, J3.21, J4.21, J5.21, J6.21, J7.21, J8.21, J9.21
PC1: J2.22, J3.22, J4.22, J5.22, J6.22, J7.22, J8.22, J9.22
PC2: J2.23, J3.23, J4.23, J5.23, J6.23, J7.23, J8.23, J9.23
PC3: J2.24, J3.24, J4.24, J5.24, J6.24, J7.24, J8.24, J9.24
PC4: J2.25, J3.25, J4.25, J5.25, J6.25, J7.25, J8.25, J9.25
PC5: J2.26, J3.26, J4.26, J5.26, J6.26, J7.26, J8.26, J9.26
PC6: J2.27, J3.27, J4.27, J5.27, J6.27, J7.27, J8.27, J9.27
PC7: J2.28, J3.28, J4.28, J5.28, J6.28, J7.28, J8.28, J9.28
PCE: J2.50, J3.50, J4.50, J5.50, J6.50, J7.50, J8.50, J9.50
PCL: J2.51, J3.51, J4.51, J5.51, J6.51, J7.51, J8.51, J9.51
RST: J2.7, J3.7, J4.7, J5.7, J6.7, J7.7, J8.7, J9.7, TP6.1
SUB: J2.39, J3.39, J4.39, J5.39, J6.39, J7.39, J8.39, J9.39
VBUS: F1.1, J1.1 (VBUS)
WRH: J2.58, J3.58, J4.58, J5.58, J6.58, J7.58, J8.58, J9.58
WRL: J2.57, J3.57, J4.57, J5.57, J6.57, J7.57, J8.57, J9.57
ZF: J2.38, J3.38, J4.38, J5.38, J6.38, J7.38, J8.38, J9.38

Notes on the sheet:
NIBBLE BOARD 07 - BUS HUB: power entry, the four bus pull-ups, the eight M-line pull-downs, and one 64-pin header per board
No logic on this board. 8 identical headers wired pin-for-pin; every board plugs in with a straight 64-way ribbon cable (docs/bus-header.md). Power: USB-B 5 V through a 750 mA polyfuse (the USB plug is the power switch). The BUS0#..BUS3# pull-ups (10k) live here and nowhere else. The M0..M7 pull-do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
power
Decoupling
Bus pull-ups (the only ones in the machine)
M-line pull-downs (the memory boards only pull high)
Test loops
Mounting holes
slot 1
slot 2
slot 3
slot 4
slot 5
slot 6
slot 7
slot 8

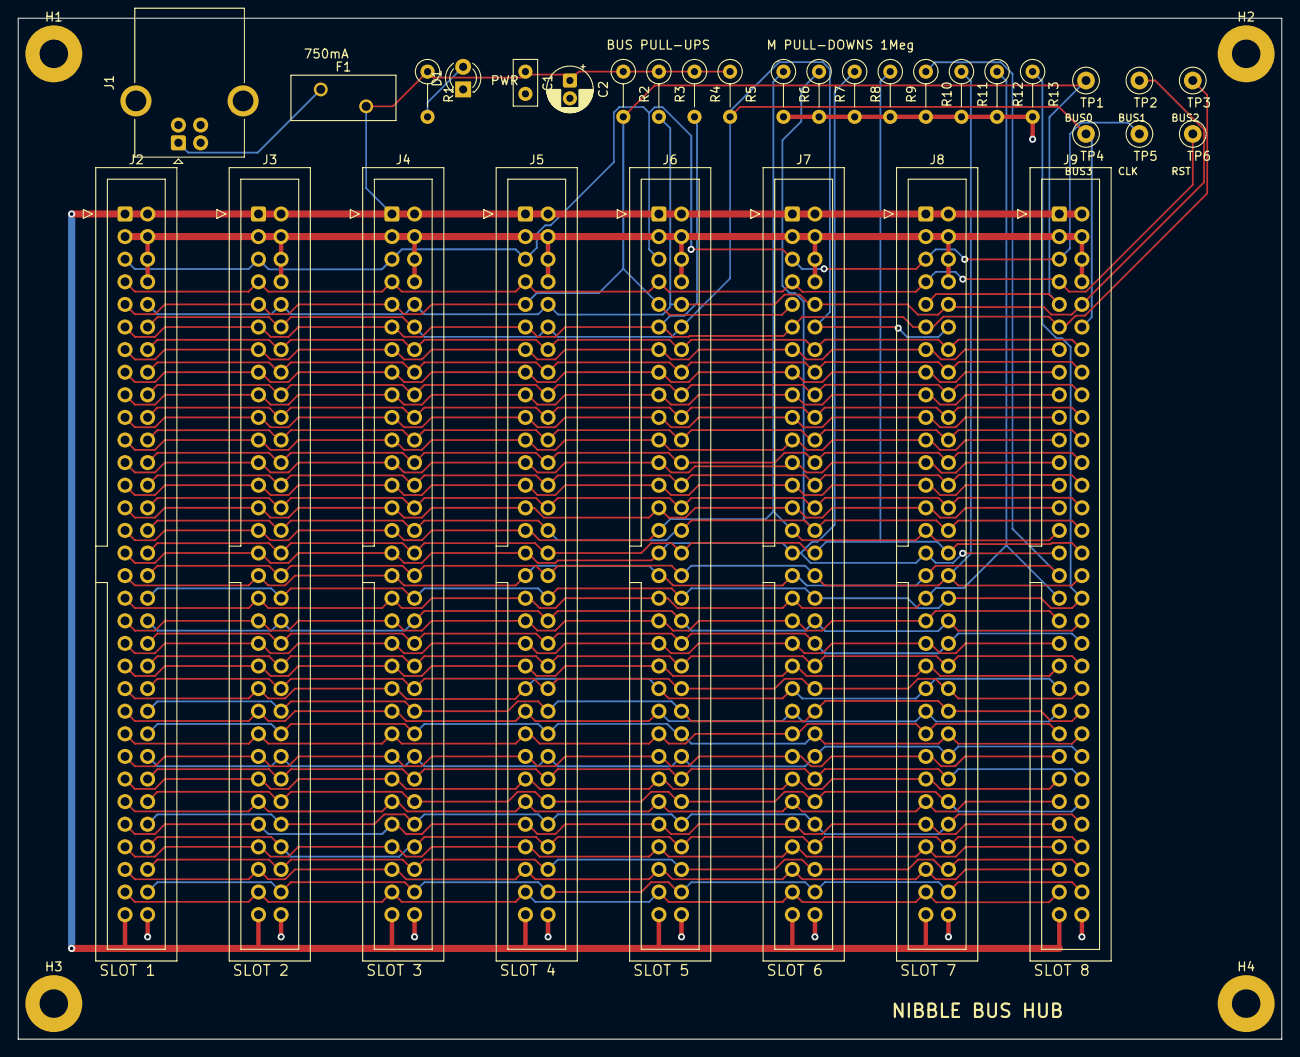
[picture p96: board boards/07-hub/hub.kicad_pcb from above]

Board: 2 copper layers, 142.0 x 114.7 mm, 36 parts (0 on the bottom side), 60 nets.
