nikolafilip/nibble/experiments/muldiv/Untitled.kicad_sch

## KiCad design experiments/muldiv/Untitled.kicad_sch (2026-09-09)

Schematic: Untitled.kicad_sch

Parts:
Q1, Q2, Q3, Q4, Q5, Q6, Q7, Q8, Q9, Q10, Q11, Q12, Q13, Q14, Q15, Q16, Q17, Q18, Q19, Q20, Q21, Q22, Q23, Q24, Q25, Q26, Q27, Q28, Q29, Q30, Q31, Q32, Q33, Q34, Q35, Q36, Q37, Q38, Q39, Q40, Q41, Q42, Q43, Q44, Q45, Q46, Q47, Q48, Q49, Q50, Q51, Q52, Q53, Q54, Q55, Q56, Q57, Q58, Q59, Q60, Q61, Q62, Q63, Q64, Q65, Q66, Q67, Q68, Q69, Q70, Q71, Q72, Q73, Q74, Q75, Q76, Q77, Q78, Q79, Q80, Q81, Q82, Q83, Q85, Q86, Q87, Q88, Q89, Q90, Q92, Q93, Q94, Q95, Q97, Q98, Q99, Q100, Q101, Q102, Q103, Q104, Q105, Q106, Q107, Q108, Q112, Q113, Q114, Q115, Q116, Q117, Q118, Q119, Q120, Q121, Q122, Q123, Q124, Q125, Q126, Q127, Q128, Q129, Q130, Q131, Q132, Q133, Q134, Q135, Q136, Q137, Q138, Q139, Q140, Q141, Q142, Q143, Q144, Q145, Q146, Q147, Q148, Q149, Q150, Q151, Q152, Q153, Q154, Q155, Q156, Q157, Q158, Q159, Q160, Q161, Q162, Q163, Q164, Q165, Q166, Q167, Q168, Q169, Q170, Q171, Q172, Q173, Q174, Q175, Q176, Q177, Q178, Q179, Q180, Q181, Q182, Q183, Q184, Q185, Q186, Q187, Q188, Q189, Q190, Q191, Q192, Q193, Q194, Q195, Q196, Q197, Q198, Q199, Q200, Q201, Q202, Q203, Q204, Q205, Q206, Q207, Q208, Q209, Q210, Q211, Q212, Q213, Q214, Q215, Q216, Q217, Q218, Q219, Q220, Q221, Q222, Q223, Q224, Q225, Q226, Q227, Q228, Q229, Q230, Q231, Q232, Q233, Q234, Q235, Q236, Q237, Q238, Q239, Q240, Q241, Q242, Q243, Q244, Q245, Q246, Q247, Q248, Q249, Q250, Q251, Q252, Q253, Q254, Q255, Q256, Q257, Q258, Q259, Q260, Q261, Q262, Q263, Q264, Q265, Q266, Q267, Q268, Q269, Q270, Q271, Q272, Q273, Q274, Q275, Q276, Q277, Q278, Q279, Q280, Q281, Q282, Q283, Q284, Q285, Q286, Q287, Q288, Q289, Q290, Q291, Q292, Q293, Q294, Q295, Q296, Q297, Q298, Q299, Q300, Q301, Q302, Q303, Q304, Q305, Q306, Q307, Q308, Q309, Q310, Q311, Q312, Q313, Q314, Q315, Q316, Q317, Q318, Q319, Q320, Q321, Q322, Q323, Q324, Q325, Q326, Q327, Q328, Q329, Q330, Q331, Q332, Q333, Q334, Q335, Q336, Q337, Q338, Q339, Q340, Q341, Q342, Q343, Q344, Q345, Q346, Q347, Q348, Q349, Q350, Q351, Q352, Q353, Q354, Q355, Q356, Q357, Q358, Q359, Q360, Q361, Q362, Q363, Q364, Q365, Q366, Q367, Q368, Q369, Q370, Q371, Q372, Q373, Q374, Q375, Q376, Q377, Q378, Q379, Q388, Q389, Q390, Q391, Q392, Q393, Q394, Q395, Q396, Q397, Q398, Q399, Q400, Q401, Q402, Q403, Q404, Q405, Q406, Q407, Q408, Q409, Q410, Q411, Q412, Q413, Q414, Q415, Q416, Q417, Q418, Q419, Q420, Q421, Q422, Q423, Q424, Q425, Q426, Q427: 2N3904; TO-92_Inline
R1, R5, R8, R18, R21, R25, R29, R34, R37, R42, R45, R49, R61, R62, R63, R70, R71, R78, R82, R86, R98, R99, R100, R107, R108, R111, R115, R127, R128, R129, R136, R137, R144, R148, R152, R164, R165, R166, R173, R174, R177, R181, R193, R194, R195, R202, R203, R210, R218, R233, R245, R259, R266, R275, R290, R298, R299, R304, R307, R311, R319, R320, R325, R328, R332, R340, R341, R346, R349, R353, R365, R366, R367, R374, R375, R378, R382, R394, R395, R396, R403, R404, R407, R411, R423, R424, R425, R432, R433, R436, R439, R444, R447, R451, R459, R460, R465, R468, R472, R480, R481, R486, R489, R493, R501, R502, R507, R510, R514, R526, R527, R528, R535, R536, R539, R804, R807, R820, R823, R832, R835, R844, R847, R880, R881, R882, R884, R891, R893, R894, R895, R898, R901, R904, R907, R910, R913, R916, R919, R922, R925, R928, R931, R934, R937, R940, R943, R946, R949, R952, R955, R958, R961, R964, R967, R970, R973, R976, R979, R982, R985, R988, R991, R1056, R1064, R1070, R1079, R1088, R1092, R1093, R1094, R1097, R1098, R1100, R1103, R1107, R1109, R1110, R1111: 4.7k; R_Axial_DIN0207_L6.3mm_D2.5mm_P5.08mm_Vertical
R2, R3, R4, R6, R7, R9, R10, R11, R20, R23, R26, R30, R31, R35, R38, R39, R43, R46, R48, R51, R52, R53, R54, R55, R64, R65, R66, R72, R75, R77, R80, R83, R85, R88, R89, R90, R91, R92, R101, R102, R103, R109, R112, R114, R117, R118, R119, R120, R121, R130, R131, R132, R138, R141, R143, R146, R149, R151, R154, R155, R156, R157, R158, R167, R168, R169, R175, R178, R180, R183, R184, R185, R186, R187, R196, R197, R198, R204, R207, R209, R212, R215, R217, R223, R225, R226, R228, R231, R232, R239, R240, R243, R244, R251, R252, R255, R256, R257, R258, R264, R265, R269, R270, R273, R274, R287, R289, R292, R293, R294, R300, R301, R305, R308, R310, R313, R314, R315, R321, R322, R326, R329, R331, R334, R335, R336, R342, R343, R347, R350, R352, R355, R356, R357, R358, R359, R368, R369, R370, R376, R379, R381, R384, R385, R386, R387, R388, R397, R398, R399, R405, R408, R410, R413, R414, R415, R416, R417, R426, R427, R428, R434, R437, R440, R441, R445, R448, R450, R453, R454, R455, R461, R462, R466, R469, R471, R474, R475, R476, R482, R483, R487, R490, R492, R495, R496, R497, R503, R504, R508, R511, R513, R516, R517, R518, R519, R520, R529, R530, R531, R537, R800, R801, R805, R808, R810, R812, R813, R814, R815, R821, R824, R825, R826, R827, R833, R836, R837, R838, R839, R845, R848, R849, R850, R851, R852, R853, R854, R855, R856, R857, R858, R859, R864, R865, R866, R867, R883, R885, R887, R889, R896, R899, R902, R905, R908, R911, R914, R917, R920, R923, R926, R929, R932, R935, R938, R941, R944, R947, R950, R953, R956, R959, R962, R965, R968, R971, R974, R977, R980, R983, R986, R989, R1016, R1017, R1018, R1019, R1020, R1021, R1022, R1023, R1024, R1025, R1026, R1027, R1032, R1033, R1034, R1035, R1044, R1045, R1046, R1047, R1052, R1053, R1054, R1055, R1057, R1058, R1059, R1060, R1066, R1067, R1068, R1069, R1074, R1081, R1086, R1090, R1096, R1099, R1102, R1105: 10k; R_Axial_DIN0207_L6.3mm_D2.5mm_P5.08mm_Vertical
R12, R13, R14, R15, R16, R17, R19, R22, R24, R27, R28, R32, R33, R36, R40, R41, R44, R47, R50, R56, R57, R58, R59, R60, R67, R68, R69, R73, R76, R79, R81, R84, R87, R93, R94, R95, R96, R97, R104, R105, R106, R110, R113, R116, R122, R123, R124, R125, R126, R133, R134, R135, R139, R142, R145, R147, R150, R153, R159, R160, R161, R162, R163, R170, R171, R172, R176, R179, R182, R188, R189, R190, R191, R192, R199, R200, R201, R205, R208, R211, R213, R216, R219, R224, R227, R229, R230, R234, R235, R241, R242, R246, R247, R253, R254, R260, R261, R262, R263, R267, R268, R271, R272, R276, R277, R288, R291, R295, R296, R297, R302, R303, R306, R309, R312, R316, R317, R318, R323, R324, R327, R330, R333, R337, R338, R339, R344, R345, R348, R351, R354, R360, R361, R362, R363, R364, R371, R372, R373, R377, R380, R383, R389, R390, R391, R392, R393, R400, R401, R402, R406, R409, R412, R418, R419, R420, R421, R422, R429, R430, R431, R435, R438, R442, R443, R446, R449, R452, R456, R457, R458, R463, R464, R467, R470, R473, R477, R478, R479, R484, R485, R488, R491, R494, R498, R499, R500, R505, R506, R509, R512, R515, R521, R522, R523, R524, R525, R532, R533, R534, R538, R802, R803, R806, R809, R811, R816, R817, R818, R819, R822, R828, R829, R830, R831, R834, R840, R841, R842, R843, R846, R860, R861, R862, R863, R868, R869, R870, R871, R872, R873, R874, R875, R876, R877, R878, R879, R886, R888, R890, R892, R897, R900, R903, R906, R909, R912, R915, R918, R921, R924, R927, R930, R933, R936, R939, R942, R945, R948, R951, R954, R957, R960, R963, R966, R969, R972, R975, R978, R981, R984, R987, R990, R1028, R1029, R1030, R1031, R1036, R1037, R1038, R1039, R1040, R1041, R1042, R1043, R1048, R1049, R1050, R1051, R1061, R1062, R1063, R1065, R1071, R1072, R1073, R1075, R1076, R1077, R1078, R1080, R1082, R1083, R1084, R1085, R1087, R1089, R1091, R1095, R1101, R1104, R1106, R1108: 22k; R_Axial_DIN0207_L6.3mm_D2.5mm_P5.08mm_Vertical
R74, R140, R206, R214: 2.2k; R_Axial_DIN0207_L6.3mm_D2.5mm_P5.08mm_Vertical
R540, R542, R546, R547, R548, R549, R556, R558, R559, R560, R561, R569, R572, R573, R574, R575, R582, R583, R584, R585, R592, R594, R598, R599, R600, R601, R608, R610, R611, R612, R613, R621, R624, R625, R626, R627, R634, R635, R636, R637, R644, R646, R650, R651, R652, R653, R660, R662, R663, R664, R665, R673, R676, R677, R678, R679, R686, R687, R688, R689, R696, R698, R702, R703, R704, R705, R712, R714, R715, R716, R717, R725, R728, R729, R730, R731, R738, R739, R740, R741, R748, R750, R754, R755, R756, R757, R764, R766, R767, R768, R769, R777, R780, R781, R782, R783, R790, R791, R792, R793: 10k
R541, R544, R550, R551, R552, R553, R557, R563, R564, R565, R566, R570, R576, R577, R578, R579, R586, R587, R588, R589, R593, R596, R602, R603, R604, R605, R609, R615, R616, R617, R618, R622, R628, R629, R630, R631, R638, R639, R640, R641, R645, R648, R654, R655, R656, R657, R661, R667, R668, R669, R670, R674, R680, R681, R682, R683, R690, R691, R692, R693, R697, R700, R706, R707, R708, R709, R713, R719, R720, R721, R722, R726, R732, R733, R734, R735, R742, R743, R744, R745, R749, R752, R758, R759, R760, R761, R765, R771, R772, R773, R774, R778, R784, R785, R786, R787, R794, R795, R796, R797: 22k
R543, R590, R595, R642, R647, R694, R699, R746, R751, R798: 2.2k
R545, R554, R555, R562, R567, R568, R571, R580, R581, R591, R597, R606, R607, R614, R619, R620, R623, R632, R633, R643, R649, R658, R659, R666, R671, R672, R675, R684, R685, R695, R701, R710, R711, R718, R723, R724, R727, R736, R737, R747, R753, R762, R763, R770, R775, R776, R779, R788, R789, R799: 4.7k
V1: 5

Connections:
+5V: R1.1, R2.1, R3.1, R5.1, R7.1, R8.1, R9.1, R18.1, R21.1, R25.1, R29.1, R34.1, R37.1, R42.1, R45.1, R49.1, R61.1, R62.1, R63.1, R70.1, R71.1, R74.1, R78.1, R82.1, R86.1, R98.1, R99.1, R100.1, R107.1, R108.1, R111.1, R115.1, R127.1, R128.1, R129.1, R136.1, R137.1, R140.1, R144.1, R148.1, R152.1, R164.1, R165.1, R166.1, R173.1, R174.1, R177.1, R181.1, R193.1, R194.1, R195.1, R202.1, R203.1, R206.1, R210.1, R214.1, R218.1, R233.1, R245.1, R259.1, R266.1, R275.1, R290.1, R298.1, R299.1, R304.1, R307.1, R311.1, R319.1, R320.1, R325.1, R328.1, R332.1, R340.1, R341.1, R346.1, R349.1, R353.1, R365.1, R366.1, R367.1, R374.1, R375.1, R378.1, R382.1, R394.1, R395.1, R396.1, R403.1, R404.1, R407.1, R411.1, R423.1, R424.1, R425.1, R432.1, R433.1, R436.1, R439.1, R444.1, R447.1, R451.1, R459.1, R460.1, R465.1, R468.1, R472.1, R480.1, R481.1, R486.1, R489.1, R493.1, R501.1, R502.1, R507.1, R510.1, R514.1, R526.1, R527.1, R528.1, R535.1, R536.1, R539.1, R543.1, R545.1, R554.1, R555.1, R562.1, R567.1, R568.1, R571.1, R580.1, R581.1, R590.1, R591.1, R595.1, R597.1, R606.1, R607.1, R614.1, R619.1, R620.1, R623.1, R632.1, R633.1, R642.1, R643.1, R647.1, R649.1, R658.1, R659.1, R666.1, R671.1, R672.1, R675.1, R684.1, R685.1, R694.1, R695.1, R699.1, R701.1, R710.1, R711.1, R718.1, R723.1, R724.1, R727.1, R736.1, R737.1, R746.1, R747.1, R751.1, R753.1, R762.1, R763.1, R770.1, R775.1, R776.1, R779.1, R788.1, R789.1, R798.1, R799.1, R804.1, R807.1, R820.1, R823.1, R832.1, R835.1, R844.1, R847.1, R880.1, R881.1, R882.1, R884.1, R891.1, R893.1, R894.1, R895.1, R898.1, R901.1, R904.1, R907.1, R910.1, R913.1, R916.1, R919.1, R922.1, R925.1, R928.1, R931.1, R934.1, R937.1, R940.1, R943.1, R946.1, R949.1, R952.1, R955.1, R958.1, R961.1, R964.1, R967.1, R970.1, R973.1, R976.1, R979.1, R982.1, R985.1, R988.1, R991.1, R1056.1, R1064.1, R1070.1, R1079.1, R1088.1, R1092.1, R1093.1, R1094.1, R1097.1, R1098.1, R1100.1, R1103.1, R1107.1, R1109.1, R1110.1, R1111.1, V1.1
A0: R6.1, R10.1, R38.1
A1: R83.1, R88.1, R90.1
A2: R149.1, R154.1, R156.1
B0: Q119.3 (C), R20.1, R26.1, R39.1, R307.2
B1: Q127.3 (C), R85.1, R89.1, R91.1, R328.2
B2: Q135.3 (C), R151.1, R155.1, R157.1, R349.2
Cin1: Q31.3 (C), R82.2, R114.1, R118.1, R120.1
Cin2: Q56.3 (C), R148.2, R180.1, R184.1, R186.1
EB0: R289.1, R293.1
EB1: R310.1, R314.1
EB2: R331.1, R335.1
ENCA_N0: Q92.3 (C), Q93.3 (C), Q94.3 (C), Q95.3 (C), R245.2
ENCA_N1: Q87.3 (C), Q88.3 (C), Q89.3 (C), Q90.3 (C), R233.2
ENCA_N2: Q82.3 (C), Q83.3 (C), Q85.3 (C), Q86.3 (C), R218.2
ENCB_N0: Q105.3 (C), Q106.3 (C), Q107.3 (C), Q108.3 (C), R275.2
ENCB_N1: Q101.3 (C), Q102.3 (C), Q103.3 (C), Q104.3 (C), R266.2
ENCB_N2: Q97.3 (C), Q98.3 (C), Q99.3 (C), Q100.3 (C), R259.2
F_OUT0: Q310.3 (C), R807.2
F_OUT1: Q317.3 (C), R823.2
F_OUT2: Q322.3 (C), R835.2
F_OUT3: Q327.3 (C), R847.2
F_OUT4: Q344.3 (C), R891.2
F_OUT5: Q345.3 (C), R893.2
F_OUT6: Q346.3 (C), R894.2
F_OUT7: Q347.3 (C), R895.2
F_OUT8: Q416.3 (C), R1094.2
F_OUT9: Q421.3 (C), R1098.2
F_OUT10: Q422.3 (C), R1100.2
F_OUT11: Q423.3 (C), R1103.2
F_OUT12: Q424.3 (C), R1107.2
F_OUT13: Q425.3 (C), R1109.2
F_OUT14: Q426.3 (C), R1110.2
F_OUT15: Q427.3 (C), R1111.2
GND: Q2.1 (E), Q3.1 (E), Q4.1 (E), Q5.1 (E), Q6.1 (E), Q7.1 (E), Q8.1 (E), Q9.1 (E), Q11.1 (E), Q13.1 (E), Q14.1 (E), Q16.1 (E), Q17.1 (E), Q18.1 (E), Q19.1 (E), Q20.1 (E), Q22.1 (E), Q24.1 (E), Q25.1 (E), Q27.1 (E), Q28.1 (E), Q29.1 (E), Q30.1 (E), Q31.1 (E), Q32.1 (E), Q33.1 (E), Q34.1 (E), Q36.1 (E), Q38.1 (E), Q39.1 (E), Q41.1 (E), Q42.1 (E), Q43.1 (E), Q44.1 (E), Q45.1 (E), Q47.1 (E), Q49.1 (E), Q50.1 (E), Q52.1 (E), Q53.1 (E), Q54.1 (E), Q55.1 (E), Q56.1 (E), Q57.1 (E), Q58.1 (E), Q59.1 (E), Q61.1 (E), Q63.1 (E), Q64.1 (E), Q66.1 (E), Q67.1 (E), Q68.1 (E), Q69.1 (E), Q70.1 (E), Q72.1 (E), Q74.1 (E), Q75.1 (E), Q77.1 (E), Q78.1 (E), Q79.1 (E), Q80.1 (E), Q81.1 (E), Q82.1 (E), Q83.1 (E), Q85.1 (E), Q86.1 (E), Q87.1 (E), Q88.1 (E), Q89.1 (E), Q90.1 (E), Q92.1 (E), Q93.1 (E), Q94.1 (E), Q95.1 (E), Q97.1 (E), Q98.1 (E), Q99.1 (E), Q100.1 (E), Q101.1 (E), Q102.1 (E), Q103.1 (E), Q104.1 (E), Q105.1 (E), Q106.1 (E), Q107.1 (E), Q108.1 (E), Q112.1 (E), Q113.1 (E), Q114.1 (E), Q116.1 (E), Q118.1 (E), Q119.1 (E), Q120.1 (E), Q121.1 (E), Q122.1 (E), Q124.1 (E), Q126.1 (E), Q127.1 (E), Q128.1 (E), Q129.1 (E), Q130.1 (E), Q132.1 (E), Q134.1 (E), Q135.1 (E), Q136.1 (E), Q137.1 (E), Q138.1 (E), Q140.1 (E), Q142.1 (E), Q143.1 (E), Q145.1 (E), Q146.1 (E), Q147.1 (E), Q148.1 (E), Q149.1 (E), Q151.1 (E), Q153.1 (E), Q154.1 (E), Q156.1 (E), Q157.1 (E), Q158.1 (E), Q159.1 (E), Q160.1 (E), Q162.1 (E), Q164.1 (E), Q165.1 (E), Q167.1 (E), Q168.1 (E), Q169.1 (E), Q171.1 (E), Q172.1 (E), Q173.1 (E), Q174.1 (E), Q175.1 (E), Q177.1 (E), Q179.1 (E), Q180.1 (E), Q181.1 (E), Q182.1 (E), Q183.1 (E), Q185.1 (E), Q187.1 (E), Q188.1 (E), Q189.1 (E), Q190.1 (E), Q191.1 (E), Q193.1 (E), Q195.1 (E), Q196.1 (E), Q197.1 (E), Q198.1 (E), Q199.1 (E), Q201.1 (E), Q203.1 (E), Q204.1 (E), Q206.1 (E), Q207.1 (E), Q208.1 (E), Q209.1 (E), Q211.1 (E), Q213.1 (E), Q214.1 (E), Q216.1 (E), Q218.1 (E), Q219.1 (E), Q221.1 (E), Q223.1 (E), Q225.1 (E), Q227.1 (E), Q228.1 (E), Q229.1 (E), Q231.1 (E), Q233.1 (E), Q234.1 (E), Q236.1 (E), Q238.1 (E), Q239.1 (E), Q241.1 (E), Q243.1 (E), Q245.1 (E), Q247.1 (E), Q248.1 (E), Q249.1 (E), Q251.1 (E), Q253.1 (E), Q254.1 (E), Q256.1 (E), Q258.1 (E), Q259.1 (E), Q261.1 (E), Q263.1 (E), Q265.1 (E), Q267.1 (E), Q268.1 (E), Q269.1 (E), Q271.1 (E), Q273.1 (E), Q274.1 (E), Q276.1 (E), Q278.1 (E), Q279.1 (E), Q281.1 (E), Q283.1 (E), Q285.1 (E), Q287.1 (E), Q288.1 (E), Q289.1 (E), Q291.1 (E), Q293.1 (E), Q294.1 (E), Q296.1 (E), Q298.1 (E), Q299.1 (E), Q301.1 (E), Q303.1 (E), Q305.1 (E), Q307.1 (E), Q310.1 (E), Q312.1 (E), Q316.1 (E), Q317.1 (E), Q321.1 (E), Q322.1 (E), Q326.1 (E), Q327.1 (E), Q331.1 (E), Q335.1 (E), Q339.1 (E), Q343.1 (E), Q344.1 (E), Q345.1 (E), Q346.1 (E), Q347.1 (E), Q348.1 (E), Q349.1 (E), Q350.1 (E), Q351.1 (E), Q352.1 (E), Q353.1 (E), Q354.1 (E), Q355.1 (E), Q356.1 (E), Q357.1 (E), Q358.1 (E), Q359.1 (E), Q360.1 (E), Q361.1 (E), Q362.1 (E), Q363.1 (E), Q364.1 (E), Q365.1 (E), Q366.1 (E), Q367.1 (E), Q368.1 (E), Q369.1 (E), Q370.1 (E), Q371.1 (E), Q372.1 (E), Q373.1 (E), Q374.1 (E), Q375.1 (E), Q376.1 (E), Q377.1 (E), Q378.1 (E), Q379.1 (E), Q391.1 (E), Q395.1 (E), Q399.1 (E), Q403.1 (E), Q407.1 (E), Q411.1 (E), Q415.1 (E), Q416.1 (E), Q420.1 (E), Q421.1 (E), Q422.1 (E), Q423.1 (E), Q424.1 (E), Q425.1 (E), Q426.1 (E), Q427.1 (E), R12.1, R13.1, R14.1, R15.1, R16.1, R17.1, R19.1, R22.1, R24.1, R27.1, R28.1, R32.1, R33.1, R36.1, R40.1, R41.1, R44.1, R47.1, R50.1, R56.1, R57.1, R58.1, R59.1, R60.1, R67.1, R68.1, R69.1, R73.1, R76.1, R79.1, R81.1, R84.1, R87.1, R93.1, R94.1, R95.1, R96.1, R97.1, R104.1, R105.1, R106.1, R110.1, R113.1, R116.1, R122.1, R123.1, R124.1, R125.1, R126.1, R133.1, R134.1, R135.1, R139.1, R142.1, R145.1, R147.1, R150.1, R153.1, R159.1, R160.1, R161.1, R162.1, R163.1, R170.1, R171.1, R172.1, R176.1, R179.1, R182.1, R188.1, R189.1, R190.1, R191.1, R192.1, R199.1, R200.1, R201.1, R205.1, R208.1, R211.1, R213.1, R216.1, R219.1, R224.1, R227.1, R229.1, R230.1, R234.1, R235.1, R241.1, R242.1, R246.1, R247.1, R253.1, R254.1, R260.1, R261.1, R262.1, R263.1, R267.1, R268.1, R271.1, R272.1, R276.1, R277.1, R288.1, R291.1, R295.1, R296.1, R297.1, R302.1, R303.1, R306.1, R309.1, R312.1, R316.1, R317.1, R318.1, R323.1, R324.1, R327.1, R330.1, R333.1, R337.1, R338.1, R339.1, R344.1, R345.1, R348.1, R351.1, R354.1, R360.1, R361.1, R362.1, R363.1, R364.1, R371.1, R372.1, R373.1, R377.1, R380.1, R383.1, R389.1, R390.1, R391.1, R392.1, R393.1, R400.1, R401.1, R402.1, R406.1, R409.1, R412.1, R418.1, R419.1, R420.1, R421.1, R422.1, R429.1, R430.1, R431.1, R435.1, R438.1, R442.1, R443.1, R446.1, R449.1, R452.1, R456.1, R457.1, R458.1, R463.1, R464.1, R467.1, R470.1, R473.1, R477.1, R478.1, R479.1, R484.1, R485.1, R488.1, R491.1, R494.1, R498.1, R499.1, R500.1, R505.1, R506.1, R509.1, R512.1, R515.1, R521.1, R522.1, R523.1, R524.1, R525.1, R532.1, R533.1, R534.1, R538.1, R541.1, R544.1, R550.1, R551.1, R552.1, R553.1, R557.1, R563.1, R564.1, R565.1, R566.1, R570.1, R576.1, R577.1, R578.1, R579.1, R586.1, R587.1, R588.1, R589.1, R593.1, R596.1, R602.1, R603.1, R604.1, R605.1, R609.1, R615.1, R616.1, R617.1, R618.1, R622.1, R628.1, R629.1, R630.1, R631.1, R638.1, R639.1, R640.1, R641.1, R645.1, R648.1, R654.1, R655.1, R656.1, R657.1, R661.1, R667.1, R668.1, R669.1, R670.1, R674.1, R680.1, R681.1, R682.1, R683.1, R690.1, R691.1, R692.1, R693.1, R697.1, R700.1, R706.1, R707.1, R708.1, R709.1, R713.1, R719.1, R720.1, R721.1, R722.1, R726.1, R732.1, R733.1, R734.1, R735.1, R742.1, R743.1, R744.1, R745.1, R749.1, R752.1, R758.1, R759.1, R760.1, R761.1, R765.1, R771.1, R772.1, R773.1, R774.1, R778.1, R784.1, R785.1, R786.1, R787.1, R794.1, R795.1, R796.1, R797.1, R802.1, R803.1, R806.1, R809.1, R811.1, R816.1, R817.1, R818.1, R819.1, R822.1, R828.1, R829.1, R830.1, R831.1, R834.1, R840.1, R841.1, R842.1, R843.1, R846.1, R860.1, R861.1, R862.1, R863.1, R868.1, R869.1, R870.1, R871.1, R872.1, R873.1, R874.1, R875.1, R876.1, R877.1, R878.1, R879.1, R886.1, R888.1, R890.1, R892.1, R897.1, R900.1, R903.1, R906.1, R909.1, R912.1, R915.1, R918.1, R921.1, R924.1, R927.1, R930.1, R933.1, R936.1, R939.1, R942.1, R945.1, R948.1, R951.1, R954.1, R957.1, R960.1, R963.1, R966.1, R969.1, R972.1, R975.1, R978.1, R981.1, R984.1, R987.1, R990.1, R1028.1, R1029.1, R1030.1, R1031.1, R1036.1, R1037.1, R1038.1, R1039.1, R1040.1, R1041.1, R1042.1, R1043.1, R1048.1, R1049.1, R1050.1, R1051.1, R1061.1, R1062.1, R1063.1, R1065.1, R1071.1, R1072.1, R1073.1, R1075.1, R1076.1, R1077.1, R1078.1, R1080.1, R1082.1, R1083.1, R1084.1, R1085.1, R1087.1, R1089.1, R1091.1, R1095.1, R1101.1, R1104.1, R1106.1, R1108.1, V1.2
MEMCLK: R540.1, R592.1, R644.1, R696.1, R748.1
unnamed: Q1.1 (E), Q2.3 (C)
unnamed: Q1.2 (B), R2.2, R12.2
unnamed: Q1.3 (C), R1.2, R4.1
unnamed: Q2.2 (B), R3.2, R13.2
unnamed: Q3.2 (B), R4.2, R14.2
unnamed: Q3.3 (C), R5.2
unnamed: Q4.2 (B), R7.2, R15.2
unnamed: Q4.3 (C), Q5.3 (C), R8.2, R11.1
unnamed: Q5.2 (B), R9.2, R16.2
unnamed: Q6.2 (B), R11.2, R17.2
unnamed: Q6.3 (C), R18.2
unnamed: Q7.2 (B), R10.2, R19.2
unnamed: Q7.3 (C), Q8.3 (C), R21.2, R23.1
unnamed: Q8.2 (B), R20.2, R22.2
unnamed: Q9.2 (B), R23.2, R24.2
unnamed: Q9.3 (C), R25.2, R30.1
unnamed: Q10.1 (E), Q11.3 (C)
unnamed: Q10.2 (B), R6.2, R28.2
unnamed: Q10.3 (C), R29.2, R31.1
unnamed: Q11.2 (B), R26.2, R27.2
unnamed: Q12.1 (E), Q13.3 (C)
unnamed: Q12.2 (B), R30.2, R33.2
unnamed: Q12.3 (C), R34.2, R35.1
unnamed: Q13.2 (B), R31.2, R32.2
unnamed: Q14.2 (B), R35.2, R36.2
unnamed: Q14.3 (C), R37.2, R46.1, R51.1, R53.1
unnamed: Q15.1 (E), Q16.3 (C)
unnamed: Q15.2 (B), R38.2, R41.2
unnamed: Q15.3 (C), R42.2, R43.1
unnamed: Q16.2 (B), R39.2, R40.2
unnamed: Q17.2 (B), R43.2, R44.2
unnamed: Q17.3 (C), R45.2, R77.1
unnamed: Q18.2 (B), R46.2, R47.2
unnamed: Q18.3 (C), Q19.3 (C), R49.2, R55.1
unnamed: Q19.2 (B), R48.2, R50.2
unnamed: Q20.2 (B), R55.2, R59.2
unnamed: Q20.3 (C), R61.2, R65.1
unnamed: Q21.1 (E), Q22.3 (C)
unnamed: Q21.2 (B), R51.2, R57.2
unnamed: Q21.3 (C), R62.2, R66.1
unnamed: Q22.2 (B), R52.2, R56.2
unnamed: Q23.1 (E), Q24.3 (C)
unnamed: Q23.2 (B), R53.2, R60.2
unnamed: Q23.3 (C), R63.2, R64.1
unnamed: Q24.2 (B), R54.2, R58.2
unnamed: Q25.2 (B), R64.2, R67.2
unnamed: Q25.3 (C), R70.2, R75.1
unnamed: Q26.1 (E), Q27.3 (C)
unnamed: Q26.2 (B), R65.2, R69.2
unnamed: Q26.3 (C), R71.2, R72.1
unnamed: Q27.2 (B), R66.2, R68.2
unnamed: Q28.2 (B), R72.2, R73.2
unnamed: Q29.2 (B), R75.2, R76.2
unnamed: Q29.3 (C), Q30.3 (C), R78.2, R80.1
unnamed: Q30.2 (B), R77.2, R79.2
unnamed: Q31.2 (B), R80.2, R81.2
unnamed: Q32.2 (B), R83.2, R84.2
unnamed: Q32.3 (C), Q33.3 (C), R86.2, R92.1
unnamed: Q33.2 (B), R85.2, R87.2
unnamed: Q34.2 (B), R92.2, R96.2
unnamed: Q34.3 (C), R98.2, R102.1
unnamed: Q35.1 (E), Q36.3 (C)
unnamed: Q35.2 (B), R88.2, R94.2
unnamed: Q35.3 (C), R99.2, R103.1
unnamed: Q36.2 (B), R89.2, R93.2
unnamed: Q37.1 (E), Q38.3 (C)
unnamed: Q37.2 (B), R90.2, R97.2
unnamed: Q37.3 (C), R100.2, R101.1
unnamed: Q38.2 (B), R91.2, R95.2
unnamed: Q39.2 (B), R101.2, R104.2
unnamed: Q39.3 (C), R107.2, R143.1
unnamed: Q40.1 (E), Q41.3 (C)
unnamed: Q40.2 (B), R102.2, R106.2
unnamed: Q40.3 (C), R108.2, R109.1
unnamed: Q41.2 (B), R103.2, R105.2
unnamed: Q42.2 (B), R109.2, R110.2
unnamed: Q42.3 (C), R111.2, R112.1, R117.1, R119.1
unnamed: Q43.2 (B), R112.2, R113.2
unnamed: Q43.3 (C), Q44.3 (C), R115.2, R121.1
unnamed: Q44.2 (B), R114.2, R116.2
unnamed: Q45.2 (B), R121.2, R125.2
unnamed: Q45.3 (C), R127.2, R131.1
unnamed: Q46.1 (E), Q47.3 (C)
unnamed: Q46.2 (B), R117.2, R123.2
unnamed: Q46.3 (C), R128.2, R132.1
unnamed: Q47.2 (B), R118.2, R122.2
unnamed: Q48.1 (E), Q49.3 (C)
unnamed: Q48.2 (B), R119.2, R126.2
unnamed: Q48.3 (C), R129.2, R130.1
unnamed: Q49.2 (B), R120.2, R124.2
unnamed: Q50.2 (B), R130.2, R133.2
unnamed: Q50.3 (C), R136.2, R141.1
unnamed: Q51.1 (E), Q52.3 (C)
unnamed: Q51.2 (B), R131.2, R135.2
unnamed: Q51.3 (C), R137.2, R138.1
unnamed: Q52.2 (B), R132.2, R134.2
unnamed: Q53.2 (B), R138.2, R139.2
unnamed: Q54.2 (B), R141.2, R142.2
unnamed: Q54.3 (C), Q55.3 (C), R144.2, R146.1
unnamed: Q55.2 (B), R143.2, R145.2
unnamed: Q56.2 (B), R146.2, R147.2
unnamed: Q57.2 (B), R149.2, R150.2
unnamed: Q57.3 (C), Q58.3 (C), R152.2, R158.1
unnamed: Q58.2 (B), R151.2, R153.2
unnamed: Q59.2 (B), R158.2, R162.2
unnamed: Q59.3 (C), R164.2, R168.1
unnamed: Q60.1 (E), Q61.3 (C)
unnamed: Q60.2 (B), R154.2, R160.2
unnamed: Q60.3 (C), R165.2, R169.1
unnamed: Q61.2 (B), R155.2, R159.2
unnamed: Q62.1 (E), Q63.3 (C)
unnamed: Q62.2 (B), R156.2, R163.2
unnamed: Q62.3 (C), R166.2, R167.1
unnamed: Q63.2 (B), R157.2, R161.2
unnamed: Q64.2 (B), R167.2, R170.2
unnamed: Q64.3 (C), R173.2, R209.1
unnamed: Q65.1 (E), Q66.3 (C)
unnamed: Q65.2 (B), R168.2, R172.2
unnamed: Q65.3 (C), R174.2, R175.1
unnamed: Q66.2 (B), R169.2, R171.2
unnamed: Q67.2 (B), R175.2, R176.2
unnamed: Q67.3 (C), R177.2, R178.1, R183.1, R185.1
unnamed: Q68.2 (B), R178.2, R179.2
unnamed: Q68.3 (C), Q69.3 (C), R181.2, R187.1
unnamed: Q69.2 (B), R180.2, R182.2
unnamed: Q70.2 (B), R187.2, R191.2
unnamed: Q70.3 (C), R193.2, R197.1
unnamed: Q71.1 (E), Q72.3 (C)
unnamed: Q71.2 (B), R183.2, R189.2
unnamed: Q71.3 (C), R194.2, R198.1
unnamed: Q72.2 (B), R184.2, R188.2
unnamed: Q73.1 (E), Q74.3 (C)
unnamed: Q73.2 (B), R185.2, R192.2
unnamed: Q73.3 (C), R195.2, R196.1
unnamed: Q74.2 (B), R186.2, R190.2
unnamed: Q75.2 (B), R196.2, R199.2
unnamed: Q75.3 (C), R202.2, R207.1
unnamed: Q76.1 (E), Q77.3 (C)
unnamed: Q76.2 (B), R197.2, R201.2
unnamed: Q76.3 (C), R203.2, R204.1
unnamed: Q77.2 (B), R198.2, R200.2
unnamed: Q78.2 (B), R204.2, R205.2
unnamed: Q79.2 (B), R207.2, R208.2
unnamed: Q79.3 (C), Q80.3 (C), R210.2, R212.1
unnamed: Q80.2 (B), R209.2, R211.2
unnamed: Q81.2 (B), R212.2, R213.2
unnamed: Q82.2 (B), R215.2, R216.2
unnamed: Q83.2 (B), R217.2, R219.2
unnamed: Q85.2 (B), R223.2, R224.2
unnamed: Q86.2 (B), R225.2, R227.2
unnamed: Q87.2 (B), R226.2, R229.2
unnamed: Q88.2 (B), R228.2, R230.2
unnamed: Q89.2 (B), R231.2, R234.2
unnamed: Q90.2 (B), R232.2, R235.2
unnamed: Q92.2 (B), R239.2, R241.2
unnamed: Q93.2 (B), R240.2, R242.2
unnamed: Q94.2 (B), R243.2, R246.2
unnamed: Q95.2 (B), R244.2, R247.2
unnamed: Q97.2 (B), R251.2, R253.2
unnamed: Q98.2 (B), R252.2, R254.2
unnamed: Q99.2 (B), R255.2, R260.2
unnamed: Q100.2 (B), R256.2, R261.2
unnamed: Q101.2 (B), R257.2, R262.2
unnamed: Q102.2 (B), R258.2, R263.2
unnamed: Q103.2 (B), R264.2, R267.2
unnamed: Q104.2 (B), R265.2, R268.2
unnamed: Q105.2 (B), R269.2, R271.2
unnamed: Q106.2 (B), R270.2, R272.2
unnamed: Q107.2 (B), R273.2, R276.2
unnamed: Q108.2 (B), R274.2, R277.2
unnamed: Q112.2 (B), R287.2, R288.2
unnamed: Q112.3 (C), Q113.3 (C), R290.2, R294.1
unnamed: Q113.2 (B), R289.2, R291.2
unnamed: Q114.2 (B), R294.2, R297.2
unnamed: Q114.3 (C), R298.2, R300.1
unnamed: Q115.1 (E), Q116.3 (C)
unnamed: Q115.2 (B), R292.2, R296.2
unnamed: Q115.3 (C), R299.2, R301.1
unnamed: Q116.2 (B), R293.2, R295.2
unnamed: Q117.1 (E), Q118.3 (C)
unnamed: Q117.2 (B), R300.2, R303.2
unnamed: Q117.3 (C), R304.2, R305.1
unnamed: Q118.2 (B), R301.2, R302.2
unnamed: Q119.2 (B), R305.2, R306.2
unnamed: Q120.2 (B), R308.2, R309.2
unnamed: Q120.3 (C), Q121.3 (C), R311.2, R315.1
unnamed: Q121.2 (B), R310.2, R312.2
unnamed: Q122.2 (B), R315.2, R318.2
unnamed: Q122.3 (C), R319.2, R321.1
unnamed: Q123.1 (E), Q124.3 (C)
unnamed: Q123.2 (B), R313.2, R317.2
unnamed: Q123.3 (C), R320.2, R322.1
unnamed: Q124.2 (B), R314.2, R316.2
unnamed: Q125.1 (E), Q126.3 (C)
unnamed: Q125.2 (B), R321.2, R324.2
unnamed: Q125.3 (C), R325.2, R326.1
unnamed: Q126.2 (B), R322.2, R323.2
unnamed: Q127.2 (B), R326.2, R327.2
unnamed: Q128.2 (B), R329.2, R330.2
unnamed: Q128.3 (C), Q129.3 (C), R332.2, R336.1
unnamed: Q129.2 (B), R331.2, R333.2
unnamed: Q130.2 (B), R336.2, R339.2
unnamed: Q130.3 (C), R340.2, R342.1
unnamed: Q131.1 (E), Q132.3 (C)
unnamed: Q131.2 (B), R334.2, R338.2
unnamed: Q131.3 (C), R341.2, R343.1
unnamed: Q132.2 (B), R335.2, R337.2
unnamed: Q133.1 (E), Q134.3 (C)
unnamed: Q133.2 (B), R342.2, R345.2
unnamed: Q133.3 (C), R346.2, R347.1
unnamed: Q134.2 (B), R343.2, R344.2
unnamed: Q135.2 (B), R347.2, R348.2
unnamed: Q136.2 (B), R350.2, R351.2
unnamed: Q136.3 (C), Q137.3 (C), R353.2, R359.1
unnamed: Q137.2 (B), R352.2, R354.2
unnamed: Q138.2 (B), R359.2, R363.2
unnamed: Q138.3 (C), R365.2, R369.1
unnamed: Q139.1 (E), Q140.3 (C)
unnamed: Q139.2 (B), R355.2, R361.2
unnamed: Q139.3 (C), R366.2, R370.1
unnamed: Q140.2 (B), R356.2, R360.2
unnamed: Q141.1 (E), Q142.3 (C)
unnamed: Q141.2 (B), R357.2, R364.2
unnamed: Q141.3 (C), R367.2, R368.1
unnamed: Q142.2 (B), R358.2, R362.2
unnamed: Q143.2 (B), R368.2, R371.2
unnamed: Q143.3 (C), R374.2, R381.1, R385.1, R387.1
unnamed: Q144.1 (E), Q145.3 (C)
unnamed: Q144.2 (B), R369.2, R373.2
unnamed: Q144.3 (C), R375.2, R376.1
unnamed: Q145.2 (B), R370.2, R372.2
unnamed: Q146.2 (B), R376.2, R377.2
unnamed: Q147.2 (B), R379.2, R380.2
unnamed: Q147.3 (C), Q148.3 (C), R382.2, R388.1
unnamed: Q148.2 (B), R381.2, R383.2
unnamed: Q149.2 (B), R388.2, R392.2
unnamed: Q149.3 (C), R394.2, R398.1
unnamed: Q150.1 (E), Q151.3 (C)
unnamed: Q150.2 (B), R384.2, R390.2
unnamed: Q150.3 (C), R395.2, R399.1
unnamed: Q151.2 (B), R385.2, R389.2
unnamed: Q152.1 (E), Q153.3 (C)
unnamed: Q152.2 (B), R386.2, R393.2
unnamed: Q152.3 (C), R396.2, R397.1
unnamed: Q153.2 (B), R387.2, R391.2
unnamed: Q154.2 (B), R397.2, R400.2
unnamed: Q154.3 (C), R403.2, R410.1, R414.1, R416.1
unnamed: Q155.1 (E), Q156.3 (C)
unnamed: Q155.2 (B), R398.2, R402.2
unnamed: Q155.3 (C), R404.2, R405.1
unnamed: Q156.2 (B), R399.2, R401.2
unnamed: Q157.2 (B), R405.2, R406.2
unnamed: Q158.2 (B), R408.2, R409.2
unnamed: Q158.3 (C), Q159.3 (C), R411.2, R417.1
unnamed: Q159.2 (B), R410.2, R412.2
unnamed: Q160.2 (B), R417.2, R421.2
unnamed: Q160.3 (C), R423.2, R427.1
unnamed: Q161.1 (E), Q162.3 (C)
unnamed: Q161.2 (B), R413.2, R419.2
unnamed: Q161.3 (C), R424.2, R428.1
unnamed: Q162.2 (B), R414.2, R418.2
unnamed: Q163.1 (E), Q164.3 (C)
unnamed: Q163.2 (B), R415.2, R422.2
unnamed: Q163.3 (C), R425.2, R426.1
unnamed: Q164.2 (B), R416.2, R420.2
unnamed: Q165.2 (B), R426.2, R429.2
unnamed: Q165.3 (C), R432.2, R513.1, R517.1, R519.1
unnamed: Q166.1 (E), Q167.3 (C)
unnamed: Q166.2 (B), R427.2, R431.2
unnamed: Q166.3 (C), R433.2, R434.1
unnamed: Q167.2 (B), R428.2, R430.2
unnamed: Q168.2 (B), R434.2, R435.2
unnamed: Q169.2 (B), R437.2, R438.2
unnamed: Q169.3 (C), R439.2, R440.1
unnamed: Q170.1 (E), Q171.3 (C)
unnamed: Q170.2 (B), R440.2, R443.2
unnamed: Q170.3 (C), R444.2, R445.1
unnamed: Q171.2 (B), R441.2, R442.2
unnamed: Q172.2 (B), R445.2, R446.2
unnamed: Q173.2 (B), R448.2, R449.2
unnamed: Q173.3 (C), Q174.3 (C), R451.2, R455.1
unnamed: Q174.2 (B), R450.2, R452.2
unnamed: Q175.2 (B), R455.2, R458.2
unnamed: Q175.3 (C), R459.2, R461.1
unnamed: Q176.1 (E), Q177.3 (C)
unnamed: Q176.2 (B), R453.2, R457.2
unnamed: Q176.3 (C), R460.2, R462.1
unnamed: Q177.2 (B), R454.2, R456.2
unnamed: Q178.1 (E), Q179.3 (C)
unnamed: Q178.2 (B), R461.2, R464.2
unnamed: Q178.3 (C), R465.2, R466.1
unnamed: Q179.2 (B), R462.2, R463.2
unnamed: Q180.2 (B), R466.2, R467.2
unnamed: Q180.3 (C), R350.1, R355.1, R357.1, R468.2
unnamed: Q181.2 (B), R469.2, R470.2
unnamed: Q181.3 (C), Q182.3 (C), R472.2, R476.1
unnamed: Q182.2 (B), R471.2, R473.2
unnamed: Q183.2 (B), R476.2, R479.2
unnamed: Q183.3 (C), R480.2, R482.1
unnamed: Q184.1 (E), Q185.3 (C)
unnamed: Q184.2 (B), R474.2, R478.2
unnamed: Q184.3 (C), R481.2, R483.1
unnamed: Q185.2 (B), R475.2, R477.2
unnamed: Q186.1 (E), Q187.3 (C)
unnamed: Q186.2 (B), R482.2, R485.2
unnamed: Q186.3 (C), R486.2, R487.1
unnamed: Q187.2 (B), R483.2, R484.2
unnamed: Q188.2 (B), R487.2, R488.2
unnamed: Q188.3 (C), R379.1, R384.1, R386.1, R489.2
unnamed: Q189.2 (B), R490.2, R491.2
unnamed: Q189.3 (C), Q190.3 (C), R493.2, R497.1
unnamed: Q190.2 (B), R492.2, R494.2
unnamed: Q191.2 (B), R497.2, R500.2
unnamed: Q191.3 (C), R501.2, R503.1
unnamed: Q192.1 (E), Q193.3 (C)
unnamed: Q192.2 (B), R495.2, R499.2
unnamed: Q192.3 (C), R502.2, R504.1
unnamed: Q193.2 (B), R496.2, R498.2
unnamed: Q194.1 (E), Q195.3 (C)
unnamed: Q194.2 (B), R503.2, R506.2
unnamed: Q194.3 (C), R507.2, R508.1
unnamed: Q195.2 (B), R504.2, R505.2
unnamed: Q196.2 (B), R508.2, R509.2
unnamed: Q196.3 (C), R408.1, R413.1, R415.1, R510.2
unnamed: Q197.2 (B), R511.2, R512.2
unnamed: Q197.3 (C), Q198.3 (C), R514.2, R520.1
unnamed: Q198.2 (B), R513.2, R515.2
unnamed: Q199.2 (B), R520.2, R524.2
unnamed: Q199.3 (C), R526.2, R530.1
unnamed: Q200.1 (E), Q201.3 (C)
unnamed: Q200.2 (B), R516.2, R522.2
unnamed: Q200.3 (C), R527.2, R531.1
unnamed: Q201.2 (B), R517.2, R521.2
unnamed: Q202.1 (E), Q203.3 (C)
unnamed: Q202.2 (B), R518.2, R525.2
unnamed: Q202.3 (C), R528.2, R529.1
unnamed: Q203.2 (B), R519.2, R523.2
unnamed: Q204.2 (B), R529.2, R532.2
unnamed: Q205.1 (E), Q206.3 (C)
unnamed: Q205.2 (B), R530.2, R534.2
unnamed: Q205.3 (C), R536.2, R537.1
unnamed: Q206.2 (B), R531.2, R533.2
unnamed: Q207.2 (B), R537.2, R538.2
unnamed: Q208.2 (B), R540.2, R541.2
unnamed: Q208.3 (C), R543.2, R547.1, R548.1, R556.1
unnamed: Q209.2 (B), R542.2, R544.2
unnamed: Q209.3 (C), R545.2, R549.1
unnamed: Q210.1 (E), Q211.3 (C)
unnamed: Q210.2 (B), R546.2, R552.2
unnamed: Q210.3 (C), R554.2, R558.1
unnamed: Q211.2 (B), R547.2, R550.2
unnamed: Q212.1 (E), Q213.3 (C)
unnamed: Q212.2 (B), R548.2, R553.2
unnamed: Q212.3 (C), R555.2, R561.1
unnamed: Q213.2 (B), R549.2, R551.2
unnamed: Q214.2 (B), R556.2, R557.2
unnamed: Q214.3 (C), R562.2, R573.1, R574.1
unnamed: Q215.1 (E), Q216.3 (C)
unnamed: Q215.2 (B), R558.2, R565.2
unnamed: Q215.3 (C), R560.1, R567.2, R569.1, R572.1
unnamed: Q216.2 (B), R559.2, R563.2
unnamed: Q217.1 (E), Q218.3 (C)
unnamed: Q217.2 (B), R560.2, R566.2
unnamed: Q217.3 (C), R559.1, R568.2
unnamed: Q218.2 (B), R561.2, R564.2
unnamed: Q219.2 (B), R569.2, R570.2
unnamed: Q219.3 (C), R571.2, R575.1
unnamed: Q220.1 (E), Q221.3 (C)
unnamed: Q220.2 (B), R572.2, R578.2
unnamed: Q220.3 (C), R580.2, R582.1
unnamed: Q221.2 (B), R573.2, R576.2
unnamed: Q222.1 (E), Q223.3 (C)
unnamed: Q222.2 (B), R574.2, R579.2
unnamed: Q222.3 (C), R581.2, R585.1
unnamed: Q223.2 (B), R575.2, R577.2
unnamed: Q224.1 (E), Q225.3 (C)
unnamed: Q224.2 (B), R582.2, R588.2
unnamed: Q225.2 (B), R583.2, R586.2
unnamed: Q226.1 (E), Q227.3 (C)
unnamed: Q226.2 (B), R584.2, R589.2
unnamed: Q226.3 (C), R583.1, R591.2
unnamed: Q227.2 (B), R585.2, R587.2
unnamed: Q228.2 (B), R592.2, R593.2
unnamed: Q228.3 (C), R595.2, R599.1, R600.1, R608.1
unnamed: Q229.2 (B), R594.2, R596.2
unnamed: Q229.3 (C), R597.2, R601.1
unnamed: Q230.1 (E), Q231.3 (C)
unnamed: Q230.2 (B), R598.2, R604.2
unnamed: Q230.3 (C), R606.2, R610.1
unnamed: Q231.2 (B), R599.2, R602.2
unnamed: Q232.1 (E), Q233.3 (C)
unnamed: Q232.2 (B), R600.2, R605.2
unnamed: Q232.3 (C), R607.2, R613.1
unnamed: Q233.2 (B), R601.2, R603.2
unnamed: Q234.2 (B), R608.2, R609.2
unnamed: Q234.3 (C), R614.2, R625.1, R626.1
unnamed: Q235.1 (E), Q236.3 (C)
unnamed: Q235.2 (B), R610.2, R617.2
unnamed: Q235.3 (C), R612.1, R619.2, R621.1, R624.1
unnamed: Q236.2 (B), R611.2, R615.2
unnamed: Q237.1 (E), Q238.3 (C)
unnamed: Q237.2 (B), R612.2, R618.2
unnamed: Q237.3 (C), R611.1, R620.2
unnamed: Q238.2 (B), R613.2, R616.2
unnamed: Q239.2 (B), R621.2, R622.2
unnamed: Q239.3 (C), R623.2, R627.1
unnamed: Q240.1 (E), Q241.3 (C)
unnamed: Q240.2 (B), R624.2, R630.2
unnamed: Q240.3 (C), R632.2, R634.1
unnamed: Q241.2 (B), R625.2, R628.2
unnamed: Q242.1 (E), Q243.3 (C)
unnamed: Q242.2 (B), R626.2, R631.2
unnamed: Q242.3 (C), R633.2, R637.1
unnamed: Q243.2 (B), R627.2, R629.2
unnamed: Q244.1 (E), Q245.3 (C)
unnamed: Q244.2 (B), R634.2, R640.2
unnamed: Q245.2 (B), R635.2, R638.2
unnamed: Q246.1 (E), Q247.3 (C)
unnamed: Q246.2 (B), R636.2, R641.2
unnamed: Q246.3 (C), R635.1, R643.2
unnamed: Q247.2 (B), R637.2, R639.2
unnamed: Q248.2 (B), R644.2, R645.2
unnamed: Q248.3 (C), R647.2, R651.1, R652.1, R660.1
unnamed: Q249.2 (B), R646.2, R648.2
unnamed: Q249.3 (C), R649.2, R653.1
unnamed: Q250.1 (E), Q251.3 (C)
unnamed: Q250.2 (B), R650.2, R656.2
unnamed: Q250.3 (C), R658.2, R662.1
unnamed: Q251.2 (B), R651.2, R654.2
unnamed: Q252.1 (E), Q253.3 (C)
unnamed: Q252.2 (B), R652.2, R657.2
unnamed: Q252.3 (C), R659.2, R665.1
unnamed: Q253.2 (B), R653.2, R655.2
unnamed: Q254.2 (B), R660.2, R661.2
unnamed: Q254.3 (C), R666.2, R677.1, R678.1
unnamed: Q255.1 (E), Q256.3 (C)
unnamed: Q255.2 (B), R662.2, R669.2
unnamed: Q255.3 (C), R664.1, R671.2, R673.1, R676.1
unnamed: Q256.2 (B), R663.2, R667.2
unnamed: Q257.1 (E), Q258.3 (C)
unnamed: Q257.2 (B), R664.2, R670.2
unnamed: Q257.3 (C), R663.1, R672.2
unnamed: Q258.2 (B), R665.2, R668.2
unnamed: Q259.2 (B), R673.2, R674.2
unnamed: Q259.3 (C), R675.2, R679.1
unnamed: Q260.1 (E), Q261.3 (C)
unnamed: Q260.2 (B), R676.2, R682.2
unnamed: Q260.3 (C), R684.2, R686.1
unnamed: Q261.2 (B), R677.2, R680.2
unnamed: Q262.1 (E), Q263.3 (C)
unnamed: Q262.2 (B), R678.2, R683.2
unnamed: Q262.3 (C), R685.2, R689.1
unnamed: Q263.2 (B), R679.2, R681.2
unnamed: Q264.1 (E), Q265.3 (C)
unnamed: Q264.2 (B), R686.2, R692.2
unnamed: Q265.2 (B), R687.2, R690.2
unnamed: Q266.1 (E), Q267.3 (C)
unnamed: Q266.2 (B), R688.2, R693.2
unnamed: Q266.3 (C), R687.1, R695.2
unnamed: Q267.2 (B), R689.2, R691.2
unnamed: Q268.2 (B), R696.2, R697.2
unnamed: Q268.3 (C), R699.2, R703.1, R704.1, R712.1
unnamed: Q269.2 (B), R698.2, R700.2
unnamed: Q269.3 (C), R701.2, R705.1
unnamed: Q270.1 (E), Q271.3 (C)
unnamed: Q270.2 (B), R702.2, R708.2
unnamed: Q270.3 (C), R710.2, R714.1
unnamed: Q271.2 (B), R703.2, R706.2
unnamed: Q272.1 (E), Q273.3 (C)
unnamed: Q272.2 (B), R704.2, R709.2
unnamed: Q272.3 (C), R711.2, R717.1
unnamed: Q273.2 (B), R705.2, R707.2
unnamed: Q274.2 (B), R712.2, R713.2
unnamed: Q274.3 (C), R718.2, R729.1, R730.1
unnamed: Q275.1 (E), Q276.3 (C)
unnamed: Q275.2 (B), R714.2, R721.2
unnamed: Q275.3 (C), R716.1, R723.2, R725.1, R728.1
unnamed: Q276.2 (B), R715.2, R719.2
unnamed: Q277.1 (E), Q278.3 (C)
unnamed: Q277.2 (B), R716.2, R722.2
unnamed: Q277.3 (C), R715.1, R724.2
unnamed: Q278.2 (B), R717.2, R720.2
unnamed: Q279.2 (B), R725.2, R726.2
unnamed: Q279.3 (C), R727.2, R731.1
unnamed: Q280.1 (E), Q281.3 (C)
unnamed: Q280.2 (B), R728.2, R734.2
unnamed: Q280.3 (C), R736.2, R738.1
unnamed: Q281.2 (B), R729.2, R732.2
unnamed: Q282.1 (E), Q283.3 (C)
unnamed: Q282.2 (B), R730.2, R735.2
unnamed: Q282.3 (C), R737.2, R741.1
unnamed: Q283.2 (B), R731.2, R733.2
unnamed: Q284.1 (E), Q285.3 (C)
unnamed: Q284.2 (B), R738.2, R744.2
unnamed: Q285.2 (B), R739.2, R742.2
unnamed: Q286.1 (E), Q287.3 (C)
unnamed: Q286.2 (B), R740.2, R745.2
unnamed: Q286.3 (C), R739.1, R747.2
unnamed: Q287.2 (B), R741.2, R743.2
unnamed: Q288.2 (B), R748.2, R749.2
unnamed: Q288.3 (C), R751.2, R755.1, R756.1, R764.1
unnamed: Q289.2 (B), R750.2, R752.2
unnamed: Q289.3 (C), R753.2, R757.1
unnamed: Q290.1 (E), Q291.3 (C)
unnamed: Q290.2 (B), R754.2, R760.2
unnamed: Q290.3 (C), R762.2, R766.1
unnamed: Q291.2 (B), R755.2, R758.2
unnamed: Q292.1 (E), Q293.3 (C)
unnamed: Q292.2 (B), R756.2, R761.2
unnamed: Q292.3 (C), R763.2, R769.1
unnamed: Q293.2 (B), R757.2, R759.2
unnamed: Q294.2 (B), R764.2, R765.2
unnamed: Q294.3 (C), R770.2, R781.1, R782.1
unnamed: Q295.1 (E), Q296.3 (C)
unnamed: Q295.2 (B), R766.2, R773.2
unnamed: Q295.3 (C), R768.1, R775.2, R777.1, R780.1
unnamed: Q296.2 (B), R767.2, R771.2
unnamed: Q297.1 (E), Q298.3 (C)
unnamed: Q297.2 (B), R768.2, R774.2
unnamed: Q297.3 (C), R767.1, R776.2
unnamed: Q298.2 (B), R769.2, R772.2
unnamed: Q299.2 (B), R777.2, R778.2
unnamed: Q299.3 (C), R779.2, R783.1
unnamed: Q300.1 (E), Q301.3 (C)
unnamed: Q300.2 (B), R780.2, R786.2
unnamed: Q300.3 (C), R788.2, R790.1
unnamed: Q301.2 (B), R781.2, R784.2
unnamed: Q302.1 (E), Q303.3 (C)
unnamed: Q302.2 (B), R782.2, R787.2
unnamed: Q302.3 (C), R789.2, R793.1
unnamed: Q303.2 (B), R783.2, R785.2
unnamed: Q304.1 (E), Q305.3 (C)
unnamed: Q304.2 (B), R790.2, R796.2
unnamed: Q305.2 (B), R791.2, R794.2
unnamed: Q306.1 (E), Q307.3 (C)
unnamed: Q306.2 (B), R792.2, R797.2
unnamed: Q306.3 (C), R791.1, R799.2
unnamed: Q307.2 (B), R793.2, R795.2
unnamed: Q308.1 (E), Q309.3 (C)
unnamed: Q308.2 (B), R800.2, R803.2
unnamed: Q308.3 (C), R804.2, R805.1
unnamed: Q309.1 (E), Q311.3 (C)
unnamed: Q309.2 (B), R801.2, R802.2
unnamed: Q310.2 (B), R805.2, R806.2
unnamed: Q311.1 (E), Q312.3 (C)
unnamed: Q311.2 (B), R808.2, R809.2
unnamed: Q312.2 (B), R810.2, R811.2
unnamed: Q313.1 (E), Q314.3 (C)
unnamed: Q313.2 (B), R812.2, R819.2
unnamed: Q313.3 (C), R820.2, R821.1
unnamed: Q314.1 (E), Q315.3 (C)
unnamed: Q314.2 (B), R813.2, R816.2
unnamed: Q315.1 (E), Q316.3 (C)
unnamed: Q315.2 (B), R814.2, R817.2
unnamed: Q316.2 (B), R815.2, R818.2
unnamed: Q317.2 (B), R821.2, R822.2
unnamed: Q318.1 (E), Q319.3 (C)
unnamed: Q318.2 (B), R824.2, R831.2
unnamed: Q318.3 (C), R832.2, R833.1
unnamed: Q319.1 (E), Q320.3 (C)
unnamed: Q319.2 (B), R825.2, R828.2
unnamed: Q320.1 (E), Q321.3 (C)
unnamed: Q320.2 (B), R826.2, R829.2
unnamed: Q321.2 (B), R827.2, R830.2
unnamed: Q322.2 (B), R833.2, R834.2
unnamed: Q323.1 (E), Q324.3 (C)
unnamed: Q323.2 (B), R836.2, R843.2
unnamed: Q323.3 (C), R844.2, R845.1
unnamed: Q324.1 (E), Q325.3 (C)
unnamed: Q324.2 (B), R837.2, R840.2
unnamed: Q325.1 (E), Q326.3 (C)
unnamed: Q325.2 (B), R838.2, R841.2
unnamed: Q326.2 (B), R839.2, R842.2
unnamed: Q327.2 (B), R845.2, R846.2
unnamed: Q328.1 (E), Q329.3 (C)
unnamed: Q328.2 (B), R848.2, R863.2
unnamed: Q328.3 (C), R880.2, R883.1
unnamed: Q329.1 (E), Q330.3 (C)
unnamed: Q329.2 (B), R849.2, R860.2
unnamed: Q330.1 (E), Q331.3 (C)
unnamed: Q330.2 (B), R850.2, R861.2
unnamed: Q331.2 (B), R851.2, R862.2
unnamed: Q332.1 (E), Q333.3 (C)
unnamed: Q332.2 (B), R852.2, R871.2
unnamed: Q332.3 (C), R881.2, R885.1
unnamed: Q333.1 (E), Q334.3 (C)
unnamed: Q333.2 (B), R853.2, R868.2
unnamed: Q334.1 (E), Q335.3 (C)
unnamed: Q334.2 (B), R854.2, R869.2
unnamed: Q335.2 (B), R855.2, R870.2
unnamed: Q336.1 (E), Q337.3 (C)
unnamed: Q336.2 (B), R856.2, R875.2
unnamed: Q336.3 (C), R882.2, R887.1
unnamed: Q337.1 (E), Q338.3 (C)
unnamed: Q337.2 (B), R857.2, R872.2
unnamed: Q338.1 (E), Q339.3 (C)
unnamed: Q338.2 (B), R858.2, R873.2
unnamed: Q339.2 (B), R859.2, R874.2
unnamed: Q340.1 (E), Q341.3 (C)
unnamed: Q340.2 (B), R864.2, R879.2
unnamed: Q340.3 (C), R884.2, R889.1
unnamed: Q341.1 (E), Q342.3 (C)
unnamed: Q341.2 (B), R865.2, R876.2
unnamed: Q342.1 (E), Q343.3 (C)
unnamed: Q342.2 (B), R866.2, R877.2
unnamed: Q343.2 (B), R867.2, R878.2
unnamed: Q344.2 (B), R883.2, R886.2
unnamed: Q345.2 (B), R885.2, R888.2
unnamed: Q346.2 (B), R887.2, R890.2
unnamed: Q347.2 (B), R889.2, R892.2
unnamed: Q348.2 (B), R896.2, R897.2
unnamed: Q348.3 (C), R800.1, R898.2
unnamed: Q349.2 (B), R899.2, R900.2
unnamed: Q349.3 (C), R801.1, R901.2
unnamed: Q350.2 (B), R902.2, R903.2
unnamed: Q350.3 (C), R808.1, R904.2
unnamed: Q351.2 (B), R905.2, R906.2
unnamed: Q351.3 (C), R810.1, R907.2
unnamed: Q352.2 (B), R908.2, R909.2
unnamed: Q352.3 (C), R812.1, R910.2
unnamed: Q353.2 (B), R911.2, R912.2
unnamed: Q353.3 (C), R813.1, R913.2
unnamed: Q354.2 (B), R914.2, R915.2
unnamed: Q354.3 (C), R815.1, R916.2
unnamed: Q355.2 (B), R917.2, R918.2
unnamed: Q355.3 (C), R824.1, R919.2
unnamed: Q356.2 (B), R920.2, R921.2
unnamed: Q356.3 (C), R825.1, R922.2
unnamed: Q357.2 (B), R923.2, R924.2
unnamed: Q357.3 (C), R827.1, R925.2
unnamed: Q358.2 (B), R926.2, R927.2
unnamed: Q358.3 (C), R836.1, R928.2
unnamed: Q359.2 (B), R929.2, R930.2
unnamed: Q359.3 (C), R837.1, R931.2
unnamed: Q360.2 (B), R932.2, R933.2
unnamed: Q360.3 (C), R848.1, R934.2
unnamed: Q361.2 (B), R935.2, R936.2
unnamed: Q361.3 (C), R849.1, R937.2
unnamed: Q362.2 (B), R938.2, R939.2
unnamed: Q362.3 (C), R850.1, R940.2
unnamed: Q363.2 (B), R941.2, R942.2
unnamed: Q363.3 (C), R852.1, R943.2
unnamed: Q364.2 (B), R944.2, R945.2
unnamed: Q364.3 (C), R854.1, R946.2
unnamed: Q365.2 (B), R947.2, R948.2
unnamed: Q365.3 (C), R856.1, R949.2
unnamed: Q366.2 (B), R950.2, R951.2
unnamed: Q366.3 (C), R859.1, R952.2
unnamed: Q367.2 (B), R953.2, R954.2
unnamed: Q367.3 (C), R864.1, R955.2
unnamed: Q368.2 (B), R956.2, R957.2
unnamed: Q368.3 (C), R958.2, R1017.1
unnamed: Q369.2 (B), R959.2, R960.2
unnamed: Q369.3 (C), R961.2, R1018.1
unnamed: Q370.2 (B), R962.2, R963.2
unnamed: Q370.3 (C), R964.2, R1019.1
unnamed: Q371.2 (B), R965.2, R966.2
unnamed: Q371.3 (C), R967.2, R1021.1
unnamed: Q372.2 (B), R968.2, R969.2
unnamed: Q372.3 (C), R970.2, R1022.1
unnamed: Q373.2 (B), R971.2, R972.2
unnamed: Q373.3 (C), R973.2, R1025.1
unnamed: Q374.2 (B), R974.2, R975.2
unnamed: Q374.3 (C), R976.2, R1027.1
unnamed: Q375.2 (B), R977.2, R978.2
unnamed: Q375.3 (C), R979.2, R1033.1
unnamed: Q376.2 (B), R980.2, R981.2
unnamed: Q376.3 (C), R982.2, R1046.1
unnamed: Q377.2 (B), R983.2, R984.2
unnamed: Q377.3 (C), R985.2, R1047.1
unnamed: Q378.2 (B), R986.2, R987.2
unnamed: Q378.3 (C), R988.2, R1054.1
unnamed: Q379.2 (B), R989.2, R990.2
unnamed: Q379.3 (C), R991.2, R1060.1
unnamed: Q388.1 (E), Q389.3 (C)
unnamed: Q388.2 (B), R1016.2, R1031.2
unnamed: Q388.3 (C), R1056.2, R1074.1
unnamed: Q389.1 (E), Q390.3 (C)
unnamed: Q389.2 (B), R1017.2, R1028.2
unnamed: Q390.1 (E), Q391.3 (C)
unnamed: Q390.2 (B), R1018.2, R1029.2
unnamed: Q391.2 (B), R1019.2, R1030.2
unnamed: Q392.1 (E), Q393.3 (C)
unnamed: Q392.2 (B), R1020.2, R1039.2
unnamed: Q392.3 (C), R1064.2, R1081.1
unnamed: Q393.1 (E), Q394.3 (C)
unnamed: Q393.2 (B), R1021.2, R1036.2
unnamed: Q394.1 (E), Q395.3 (C)
unnamed: Q394.2 (B), R1022.2, R1037.2
unnamed: Q395.2 (B), R1023.2, R1038.2
unnamed: Q396.1 (E), Q397.3 (C)
unnamed: Q396.2 (B), R1024.2, R1043.2
unnamed: Q396.3 (C), R1070.2, R1086.1
unnamed: Q397.1 (E), Q398.3 (C)
unnamed: Q397.2 (B), R1025.2, R1040.2
unnamed: Q398.1 (E), Q399.3 (C)
unnamed: Q398.2 (B), R1026.2, R1041.2
unnamed: Q399.2 (B), R1027.2, R1042.2
unnamed: Q400.1 (E), Q401.3 (C)
unnamed: Q400.2 (B), R1032.2, R1051.2
unnamed: Q400.3 (C), R1079.2, R1090.1
unnamed: Q401.1 (E), Q402.3 (C)
unnamed: Q401.2 (B), R1033.2, R1048.2
unnamed: Q402.1 (E), Q403.3 (C)
unnamed: Q402.2 (B), R1034.2, R1049.2
unnamed: Q403.2 (B), R1035.2, R1050.2
unnamed: Q404.1 (E), Q405.3 (C)
unnamed: Q404.2 (B), R1044.2, R1065.2
unnamed: Q404.3 (C), R1088.2, R1096.1
unnamed: Q405.1 (E), Q406.3 (C)
unnamed: Q405.2 (B), R1045.2, R1061.2
unnamed: Q406.1 (E), Q407.3 (C)
unnamed: Q406.2 (B), R1046.2, R1062.2
unnamed: Q407.2 (B), R1047.2, R1063.2
unnamed: Q408.1 (E), Q409.3 (C)
unnamed: Q408.2 (B), R1052.2, R1075.2
unnamed: Q408.3 (C), R1092.2, R1099.1
unnamed: Q409.1 (E), Q410.3 (C)
unnamed: Q409.2 (B), R1053.2, R1071.2
unnamed: Q410.1 (E), Q411.3 (C)
unnamed: Q410.2 (B), R1054.2, R1072.2
unnamed: Q411.2 (B), R1055.2, R1073.2
unnamed: Q412.1 (E), Q413.3 (C)
unnamed: Q412.2 (B), R1057.2, R1080.2
unnamed: Q412.3 (C), R1093.2, R1102.1
unnamed: Q413.1 (E), Q414.3 (C)
unnamed: Q413.2 (B), R1058.2, R1076.2
unnamed: Q414.1 (E), Q415.3 (C)
unnamed: Q414.2 (B), R1059.2, R1077.2
unnamed: Q415.2 (B), R1060.2, R1078.2
unnamed: Q416.2 (B), R1074.2, R1085.2
unnamed: Q417.1 (E), Q418.3 (C)
unnamed: Q417.2 (B), R1066.2, R1087.2
unnamed: Q417.3 (C), R1097.2, R1105.1
unnamed: Q418.1 (E), Q419.3 (C)
unnamed: Q418.2 (B), R1067.2, R1082.2
unnamed: Q419.1 (E), Q420.3 (C)
unnamed: Q419.2 (B), R1068.2, R1083.2
unnamed: Q420.2 (B), R1069.2, R1084.2
unnamed: Q421.2 (B), R1081.2, R1089.2
unnamed: Q422.2 (B), R1086.2, R1091.2
unnamed: Q423.2 (B), R1090.2, R1095.2
unnamed: Q424.2 (B), R1096.2, R1101.2
unnamed: Q425.2 (B), R1099.2, R1104.2
unnamed: Q426.2 (B), R1102.2, R1106.2
unnamed: Q427.2 (B), R1105.2, R1108.2
OUT0: Q146.3 (C), R378.2
OUT1: Q157.3 (C), R407.2
OUT2: Q168.3 (C), R436.2
OUT3: Q207.3 (C), R539.2
OUT4: Q204.3 (C), R535.2
OUT_B0: Q304.3 (C), R792.1, R798.2, R814.1, R839.1, R855.1, R867.1, R896.1, R923.1, R938.1, R950.1, R962.1, R974.1, R983.1, R989.1, R1023.1, R1035.1, R1055.1, R1069.1
OUT_B1: Q284.3 (C), R740.1, R746.2, R826.1, R838.1, R858.1, R866.1, R899.1, R914.1, R935.1, R944.1, R959.1, R968.1, R980.1, R986.1, R1026.1, R1034.1, R1059.1, R1068.1
OUT_B2: Q264.3 (C), R688.1, R694.2, R851.1, R853.1, R857.1, R865.1, R902.1, R911.1, R920.1, R929.1, R956.1, R965.1, R971.1, R977.1, R1045.1, R1053.1, R1058.1, R1067.1
OUT_B3: Q244.3 (C), R636.1, R642.2, R905.1, R908.1, R917.1, R926.1, R932.1, R941.1, R947.1, R953.1, R1016.1, R1020.1, R1024.1, R1032.1, R1044.1, R1052.1, R1057.1, R1066.1
OUT_SIGN: Q224.3 (C), R584.1, R590.2
REG_D0: R750.1, R754.1
REG_D1: R698.1, R702.1
REG_D2: R646.1, R650.1
REG_D3: R594.1, R598.1
REG_DS: R542.1, R546.1
S0: Q28.3 (C), R74.2, R448.1, R453.1
S1: Q53.3 (C), R140.2, R469.1, R474.1
S2: Q78.3 (C), R206.2, R490.1, R495.1
S3: Q81.3 (C), R214.2, R437.1, R511.1, R516.1, R518.1
SIG: Q172.3 (C), R352.1, R356.1, R358.1, R447.2
SIGB: R450.1, R454.1, R471.1, R475.1, R492.1, R496.1
SUB: R48.1, R52.1, R54.1, R441.1
SUB2: R287.1, R292.1, R308.1, R313.1, R329.1, R334.1
X1: R274.1
X2: R265.1
X3: R258.1, R270.1
X4: R256.1
X5: R252.1, R273.1
X6: R255.1, R264.1
X7: R251.1, R257.1, R269.1
Y1: R244.1
Y2: R232.1
Y3: R228.1, R240.1
Y4: R225.1
Y5: R223.1, R243.1
Y6: R217.1, R231.1
Y7: R215.1, R226.1, R239.1

Notes on the sheet:
MULDIV sheet: multiply/divide extension (re-uses this sheet's adder). TESTBENCH sheet: keypad/op-code/clock stimulus + .tran directive. Root-sheet changes: keypad-encoder output inverters for A0..A2 / EB0..EB2 moved into MULDIV (operand muxes); memory register D inputs renamed REG_D0..3 / REG_DS; c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
