nikolafilip/nibble/experiments/muldiv/muldiv.kicad_sch

## KiCad design experiments/muldiv/muldiv.kicad_sch (2026-09-09)

Schematic: muldiv.kicad_sch

Parts:
Q2000, Q2001, Q2002, Q2003, Q2004, Q2005, Q2006, Q2007, Q2008, Q2009, Q2010, Q2011, Q2012, Q2013, Q2014, Q2015, Q2016, Q2017, Q2018, Q2019, Q2020, Q2021, Q2022, Q2023, Q2024, Q2025, Q2026, Q2027, Q2028, Q2029, Q2030, Q2031, Q2032, Q2033, Q2034, Q2035, Q2036, Q2037, Q2038, Q2039, Q2040, Q2041, Q2042, Q2043, Q2044, Q2045, Q2046, Q2047, Q2048, Q2049, Q2050, Q2051, Q2052, Q2053, Q2054, Q2055, Q2056, Q2057, Q2058, Q2059, Q2060, Q2061, Q2062, Q2063, Q2064, Q2065, Q2066, Q2067, Q2068, Q2069, Q2070, Q2071, Q2072, Q2073, Q2074, Q2075, Q2076, Q2077, Q2078, Q2079, Q2080, Q2081, Q2082, Q2083, Q2084, Q2085, Q2086, Q2087, Q2088, Q2089, Q2090, Q2091, Q2092, Q2093, Q2094, Q2095, Q2096, Q2097, Q2098, Q2099, Q2100, Q2101, Q2102, Q2103, Q2104, Q2105, Q2106, Q2107, Q2108, Q2109, Q2110, Q2111, Q2112, Q2113, Q2114, Q2115, Q2116, Q2117, Q2118, Q2119, Q2120, Q2121, Q2122, Q2123, Q2124, Q2125, Q2126, Q2127, Q2128, Q2129, Q2130, Q2131, Q2132, Q2133, Q2134, Q2135, Q2136, Q2137, Q2138, Q2139, Q2140, Q2141, Q2142, Q2143, Q2144, Q2145, Q2146, Q2147, Q2148, Q2149, Q2150, Q2151, Q2152, Q2153, Q2154, Q2155, Q2156, Q2157, Q2158, Q2159, Q2160, Q2161, Q2162, Q2163, Q2164, Q2165, Q2166, Q2167, Q2168, Q2169, Q2170, Q2171, Q2172, Q2173, Q2174, Q2175, Q2176, Q2177, Q2178, Q2179, Q2180, Q2181, Q2182, Q2183, Q2184, Q2185, Q2186, Q2187, Q2188, Q2189, Q2190, Q2191, Q2192, Q2193, Q2194, Q2195, Q2196, Q2197, Q2198, Q2199, Q2200, Q2201, Q2202, Q2203, Q2204, Q2205, Q2206, Q2207, Q2208, Q2209, Q2210, Q2211, Q2212, Q2213, Q2214, Q2215, Q2216, Q2217, Q2218, Q2219, Q2220, Q2221, Q2222, Q2223, Q2224, Q2225, Q2226, Q2227, Q2228, Q2229, Q2230, Q2231, Q2232, Q2233, Q2234, Q2235, Q2236, Q2237, Q2238, Q2239, Q2240, Q2241, Q2242, Q2243, Q2244, Q2245, Q2246, Q2247, Q2248, Q2249, Q2250, Q2251, Q2252, Q2253, Q2254, Q2255, Q2256, Q2257, Q2258, Q2259, Q2260, Q2261, Q2262, Q2263, Q2264, Q2265, Q2266, Q2267, Q2268, Q2269, Q2270, Q2271, Q2272, Q2273, Q2274, Q2275, Q2276, Q2277, Q2278, Q2279, Q2280, Q2281, Q2282, Q2283, Q2284, Q2285, Q2286, Q2287, Q2288, Q2289, Q2290, Q2291, Q2292, Q2293, Q2294, Q2295, Q2296, Q2297, Q2298, Q2299, Q2300, Q2301, Q2302, Q2303, Q2304, Q2305, Q2306, Q2307, Q2308, Q2309, Q2310, Q2311, Q2312, Q2313, Q2314, Q2315, Q2316, Q2317, Q2318, Q2319, Q2320, Q2321, Q2322, Q2323, Q2324, Q2325, Q2326, Q2327, Q2328, Q2329, Q2330, Q2331, Q2332, Q2333, Q2334, Q2335, Q2336, Q2337, Q2338, Q2339, Q2340, Q2341, Q2342, Q2343, Q2344, Q2345, Q2346, Q2347, Q2348, Q2349, Q2350, Q2351, Q2352, Q2353, Q2354, Q2355, Q2356, Q2357, Q2358, Q2359, Q2360, Q2361, Q2362, Q2363, Q2364, Q2365, Q2366, Q2367, Q2368, Q2369, Q2370, Q2371, Q2372, Q2373, Q2374, Q2375, Q2376, Q2377, Q2378, Q2379, Q2380, Q2381, Q2382, Q2383, Q2384, Q2385, Q2386, Q2387, Q2388, Q2389, Q2390, Q2391, Q2392, Q2393, Q2394, Q2395, Q2396, Q2397, Q2398, Q2399, Q2400, Q2401, Q2402, Q2403, Q2404, Q2405, Q2406, Q2407, Q2408, Q2409, Q2410, Q2411, Q2412, Q2413, Q2414, Q2415, Q2416, Q2417, Q2418, Q2419, Q2420, Q2421, Q2422, Q2423, Q2424, Q2425, Q2426, Q2427, Q2428, Q2429, Q2430, Q2431, Q2432, Q2433, Q2434, Q2435, Q2436, Q2437, Q2438, Q2439, Q2440, Q2441, Q2442, Q2443, Q2444, Q2445, Q2446, Q2447, Q2448, Q2449, Q2450, Q2451, Q2452, Q2453, Q2454, Q2455, Q2456, Q2457, Q2458, Q2459, Q2460, Q2461, Q2462, Q2463, Q2464, Q2465, Q2466, Q2467, Q2468, Q2469, Q2470, Q2471, Q2472, Q2473, Q2474, Q2475, Q2476, Q2477, Q2478, Q2479: 2N3904; TO-92_Inline
R2000, R2003, R2006, R2009, R2012, R2015, R2018, R2024, R2030, R2033, R2036, R2060, R2102, R2115, R2118, R2160, R2170, R2212, R2222, R2264, R2274, R2333, R2336, R2349, R2360, R2392, R2413, R2438, R2463, R2480, R2692, R2734, R2744, R2786, R2796, R2838, R2848, R2890, R2900, R2942, R2952, R2994, R3090, R3132, R3142, R3184, R3227: 2.2k; R_Axial_DIN0207_L6.3mm_D2.5mm_P5.08mm_Vertical
R2001, R2004, R2007, R2010, R2013, R2016, R2019, R2022, R2025, R2028, R2031, R2034, R2037, R2040, R2042, R2044, R2046, R2048, R2051, R2053, R2055, R2058, R2061, R2064, R2067, R2070, R2072, R2075, R2077, R2080, R2082, R2085, R2087, R2090, R2093, R2095, R2098, R2100, R2103, R2105, R2108, R2110, R2113, R2116, R2119, R2122, R2125, R2128, R2130, R2133, R2135, R2138, R2140, R2143, R2145, R2148, R2151, R2153, R2156, R2158, R2161, R2163, R2166, R2168, R2171, R2174, R2177, R2180, R2182, R2185, R2187, R2190, R2192, R2195, R2197, R2200, R2203, R2205, R2208, R2210, R2213, R2215, R2218, R2220, R2223, R2226, R2229, R2232, R2234, R2237, R2239, R2242, R2244, R2247, R2249, R2252, R2255, R2257, R2260, R2262, R2265, R2267, R2270, R2272, R2275, R2278, R2281, R2284, R2286, R2289, R2291, R2294, R2296, R2299, R2301, R2304, R2307, R2309, R2312, R2314, R2317, R2319, R2322, R2324, R2327, R2329, R2331, R2334, R2337, R2339, R2342, R2344, R2347, R2350, R2353, R2355, R2358, R2361, R2364, R2366, R2369, R2372, R2374, R2377, R2380, R2382, R2385, R2388, R2390, R2393, R2396, R2399, R2401, R2404, R2406, R2409, R2411, R2414, R2416, R2418, R2421, R2424, R2426, R2429, R2431, R2434, R2436, R2439, R2441, R2443, R2446, R2449, R2451, R2454, R2456, R2459, R2461, R2464, R2466, R2468, R2471, R2474, R2476, R2478, R2481, R2484, R2486, R2489, R2491, R2494, R2496, R2499, R2501, R2503, R2506, R2509, R2511, R2513, R2516, R2519, R2521, R2524, R2526, R2529, R2531, R2534, R2536, R2539, R2541, R2543, R2545, R2548, R2550, R2553, R2555, R2558, R2560, R2563, R2565, R2568, R2570, R2572, R2574, R2577, R2579, R2582, R2584, R2587, R2589, R2592, R2594, R2597, R2599, R2601, R2603, R2606, R2608, R2611, R2613, R2616, R2618, R2621, R2623, R2626, R2628, R2630, R2632, R2635, R2637, R2640, R2642, R2645, R2647, R2650, R2652, R2655, R2657, R2659, R2661, R2664, R2666, R2669, R2671, R2674, R2676, R2679, R2681, R2684, R2686, R2688, R2690, R2693, R2696, R2699, R2702, R2704, R2707, R2709, R2712, R2714, R2717, R2719, R2722, R2725, R2727, R2730, R2732, R2735, R2737, R2740, R2742, R2745, R2748, R2751, R2754, R2756, R2759, R2761, R2764, R2766, R2769, R2771, R2774, R2777, R2779, R2782, R2784, R2787, R2789, R2792, R2794, R2797, R2800, R2803, R2806, R2808, R2811, R2813, R2816, R2818, R2821, R2823, R2826, R2829, R2831, R2834, R2836, R2839, R2841, R2844, R2846, R2849, R2852, R2855, R2858, R2860, R2863, R2865, R2868, R2870, R2873, R2875, R2878, R2881, R2883, R2886, R2888, R2891, R2893, R2896, R2898, R2901, R2904, R2907, R2910, R2912, R2915, R2917, R2920, R2922, R2925, R2927, R2930, R2933, R2935, R2938, R2940, R2943, R2945, R2948, R2950, R2953, R2956, R2959, R2962, R2964, R2967, R2969, R2972, R2974, R2977, R2979, R2982, R2985, R2987, R2990, R2992, R2995, R2997, R3000, R3002, R3005, R3007, R3010, R3012, R3015, R3017, R3020, R3022, R3025, R3027, R3030, R3032, R3035, R3037, R3040, R3042, R3045, R3047, R3050, R3052, R3054, R3057, R3059, R3062, R3064, R3067, R3069, R3072, R3075, R3077, R3080, R3083, R3085, R3088, R3091, R3094, R3097, R3100, R3102, R3105, R3107, R3110, R3112, R3115, R3117, R3120, R3123, R3125, R3128, R3130, R3133, R3135, R3138, R3140, R3143, R3146, R3149, R3152, R3154, R3157, R3159, R3162, R3164, R3167, R3169, R3172, R3175, R3177, R3180, R3182, R3185, R3187, R3190, R3192, R3195, R3197, R3200, R3203, R3205, R3208, R3210, R3213, R3215, R3218, R3220, R3223, R3225, R3228, R3231: 10k; R_Axial_DIN0207_L6.3mm_D2.5mm_P5.08mm_Vertical
R2002, R2005, R2008, R2011, R2014, R2017, R2020, R2023, R2026, R2029, R2032, R2035, R2038, R2041, R2043, R2045, R2047, R2049, R2052, R2054, R2056, R2059, R2062, R2065, R2068, R2071, R2073, R2076, R2078, R2081, R2083, R2086, R2088, R2091, R2094, R2096, R2099, R2101, R2104, R2106, R2109, R2111, R2114, R2117, R2120, R2123, R2126, R2129, R2131, R2134, R2136, R2139, R2141, R2144, R2146, R2149, R2152, R2154, R2157, R2159, R2162, R2164, R2167, R2169, R2172, R2175, R2178, R2181, R2183, R2186, R2188, R2191, R2193, R2196, R2198, R2201, R2204, R2206, R2209, R2211, R2214, R2216, R2219, R2221, R2224, R2227, R2230, R2233, R2235, R2238, R2240, R2243, R2245, R2248, R2250, R2253, R2256, R2258, R2261, R2263, R2266, R2268, R2271, R2273, R2276, R2279, R2282, R2285, R2287, R2290, R2292, R2295, R2297, R2300, R2302, R2305, R2308, R2310, R2313, R2315, R2318, R2320, R2323, R2325, R2328, R2330, R2332, R2335, R2338, R2340, R2343, R2345, R2348, R2351, R2354, R2356, R2359, R2362, R2365, R2367, R2370, R2373, R2375, R2378, R2381, R2383, R2386, R2389, R2391, R2394, R2397, R2400, R2402, R2405, R2407, R2410, R2412, R2415, R2417, R2419, R2422, R2425, R2427, R2430, R2432, R2435, R2437, R2440, R2442, R2444, R2447, R2450, R2452, R2455, R2457, R2460, R2462, R2465, R2467, R2469, R2472, R2475, R2477, R2479, R2482, R2485, R2487, R2490, R2492, R2495, R2497, R2500, R2502, R2504, R2507, R2510, R2512, R2514, R2517, R2520, R2522, R2525, R2527, R2530, R2532, R2535, R2537, R2540, R2542, R2544, R2546, R2549, R2551, R2554, R2556, R2559, R2561, R2564, R2566, R2569, R2571, R2573, R2575, R2578, R2580, R2583, R2585, R2588, R2590, R2593, R2595, R2598, R2600, R2602, R2604, R2607, R2609, R2612, R2614, R2617, R2619, R2622, R2624, R2627, R2629, R2631, R2633, R2636, R2638, R2641, R2643, R2646, R2648, R2651, R2653, R2656, R2658, R2660, R2662, R2665, R2667, R2670, R2672, R2675, R2677, R2680, R2682, R2685, R2687, R2689, R2691, R2694, R2697, R2700, R2703, R2705, R2708, R2710, R2713, R2715, R2718, R2720, R2723, R2726, R2728, R2731, R2733, R2736, R2738, R2741, R2743, R2746, R2749, R2752, R2755, R2757, R2760, R2762, R2765, R2767, R2770, R2772, R2775, R2778, R2780, R2783, R2785, R2788, R2790, R2793, R2795, R2798, R2801, R2804, R2807, R2809, R2812, R2814, R2817, R2819, R2822, R2824, R2827, R2830, R2832, R2835, R2837, R2840, R2842, R2845, R2847, R2850, R2853, R2856, R2859, R2861, R2864, R2866, R2869, R2871, R2874, R2876, R2879, R2882, R2884, R2887, R2889, R2892, R2894, R2897, R2899, R2902, R2905, R2908, R2911, R2913, R2916, R2918, R2921, R2923, R2926, R2928, R2931, R2934, R2936, R2939, R2941, R2944, R2946, R2949, R2951, R2954, R2957, R2960, R2963, R2965, R2968, R2970, R2973, R2975, R2978, R2980, R2983, R2986, R2988, R2991, R2993, R2996, R2998, R3001, R3003, R3006, R3008, R3011, R3013, R3016, R3018, R3021, R3023, R3026, R3028, R3031, R3033, R3036, R3038, R3041, R3043, R3046, R3048, R3051, R3053, R3055, R3058, R3060, R3063, R3065, R3068, R3070, R3073, R3076, R3078, R3081, R3084, R3086, R3089, R3092, R3095, R3098, R3101, R3103, R3106, R3108, R3111, R3113, R3116, R3118, R3121, R3124, R3126, R3129, R3131, R3134, R3136, R3139, R3141, R3144, R3147, R3150, R3153, R3155, R3158, R3160, R3163, R3165, R3168, R3170, R3173, R3176, R3178, R3181, R3183, R3186, R3188, R3191, R3193, R3196, R3198, R3201, R3204, R3206, R3209, R3211, R3214, R3216, R3219, R3221, R3224, R3226, R3229, R3232: 22k; R_Axial_DIN0207_L6.3mm_D2.5mm_P5.08mm_Vertical
R2021, R2027, R2039, R2050, R2057, R2063, R2066, R2069, R2074, R2079, R2084, R2089, R2092, R2097, R2107, R2112, R2121, R2124, R2127, R2132, R2137, R2142, R2147, R2150, R2155, R2165, R2173, R2176, R2179, R2184, R2189, R2194, R2199, R2202, R2207, R2217, R2225, R2228, R2231, R2236, R2241, R2246, R2251, R2254, R2259, R2269, R2277, R2280, R2283, R2288, R2293, R2298, R2303, R2306, R2311, R2316, R2321, R2326, R2341, R2346, R2352, R2357, R2363, R2368, R2371, R2376, R2379, R2384, R2387, R2395, R2398, R2403, R2408, R2420, R2423, R2428, R2433, R2445, R2448, R2453, R2458, R2470, R2473, R2483, R2488, R2493, R2498, R2505, R2508, R2515, R2518, R2523, R2528, R2533, R2538, R2547, R2552, R2557, R2562, R2567, R2576, R2581, R2586, R2591, R2596, R2605, R2610, R2615, R2620, R2625, R2634, R2639, R2644, R2649, R2654, R2663, R2668, R2673, R2678, R2683, R2695, R2698, R2701, R2706, R2711, R2716, R2721, R2724, R2729, R2739, R2747, R2750, R2753, R2758, R2763, R2768, R2773, R2776, R2781, R2791, R2799, R2802, R2805, R2810, R2815, R2820, R2825, R2828, R2833, R2843, R2851, R2854, R2857, R2862, R2867, R2872, R2877, R2880, R2885, R2895, R2903, R2906, R2909, R2914, R2919, R2924, R2929, R2932, R2937, R2947, R2955, R2958, R2961, R2966, R2971, R2976, R2981, R2984, R2989, R2999, R3004, R3009, R3014, R3019, R3024, R3029, R3034, R3039, R3044, R3049, R3056, R3061, R3066, R3071, R3074, R3079, R3082, R3087, R3093, R3096, R3099, R3104, R3109, R3114, R3119, R3122, R3127, R3137, R3145, R3148, R3151, R3156, R3161, R3166, R3171, R3174, R3179, R3189, R3194, R3199, R3202, R3207, R3212, R3217, R3222, R3230: 4.7k; R_Axial_DIN0207_L6.3mm_D2.5mm_P5.08mm_Vertical

Connections:
+5V: R2000.1, R2003.1, R2006.1, R2009.1, R2012.1, R2015.1, R2018.1, R2021.1, R2024.1, R2027.1, R2030.1, R2033.1, R2036.1, R2039.1, R2050.1, R2057.1, R2060.1, R2063.1, R2066.1, R2069.1, R2074.1, R2079.1, R2084.1, R2089.1, R2092.1, R2097.1, R2102.1, R2107.1, R2112.1, R2115.1, R2118.1, R2121.1, R2124.1, R2127.1, R2132.1, R2137.1, R2142.1, R2147.1, R2150.1, R2155.1, R2160.1, R2165.1, R2170.1, R2173.1, R2176.1, R2179.1, R2184.1, R2189.1, R2194.1, R2199.1, R2202.1, R2207.1, R2212.1, R2217.1, R2222.1, R2225.1, R2228.1, R2231.1, R2236.1, R2241.1, R2246.1, R2251.1, R2254.1, R2259.1, R2264.1, R2269.1, R2274.1, R2277.1, R2280.1, R2283.1, R2288.1, R2293.1, R2298.1, R2303.1, R2306.1, R2311.1, R2316.1, R2321.1, R2326.1, R2333.1, R2336.1, R2341.1, R2346.1, R2349.1, R2352.1, R2357.1, R2360.1, R2363.1, R2368.1, R2371.1, R2376.1, R2379.1, R2384.1, R2387.1, R2392.1, R2395.1, R2398.1, R2403.1, R2408.1, R2413.1, R2420.1, R2423.1, R2428.1, R2433.1, R2438.1, R2445.1, R2448.1, R2453.1, R2458.1, R2463.1, R2470.1, R2473.1, R2480.1, R2483.1, R2488.1, R2493.1, R2498.1, R2505.1, R2508.1, R2515.1, R2518.1, R2523.1, R2528.1, R2533.1, R2538.1, R2547.1, R2552.1, R2557.1, R2562.1, R2567.1, R2576.1, R2581.1, R2586.1, R2591.1, R2596.1, R2605.1, R2610.1, R2615.1, R2620.1, R2625.1, R2634.1, R2639.1, R2644.1, R2649.1, R2654.1, R2663.1, R2668.1, R2673.1, R2678.1, R2683.1, R2692.1, R2695.1, R2698.1, R2701.1, R2706.1, R2711.1, R2716.1, R2721.1, R2724.1, R2729.1, R2734.1, R2739.1, R2744.1, R2747.1, R2750.1, R2753.1, R2758.1, R2763.1, R2768.1, R2773.1, R2776.1, R2781.1, R2786.1, R2791.1, R2796.1, R2799.1, R2802.1, R2805.1, R2810.1, R2815.1, R2820.1, R2825.1, R2828.1, R2833.1, R2838.1, R2843.1, R2848.1, R2851.1, R2854.1, R2857.1, R2862.1, R2867.1, R2872.1, R2877.1, R2880.1, R2885.1, R2890.1, R2895.1, R2900.1, R2903.1, R2906.1, R2909.1, R2914.1, R2919.1, R2924.1, R2929.1, R2932.1, R2937.1, R2942.1, R2947.1, R2952.1, R2955.1, R2958.1, R2961.1, R2966.1, R2971.1, R2976.1, R2981.1, R2984.1, R2989.1, R2994.1, R2999.1, R3004.1, R3009.1, R3014.1, R3019.1, R3024.1, R3029.1, R3034.1, R3039.1, R3044.1, R3049.1, R3056.1, R3061.1, R3066.1, R3071.1, R3074.1, R3079.1, R3082.1, R3087.1, R3090.1, R3093.1, R3096.1, R3099.1, R3104.1, R3109.1, R3114.1, R3119.1, R3122.1, R3127.1, R3132.1, R3137.1, R3142.1, R3145.1, R3148.1, R3151.1, R3156.1, R3161.1, R3166.1, R3171.1, R3174.1, R3179.1, R3184.1, R3189.1, R3194.1, R3199.1, R3202.1, R3207.1, R3212.1, R3217.1, R3222.1, R3227.1, R3230.1
A0: Q2157.3 (C), R2413.2, R2681.1
A1: Q2167.3 (C), R2438.2, R2652.1
A2: Q2177.3 (C), R2463.2, R2623.1
AD_N0: Q2155.3 (C), R2408.2, R2418.1
AD_N1: Q2165.3 (C), R2433.2, R2443.1
AD_N2: Q2175.3 (C), R2458.2, R2468.1
AK_N0: Q2151.3 (C), R2398.2, R2414.1
AK_N1: Q2161.3 (C), R2423.2, R2439.1
AK_N2: Q2171.3 (C), R2448.2, R2464.1
AM_N0: Q2153.3 (C), R2403.2, R2416.1
AM_N1: Q2163.3 (C), R2428.2, R2441.1
AM_N2: Q2173.3 (C), R2453.2, R2466.1
BUSY_N: Q2013.3 (C), Q2014.3 (C), Q2015.3 (C), Q2016.3 (C), Q2017.3 (C), R2039.2, R2055.1
BZ: Q2194.3 (C), R2505.2, R2513.1
BZ_N: Q2191.3 (C), R2498.2, R2506.1
CK1: Q2011.3 (C), R2033.2, R2061.1, R2119.1, R2171.1, R2223.1, R2275.1, R3223.1
CK2: Q2012.3 (C), R2036.2, R2693.1, R2745.1, R2797.1, R2849.1, R2901.1, R2953.1
CK_N: Q2010.3 (C), R2030.2, R2034.1, R2037.1, R3205.1, R3210.1
CLOCK: R2031.1
D4: Q2421.3 (C), R3079.2, R3097.1, R3100.1
D4_N: Q2419.3 (C), R3074.2, R3080.1
D5: Q2424.3 (C), R3087.2, R3149.1, R3152.1
D5_N: Q2422.3 (C), R3082.2, R3088.1
DIV0: Q2198.3 (C), R2515.2
DIV0_N: Q2195.3 (C), R2508.2, R2516.1
DN: Q2120.3 (C), R2048.1, R2316.2, R2322.1, R3197.1
DN.CLKB: Q2105.3 (C), R2277.2, R2309.1, R2312.1
DN.CLKN: Q2104.3 (C), R2274.2, R2278.1, R2286.1, R2289.1
DN.DN: Q2106.3 (C), R2280.2, R2291.1
DN.M1: Q2107.3 (C), R2283.2, R2294.1
DN.M2: Q2109.3 (C), R2288.2, R2301.1
DN.MQ: Q2111.3 (C), R2293.2, R2299.1, R2304.1, R2307.1
DN.MQI: Q2115.3 (C), R2303.2, R2314.1
DN.MQN: Q2113.3 (C), R2296.1, R2298.2
DN.QN: Q2122.3 (C), R2319.1, R2321.2
DN.S1: Q2116.3 (C), R2306.2, R2317.1
DN.S2: Q2118.3 (C), R2311.2, R2324.1
EB0: Q2185.3 (C), Q2186.3 (C), R2483.2
EB1: Q2187.3 (C), Q2188.3 (C), R2488.2
EB2: Q2189.3 (C), Q2190.3 (C), R2493.2
EN: Q2467.3 (C), R3199.2, R3203.1
ENCA_N0: R2396.1
ENCA_N1: R2421.1
ENCA_N2: R2446.1
ENCB_N0: R2484.1, R2499.1
ENCB_N1: R2489.1, R2501.1
ENCB_N2: R2494.1, R2503.1
ENL: Q2472.3 (C), R3212.2, R3218.1, R3225.1
ENLN: Q2474.3 (C), R3215.1, R3217.2
EN_N: Q2465.3 (C), Q2466.3 (C), R3194.2, R3200.1, R3208.1
G1: Q2468.3 (C), R3202.2, R3213.1
G2: Q2470.3 (C), R3207.2, R3220.1
GND: Q2000.1 (E), Q2001.1 (E), Q2002.1 (E), Q2003.1 (E), Q2004.1 (E), Q2005.1 (E), Q2006.1 (E), Q2007.1 (E), Q2008.1 (E), Q2009.1 (E), Q2010.1 (E), Q2011.1 (E), Q2012.1 (E), Q2013.1 (E), Q2014.1 (E), Q2015.1 (E), Q2016.1 (E), Q2017.1 (E), Q2020.1 (E), Q2021.1 (E), Q2022.1 (E), Q2023.1 (E), Q2024.1 (E), Q2026.1 (E), Q2028.1 (E), Q2030.1 (E), Q2032.1 (E), Q2033.1 (E), Q2035.1 (E), Q2037.1 (E), Q2039.1 (E), Q2041.1 (E), Q2042.1 (E), Q2043.1 (E), Q2044.1 (E), Q2045.1 (E), Q2046.1 (E), Q2048.1 (E), Q2050.1 (E), Q2052.1 (E), Q2054.1 (E), Q2055.1 (E), Q2057.1 (E), Q2059.1 (E), Q2061.1 (E), Q2063.1 (E), Q2064.1 (E), Q2065.1 (E), Q2066.1 (E), Q2068.1 (E), Q2070.1 (E), Q2072.1 (E), Q2074.1 (E), Q2075.1 (E), Q2077.1 (E), Q2079.1 (E), Q2081.1 (E), Q2083.1 (E), Q2084.1 (E), Q2085.1 (E), Q2086.1 (E), Q2088.1 (E), Q2090.1 (E), Q2092.1 (E), Q2094.1 (E), Q2095.1 (E), Q2097.1 (E), Q2099.1 (E), Q2101.1 (E), Q2103.1 (E), Q2104.1 (E), Q2105.1 (E), Q2106.1 (E), Q2108.1 (E), Q2110.1 (E), Q2112.1 (E), Q2114.1 (E), Q2115.1 (E), Q2117.1 (E), Q2119.1 (E), Q2121.1 (E), Q2123.1 (E), Q2124.1 (E), Q2125.1 (E), Q2126.1 (E), Q2127.1 (E), Q2128.1 (E), Q2129.1 (E), Q2131.1 (E), Q2132.1 (E), Q2133.1 (E), Q2135.1 (E), Q2136.1 (E), Q2137.1 (E), Q2138.1 (E), Q2139.1 (E), Q2140.1 (E), Q2142.1 (E), Q2143.1 (E), Q2145.1 (E), Q2146.1 (E), Q2147.1 (E), Q2148.1 (E), Q2149.1 (E), Q2150.1 (E), Q2152.1 (E), Q2154.1 (E), Q2156.1 (E), Q2159.1 (E), Q2160.1 (E), Q2162.1 (E), Q2164.1 (E), Q2166.1 (E), Q2169.1 (E), Q2170.1 (E), Q2172.1 (E), Q2174.1 (E), Q2176.1 (E), Q2179.1 (E), Q2180.1 (E), Q2183.1 (E), Q2184.1 (E), Q2185.1 (E), Q2186.1 (E), Q2187.1 (E), Q2188.1 (E), Q2189.1 (E), Q2190.1 (E), Q2193.1 (E), Q2194.1 (E), Q2197.1 (E), Q2198.1 (E), Q2200.1 (E), Q2202.1 (E), Q2204.1 (E), Q2206.1 (E), Q2210.1 (E), Q2212.1 (E), Q2214.1 (E), Q2216.1 (E), Q2218.1 (E), Q2222.1 (E), Q2224.1 (E), Q2226.1 (E), Q2228.1 (E), Q2230.1 (E), Q2234.1 (E), Q2236.1 (E), Q2238.1 (E), Q2240.1 (E), Q2242.1 (E), Q2246.1 (E), Q2248.1 (E), Q2250.1 (E), Q2252.1 (E), Q2254.1 (E), Q2258.1 (E), Q2260.1 (E), Q2262.1 (E), Q2264.1 (E), Q2266.1 (E), Q2270.1 (E), Q2271.1 (E), Q2272.1 (E), Q2273.1 (E), Q2275.1 (E), Q2277.1 (E), Q2279.1 (E), Q2281.1 (E), Q2282.1 (E), Q2284.1 (E), Q2286.1 (E), Q2288.1 (E), Q2290.1 (E), Q2291.1 (E), Q2292.1 (E), Q2293.1 (E), Q2295.1 (E), Q2297.1 (E), Q2299.1 (E), Q2301.1 (E), Q2302.1 (E), Q2304.1 (E), Q2306.1 (E), Q2308.1 (E), Q2310.1 (E), Q2311.1 (E), Q2312.1 (E), Q2313.1 (E), Q2315.1 (E), Q2317.1 (E), Q2319.1 (E), Q2321.1 (E), Q2322.1 (E), Q2324.1 (E), Q2326.1 (E), Q2328.1 (E), Q2330.1 (E), Q2331.1 (E), Q2332.1 (E), Q2333.1 (E), Q2335.1 (E), Q2337.1 (E), Q2339.1 (E), Q2341.1 (E), Q2342.1 (E), Q2344.1 (E), Q2346.1 (E), Q2348.1 (E), Q2350.1 (E), Q2351.1 (E), Q2352.1 (E), Q2353.1 (E), Q2355.1 (E), Q2357.1 (E), Q2359.1 (E), Q2361.1 (E), Q2362.1 (E), Q2364.1 (E), Q2366.1 (E), Q2368.1 (E), Q2370.1 (E), Q2371.1 (E), Q2372.1 (E), Q2373.1 (E), Q2375.1 (E), Q2377.1 (E), Q2379.1 (E), Q2381.1 (E), Q2382.1 (E), Q2384.1 (E), Q2386.1 (E), Q2388.1 (E), Q2390.1 (E), Q2392.1 (E), Q2394.1 (E), Q2396.1 (E), Q2398.1 (E), Q2400.1 (E), Q2402.1 (E), Q2404.1 (E), Q2406.1 (E), Q2408.1 (E), Q2411.1 (E), Q2413.1 (E), Q2415.1 (E), Q2417.1 (E), Q2418.1 (E), Q2420.1 (E), Q2421.1 (E), Q2423.1 (E), Q2424.1 (E), Q2425.1 (E), Q2426.1 (E), Q2427.1 (E), Q2429.1 (E), Q2431.1 (E), Q2433.1 (E), Q2435.1 (E), Q2436.1 (E), Q2438.1 (E), Q2440.1 (E), Q2442.1 (E), Q2444.1 (E), Q2445.1 (E), Q2446.1 (E), Q2447.1 (E), Q2449.1 (E), Q2451.1 (E), Q2453.1 (E), Q2455.1 (E), Q2456.1 (E), Q2458.1 (E), Q2460.1 (E), Q2462.1 (E), Q2464.1 (E), Q2465.1 (E), Q2466.1 (E), Q2467.1 (E), Q2469.1 (E), Q2471.1 (E), Q2473.1 (E), Q2475.1 (E), Q2477.1 (E), Q2478.1 (E), Q2479.1 (E), R2002.2, R2005.2, R2008.2, R2011.2, R2014.2, R2017.2, R2020.2, R2023.2, R2026.2, R2029.2, R2032.2, R2035.2, R2038.2, R2041.2, R2043.2, R2045.2, R2047.2, R2049.2, R2052.2, R2054.2, R2056.2, R2059.2, R2062.2, R2065.2, R2068.2, R2071.2, R2073.2, R2076.2, R2078.2, R2081.2, R2083.2, R2086.2, R2088.2, R2091.2, R2094.2, R2096.2, R2099.2, R2101.2, R2104.2, R2106.2, R2109.2, R2111.2, R2114.2, R2117.2, R2120.2, R2123.2, R2126.2, R2129.2, R2131.2, R2134.2, R2136.2, R2139.2, R2141.2, R2144.2, R2146.2, R2149.2, R2152.2, R2154.2, R2157.2, R2159.2, R2162.2, R2164.2, R2167.2, R2169.2, R2172.2, R2175.2, R2178.2, R2181.2, R2183.2, R2186.2, R2188.2, R2191.2, R2193.2, R2196.2, R2198.2, R2201.2, R2204.2, R2206.2, R2209.2, R2211.2, R2214.2, R2216.2, R2219.2, R2221.2, R2224.2, R2227.2, R2230.2, R2233.2, R2235.2, R2238.2, R2240.2, R2243.2, R2245.2, R2248.2, R2250.2, R2253.2, R2256.2, R2258.2, R2261.2, R2263.2, R2266.2, R2268.2, R2271.2, R2273.2, R2276.2, R2279.2, R2282.2, R2285.2, R2287.2, R2290.2, R2292.2, R2295.2, R2297.2, R2300.2, R2302.2, R2305.2, R2308.2, R2310.2, R2313.2, R2315.2, R2318.2, R2320.2, R2323.2, R2325.2, R2328.2, R2330.2, R2332.2, R2335.2, R2338.2, R2340.2, R2343.2, R2345.2, R2348.2, R2351.2, R2354.2, R2356.2, R2359.2, R2362.2, R2365.2, R2367.2, R2370.2, R2373.2, R2375.2, R2378.2, R2381.2, R2383.2, R2386.2, R2389.2, R2391.2, R2394.2, R2397.2, R2400.2, R2402.2, R2405.2, R2407.2, R2410.2, R2412.2, R2415.2, R2417.2, R2419.2, R2422.2, R2425.2, R2427.2, R2430.2, R2432.2, R2435.2, R2437.2, R2440.2, R2442.2, R2444.2, R2447.2, R2450.2, R2452.2, R2455.2, R2457.2, R2460.2, R2462.2, R2465.2, R2467.2, R2469.2, R2472.2, R2475.2, R2477.2, R2479.2, R2482.2, R2485.2, R2487.2, R2490.2, R2492.2, R2495.2, R2497.2, R2500.2, R2502.2, R2504.2, R2507.2, R2510.2, R2512.2, R2514.2, R2517.2, R2520.2, R2522.2, R2525.2, R2527.2, R2530.2, R2532.2, R2535.2, R2537.2, R2540.2, R2542.2, R2544.2, R2546.2, R2549.2, R2551.2, R2554.2, R2556.2, R2559.2, R2561.2, R2564.2, R2566.2, R2569.2, R2571.2, R2573.2, R2575.2, R2578.2, R2580.2, R2583.2, R2585.2, R2588.2, R2590.2, R2593.2, R2595.2, R2598.2, R2600.2, R2602.2, R2604.2, R2607.2, R2609.2, R2612.2, R2614.2, R2617.2, R2619.2, R2622.2, R2624.2, R2627.2, R2629.2, R2631.2, R2633.2, R2636.2, R2638.2, R2641.2, R2643.2, R2646.2, R2648.2, R2651.2, R2653.2, R2656.2, R2658.2, R2660.2, R2662.2, R2665.2, R2667.2, R2670.2, R2672.2, R2675.2, R2677.2, R2680.2, R2682.2, R2685.2, R2687.2, R2689.2, R2691.2, R2694.2, R2697.2, R2700.2, R2703.2, R2705.2, R2708.2, R2710.2, R2713.2, R2715.2, R2718.2, R2720.2, R2723.2, R2726.2, R2728.2, R2731.2, R2733.2, R2736.2, R2738.2, R2741.2, R2743.2, R2746.2, R2749.2, R2752.2, R2755.2, R2757.2, R2760.2, R2762.2, R2765.2, R2767.2, R2770.2, R2772.2, R2775.2, R2778.2, R2780.2, R2783.2, R2785.2, R2788.2, R2790.2, R2793.2, R2795.2, R2798.2, R2801.2, R2804.2, R2807.2, R2809.2, R2812.2, R2814.2, R2817.2, R2819.2, R2822.2, R2824.2, R2827.2, R2830.2, R2832.2, R2835.2, R2837.2, R2840.2, R2842.2, R2845.2, R2847.2, R2850.2, R2853.2, R2856.2, R2859.2, R2861.2, R2864.2, R2866.2, R2869.2, R2871.2, R2874.2, R2876.2, R2879.2, R2882.2, R2884.2, R2887.2, R2889.2, R2892.2, R2894.2, R2897.2, R2899.2, R2902.2, R2905.2, R2908.2, R2911.2, R2913.2, R2916.2, R2918.2, R2921.2, R2923.2, R2926.2, R2928.2, R2931.2, R2934.2, R2936.2, R2939.2, R2941.2, R2944.2, R2946.2, R2949.2, R2951.2, R2954.2, R2957.2, R2960.2, R2963.2, R2965.2, R2968.2, R2970.2, R2973.2, R2975.2, R2978.2, R2980.2, R2983.2, R2986.2, R2988.2, R2991.2, R2993.2, R2996.2, R2998.2, R3001.2, R3003.2, R3006.2, R3008.2, R3011.2, R3013.2, R3016.2, R3018.2, R3021.2, R3023.2, R3026.2, R3028.2, R3031.2, R3033.2, R3036.2, R3038.2, R3041.2, R3043.2, R3046.2, R3048.2, R3051.2, R3053.2, R3055.2, R3058.2, R3060.2, R3063.2, R3065.2, R3068.2, R3070.2, R3073.2, R3076.2, R3078.2, R3081.2, R3084.2, R3086.2, R3089.2, R3092.2, R3095.2, R3098.2, R3101.2, R3103.2, R3106.2, R3108.2, R3111.2, R3113.2, R3116.2, R3118.2, R3121.2, R3124.2, R3126.2, R3129.2, R3131.2, R3134.2, R3136.2, R3139.2, R3141.2, R3144.2, R3147.2, R3150.2, R3153.2, R3155.2, R3158.2, R3160.2, R3163.2, R3165.2, R3168.2, R3170.2, R3173.2, R3176.2, R3178.2, R3181.2, R3183.2, R3186.2, R3188.2, R3191.2, R3193.2, R3196.2, R3198.2, R3201.2, R3204.2, R3206.2, R3209.2, R3211.2, R3214.2, R3216.2, R3219.2, R3221.2, R3224.2, R3226.2, R3229.2, R3232.2
IDLE: Q2128.3 (C), Q2129.3 (C), R2336.2, R2534.1, R2563.1, R2592.1, R2616.1, R2645.1, R2674.1
KA0: Q2150.3 (C), R2395.2, R2401.1
KA1: Q2160.3 (C), R2420.2, R2426.1
KA2: Q2170.3 (C), R2445.2, R2451.1
KSEL: Q2149.3 (C), R2392.2, R2399.1, R2424.1, R2449.1
KSEL_N: Q2147.3 (C), Q2148.3 (C), R2387.2, R2393.1
L: Q2038.3 (C), R2040.1, R2102.2, R2108.1, R2113.1, R2125.1, R2128.1, R2337.1
L.CLKB: Q2023.3 (C), R2063.2, R2095.1, R2098.1
L.CLKN: Q2022.3 (C), R2060.2, R2064.1, R2072.1, R2075.1
L.DN: Q2024.3 (C), R2066.2, R2077.1
L.M1: Q2025.3 (C), R2069.2, R2080.1
L.M2: Q2027.3 (C), R2074.2, R2087.1
L.MQ: Q2029.3 (C), R2079.2, R2085.1, R2090.1, R2093.1
L.MQI: Q2033.3 (C), R2089.2, R2100.1
L.MQN: Q2031.3 (C), R2082.1, R2084.2
L.QN: Q2040.3 (C), R2105.1, R2107.2
L.S1: Q2034.3 (C), R2092.2, R2103.1
L.S2: Q2036.3 (C), R2097.2, R2110.1
LB: Q2043.3 (C), R2115.2, R2390.1, R2621.1, R2650.1, R2679.1
L_D: Q2021.3 (C), R2057.2, R2067.1, R2070.1
L_N: Q2042.3 (C), R2112.2, R2116.1
L_N_D: Q2018.3 (C), R2050.2, R2058.1
MEMCLK: Q2478.3 (C), R3227.2
MEMCLK2: Q2479.3 (C), R3091.1, R3143.1, R3230.2
MEMCLK_N: Q2476.3 (C), R3222.2, R3228.1, R3231.1
NX0: Q2267.3 (C), R2683.2, R2699.1, R2702.1
NX0.t0: Q2259.3 (C), R2663.2, R2684.1
NX0.t1: Q2261.3 (C), R2668.2, R2686.1
NX0.t2: Q2263.3 (C), R2673.2, R2688.1
NX0.t3: Q2265.3 (C), R2678.2, R2690.1
NX1: Q2255.3 (C), R2654.2, R2751.1, R2754.1
NX1.t0: Q2247.3 (C), R2634.2, R2655.1
NX1.t1: Q2249.3 (C), R2639.2, R2657.1
NX1.t2: Q2251.3 (C), R2644.2, R2659.1
NX1.t3: Q2253.3 (C), R2649.2, R2661.1
NX2: Q2243.3 (C), R2625.2, R2803.1, R2806.1
NX2.t0: Q2235.3 (C), R2605.2, R2626.1
NX2.t1: Q2237.3 (C), R2610.2, R2628.1
NX2.t2: Q2239.3 (C), R2615.2, R2630.1
NX2.t3: Q2241.3 (C), R2620.2, R2632.1
NX3: Q2231.3 (C), R2596.2, R2855.1, R2858.1
NX3.t0: Q2223.3 (C), R2576.2, R2597.1
NX3.t1: Q2225.3 (C), R2581.2, R2599.1
NX3.t2: Q2227.3 (C), R2586.2, R2601.1
NX3.t3: Q2229.3 (C), R2591.2, R2603.1
NX4: Q2219.3 (C), R2567.2, R2907.1, R2910.1
NX4.t0: Q2211.3 (C), R2547.2, R2568.1
NX4.t1: Q2213.3 (C), R2552.2, R2570.1
NX4.t2: Q2215.3 (C), R2557.2, R2572.1
NX4.t3: Q2217.3 (C), R2562.2, R2574.1
NX5: Q2207.3 (C), R2538.2, R2959.1, R2962.1
NX5.t0: Q2199.3 (C), R2518.2, R2539.1
NX5.t1: Q2201.3 (C), R2523.2, R2541.1
NX5.t2: Q2203.3 (C), R2528.2, R2543.1
NX5.t3: Q2205.3 (C), R2533.2, R2545.1
unnamed: Q2000.2 (B), R2001.2, R2002.1
unnamed: Q2001.2 (B), R2004.2, R2005.1
unnamed: Q2002.2 (B), R2007.2, R2008.1
unnamed: Q2003.2 (B), R2010.2, R2011.1
unnamed: Q2004.2 (B), R2013.2, R2014.1
unnamed: Q2005.2 (B), R2016.2, R2017.1
unnamed: Q2006.2 (B), R2019.2, R2020.1
unnamed: Q2007.2 (B), R2022.2, R2023.1
unnamed: Q2008.2 (B), R2025.2, R2026.1
unnamed: Q2009.2 (B), R2028.2, R2029.1
unnamed: Q2010.2 (B), R2031.2, R2032.1
unnamed: Q2011.2 (B), R2034.2, R2035.1
unnamed: Q2012.2 (B), R2037.2, R2038.1
unnamed: Q2013.2 (B), R2040.2, R2041.1
unnamed: Q2014.2 (B), R2042.2, R2043.1
unnamed: Q2015.2 (B), R2044.2, R2045.1
unnamed: Q2016.2 (B), R2046.2, R2047.1
unnamed: Q2017.2 (B), R2048.2, R2049.1
unnamed: Q2018.1 (E), Q2019.3 (C)
unnamed: Q2018.2 (B), R2051.2, R2052.1
unnamed: Q2019.1 (E), Q2020.3 (C)
unnamed: Q2019.2 (B), R2053.2, R2054.1
unnamed: Q2020.2 (B), R2055.2, R2056.1
unnamed: Q2021.2 (B), R2058.2, R2059.1
unnamed: Q2022.2 (B), R2061.2, R2062.1
unnamed: Q2023.2 (B), R2064.2, R2065.1
unnamed: Q2024.2 (B), R2067.2, R2068.1
unnamed: Q2025.1 (E), Q2026.3 (C)
unnamed: Q2025.2 (B), R2070.2, R2071.1
unnamed: Q2026.2 (B), R2072.2, R2073.1
unnamed: Q2027.1 (E), Q2028.3 (C)
unnamed: Q2027.2 (B), R2075.2, R2076.1
unnamed: Q2028.2 (B), R2077.2, R2078.1
unnamed: Q2029.1 (E), Q2030.3 (C)
unnamed: Q2029.2 (B), R2080.2, R2081.1
unnamed: Q2030.2 (B), R2082.2, R2083.1
unnamed: Q2031.1 (E), Q2032.3 (C)
unnamed: Q2031.2 (B), R2085.2, R2086.1
unnamed: Q2032.2 (B), R2087.2, R2088.1
unnamed: Q2033.2 (B), R2090.2, R2091.1
unnamed: Q2034.1 (E), Q2035.3 (C)
unnamed: Q2034.2 (B), R2093.2, R2094.1
unnamed: Q2035.2 (B), R2095.2, R2096.1
unnamed: Q2036.1 (E), Q2037.3 (C)
unnamed: Q2036.2 (B), R2098.2, R2099.1
unnamed: Q2037.2 (B), R2100.2, R2101.1
unnamed: Q2038.1 (E), Q2039.3 (C)
unnamed: Q2038.2 (B), R2103.2, R2104.1
unnamed: Q2039.2 (B), R2105.2, R2106.1
unnamed: Q2040.1 (E), Q2041.3 (C)
unnamed: Q2040.2 (B), R2108.2, R2109.1
unnamed: Q2041.2 (B), R2110.2, R2111.1
unnamed: Q2042.2 (B), R2113.2, R2114.1
unnamed: Q2043.2 (B), R2116.2, R2117.1
unnamed: Q2044.2 (B), R2119.2, R2120.1
unnamed: Q2045.2 (B), R2122.2, R2123.1
unnamed: Q2046.2 (B), R2125.2, R2126.1
unnamed: Q2047.1 (E), Q2048.3 (C)
unnamed: Q2047.2 (B), R2128.2, R2129.1
unnamed: Q2048.2 (B), R2130.2, R2131.1
unnamed: Q2049.1 (E), Q2050.3 (C)
unnamed: Q2049.2 (B), R2133.2, R2134.1
unnamed: Q2050.2 (B), R2135.2, R2136.1
unnamed: Q2051.1 (E), Q2052.3 (C)
unnamed: Q2051.2 (B), R2138.2, R2139.1
unnamed: Q2052.2 (B), R2140.2, R2141.1
unnamed: Q2053.1 (E), Q2054.3 (C)
unnamed: Q2053.2 (B), R2143.2, R2144.1
unnamed: Q2054.2 (B), R2145.2, R2146.1
unnamed: Q2055.2 (B), R2148.2, R2149.1
unnamed: Q2056.1 (E), Q2057.3 (C)
unnamed: Q2056.2 (B), R2151.2, R2152.1
unnamed: Q2057.2 (B), R2153.2, R2154.1
unnamed: Q2058.1 (E), Q2059.3 (C)
unnamed: Q2058.2 (B), R2156.2, R2157.1
unnamed: Q2059.2 (B), R2158.2, R2159.1
unnamed: Q2060.1 (E), Q2061.3 (C)
unnamed: Q2060.2 (B), R2161.2, R2162.1
unnamed: Q2061.2 (B), R2163.2, R2164.1
unnamed: Q2062.1 (E), Q2063.3 (C)
unnamed: Q2062.2 (B), R2166.2, R2167.1
unnamed: Q2063.2 (B), R2168.2, R2169.1
unnamed: Q2064.2 (B), R2171.2, R2172.1
unnamed: Q2065.2 (B), R2174.2, R2175.1
unnamed: Q2066.2 (B), R2177.2, R2178.1
unnamed: Q2067.1 (E), Q2068.3 (C)
unnamed: Q2067.2 (B), R2180.2, R2181.1
unnamed: Q2068.2 (B), R2182.2, R2183.1
unnamed: Q2069.1 (E), Q2070.3 (C)
unnamed: Q2069.2 (B), R2185.2, R2186.1
unnamed: Q2070.2 (B), R2187.2, R2188.1
unnamed: Q2071.1 (E), Q2072.3 (C)
unnamed: Q2071.2 (B), R2190.2, R2191.1
unnamed: Q2072.2 (B), R2192.2, R2193.1
unnamed: Q2073.1 (E), Q2074.3 (C)
unnamed: Q2073.2 (B), R2195.2, R2196.1
unnamed: Q2074.2 (B), R2197.2, R2198.1
unnamed: Q2075.2 (B), R2200.2, R2201.1
unnamed: Q2076.1 (E), Q2077.3 (C)
unnamed: Q2076.2 (B), R2203.2, R2204.1
unnamed: Q2077.2 (B), R2205.2, R2206.1
unnamed: Q2078.1 (E), Q2079.3 (C)
unnamed: Q2078.2 (B), R2208.2, R2209.1
unnamed: Q2079.2 (B), R2210.2, R2211.1
unnamed: Q2080.1 (E), Q2081.3 (C)
unnamed: Q2080.2 (B), R2213.2, R2214.1
unnamed: Q2081.2 (B), R2215.2, R2216.1
unnamed: Q2082.1 (E), Q2083.3 (C)
unnamed: Q2082.2 (B), R2218.2, R2219.1
unnamed: Q2083.2 (B), R2220.2, R2221.1
unnamed: Q2084.2 (B), R2223.2, R2224.1
unnamed: Q2085.2 (B), R2226.2, R2227.1
unnamed: Q2086.2 (B), R2229.2, R2230.1
unnamed: Q2087.1 (E), Q2088.3 (C)
unnamed: Q2087.2 (B), R2232.2, R2233.1
unnamed: Q2088.2 (B), R2234.2, R2235.1
unnamed: Q2089.1 (E), Q2090.3 (C)
unnamed: Q2089.2 (B), R2237.2, R2238.1
unnamed: Q2090.2 (B), R2239.2, R2240.1
unnamed: Q2091.1 (E), Q2092.3 (C)
unnamed: Q2091.2 (B), R2242.2, R2243.1
unnamed: Q2092.2 (B), R2244.2, R2245.1
unnamed: Q2093.1 (E), Q2094.3 (C)
unnamed: Q2093.2 (B), R2247.2, R2248.1
unnamed: Q2094.2 (B), R2249.2, R2250.1
unnamed: Q2095.2 (B), R2252.2, R2253.1
unnamed: Q2096.1 (E), Q2097.3 (C)
unnamed: Q2096.2 (B), R2255.2, R2256.1
unnamed: Q2097.2 (B), R2257.2, R2258.1
unnamed: Q2098.1 (E), Q2099.3 (C)
unnamed: Q2098.2 (B), R2260.2, R2261.1
unnamed: Q2099.2 (B), R2262.2, R2263.1
unnamed: Q2100.1 (E), Q2101.3 (C)
unnamed: Q2100.2 (B), R2265.2, R2266.1
unnamed: Q2101.2 (B), R2267.2, R2268.1
unnamed: Q2102.1 (E), Q2103.3 (C)
unnamed: Q2102.2 (B), R2270.2, R2271.1
unnamed: Q2103.2 (B), R2272.2, R2273.1
unnamed: Q2104.2 (B), R2275.2, R2276.1
unnamed: Q2105.2 (B), R2278.2, R2279.1
unnamed: Q2106.2 (B), R2281.2, R2282.1
unnamed: Q2107.1 (E), Q2108.3 (C)
unnamed: Q2107.2 (B), R2284.2, R2285.1
unnamed: Q2108.2 (B), R2286.2, R2287.1
unnamed: Q2109.1 (E), Q2110.3 (C)
unnamed: Q2109.2 (B), R2289.2, R2290.1
unnamed: Q2110.2 (B), R2291.2, R2292.1
unnamed: Q2111.1 (E), Q2112.3 (C)
unnamed: Q2111.2 (B), R2294.2, R2295.1
unnamed: Q2112.2 (B), R2296.2, R2297.1
unnamed: Q2113.1 (E), Q2114.3 (C)
unnamed: Q2113.2 (B), R2299.2, R2300.1
unnamed: Q2114.2 (B), R2301.2, R2302.1
unnamed: Q2115.2 (B), R2304.2, R2305.1
unnamed: Q2116.1 (E), Q2117.3 (C)
unnamed: Q2116.2 (B), R2307.2, R2308.1
unnamed: Q2117.2 (B), R2309.2, R2310.1
unnamed: Q2118.1 (E), Q2119.3 (C)
unnamed: Q2118.2 (B), R2312.2, R2313.1
unnamed: Q2119.2 (B), R2314.2, R2315.1
unnamed: Q2120.1 (E), Q2121.3 (C)
unnamed: Q2120.2 (B), R2317.2, R2318.1
unnamed: Q2121.2 (B), R2319.2, R2320.1
unnamed: Q2122.1 (E), Q2123.3 (C)
unnamed: Q2122.2 (B), R2322.2, R2323.1
unnamed: Q2123.2 (B), R2324.2, R2325.1
unnamed: Q2124.2 (B), R2327.2, R2328.1
unnamed: Q2125.2 (B), R2329.2, R2330.1
unnamed: Q2126.2 (B), R2331.2, R2332.1
unnamed: Q2127.2 (B), R2334.2, R2335.1
unnamed: Q2128.2 (B), R2337.2, R2338.1
unnamed: Q2129.2 (B), R2339.2, R2340.1
unnamed: Q2130.1 (E), Q2131.3 (C)
unnamed: Q2130.2 (B), R2342.2, R2343.1
unnamed: Q2131.2 (B), R2344.2, R2345.1
unnamed: Q2132.2 (B), R2347.2, R2348.1
unnamed: Q2133.2 (B), R2350.2, R2351.1
unnamed: Q2134.1 (E), Q2135.3 (C)
unnamed: Q2134.2 (B), R2353.2, R2354.1
unnamed: Q2135.2 (B), R2355.2, R2356.1
unnamed: Q2136.2 (B), R2358.2, R2359.1
unnamed: Q2137.2 (B), R2361.2, R2362.1
unnamed: Q2138.2 (B), R2364.2, R2365.1
unnamed: Q2139.2 (B), R2366.2, R2367.1
unnamed: Q2140.2 (B), R2369.2, R2370.1
unnamed: Q2141.1 (E), Q2142.3 (C)
unnamed: Q2141.2 (B), R2372.2, R2373.1
unnamed: Q2142.2 (B), R2374.2, R2375.1
unnamed: Q2143.2 (B), R2377.2, R2378.1
unnamed: Q2144.1 (E), Q2145.3 (C)
unnamed: Q2144.2 (B), R2380.2, R2381.1
unnamed: Q2145.2 (B), R2382.2, R2383.1
unnamed: Q2146.2 (B), R2385.2, R2386.1
unnamed: Q2147.2 (B), R2388.2, R2389.1
unnamed: Q2148.2 (B), R2390.2, R2391.1
unnamed: Q2149.2 (B), R2393.2, R2394.1
unnamed: Q2150.2 (B), R2396.2, R2397.1
unnamed: Q2151.1 (E), Q2152.3 (C)
unnamed: Q2151.2 (B), R2399.2, R2400.1
unnamed: Q2152.2 (B), R2401.2, R2402.1
unnamed: Q2153.1 (E), Q2154.3 (C)
unnamed: Q2153.2 (B), R2404.2, R2405.1
unnamed: Q2154.2 (B), R2406.2, R2407.1
unnamed: Q2155.1 (E), Q2156.3 (C)
unnamed: Q2155.2 (B), R2409.2, R2410.1
unnamed: Q2156.2 (B), R2411.2, R2412.1
unnamed: Q2157.1 (E), Q2158.3 (C)
unnamed: Q2157.2 (B), R2414.2, R2415.1
unnamed: Q2158.1 (E), Q2159.3 (C)
unnamed: Q2158.2 (B), R2416.2, R2417.1
unnamed: Q2159.2 (B), R2418.2, R2419.1
unnamed: Q2160.2 (B), R2421.2, R2422.1
unnamed: Q2161.1 (E), Q2162.3 (C)
unnamed: Q2161.2 (B), R2424.2, R2425.1
unnamed: Q2162.2 (B), R2426.2, R2427.1
unnamed: Q2163.1 (E), Q2164.3 (C)
unnamed: Q2163.2 (B), R2429.2, R2430.1
unnamed: Q2164.2 (B), R2431.2, R2432.1
unnamed: Q2165.1 (E), Q2166.3 (C)
unnamed: Q2165.2 (B), R2434.2, R2435.1
unnamed: Q2166.2 (B), R2436.2, R2437.1
unnamed: Q2167.1 (E), Q2168.3 (C)
unnamed: Q2167.2 (B), R2439.2, R2440.1
unnamed: Q2168.1 (E), Q2169.3 (C)
unnamed: Q2168.2 (B), R2441.2, R2442.1
unnamed: Q2169.2 (B), R2443.2, R2444.1
unnamed: Q2170.2 (B), R2446.2, R2447.1
unnamed: Q2171.1 (E), Q2172.3 (C)
unnamed: Q2171.2 (B), R2449.2, R2450.1
unnamed: Q2172.2 (B), R2451.2, R2452.1
unnamed: Q2173.1 (E), Q2174.3 (C)
unnamed: Q2173.2 (B), R2454.2, R2455.1
unnamed: Q2174.2 (B), R2456.2, R2457.1
unnamed: Q2175.1 (E), Q2176.3 (C)
unnamed: Q2175.2 (B), R2459.2, R2460.1
unnamed: Q2176.2 (B), R2461.2, R2462.1
unnamed: Q2177.1 (E), Q2178.3 (C)
unnamed: Q2177.2 (B), R2464.2, R2465.1
unnamed: Q2178.1 (E), Q2179.3 (C)
unnamed: Q2178.2 (B), R2466.2, R2467.1
unnamed: Q2179.2 (B), R2468.2, R2469.1
unnamed: Q2180.2 (B), R2471.2, R2472.1
unnamed: Q2181.1 (E), Q2182.3 (C)
unnamed: Q2181.2 (B), R2474.2, R2475.1
unnamed: Q2182.1 (E), Q2183.3 (C)
unnamed: Q2182.2 (B), R2476.2, R2477.1
unnamed: Q2183.2 (B), R2478.2, R2479.1
unnamed: Q2184.2 (B), R2481.2, R2482.1
unnamed: Q2185.2 (B), R2484.2, R2485.1
unnamed: Q2186.2 (B), R2486.2, R2487.1
unnamed: Q2187.2 (B), R2489.2, R2490.1
unnamed: Q2188.2 (B), R2491.2, R2492.1
unnamed: Q2189.2 (B), R2494.2, R2495.1
unnamed: Q2190.2 (B), R2496.2, R2497.1
unnamed: Q2191.1 (E), Q2192.3 (C)
unnamed: Q2191.2 (B), R2499.2, R2500.1
unnamed: Q2192.1 (E), Q2193.3 (C)
unnamed: Q2192.2 (B), R2501.2, R2502.1
unnamed: Q2193.2 (B), R2503.2, R2504.1
unnamed: Q2194.2 (B), R2506.2, R2507.1
unnamed: Q2195.1 (E), Q2196.3 (C)
unnamed: Q2195.2 (B), R2509.2, R2510.1
unnamed: Q2196.1 (E), Q2197.3 (C)
unnamed: Q2196.2 (B), R2511.2, R2512.1
unnamed: Q2197.2 (B), R2513.2, R2514.1
unnamed: Q2198.2 (B), R2516.2, R2517.1
unnamed: Q2199.1 (E), Q2200.3 (C)
unnamed: Q2199.2 (B), R2519.2, R2520.1
unnamed: Q2200.2 (B), R2521.2, R2522.1
unnamed: Q2201.1 (E), Q2202.3 (C)
unnamed: Q2201.2 (B), R2524.2, R2525.1
unnamed: Q2202.2 (B), R2526.2, R2527.1
unnamed: Q2203.1 (E), Q2204.3 (C)
unnamed: Q2203.2 (B), R2529.2, R2530.1
unnamed: Q2204.2 (B), R2531.2, R2532.1
unnamed: Q2205.1 (E), Q2206.3 (C)
unnamed: Q2205.2 (B), R2534.2, R2535.1
unnamed: Q2206.2 (B), R2536.2, R2537.1
unnamed: Q2207.1 (E), Q2208.3 (C)
unnamed: Q2207.2 (B), R2539.2, R2540.1
unnamed: Q2208.1 (E), Q2209.3 (C)
unnamed: Q2208.2 (B), R2541.2, R2542.1
unnamed: Q2209.1 (E), Q2210.3 (C)
unnamed: Q2209.2 (B), R2543.2, R2544.1
unnamed: Q2210.2 (B), R2545.2, R2546.1
unnamed: Q2211.1 (E), Q2212.3 (C)
unnamed: Q2211.2 (B), R2548.2, R2549.1
unnamed: Q2212.2 (B), R2550.2, R2551.1
unnamed: Q2213.1 (E), Q2214.3 (C)
unnamed: Q2213.2 (B), R2553.2, R2554.1
unnamed: Q2214.2 (B), R2555.2, R2556.1
unnamed: Q2215.1 (E), Q2216.3 (C)
unnamed: Q2215.2 (B), R2558.2, R2559.1
unnamed: Q2216.2 (B), R2560.2, R2561.1
unnamed: Q2217.1 (E), Q2218.3 (C)
unnamed: Q2217.2 (B), R2563.2, R2564.1
unnamed: Q2218.2 (B), R2565.2, R2566.1
unnamed: Q2219.1 (E), Q2220.3 (C)
unnamed: Q2219.2 (B), R2568.2, R2569.1
unnamed: Q2220.1 (E), Q2221.3 (C)
unnamed: Q2220.2 (B), R2570.2, R2571.1
unnamed: Q2221.1 (E), Q2222.3 (C)
unnamed: Q2221.2 (B), R2572.2, R2573.1
unnamed: Q2222.2 (B), R2574.2, R2575.1
unnamed: Q2223.1 (E), Q2224.3 (C)
unnamed: Q2223.2 (B), R2577.2, R2578.1
unnamed: Q2224.2 (B), R2579.2, R2580.1
unnamed: Q2225.1 (E), Q2226.3 (C)
unnamed: Q2225.2 (B), R2582.2, R2583.1
unnamed: Q2226.2 (B), R2584.2, R2585.1
unnamed: Q2227.1 (E), Q2228.3 (C)
unnamed: Q2227.2 (B), R2587.2, R2588.1
unnamed: Q2228.2 (B), R2589.2, R2590.1
unnamed: Q2229.1 (E), Q2230.3 (C)
unnamed: Q2229.2 (B), R2592.2, R2593.1
unnamed: Q2230.2 (B), R2594.2, R2595.1
unnamed: Q2231.1 (E), Q2232.3 (C)
unnamed: Q2231.2 (B), R2597.2, R2598.1
unnamed: Q2232.1 (E), Q2233.3 (C)
unnamed: Q2232.2 (B), R2599.2, R2600.1
unnamed: Q2233.1 (E), Q2234.3 (C)
unnamed: Q2233.2 (B), R2601.2, R2602.1
unnamed: Q2234.2 (B), R2603.2, R2604.1
unnamed: Q2235.1 (E), Q2236.3 (C)
unnamed: Q2235.2 (B), R2606.2, R2607.1
unnamed: Q2236.2 (B), R2608.2, R2609.1
unnamed: Q2237.1 (E), Q2238.3 (C)
unnamed: Q2237.2 (B), R2611.2, R2612.1
unnamed: Q2238.2 (B), R2613.2, R2614.1
unnamed: Q2239.1 (E), Q2240.3 (C)
unnamed: Q2239.2 (B), R2616.2, R2617.1
unnamed: Q2240.2 (B), R2618.2, R2619.1
unnamed: Q2241.1 (E), Q2242.3 (C)
unnamed: Q2241.2 (B), R2621.2, R2622.1
unnamed: Q2242.2 (B), R2623.2, R2624.1
unnamed: Q2243.1 (E), Q2244.3 (C)
unnamed: Q2243.2 (B), R2626.2, R2627.1
unnamed: Q2244.1 (E), Q2245.3 (C)
unnamed: Q2244.2 (B), R2628.2, R2629.1
unnamed: Q2245.1 (E), Q2246.3 (C)
unnamed: Q2245.2 (B), R2630.2, R2631.1
unnamed: Q2246.2 (B), R2632.2, R2633.1
unnamed: Q2247.1 (E), Q2248.3 (C)
unnamed: Q2247.2 (B), R2635.2, R2636.1
unnamed: Q2248.2 (B), R2637.2, R2638.1
unnamed: Q2249.1 (E), Q2250.3 (C)
unnamed: Q2249.2 (B), R2640.2, R2641.1
unnamed: Q2250.2 (B), R2642.2, R2643.1
unnamed: Q2251.1 (E), Q2252.3 (C)
unnamed: Q2251.2 (B), R2645.2, R2646.1
unnamed: Q2252.2 (B), R2647.2, R2648.1
unnamed: Q2253.1 (E), Q2254.3 (C)
unnamed: Q2253.2 (B), R2650.2, R2651.1
unnamed: Q2254.2 (B), R2652.2, R2653.1
unnamed: Q2255.1 (E), Q2256.3 (C)
unnamed: Q2255.2 (B), R2655.2, R2656.1
unnamed: Q2256.1 (E), Q2257.3 (C)
unnamed: Q2256.2 (B), R2657.2, R2658.1
unnamed: Q2257.1 (E), Q2258.3 (C)
unnamed: Q2257.2 (B), R2659.2, R2660.1
unnamed: Q2258.2 (B), R2661.2, R2662.1
unnamed: Q2259.1 (E), Q2260.3 (C)
unnamed: Q2259.2 (B), R2664.2, R2665.1
unnamed: Q2260.2 (B), R2666.2, R2667.1
unnamed: Q2261.1 (E), Q2262.3 (C)
unnamed: Q2261.2 (B), R2669.2, R2670.1
unnamed: Q2262.2 (B), R2671.2, R2672.1
unnamed: Q2263.1 (E), Q2264.3 (C)
unnamed: Q2263.2 (B), R2674.2, R2675.1
unnamed: Q2264.2 (B), R2676.2, R2677.1
unnamed: Q2265.1 (E), Q2266.3 (C)
unnamed: Q2265.2 (B), R2679.2, R2680.1
unnamed: Q2266.2 (B), R2681.2, R2682.1
unnamed: Q2267.1 (E), Q2268.3 (C)
unnamed: Q2267.2 (B), R2684.2, R2685.1
unnamed: Q2268.1 (E), Q2269.3 (C)
unnamed: Q2268.2 (B), R2686.2, R2687.1
unnamed: Q2269.1 (E), Q2270.3 (C)
unnamed: Q2269.2 (B), R2688.2, R2689.1
unnamed: Q2270.2 (B), R2690.2, R2691.1
unnamed: Q2271.2 (B), R2693.2, R2694.1
unnamed: Q2272.2 (B), R2696.2, R2697.1
unnamed: Q2273.2 (B), R2699.2, R2700.1
unnamed: Q2274.1 (E), Q2275.3 (C)
unnamed: Q2274.2 (B), R2702.2, R2703.1
unnamed: Q2275.2 (B), R2704.2, R2705.1
unnamed: Q2276.1 (E), Q2277.3 (C)
unnamed: Q2276.2 (B), R2707.2, R2708.1
unnamed: Q2277.2 (B), R2709.2, R2710.1
unnamed: Q2278.1 (E), Q2279.3 (C)
unnamed: Q2278.2 (B), R2712.2, R2713.1
unnamed: Q2279.2 (B), R2714.2, R2715.1
unnamed: Q2280.1 (E), Q2281.3 (C)
unnamed: Q2280.2 (B), R2717.2, R2718.1
unnamed: Q2281.2 (B), R2719.2, R2720.1
unnamed: Q2282.2 (B), R2722.2, R2723.1
unnamed: Q2283.1 (E), Q2284.3 (C)
unnamed: Q2283.2 (B), R2725.2, R2726.1
unnamed: Q2284.2 (B), R2727.2, R2728.1
unnamed: Q2285.1 (E), Q2286.3 (C)
unnamed: Q2285.2 (B), R2730.2, R2731.1
unnamed: Q2286.2 (B), R2732.2, R2733.1
unnamed: Q2287.1 (E), Q2288.3 (C)
unnamed: Q2287.2 (B), R2735.2, R2736.1
unnamed: Q2288.2 (B), R2737.2, R2738.1
unnamed: Q2289.1 (E), Q2290.3 (C)
unnamed: Q2289.2 (B), R2740.2, R2741.1
unnamed: Q2290.2 (B), R2742.2, R2743.1
unnamed: Q2291.2 (B), R2745.2, R2746.1
unnamed: Q2292.2 (B), R2748.2, R2749.1
unnamed: Q2293.2 (B), R2751.2, R2752.1
unnamed: Q2294.1 (E), Q2295.3 (C)
unnamed: Q2294.2 (B), R2754.2, R2755.1
unnamed: Q2295.2 (B), R2756.2, R2757.1
unnamed: Q2296.1 (E), Q2297.3 (C)
unnamed: Q2296.2 (B), R2759.2, R2760.1
unnamed: Q2297.2 (B), R2761.2, R2762.1
unnamed: Q2298.1 (E), Q2299.3 (C)
unnamed: Q2298.2 (B), R2764.2, R2765.1
unnamed: Q2299.2 (B), R2766.2, R2767.1
unnamed: Q2300.1 (E), Q2301.3 (C)
unnamed: Q2300.2 (B), R2769.2, R2770.1
unnamed: Q2301.2 (B), R2771.2, R2772.1
unnamed: Q2302.2 (B), R2774.2, R2775.1
unnamed: Q2303.1 (E), Q2304.3 (C)
unnamed: Q2303.2 (B), R2777.2, R2778.1
unnamed: Q2304.2 (B), R2779.2, R2780.1
unnamed: Q2305.1 (E), Q2306.3 (C)
unnamed: Q2305.2 (B), R2782.2, R2783.1
unnamed: Q2306.2 (B), R2784.2, R2785.1
unnamed: Q2307.1 (E), Q2308.3 (C)
unnamed: Q2307.2 (B), R2787.2, R2788.1
unnamed: Q2308.2 (B), R2789.2, R2790.1
unnamed: Q2309.1 (E), Q2310.3 (C)
unnamed: Q2309.2 (B), R2792.2, R2793.1
unnamed: Q2310.2 (B), R2794.2, R2795.1
unnamed: Q2311.2 (B), R2797.2, R2798.1
unnamed: Q2312.2 (B), R2800.2, R2801.1
unnamed: Q2313.2 (B), R2803.2, R2804.1
unnamed: Q2314.1 (E), Q2315.3 (C)
unnamed: Q2314.2 (B), R2806.2, R2807.1
unnamed: Q2315.2 (B), R2808.2, R2809.1
unnamed: Q2316.1 (E), Q2317.3 (C)
unnamed: Q2316.2 (B), R2811.2, R2812.1
unnamed: Q2317.2 (B), R2813.2, R2814.1
unnamed: Q2318.1 (E), Q2319.3 (C)
unnamed: Q2318.2 (B), R2816.2, R2817.1
unnamed: Q2319.2 (B), R2818.2, R2819.1
unnamed: Q2320.1 (E), Q2321.3 (C)
unnamed: Q2320.2 (B), R2821.2, R2822.1
unnamed: Q2321.2 (B), R2823.2, R2824.1
unnamed: Q2322.2 (B), R2826.2, R2827.1
unnamed: Q2323.1 (E), Q2324.3 (C)
unnamed: Q2323.2 (B), R2829.2, R2830.1
unnamed: Q2324.2 (B), R2831.2, R2832.1
unnamed: Q2325.1 (E), Q2326.3 (C)
unnamed: Q2325.2 (B), R2834.2, R2835.1
unnamed: Q2326.2 (B), R2836.2, R2837.1
unnamed: Q2327.1 (E), Q2328.3 (C)
unnamed: Q2327.2 (B), R2839.2, R2840.1
unnamed: Q2328.2 (B), R2841.2, R2842.1
unnamed: Q2329.1 (E), Q2330.3 (C)
unnamed: Q2329.2 (B), R2844.2, R2845.1
unnamed: Q2330.2 (B), R2846.2, R2847.1
unnamed: Q2331.2 (B), R2849.2, R2850.1
unnamed: Q2332.2 (B), R2852.2, R2853.1
unnamed: Q2333.2 (B), R2855.2, R2856.1
unnamed: Q2334.1 (E), Q2335.3 (C)
unnamed: Q2334.2 (B), R2858.2, R2859.1
unnamed: Q2335.2 (B), R2860.2, R2861.1
unnamed: Q2336.1 (E), Q2337.3 (C)
unnamed: Q2336.2 (B), R2863.2, R2864.1
unnamed: Q2337.2 (B), R2865.2, R2866.1
unnamed: Q2338.1 (E), Q2339.3 (C)
unnamed: Q2338.2 (B), R2868.2, R2869.1
unnamed: Q2339.2 (B), R2870.2, R2871.1
unnamed: Q2340.1 (E), Q2341.3 (C)
unnamed: Q2340.2 (B), R2873.2, R2874.1
unnamed: Q2341.2 (B), R2875.2, R2876.1
unnamed: Q2342.2 (B), R2878.2, R2879.1
unnamed: Q2343.1 (E), Q2344.3 (C)
unnamed: Q2343.2 (B), R2881.2, R2882.1
unnamed: Q2344.2 (B), R2883.2, R2884.1
unnamed: Q2345.1 (E), Q2346.3 (C)
unnamed: Q2345.2 (B), R2886.2, R2887.1
unnamed: Q2346.2 (B), R2888.2, R2889.1
unnamed: Q2347.1 (E), Q2348.3 (C)
unnamed: Q2347.2 (B), R2891.2, R2892.1
unnamed: Q2348.2 (B), R2893.2, R2894.1
unnamed: Q2349.1 (E), Q2350.3 (C)
unnamed: Q2349.2 (B), R2896.2, R2897.1
unnamed: Q2350.2 (B), R2898.2, R2899.1
unnamed: Q2351.2 (B), R2901.2, R2902.1
unnamed: Q2352.2 (B), R2904.2, R2905.1
unnamed: Q2353.2 (B), R2907.2, R2908.1
unnamed: Q2354.1 (E), Q2355.3 (C)
unnamed: Q2354.2 (B), R2910.2, R2911.1
unnamed: Q2355.2 (B), R2912.2, R2913.1
unnamed: Q2356.1 (E), Q2357.3 (C)
unnamed: Q2356.2 (B), R2915.2, R2916.1
unnamed: Q2357.2 (B), R2917.2, R2918.1
unnamed: Q2358.1 (E), Q2359.3 (C)
unnamed: Q2358.2 (B), R2920.2, R2921.1
unnamed: Q2359.2 (B), R2922.2, R2923.1
unnamed: Q2360.1 (E), Q2361.3 (C)
unnamed: Q2360.2 (B), R2925.2, R2926.1
unnamed: Q2361.2 (B), R2927.2, R2928.1
unnamed: Q2362.2 (B), R2930.2, R2931.1
unnamed: Q2363.1 (E), Q2364.3 (C)
unnamed: Q2363.2 (B), R2933.2, R2934.1
unnamed: Q2364.2 (B), R2935.2, R2936.1
unnamed: Q2365.1 (E), Q2366.3 (C)
unnamed: Q2365.2 (B), R2938.2, R2939.1
unnamed: Q2366.2 (B), R2940.2, R2941.1
unnamed: Q2367.1 (E), Q2368.3 (C)
unnamed: Q2367.2 (B), R2943.2, R2944.1
unnamed: Q2368.2 (B), R2945.2, R2946.1
unnamed: Q2369.1 (E), Q2370.3 (C)
unnamed: Q2369.2 (B), R2948.2, R2949.1
unnamed: Q2370.2 (B), R2950.2, R2951.1
unnamed: Q2371.2 (B), R2953.2, R2954.1
unnamed: Q2372.2 (B), R2956.2, R2957.1
unnamed: Q2373.2 (B), R2959.2, R2960.1
unnamed: Q2374.1 (E), Q2375.3 (C)
unnamed: Q2374.2 (B), R2962.2, R2963.1
unnamed: Q2375.2 (B), R2964.2, R2965.1
unnamed: Q2376.1 (E), Q2377.3 (C)
unnamed: Q2376.2 (B), R2967.2, R2968.1
unnamed: Q2377.2 (B), R2969.2, R2970.1
unnamed: Q2378.1 (E), Q2379.3 (C)
unnamed: Q2378.2 (B), R2972.2, R2973.1
unnamed: Q2379.2 (B), R2974.2, R2975.1
unnamed: Q2380.1 (E), Q2381.3 (C)
unnamed: Q2380.2 (B), R2977.2, R2978.1
unnamed: Q2381.2 (B), R2979.2, R2980.1
unnamed: Q2382.2 (B), R2982.2, R2983.1
unnamed: Q2383.1 (E), Q2384.3 (C)
unnamed: Q2383.2 (B), R2985.2, R2986.1
unnamed: Q2384.2 (B), R2987.2, R2988.1
unnamed: Q2385.1 (E), Q2386.3 (C)
unnamed: Q2385.2 (B), R2990.2, R2991.1
unnamed: Q2386.2 (B), R2992.2, R2993.1
unnamed: Q2387.1 (E), Q2388.3 (C)
unnamed: Q2387.2 (B), R2995.2, R2996.1
unnamed: Q2388.2 (B), R2997.2, R2998.1
unnamed: Q2389.1 (E), Q2390.3 (C)
unnamed: Q2389.2 (B), R3000.2, R3001.1
unnamed: Q2390.2 (B), R3002.2, R3003.1
unnamed: Q2391.1 (E), Q2392.3 (C)
unnamed: Q2391.2 (B), R3005.2, R3006.1
unnamed: Q2392.2 (B), R3007.2, R3008.1
unnamed: Q2393.1 (E), Q2394.3 (C)
unnamed: Q2393.2 (B), R3010.2, R3011.1
unnamed: Q2394.2 (B), R3012.2, R3013.1
unnamed: Q2395.1 (E), Q2396.3 (C)
unnamed: Q2395.2 (B), R3015.2, R3016.1
unnamed: Q2396.2 (B), R3017.2, R3018.1
unnamed: Q2397.1 (E), Q2398.3 (C)
unnamed: Q2397.2 (B), R3020.2, R3021.1
unnamed: Q2398.2 (B), R3022.2, R3023.1
unnamed: Q2399.1 (E), Q2400.3 (C)
unnamed: Q2399.2 (B), R3025.2, R3026.1
unnamed: Q2400.2 (B), R3027.2, R3028.1
unnamed: Q2401.1 (E), Q2402.3 (C)
unnamed: Q2401.2 (B), R3030.2, R3031.1
unnamed: Q2402.2 (B), R3032.2, R3033.1
unnamed: Q2403.1 (E), Q2404.3 (C)
unnamed: Q2403.2 (B), R3035.2, R3036.1
unnamed: Q2404.2 (B), R3037.2, R3038.1
unnamed: Q2405.1 (E), Q2406.3 (C)
unnamed: Q2405.2 (B), R3040.2, R3041.1
unnamed: Q2406.2 (B), R3042.2, R3043.1
unnamed: Q2407.1 (E), Q2408.3 (C)
unnamed: Q2407.2 (B), R3045.2, R3046.1
unnamed: Q2408.2 (B), R3047.2, R3048.1
unnamed: Q2409.1 (E), Q2410.3 (C)
unnamed: Q2409.2 (B), R3050.2, R3051.1
unnamed: Q2410.1 (E), Q2411.3 (C)
unnamed: Q2410.2 (B), R3052.2, R3053.1
unnamed: Q2411.2 (B), R3054.2, R3055.1
unnamed: Q2412.1 (E), Q2413.3 (C)
unnamed: Q2412.2 (B), R3057.2, R3058.1
unnamed: Q2413.2 (B), R3059.2, R3060.1
unnamed: Q2414.1 (E), Q2415.3 (C)
unnamed: Q2414.2 (B), R3062.2, R3063.1
unnamed: Q2415.2 (B), R3064.2, R3065.1
unnamed: Q2416.1 (E), Q2417.3 (C)
unnamed: Q2416.2 (B), R3067.2, R3068.1
unnamed: Q2417.2 (B), R3069.2, R3070.1
unnamed: Q2418.2 (B), R3072.2, R3073.1
unnamed: Q2419.1 (E), Q2420.3 (C)
unnamed: Q2419.2 (B), R3075.2, R3076.1
unnamed: Q2420.2 (B), R3077.2, R3078.1
unnamed: Q2421.2 (B), R3080.2, R3081.1
unnamed: Q2422.1 (E), Q2423.3 (C)
unnamed: Q2422.2 (B), R3083.2, R3084.1
unnamed: Q2423.2 (B), R3085.2, R3086.1
unnamed: Q2424.2 (B), R3088.2, R3089.1
unnamed: Q2425.2 (B), R3091.2, R3092.1
unnamed: Q2426.2 (B), R3094.2, R3095.1
unnamed: Q2427.2 (B), R3097.2, R3098.1
unnamed: Q2428.1 (E), Q2429.3 (C)
unnamed: Q2428.2 (B), R3100.2, R3101.1
unnamed: Q2429.2 (B), R3102.2, R3103.1
unnamed: Q2430.1 (E), Q2431.3 (C)
unnamed: Q2430.2 (B), R3105.2, R3106.1
unnamed: Q2431.2 (B), R3107.2, R3108.1
unnamed: Q2432.1 (E), Q2433.3 (C)
unnamed: Q2432.2 (B), R3110.2, R3111.1
unnamed: Q2433.2 (B), R3112.2, R3113.1
unnamed: Q2434.1 (E), Q2435.3 (C)
unnamed: Q2434.2 (B), R3115.2, R3116.1
unnamed: Q2435.2 (B), R3117.2, R3118.1
unnamed: Q2436.2 (B), R3120.2, R3121.1
unnamed: Q2437.1 (E), Q2438.3 (C)
unnamed: Q2437.2 (B), R3123.2, R3124.1
unnamed: Q2438.2 (B), R3125.2, R3126.1
unnamed: Q2439.1 (E), Q2440.3 (C)
unnamed: Q2439.2 (B), R3128.2, R3129.1
unnamed: Q2440.2 (B), R3130.2, R3131.1
unnamed: Q2441.1 (E), Q2442.3 (C)
unnamed: Q2441.2 (B), R3133.2, R3134.1
unnamed: Q2442.2 (B), R3135.2, R3136.1
unnamed: Q2443.1 (E), Q2444.3 (C)
unnamed: Q2443.2 (B), R3138.2, R3139.1
unnamed: Q2444.2 (B), R3140.2, R3141.1
unnamed: Q2445.2 (B), R3143.2, R3144.1
unnamed: Q2446.2 (B), R3146.2, R3147.1
unnamed: Q2447.2 (B), R3149.2, R3150.1
unnamed: Q2448.1 (E), Q2449.3 (C)
unnamed: Q2448.2 (B), R3152.2, R3153.1
unnamed: Q2449.2 (B), R3154.2, R3155.1
unnamed: Q2450.1 (E), Q2451.3 (C)
unnamed: Q2450.2 (B), R3157.2, R3158.1
unnamed: Q2451.2 (B), R3159.2, R3160.1
unnamed: Q2452.1 (E), Q2453.3 (C)
unnamed: Q2452.2 (B), R3162.2, R3163.1
unnamed: Q2453.2 (B), R3164.2, R3165.1
unnamed: Q2454.1 (E), Q2455.3 (C)
unnamed: Q2454.2 (B), R3167.2, R3168.1
unnamed: Q2455.2 (B), R3169.2, R3170.1
unnamed: Q2456.2 (B), R3172.2, R3173.1
unnamed: Q2457.1 (E), Q2458.3 (C)
unnamed: Q2457.2 (B), R3175.2, R3176.1
unnamed: Q2458.2 (B), R3177.2, R3178.1
unnamed: Q2459.1 (E), Q2460.3 (C)
unnamed: Q2459.2 (B), R3180.2, R3181.1
unnamed: Q2460.2 (B), R3182.2, R3183.1
unnamed: Q2461.1 (E), Q2462.3 (C)
unnamed: Q2461.2 (B), R3185.2, R3186.1
unnamed: Q2462.2 (B), R3187.2, R3188.1
unnamed: Q2463.1 (E), Q2464.3 (C)
unnamed: Q2463.2 (B), R3190.2, R3191.1
unnamed: Q2464.2 (B), R3192.2, R3193.1
unnamed: Q2465.2 (B), R3195.2, R3196.1
unnamed: Q2466.2 (B), R3197.2, R3198.1
unnamed: Q2467.2 (B), R3200.2, R3201.1
unnamed: Q2468.1 (E), Q2469.3 (C)
unnamed: Q2468.2 (B), R3203.2, R3204.1
unnamed: Q2469.2 (B), R3205.2, R3206.1
unnamed: Q2470.1 (E), Q2471.3 (C)
unnamed: Q2470.2 (B), R3208.2, R3209.1
unnamed: Q2471.2 (B), R3210.2, R3211.1
unnamed: Q2472.1 (E), Q2473.3 (C)
unnamed: Q2472.2 (B), R3213.2, R3214.1
unnamed: Q2473.2 (B), R3215.2, R3216.1
unnamed: Q2474.1 (E), Q2475.3 (C)
unnamed: Q2474.2 (B), R3218.2, R3219.1
unnamed: Q2475.2 (B), R3220.2, R3221.1
unnamed: Q2476.1 (E), Q2477.3 (C)
unnamed: Q2476.2 (B), R3223.2, R3224.1
unnamed: Q2477.2 (B), R3225.2, R3226.1
unnamed: Q2478.2 (B), R3228.2, R3229.1
unnamed: Q2479.2 (B), R3231.2, R3232.1
OP0: R2001.1, R2355.1, R2511.1
OP0N: Q2000.3 (C), R2000.2, R2004.1, R2007.1, R2344.1, R2476.1, R3054.1
OP1: R2010.1, R2013.1
OP1BA: Q2005.3 (C), R2015.2, R2053.1, R3010.1, R3025.1, R3040.1, R3057.1
OP1BB: Q2006.3 (C), R2018.2, R2474.1, R2509.1, R3075.1, R3083.1
OP1NA: Q2003.3 (C), R2009.2, R3005.1, R3020.1, R3035.1, R3050.1, R3067.1
OP1NB: Q2004.3 (C), R2012.2, R2016.1, R2019.1, R2388.1, R3195.1
OUT0: R3007.1
OUT1: R3022.1
OUT2: R3037.1
OUT3: R3052.1
OUT_B4: Q2441.3 (C), R3132.2, R3138.1
OUT_B4.CLKB: Q2426.3 (C), R3093.2, R3125.1, R3128.1
OUT_B4.CLKN: Q2425.3 (C), R3090.2, R3094.1, R3102.1, R3105.1
OUT_B4.DN: Q2427.3 (C), R3096.2, R3107.1
OUT_B4.M1: Q2428.3 (C), R3099.2, R3110.1
OUT_B4.M2: Q2430.3 (C), R3104.2, R3117.1
OUT_B4.MQ: Q2432.3 (C), R3109.2, R3115.1, R3120.1, R3123.1
OUT_B4.MQI: Q2436.3 (C), R3119.2, R3130.1
OUT_B4.MQN: Q2434.3 (C), R3112.1, R3114.2
OUT_B4.QN: Q2443.3 (C), R3135.1, R3137.2
OUT_B4.S1: Q2437.3 (C), R3122.2, R3133.1
OUT_B4.S2: Q2439.3 (C), R3127.2, R3140.1
OUT_B5: Q2461.3 (C), R3184.2, R3190.1
OUT_B5.CLKB: Q2446.3 (C), R3145.2, R3177.1, R3180.1
OUT_B5.CLKN: Q2445.3 (C), R3142.2, R3146.1, R3154.1, R3157.1
OUT_B5.DN: Q2447.3 (C), R3148.2, R3159.1
OUT_B5.M1: Q2448.3 (C), R3151.2, R3162.1
OUT_B5.M2: Q2450.3 (C), R3156.2, R3169.1
OUT_B5.MQ: Q2452.3 (C), R3161.2, R3167.1, R3172.1, R3175.1
OUT_B5.MQI: Q2456.3 (C), R3171.2, R3182.1
OUT_B5.MQN: Q2454.3 (C), R3164.1, R3166.2
OUT_B5.QN: Q2463.3 (C), R3187.1, R3189.2
OUT_B5.S1: Q2457.3 (C), R3174.2, R3185.1
OUT_B5.S2: Q2459.3 (C), R3179.2, R3192.1
P0: Q2287.3 (C), R2471.1, R2642.1, R2676.1, R2734.2, R2740.1, R3012.1
P0.CLKB: Q2272.3 (C), R2695.2, R2727.1, R2730.1
P0.CLKN: Q2271.3 (C), R2692.2, R2696.1, R2704.1, R2707.1
P0.DN: Q2273.3 (C), R2698.2, R2709.1
P0.M1: Q2274.3 (C), R2701.2, R2712.1
P0.M2: Q2276.3 (C), R2706.2, R2719.1
P0.MQ: Q2278.3 (C), R2711.2, R2717.1, R2722.1, R2725.1
P0.MQI: Q2282.3 (C), R2721.2, R2732.1
P0.MQN: Q2280.3 (C), R2714.1, R2716.2
P0.QN: Q2289.3 (C), R2737.1, R2739.2
P0.S1: Q2283.3 (C), R2724.2, R2735.1
P0.S2: Q2285.3 (C), R2729.2, R2742.1
P0N: Q2180.3 (C), R2470.2, R2478.1
P1: Q2307.3 (C), R2613.1, R2647.1, R2666.1, R2786.2, R2792.1, R3027.1
P1.CLKB: Q2292.3 (C), R2747.2, R2779.1, R2782.1
P1.CLKN: Q2291.3 (C), R2744.2, R2748.1, R2756.1, R2759.1
P1.DN: Q2293.3 (C), R2750.2, R2761.1
P1.M1: Q2294.3 (C), R2753.2, R2764.1
P1.M2: Q2296.3 (C), R2758.2, R2771.1
P1.MQ: Q2298.3 (C), R2763.2, R2769.1, R2774.1, R2777.1
P1.MQI: Q2302.3 (C), R2773.2, R2784.1
P1.MQN: Q2300.3 (C), R2766.1, R2768.2
P1.QN: Q2309.3 (C), R2789.1, R2791.2
P1.S1: Q2303.3 (C), R2776.2, R2787.1
P1.S2: Q2305.3 (C), R2781.2, R2794.1
P2: Q2327.3 (C), R2411.1, R2589.1, R2618.1, R2637.1, R2838.2, R2844.1, R3042.1
P2.CLKB: Q2312.3 (C), R2799.2, R2831.1, R2834.1
P2.CLKN: Q2311.3 (C), R2796.2, R2800.1, R2808.1, R2811.1
P2.DN: Q2313.3 (C), R2802.2, R2813.1
P2.M1: Q2314.3 (C), R2805.2, R2816.1
P2.M2: Q2316.3 (C), R2810.2, R2823.1
P2.MQ: Q2318.3 (C), R2815.2, R2821.1, R2826.1, R2829.1
P2.MQI: Q2322.3 (C), R2825.2, R2836.1
P2.MQN: Q2320.3 (C), R2818.1, R2820.2
P2.QN: Q2329.3 (C), R2841.1, R2843.2
P2.S1: Q2323.3 (C), R2828.2, R2839.1
P2.S2: Q2325.3 (C), R2833.2, R2846.1
P3: Q2347.3 (C), R2406.1, R2436.1, R2560.1, R2594.1, R2890.2, R2896.1, R3059.1
P3.CLKB: Q2332.3 (C), R2851.2, R2883.1, R2886.1
P3.CLKN: Q2331.3 (C), R2848.2, R2852.1, R2860.1, R2863.1
P3.DN: Q2333.3 (C), R2854.2, R2865.1
P3.M1: Q2334.3 (C), R2857.2, R2868.1
P3.M2: Q2336.3 (C), R2862.2, R2875.1
P3.MQ: Q2338.3 (C), R2867.2, R2873.1, R2878.1, R2881.1
P3.MQI: Q2342.3 (C), R2877.2, R2888.1
P3.MQN: Q2340.3 (C), R2870.1, R2872.2
P3.QN: Q2349.3 (C), R2893.1, R2895.2
P3.S1: Q2343.3 (C), R2880.2, R2891.1
P3.S2: Q2345.3 (C), R2885.2, R2898.1
P4: Q2367.3 (C), R2431.1, R2461.1, R2531.1, R2565.1, R2942.2, R2948.1, R3077.1
P4.CLKB: Q2352.3 (C), R2903.2, R2935.1, R2938.1
P4.CLKN: Q2351.3 (C), R2900.2, R2904.1, R2912.1, R2915.1
P4.DN: Q2353.3 (C), R2906.2, R2917.1
P4.M1: Q2354.3 (C), R2909.2, R2920.1
P4.M2: Q2356.3 (C), R2914.2, R2927.1
P4.MQ: Q2358.3 (C), R2919.2, R2925.1, R2930.1, R2933.1
P4.MQI: Q2362.3 (C), R2929.2, R2940.1
P4.MQN: Q2360.3 (C), R2922.1, R2924.2
P4.QN: Q2369.3 (C), R2945.1, R2947.2
P4.S1: Q2363.3 (C), R2932.2, R2943.1
P4.S2: Q2365.3 (C), R2937.2, R2950.1
P5: Q2387.3 (C), R2364.1, R2456.1, R2536.1, R2994.2, R3000.1, R3085.1
P5.CLKB: Q2372.3 (C), R2955.2, R2987.1, R2990.1
P5.CLKN: Q2371.3 (C), R2952.2, R2956.1, R2964.1, R2967.1
P5.DN: Q2373.3 (C), R2958.2, R2969.1
P5.M1: Q2374.3 (C), R2961.2, R2972.1
P5.M2: Q2376.3 (C), R2966.2, R2979.1
P5.MQ: Q2378.3 (C), R2971.2, R2977.1, R2982.1, R2985.1
P5.MQI: Q2382.3 (C), R2981.2, R2992.1
P5.MQN: Q2380.3 (C), R2974.1, R2976.2
P5.QN: Q2389.3 (C), R2997.1, R2999.2
P5.S1: Q2383.3 (C), R2984.2, R2995.1
P5.S2: Q2385.3 (C), R2989.2, R3002.1
QD: Q2140.3 (C), R2368.2, R2374.1, R2671.1
Q_N: Q2138.3 (C), Q2139.3 (C), R2363.2, R2369.1, R2382.1
RDS_N: Q2416.3 (C), R3066.2, R3072.1
RD_A0: Q2391.3 (C), R3004.2, R3015.1
RD_A1: Q2397.3 (C), R3019.2, R3030.1
RD_A2: Q2403.3 (C), R3034.2, R3045.1
RD_A3: Q2409.3 (C), R3049.2, R3062.1
RD_M0: Q2393.3 (C), R3009.2, R3017.1
RD_M1: Q2399.3 (C), R3024.2, R3032.1
RD_M2: Q2405.3 (C), R3039.2, R3047.1
RD_M3: Q2412.3 (C), R3056.2, R3064.1
REG_D0: Q2395.3 (C), R3014.2
REG_D1: Q2401.3 (C), R3029.2
REG_D2: Q2407.3 (C), R3044.2
REG_D3: Q2414.3 (C), R3061.2
REG_DS: Q2418.3 (C), R3071.2
S0: R2584.1, R2608.1
S1: R2555.1, R2579.1
S2: R2526.1, R2550.1
S3: R2366.1, R2521.1
SIG: R2022.1
SIGB: Q2008.3 (C), R2024.2
SIGB2: Q2009.3 (C), R2027.2, R3069.1
SIGN_: Q2007.3 (C), R2021.2, R2025.1, R2028.1
START: R2051.1
SUB: Q2001.3 (C), R2003.2
SUB2: Q2002.3 (C), R2006.2
T: Q2127.3 (C), R2333.2, R2339.1, R2342.1, R2353.1
T1: Q2060.3 (C), R2042.1, R2160.2, R2166.1, R2177.1, R2180.1, R2327.1
T1.CLKB: Q2045.3 (C), R2121.2, R2153.1, R2156.1
T1.CLKN: Q2044.3 (C), R2118.2, R2122.1, R2130.1, R2133.1
T1.DN: Q2046.3 (C), R2124.2, R2135.1
T1.M1: Q2047.3 (C), R2127.2, R2138.1
T1.M2: Q2049.3 (C), R2132.2, R2145.1
T1.MQ: Q2051.3 (C), R2137.2, R2143.1, R2148.1, R2151.1
T1.MQI: Q2055.3 (C), R2147.2, R2158.1
T1.MQN: Q2053.3 (C), R2140.1, R2142.2
T1.QN: Q2062.3 (C), R2163.1, R2165.2
T1.S1: Q2056.3 (C), R2150.2, R2161.1
T1.S2: Q2058.3 (C), R2155.2, R2168.1
T2: Q2080.3 (C), R2044.1, R2212.2, R2218.1, R2229.1, R2232.1, R2329.1
T2.CLKB: Q2065.3 (C), R2173.2, R2205.1, R2208.1
T2.CLKN: Q2064.3 (C), R2170.2, R2174.1, R2182.1, R2185.1
T2.DN: Q2066.3 (C), R2176.2, R2187.1
T2.M1: Q2067.3 (C), R2179.2, R2190.1
T2.M2: Q2069.3 (C), R2184.2, R2197.1
T2.MQ: Q2071.3 (C), R2189.2, R2195.1, R2200.1, R2203.1
T2.MQI: Q2075.3 (C), R2199.2, R2210.1
T2.MQN: Q2073.3 (C), R2192.1, R2194.2
T2.QN: Q2082.3 (C), R2215.1, R2217.2
T2.S1: Q2076.3 (C), R2202.2, R2213.1
T2.S2: Q2078.3 (C), R2207.2, R2220.1
T3: Q2100.3 (C), R2046.1, R2264.2, R2270.1, R2281.1, R2284.1, R2331.1
T3.CLKB: Q2085.3 (C), R2225.2, R2257.1, R2260.1
T3.CLKN: Q2084.3 (C), R2222.2, R2226.1, R2234.1, R2237.1
T3.DN: Q2086.3 (C), R2228.2, R2239.1
T3.M1: Q2087.3 (C), R2231.2, R2242.1
T3.M2: Q2089.3 (C), R2236.2, R2249.1
T3.MQ: Q2091.3 (C), R2241.2, R2247.1, R2252.1, R2255.1
T3.MQI: Q2095.3 (C), R2251.2, R2262.1
T3.MQN: Q2093.3 (C), R2244.1, R2246.2
T3.QN: Q2102.3 (C), R2267.1, R2269.2
T3.S1: Q2096.3 (C), R2254.2, R2265.1
T3.S2: Q2098.3 (C), R2259.2, R2272.1
TDA: Q2136.3 (C), R2357.2, R2409.1, R2434.1, R2459.1
TDB: Q2137.3 (C), R2360.2, R2372.1, R2380.1, R2611.1, R2640.1, R2669.1
TDNQ: Q2146.3 (C), R2384.2, R2529.1, R2558.1, R2587.1
TDNQ_N: Q2144.3 (C), R2379.2, R2385.1
TDQ: Q2143.3 (C), R2376.2, R2524.1, R2553.1, R2582.1
TDQ_N: Q2141.3 (C), R2371.2, R2377.1
TD_N: Q2134.3 (C), R2352.2, R2358.1, R2361.1
TMA: Q2132.3 (C), R2346.2, R2404.1, R2429.1, R2454.1
TMB: Q2133.3 (C), R2349.2, R2519.1, R2548.1, R2577.1, R2606.1, R2635.1, R2664.1
TM_N: Q2130.3 (C), R2341.2, R2347.1, R2350.1
T_N: Q2124.3 (C), Q2125.3 (C), Q2126.3 (C), R2326.2, R2334.1
X: Q2184.3 (C), R2480.2, R2486.1, R2491.1, R2496.1
X_N: Q2181.3 (C), R2473.2, R2481.1

Notes on the sheet:
MULTIPLY / DIVIDE EXTENSION - sequential shift-add multiplier and restoring divider re-using the root sheet's 3-bit adder/subtractor.
Every cell is one RTL gate in the same style as the root sheet: 10k base resistor, 22k base pull-down, 4.7k collector pull-up (2.2k where a gate drives 4..6 inputs), stacked NPN = NAND, parallel NPN = NOR. Inputs from the root sheet: ENCA_N[2:0] / ENCB_N[2:0] (keypad encoders, active low), S[3:0] (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
OP-CODE DECODE & BUFFERS (OP1 OP0: 00=ADD 01=SUB 10=MUL 11=DIV). SUB/SUB2 drive the root adder; SIGB drives the sign-magnitude converter (bug fix: was SUB).
CLOCK BUFFERS
SEQUENCER: one-hot ring L -> T1 -> T2 -> T3 -> DN, started by START when idle in MUL/DIV mode. T=step phase, IDLE=hold, TM/TD=step&MUL / step&DIV, Q=division quotient bit
ADDER A-OPERAND MUX: keypad A (ADD/SUB and during load), P[5:3] (MUL step), P[4:2] (DIV step)
ADDER B-OPERAND GATE: B = keypad B, forced to 0 in MUL mode when P0 = 0
DIVIDE-BY-ZERO FLAG
P REGISTER NEXT-STATE (AND-OR per bit): load A / MUL shift-add / DIV restoring step / hold
P REGISTER (6 master-slave D flip-flops, same cell as the root memory register). MUL result: P[5:0]=product. DIV result: P[2:0]=quotient, P[5:3]=remainder
MEMORY REGISTER DATA MUX: REG_D[3:0] <- converter output (ADD/SUB) or P[3:0] (MUL/DIV); REG_DS <- sign (ADD/SUB only); OUT_B4/OUT_B5 = two extra memory bits
GLITCH-FREE MEMORY CLOCK GATE: MEMCLK = CLOCK while ADD/SUB; one pulse after DN in MUL/DIV (enable latched while CLOCK is low)
