nikolafilip/nibble/experiments/muldiv/testbench.kicad_sch

## KiCad design experiments/muldiv/testbench.kicad_sch (2026-09-09)

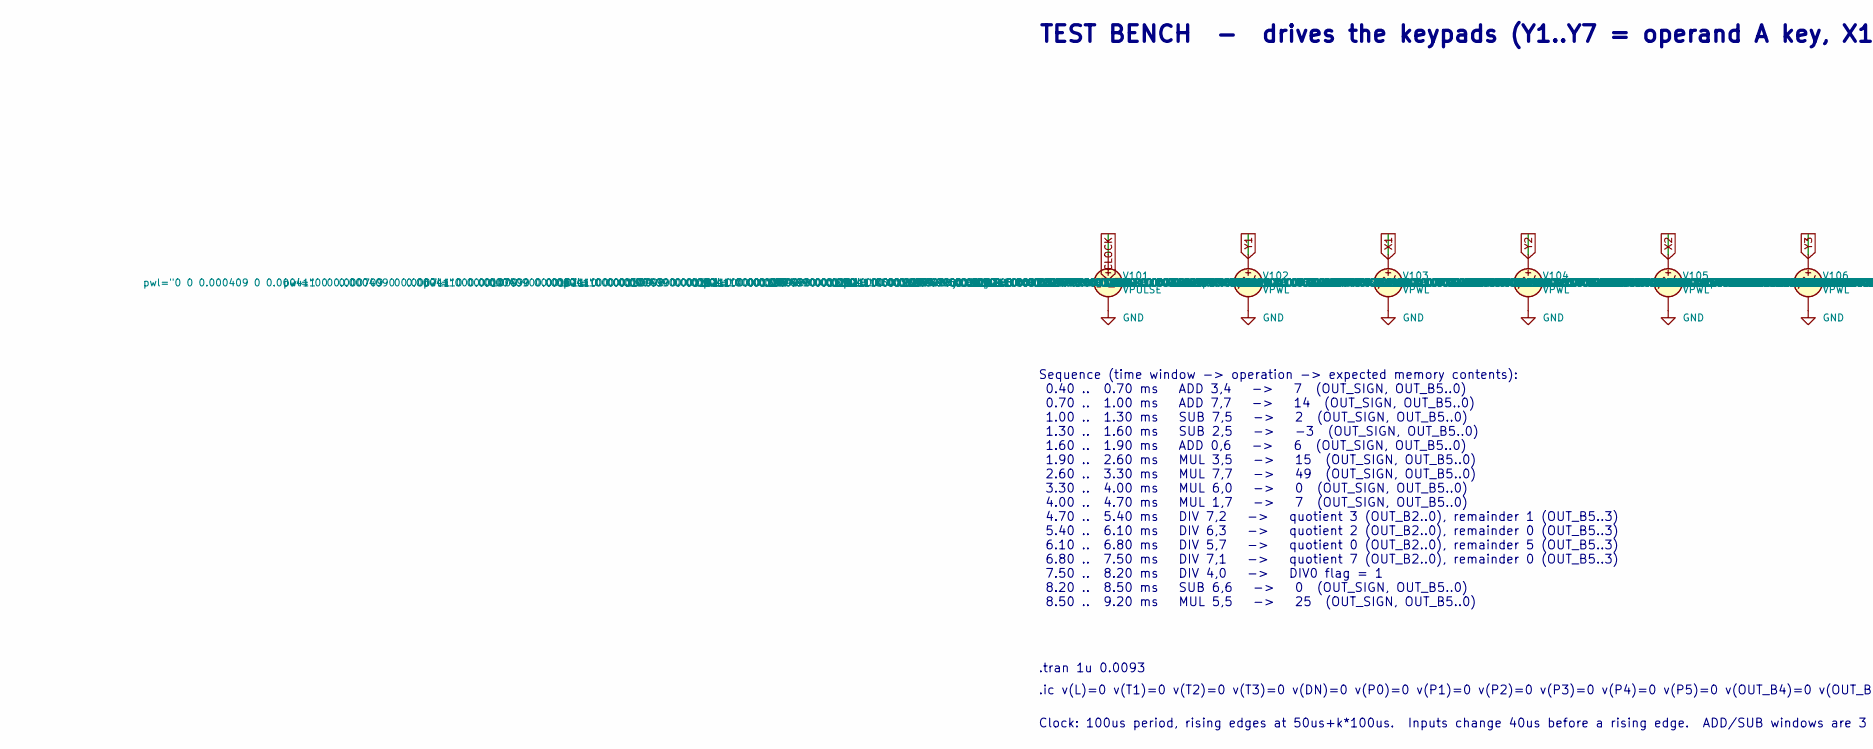
[picture p97: schematic testbench.kicad_sch, part in row 1, column 1]

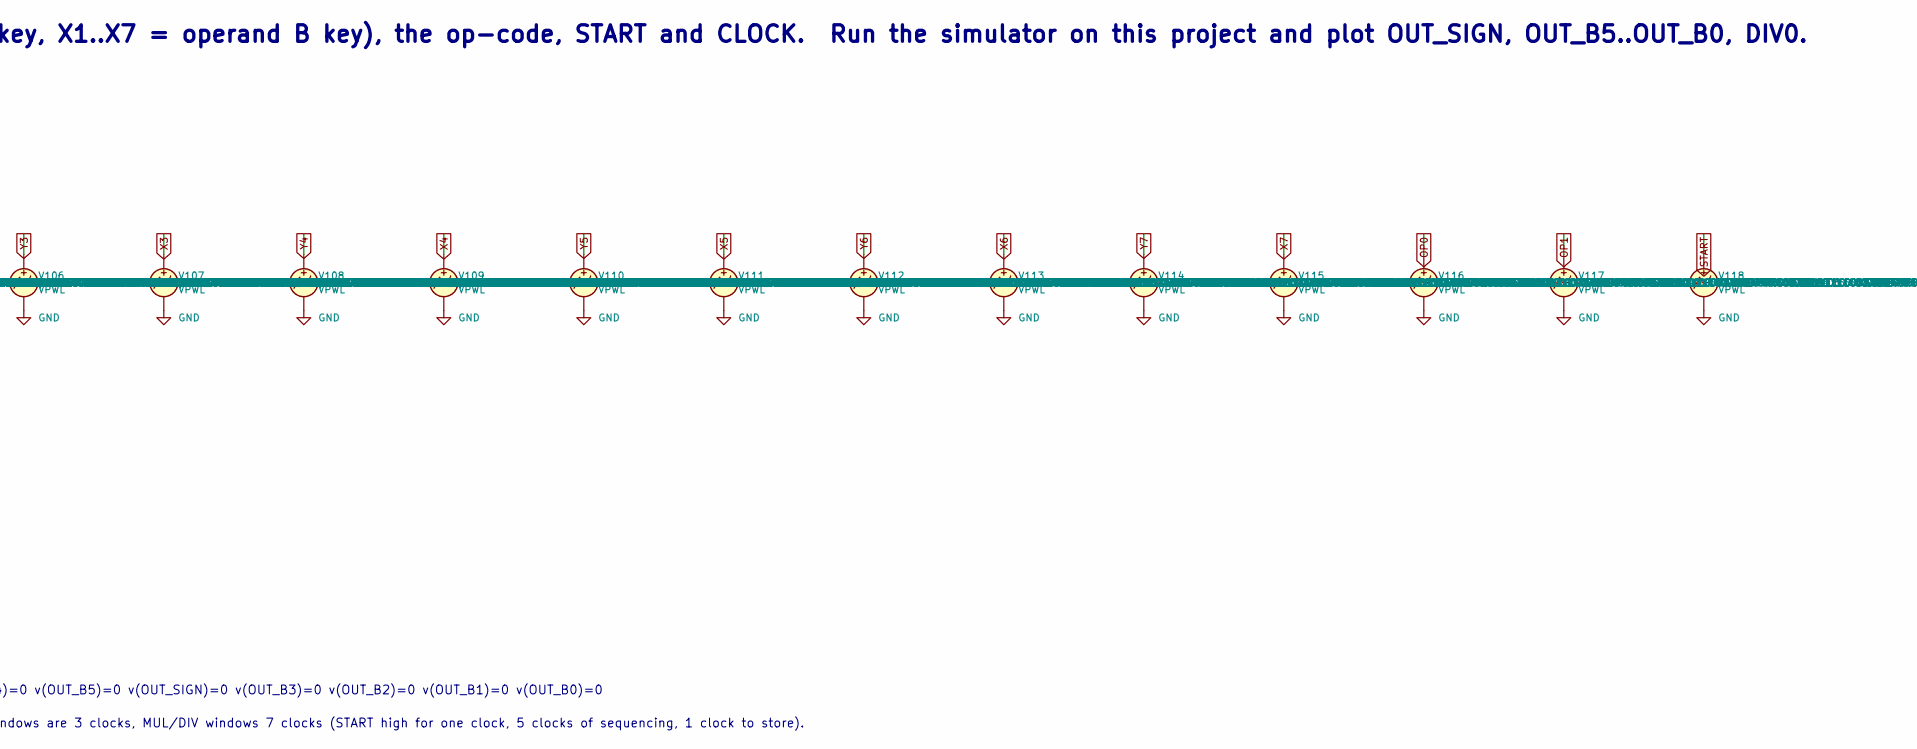
[picture p98: schematic testbench.kicad_sch, part in row 1, column 2]

Parts:
V101: VPULSE
V102, V103, V104, V105, V106, V107, V108, V109, V110, V111, V112, V113, V114, V115, V116, V117, V118: VPWL

Connections:
CLOCK: V101.1
GND: V101.2, V102.2, V103.2, V104.2, V105.2, V106.2, V107.2, V108.2, V109.2, V110.2, V111.2, V112.2, V113.2, V114.2, V115.2, V116.2, V117.2, V118.2
OP0: V116.1
OP1: V117.1
START: V118.1
X1: V103.1
X2: V105.1
X3: V107.1
X4: V109.1
X5: V111.1
X6: V113.1
X7: V115.1
Y1: V102.1
Y2: V104.1
Y3: V106.1
Y4: V108.1
Y5: V110.1
Y6: V112.1
Y7: V114.1

Notes on the sheet:
TEST BENCH - drives the keypads (Y1..Y7 = operand A key, X1..X7 = operand B key), the op-code, START and CLOCK. Run the simulator on this project and plot OUT_SIGN, OUT_B5..OUT_B0, DIV0.
Sequence (time window -> operation -> expected memory contents): 0.40 .. 0.70 ms ADD 3,4 -> 7 (OUT_SIGN, OUT_B5..0) 0.70 .. 1.00 ms ADD 7,7 -> 14 (OUT_SIGN, OUT_B5..0) 1.00 .. 1.30 ms SUB 7,5 -> 2 (OUT_SIGN, OUT_B5..0) 1.30 .. 1.60 ms SUB 2,5 -> -3 (OUT_SIGN, OUT_B5..0) 1.60 .. 1.90 ms ADD 0,6 -> 6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
.tran 1u 0.0093
.ic v(L)=0 v(T1)=0 v(T2)=0 v(T3)=0 v(DN)=0 v(P0)=0 v(P1)=0 v(P2)=0 v(P3)=0 v(P4)=0 v(P5)=0 v(OUT_B4)=0 v(OUT_B5)=0 v(OUT_SIGN)=0 v(OUT_B3)=0 v(OUT_B2)=0 v(OUT_B1)=0 v(OUT_B0)=0
Clock: 100us period, rising edges at 50us+k*100us. Inputs change 40us before a rising edge. ADD/SUB windows are 3 clocks, MUL/DIV windows 7 clocks (START high for one clock, 5 clocks of sequencing, 1 clock to store).
