nikolafilip/nibble/sim/build_clock_card.py

"""Generate cards/clock (KiCad project) from clock.py plus the RC parts, pot, switch and jumper: the clock card (docs/cards.md).
Run from sim/:  python3 build_clock_card.py"""
import os
import ksch, clock, frame
G=ksch.G
OUT=os.path.join(ksch.CARDS,'clock')
PROJECT='clock'
R_FIX='100k'; C_FAST='47n'; C_SLOW='2.2u'; R_POT='1M'

def main():
    d=clock.build(); pr=d.check(); assert not pr, pr
    os.makedirs(OUT,exist_ok=True); root_uuid=ksch.U()
    w=ksch.DenseWriter(PROJECT,root_uuid); w.n['RV']=1
    w.T("NIBBLE CARD CLOCK: RC oscillator with a speed knob, RUN/STEP switch, halt, power-on reset",10*G,6*G,3.5,True)
    w.T(f"{d.ntransistors()+3} transistors, {d.nresistors()+10} resistors, {d.nleds()} LEDs, one pot, one switch, one jumper, 100 x 100 mm (docs/cards.md).\n"
        "RUN: the switch puts 1k from +5V on CLK (a few microseconds into the 3 nF of cards and ribbon, D053) and the oscillator pulls CLK low for half of each cycle, or for as long as HLT is high.\n"
        "STEP: the switch is open and the pull-down transistor is held off; the front panel's CLK button owns the line, one edge per press.\n"
        f"Speed: a Schmitt-trigger RC oscillator, {R_FIX} + the pot from SA to X, {C_FAST} on X: about 500 Hz down to 40 Hz; the SLOW jumper adds {C_SLOW} for 10 Hz down to 0.8 Hz.\n"
        "Power-on reset: 2.2 uF charging through 100k into a Schmitt trigger holds RST high for a tenth of a second after power-up, so the machine starts at address 0 without touching the panel; RST is driven through 1k against the panel's 10k pull-down and releases within 50 us (D053).",10*G,16*G,1.6)
    used={'HLT','CLK','RST'}
    cols=3
    yend=w.layout(d.gates,clock.GROUP_TITLES,10*G,60*G,cols,pcb_origin=(frame.X0,frame.Y0),pcb_cols=3)
    extra=frame.card_frame(w,30*G,40*G,used,"NIBBLE  CLOCK"); extra["hide_refs"].append("SW")
    # ---- the analogue parts, drawn by hand ----
    y=yend+10*G; x=14*G
    w.T("SCHMITT TRIGGER: Q1 (gate X) and Q2 (gate = Q1's drain) share RS = 1k.  Q2 on: source at 0.45 V (RD2 10k); Q1 on: source at 0.1 V (RD1 47k).  VD2, Q2's drain, is the output: 0.5 V with X low, 5 V with X high.",x-4*G,y-8*G,1.6,True)
    # Q1
    q1=w.Q(x+8*G,y); w.at(q1,40,34,0); w.L('X',x+2*G,y,180,'input'); w.W(x+2*G,y,x+6*G,y)
    w.W(x+9*G,y-2*G,x+9*G,y-3*G); w.J(x+9*G,y-3*G); w.at(w.R("47k",x+9*G,y-4.5*G),46,22,270); w.W(x+9*G,y-6*G,x+9*G,y-7*G); w.PW('+5V',x+9*G,y-7*G)
    w.W(x+9*G,y+2*G,x+9*G,y+3*G); w.J(x+9*G,y+3*G)                                   # source node VS
    # Q2, gate from Q1's drain
    q2=w.Q(x+20*G,y); w.at(q2,52,34,0); w.W(x+9*G,y-3*G,x+14*G,y-3*G); w.W(x+14*G,y-3*G,x+14*G,y); w.W(x+14*G,y,x+18*G,y)
    w.W(x+21*G,y-2*G,x+21*G,y-3*G); w.J(x+21*G,y-3*G); w.at(w.R("10k",x+21*G,y-4.5*G),58,22,270); w.W(x+21*G,y-6*G,x+21*G,y-7*G); w.PW('+5V',x+21*G,y-7*G)
    w.W(x+21*G,y-3*G,x+24*G,y-3*G); w.L('VD2',x+24*G,y-3*G,0,'output')
    w.W(x+21*G,y+2*G,x+21*G,y+3*G); w.W(x+9*G,y+3*G,x+21*G,y+3*G); w.W(x+21*G,y+3*G,x+24*G,y+3*G); w.L('VS',x+24*G,y+3*G,0,'output')
    # RS from VS to GND
    w.W(x+9*G,y+3*G,x+9*G,y+4*G); w.at(w.R('1k',x+9*G,y+5.5*G),40,52,270); w.W(x+9*G,y+7*G,x+9*G,y+8*G); w.PW('GND',x+9*G,y+8*G)
    # timing: SA -> R_FIX -> RT -> pot -> X; C on X; SLOW jumper adds C_SLOW
    y+=14*G
    w.T(f"TIMING: SA -> {R_FIX} + pot -> X, {C_FAST} from X to GND; the SLOW jumper adds {C_SLOW}.  X swings only between the two trip points, about half a volt around Vth.",x-4*G,y-6*G,1.6,True)
    w.L('SA',x,y,180,'input'); w.W(x,y,x+G,y); w.at(w.R(R_FIX,x+2.5*G,y,90),40,64,270); w.W(x+4*G,y,x+5*G,y); w.L('RT',x+5*G,y,0,'output')
    xp=x+10*G; w.L('RT',xp,y-3*G,90,'input'); w.W(xp,y-3*G,xp,y-1.5*G)
    pv=w.symbol("Device","R_Potentiometer",w.ref('RV'),R_POT,xp,y,0,('1','2','3'),"nibble:Potentiometer_Bourns_PTV09A-4_Single_Vertical",[("Description","Potentiometer",True)],sim=False)
    w.at(pv,62,54,0); w.label("SPEED",58,49,1.5)
    w.W(xp+1.5*G,y,xp+2*G,y); w.W(xp+2*G,y,xp+2*G,y+2*G); w.W(xp,y+1.5*G,xp,y+2*G); w.W(xp,y+2*G,xp+2*G,y+2*G); w.J(xp,y+2*G)   # wiper tied to the low end: a two-terminal variable resistor
    w.W(xp,y+2*G,xp,y+3*G); w.L('X',xp,y+3*G,270,'output')
    w.T("In the simulation the pot is shorted (RT to X): the fastest setting, about 500 Hz.",x-4*G,y+6*G,1.27)
    xc=x+18*G; w.L('X',xc,y-3*G,90,'input'); w.W(xc,y-3*G,xc,y-1.5*G); w.at(w.C(C_FAST,xc,y),46,64,270); w.W(xc,y+1.5*G,xc,y+3*G); w.PW('GND',xc,y+3*G)
    xj=xc+8*G; jp=w.pinheader(2,xj,y-4*G,"SLOW"); w.at(jp,52,64,0); w.label("SLOW",49,60,1.0)     # Conn_01x02: pin 1 at (xj-2G, y-4G), pin 2 at (xj-2G, y-3G)
    w.W(xj-2*G,y-4*G,xj-4*G,y-4*G); w.L('X',xj-4*G,y-4*G,180,'input')
    w.W(xj-2*G,y-3*G,xj-3*G,y-3*G); w.W(xj-3*G,y-3*G,xj-3*G,y-1.5*G); w.at(w.C(C_SLOW,xj-3*G,y,True),58,64,270); w.W(xj-3*G,y+1.5*G,xj-3*G,y+3*G); w.PW('GND',xj-3*G,y+3*G)
    # RUN switch and the CLK pull-up
    y2=y+12*G
    w.T("RUN / STEP: the switch closes +5V onto RUNSW (1 Meg pull-down); a diode and 1k from RUNSW to CLK are the clock's pull-up, present only in RUN (1k, D053: the rising edge into the cards' 3 nF takes microseconds, not 35)",x-4*G,y2-4*G,1.6,True)
    sw=w.dipswitch(1,x+3*G,y2,"RUN"); w.at(sw,46,78,0); w.label("RUN",43,74,1.0); w.on_mark(46,78,1)
    w.W(x,y2,x-2*G,y2); w.PW('+5V',x-2*G,y2); w.W(x+6*G,y2,x+8*G,y2); w.J(x+8*G,y2); w.L('RUNSW',x+8*G,y2,0,'output')
    w.W(x+8*G,y2,x+8*G,y2+G); w.at(w.R('1Meg',x+8*G,y2+2.5*G),40,86,270); w.W(x+8*G,y2+4*G,x+8*G,y2+5*G); w.PW('GND',x+8*G,y2+5*G)
    w.W(x+8*G,y2,x+9*G,y2); w.at(w.diode(x+10.5*G,y2,180),58,78,0); w.W(x+12*G,y2,x+13*G,y2)          # diode: in STEP the 10k must not pull CLK down against the panel's button
    w.at(w.R('1k',x+14.5*G,y2,90),46,86,270); w.W(x+16*G,y2,x+17*G,y2); w.L('CLK',x+17*G,y2,0,'bidirectional')
    # the halt delay (D050): HLT -> 100k -> HLTD, 2.2n from HLTD to GND; the gate's inverter reads HLTD
    yh=y2+5*G
    w.T("HALT DELAY (D050): HLT through 100k into 2.2 nF, 0.22 ms, so the clock pulse that started the halt step completes and the counter's last increment lands before the clock stops",x-4*G,yh-3*G,1.6,True)
    w.L('HLT',x,yh,180,'input'); w.W(x,yh,x+G,yh); w.at(w.R("100k",x+2.5*G,yh,90),82,64,270); w.W(x+4*G,yh,x+6*G,yh); w.J(x+6*G,yh); w.L('HLTD',x+6*G,yh,0,'output')
    w.W(x+6*G,yh,x+6*G,yh+G); w.at(w.C("2.2n",x+6*G,yh+2.5*G),88,64,270); w.W(x+6*G,yh+4*G,x+6*G,yh+5*G); w.PW('GND',x+6*G,yh+5*G)
    # power-on reset
    y3=y2+16*G
    w.T("POWER-ON RESET: POR charges through 100k into 2.2 uF; 100k into PN with 1 Meg from PB (hysteresis); RD = NOT PB (high while the capacitor is still low, 1k pull-up) drives RST through 100 ohm and a diode against the panel's 10k pull-down (D053)",x-4*G,y3-6*G,1.6,True)
    w.PW('+5V',x,y3-3*G); w.W(x,y3-3*G,x,y3-2.5*G); w.at(w.R('100k',x,y3-G),52,86,270); w.W(x,y3+0.5*G,x,y3+G); w.J(x,y3+G); w.L('POR',x,y3+G,0,'output')
    w.W(x,y3+G,x,y3+2*G); w.at(w.C('2.2u',x,y3+3.5*G,True),58,86,270); w.W(x,y3+5*G,x,y3+6*G); w.PW('GND',x,y3+6*G)
    xs=x+16*G; w.L('POR',xs,y3,180,'input'); w.W(xs,y3,xs+G,y3); w.at(w.R('100k',xs+2.5*G,y3,90),70,86,270); w.W(xs+4*G,y3,xs+6*G,y3); w.J(xs+6*G,y3); w.L('PN',xs+6*G,y3,0,'output')
    w.W(xs+6*G,y3,xs+6*G,y3-G); w.at(w.R('1Meg',xs+6*G,y3-2.5*G),76,86,270); w.W(xs+6*G,y3-4*G,xs+6*G,y3-5*G); w.L('PB',xs+6*G,y3-5*G,90,'input')
    xr=x+30*G; w.L('RD',xr,y3,180,'input'); w.W(xr,y3,xr+G,y3); w.at(w.R('100',xr+2.5*G,y3,90),64,86,270); w.W(xr+4*G,y3,xr+5*G,y3)
    w.at(w.diode(xr+6.5*G,y3,180),52,70,0); w.W(xr+8*G,y3,xr+9*G,y3); w.L('RST',xr+9*G,y3,0,'output')
    # the hold-off (D064): while RST is high the timing capacitor is held empty, so the clock stands still and its first edge comes after the release
    y4=y3+16*G
    w.T("HOLD-OFF (D064): while RST is high this transistor holds X at 0 V through 100 ohm: the Schmitt trigger reads low and the clock gate holds CLK low.  When RST lets go, the card's own reset or the panel's button, X charges from 0 V and the first clock edge comes 1.3 to 5.4 ms later at the fastest setting, never in the 45 us in which the cards leave their resets",x-4*G,y4-10*G,1.6,True)
    gx,gy=max(((r[2],max(r[3],r[5])) for r in w.rails if r[0]=='GND' and r[1]=='B.Cu' and abs(r[2]-r[4])<1e-6),key=lambda t:t[1])      # the tiles' ground trunk that reaches lowest (23.09, 56.64)
    qh=w.Q(x+8*G,y4); w.at(qh,gx,66,0); w.rails.append(('GND','B.Cu',gx,gy,gx,66.0,0.5)); w.L('RST',x+2*G,y4,180,'input'); w.W(x+2*G,y4,x+6*G,y4)      # its source pad on the trunk, extended to it: routed once, the pour on its own left this pad on an island
    w.W(x+9*G,y4-2*G,x+9*G,y4-3*G); w.at(w.R('100',x+9*G,y4-4.5*G),33,64,270); w.W(x+9*G,y4-6*G,x+9*G,y4-7*G); w.L('X',x+9*G,y4-7*G,90,'input')
    w.W(x+9*G,y4+2*G,x+9*G,y4+3*G); w.PW('GND',x+9*G,y4+3*G)
    ksch.write_plan(w,os.path.join(OUT,f'{PROJECT}.plan.json'),(frame.CARD,frame.CARD),extra=extra)
    W=10*G+cols*w.CELL_W+30*G; H=y4+10*G
    open(os.path.join(OUT,f'{PROJECT}.kicad_sch'),'w').write(w.file(W,H))
    ksch.write_project(OUT,PROJECT); ksch.write_fp_lib_table(OUT)      # the pot's footprint is the repository's own
    print("wrote",OUT,"transistors",d.ntransistors(),"tiles",w.pcb_extent)

if __name__=='__main__': main()
