nikolafilip/nibble/sim/pcb.py

"""Build, route and check a board from a KiCad project + placement plan.
Run with KiCad's python:  <kicad>/python3 pcb.py <projectdir> <name> [--no-route] [--passes N] [--silk] [--patch] [--back-header] [--refit REF] [--dsn-only] [--ses file.ses]   (N: freerouting router and optimizer pass cap, default 300 (a dense card needs about 200 to close its last net); a board that cannot finish stops there with its unrouted nets listed; --silk only replaces the silkscreen text of a routed board from the plan; --back-header turns the bus headers of a routed board onto its back in the holes they have (D059) and mirrors their symbols on the schematic: no track moves)
Reads <name>.kicad_sch (via kicad-cli netlist), <name>.plan.json; writes <name>.kicad_pcb, fab/ outputs.
"""
import glob, sys, os, json, subprocess, re
sys.path.insert(0,os.path.dirname(os.path.abspath(__file__)))
import pcbnew, knet
K='/Applications/KiCad/KiCad.app/Contents/MacOS/kicad-cli'
F='/Applications/KiCad/KiCad.app/Contents/SharedSupport/footprints'
JAVA=os.environ.get('NIBBLE_JAVA') or os.path.expanduser('~/.sdkman/candidates/java/21.0.2-tem/bin/java')      # NIBBLE_JAVA: another JVM (freerouting 2.4.1 needs Java 25; 2.1.0 runs on 21)
JAR=os.path.join(os.path.dirname(os.path.abspath(__file__)),'..','tools','freerouting-1.9.0.jar')   # 1.9: -mp caps the passes and the SES is written; 2.1 ignores every cap headless
mm=lambda v:int(round(v*1e6))
V=lambda x,y:pcbnew.VECTOR2I(mm(x),mm(y))

def build(projdir,name,route=True,passes=300,dsn_only=False,ses_file=None):
    sch=os.path.join(projdir,f'{name}.kicad_sch'); net=os.path.join(projdir,f'{name}.net')
    subprocess.run([K,'sch','export','netlist','--format','kicadsexpr','-o',net,sch],check=True,capture_output=True)
    nets,comps=knet.parse(net); plan=json.load(open(os.path.join(projdir,f'{name}.plan.json')))
    W,H=plan['outline']; place=plan['place']
    board=pcbnew.NewBoard(os.path.join(projdir,f'{name}.kicad_pcb'))
    layers=plan['extra'].get('layers',2)          # 4 (the sequencer, D051): In1.Cu is a solid GND plane the router leaves alone, In2.Cu a third routing layer
    if layers==4: board.SetCopperLayerCount(4)
    GND_LAYER=pcbnew.In1_Cu if layers==4 else pcbnew.B_Cu
    ds=board.GetDesignSettings()
    nc=ds.m_NetSettings.GetDefaultNetclass()
    rules=plan['extra'].get('rules',{}); tw=rules.get('track',0.25); cl=rules.get('clearance',0.2)
    nc.SetTrackWidth(mm(tw)); nc.SetClearance(mm(cl)); nc.SetViaDiameter(mm(0.8)); nc.SetViaDrill(mm(0.4))
    ds.m_MinResolvedSpokes=1; ds.m_TrackMinWidth=mm(min(tw,0.25)); ds.m_ViasMinSize=mm(0.6); ds.m_MinThroughDrill=mm(0.3); ds.m_MinClearance=mm(min(cl,0.2))
    # nets
    netobj={}
    for n in nets:
        ni=pcbnew.NETINFO_ITEM(board,n); board.Add(ni); netobj[n]=ni
    padnet={}
    for n,nodes in nets.items():
        for ref,pin in nodes: padnet[(ref,pin)]=n
    # footprints
    holes=[]; missing=[]
    for ref,(val,fp,dnp) in comps.items():
        if not fp or int(re.sub(r'\D','',ref) or 0)>=9000: continue     # testbench parts (refs 9000 and up) are not on the board
        lib,fn=fp.split(':')
        m=pcbnew.FootprintLoad(os.path.join(os.path.dirname(os.path.abspath(__file__)),'..','lib','nibble.pretty') if lib=='nibble' else f'{F}/{lib}.pretty',fn)     # nibble: the repository's own footprints (lib/nibble.pretty), drawn from makers' drawings
        if m is None: missing.append(fp); continue
        m.SetReference(ref); m.SetValue(val)
        hidden=any(ref.startswith(pfx) for pfx in plan['extra'].get('hide_refs',[]))
        if hidden: m.Reference().SetVisible(False)
        if dnp: m.SetDNP(True)
        for t in m.GraphicalItems():    # a hidden part's own silk texts (a diode's "A") clutter a dense tile; a DNP part (an empty matrix crossing, D040) keeps its pads only, so the fitted diodes stand out
            t=t.Cast()
            if t.GetLayer()!=pcbnew.F_SilkS: continue
            if (hidden and isinstance(t,pcbnew.PCB_TEXT)) or dnp: t.SetLayer(pcbnew.F_Fab)     # (a text's visibility is not saved; the fab layer is not made)
        board.Add(m)
        for pad in m.Pads():
            n=padnet.get((ref,pad.GetNumber()))
            if n: pad.SetNet(netobj[n])
        if ref.startswith('H'): holes.append(m); continue
        if ref in place:
            x,y,rot=place[ref][:3]; m.SetPosition(V(x,y)); m.SetOrientationDegrees(rot)
            if len(place[ref])>3 and place[ref][3]=='B': flip_top_bottom(m)     # the pads' nets came from the netlist by pad number and go with the pads
        else: print('WARNING: no placement for',ref,fp); m.SetPosition(V(W+20,10))
    if missing: raise SystemExit('missing footprints: '+str(missing))
    hp=plan['extra'].get('holes')            # explicit hole positions (cards: mid-side), else the four corners
    for k,h in enumerate(holes[:len(hp) if hp else 4]):
        h.SetPosition(V(*hp[k]) if hp else V(4 if k%2==0 else W-4, 4 if k<2 else H-4))
    # outline (inset while routing so the router keeps vias off the edge; restored to full size at the end)
    def outline(inset):
        for d in [d for d in board.GetDrawings() if d.GetLayer()==pcbnew.Edge_Cuts]: board.Remove(d)
        a,b,c,e=inset,inset,W-inset,H-inset
        for (x1,y1,x2,y2) in [(a,b,c,b),(c,b,c,e),(c,e,a,e),(a,e,a,b)]:
            sh=pcbnew.PCB_SHAPE(board); sh.SetShape(pcbnew.SHAPE_T_SEGMENT); sh.SetStart(V(x1,y1)); sh.SetEnd(V(x2,y2)); sh.SetLayer(pcbnew.Edge_Cuts); sh.SetWidth(mm(0.1)); board.Add(sh)
    outline(1.5 if route else 0)
    add_silk(board,plan)
    def pour(netname,layer):
        if netname not in netobj: return
        z=pcbnew.ZONE(board); z.SetLayer(layer); z.SetNet(netobj[netname])
        o=z.Outline(); o.NewOutline()
        for x,y in [(1,1),(W-1,1),(W-1,H-1),(1,H-1)]: o.Append(mm(x),mm(y))
        z.SetPadConnection(pcbnew.ZONE_CONNECTION_THERMAL); z.SetMinThickness(mm(0.25)); z.SetLocalClearance(mm(0.3))
        z.SetZoneName(netname); board.Add(z)
        pcbnew.ZONE_FILLER(board).Fill(board.Zones())
    def gnd_pour():
        for z in list(board.Zones()):
            if not z.GetIsRuleArea(): board.Remove(z)     # the router keepouts stay (a retry exports them again)
        if plan['extra'].get('no_pour'): return      # the hub: the bus lines own the back, ground is wired on the front
        pour('GND',GND_LAYER)
    # pre-routed power rails and stubs (from the tile geometry); the router only sees signals.
    # A rail with an eighth field True is hidden from the router (the inside of the sequencer's diode matrix, D045):
    # it is not on the board while the DSN is written and comes back with the others after the import.
    LAY={'F.Cu':pcbnew.F_Cu,'B.Cu':pcbnew.B_Cu,'In1.Cu':pcbnew.In1_Cu,'In2.Cu':pcbnew.In2_Cu}
    hidden=[]; handoffs=[]
    def add_rails(all=True):
        for r in plan.get('rails',[]):
            net,layer,x1,y1,x2,y2,wd=r[:7]; hide=len(r)>7 and r[7]
            if hide and not all: continue
            t=pcbnew.PCB_TRACK(board); t.SetStart(V(x1,y1)); t.SetEnd(V(x2,y2)); t.SetWidth(mm(wd)); t.SetLayer(LAY[layer]); t.SetNet(netobj[net]); board.Add(t)
            if hide: hidden.append(t)
        handoffs.clear()
        for net,x,y,*h in plan.get('vias',[]):       # a fourth field True: a hand-off via, the end of a hand-led track for the router to wire on (drop_one_layer_vias)
            v=pcbnew.PCB_VIA(board); v.SetPosition(V(x,y)); v.SetDrill(mm(0.4)); v.SetWidth(mm(0.8)); v.SetLayerPair(pcbnew.F_Cu,pcbnew.B_Cu); v.SetNet(netobj[net]); board.Add(v)
            if h and h[0]: handoffs.append(v)
    def hide_rails():
        for t in hidden: board.Remove(t)
        hidden.clear()
    router=plan['extra'].get('router',{})
    keepouts=[]
    def add_keepouts():
        """Rule areas the router must stay out of (the matrix): exported to the DSN as keepouts, removed again at the end."""
        for x1,y1,x2,y2 in router.get('keepout',[]):
            z=pcbnew.ZONE(board); z.SetIsRuleArea(True); z.SetDoNotAllowTracks(True); z.SetDoNotAllowVias(True)
            ls=pcbnew.LSET(); ls.addLayer(pcbnew.F_Cu); ls.addLayer(pcbnew.B_Cu)
            if layers==4: ls.addLayer(pcbnew.In1_Cu)     # the plane layer too; In2 stays open across the matrix (D051)
            z.SetLayerSet(ls)
            o=z.Outline(); o.NewOutline()
            for x,y in [(x1,y1),(x2,y1),(x2,y2),(x1,y2)]: o.Append(mm(x),mm(y))
            z.SetZoneName('router keepout'); board.Add(z); keepouts.append(z)
        if layers==4 and not router.get('route_in1'):       # the plane layer: no tracks anywhere (vias still pass); a wire keepout in the DSN, so the router never uses In1 (D051; route_in1: the plan lets the router use In1 too, the GND pour fills what is left)
            z=pcbnew.ZONE(board); z.SetIsRuleArea(True); z.SetDoNotAllowTracks(True); z.SetDoNotAllowVias(False)
            ls=pcbnew.LSET(); ls.addLayer(pcbnew.In1_Cu); z.SetLayerSet(ls)
            o=z.Outline(); o.NewOutline()
            for x,y in [(0,0),(W,0),(W,H),(0,H)]: o.Append(mm(x),mm(y))
            z.SetZoneName('plane keepout'); board.Add(z); keepouts.append(z)
    def filter_dsn(path):
        """Take the excluded parts (the matrix diodes, whose pads sit on hidden tracks) out of the DSN: their placements
        and their pins. What stays on those nets is what the router has to reach: the row driver pads and the row
        track tails, the column pull-downs and buffers."""
        ex=set(router.get('exclude_refs',[]))
        if not ex: return
        s=open(path).read()
        # D051: the placements stay (their pads are obstacles on every copper layer, so the inner-layer routes thread between the
        # diodes instead of through their pins); only their pins leave the nets, so the router has nothing to route to them
        s=re.sub(r'\b([A-Za-z]+\d+)-\d+\b',lambda m:'' if m.group(1) in ex else m.group(0),s)
        open(path,'w').write(s)
    add_rails()
    pcb=os.path.join(projdir,f'{name}.kicad_pcb'); pcbnew.SaveBoard(pcb,board)
    sync_project(projdir,name,tw,cl)
    print(f'{name}: {len(comps)} parts, {len(nets)} nets, board {W}x{H} mm')
    gnd_pour(); pcbnew.SaveBoard(pcb,board)     # before routing: the router sees GND as a plane and leaves it alone
    if route:
        dsn=os.path.join(projdir,f'{name}.dsn'); ses=os.path.join(projdir,f'{name}.ses')
        best=None
        add_keepouts()
        for attempt in range(1 if ses_file else router.get('attempts',3)):
            hide_rails(); pcbnew.SaveBoard(pcb,board)
            if attempt:     # a retry starts from the saved board, not the in-memory one after the SES import: the DSN of the latter left the router blind to the open pads
                board=pcbnew.LoadBoard(pcb); netobj={n:board.FindNet(n) for n in nets}
            pcbnew.ExportSpecctraDSN(board,dsn); filter_dsn(dsn)
            # pre-routed power (GND/+5V rails, stubs, stitches) is fixed so the router cannot move it; the SES then omits it,
            # and KiCad's SES import replaces all tracks, so the rails are re-added after every import (add_rails below)
            lines=open(dsn).read().split('\n')
            fixed=set(['GND','+5V'])|set(r[0] for r in plan.get('rails',[]))     # every pre-routed net (power, matrix rows and columns) is fixed
            lines=[l.replace('(type route)','(type fix)') if any(f'(net {n})' in l for n in fixed) else l for l in lines]
            # the router's via: 0.6/0.3 (JLCPCB's minimum) whatever the board's netclass says; with 0.8/0.4 it could not drop the last net past the bus header pins on a dense card
            text='\n'.join(lines)
            # (In1 stays "(type signal)": marked "(type power)", freerouting 2.1 and 2.4 could no longer join the drain pads of a tile, three bare
            # transistors on a test board included; the whole-board wire keepout on In1 from add_keepouts keeps the plane layer free of tracks instead)
            for n in router.get('exclude_nets',[]):    # nets the router must leave alone (the sequencer's GND and +5V, D051): their pins leave the network, the pre-routed
                text=re.sub(r'\(net '+re.escape(n)+r'\s*\(pins[^)]*\)',f'(net {n}\n      (pins)',text,count=1)   # rails stay as obstacles; asked to finish power itself around fixed rails, freerouting left 75 of 509 connections open on a test cut against 9
            order=router.get('layer_order')    # freerouting prefers vertical on even DSN layers and horizontal on odd ones (2.5x against), and its own
            if order:                          # autoroute_settings block stops 2.1.0 dead; listing the layers in another order (KiCad maps the SES by name) picks the directions
                blocks={m.group(1):m.group(0) for m in re.finditer(r'    \(layer (\S+)\n      \(type \w+\)\n      \(property\n        \(index \d+\)\n      \)\n    \)\n',text)}
                assert set(order)==set(blocks), (order,list(blocks))
                first=min(text.index(b) for b in blocks.values())
                for b in blocks.values(): text=text.replace(b,'',1)
                text=text[:first]+''.join(re.sub(r'\(index \d+\)',f'(index {k})',blocks[ln]) for k,ln in enumerate(order))+text[first:]
            open(dsn,'w').write(text)
            import shutil; shutil.copy(dsn,dsn+f'.attempt{attempt+1}')      # what the router was given (kept when a connection stayed open)
            if dsn_only: print('DSN written:',dsn); return pcb
            # freerouting's own log goes to <name>.freerouting.log so a long run can be watched
            if ses_file:      # --ses: a session routed outside this run (freerouting 2.1.0 by hand on the exported DSN); imported like the router's own
                import shutil; shutil.copy(ses_file,ses); open(os.path.join(projdir,f'{name}.freerouting.log'),'w').write(f'session imported from {ses_file}\n')
            with open(os.path.join(projdir,f'{name}.freerouting.log'),'a' if ses_file else 'w') as flog:
                if ses_file: pass
                else: jar=os.path.join(os.path.dirname(JAR),router['jar']) if router.get('jar') else JAR      # the plan may pick another freerouting (2.1.0 for the sequencer: 1.9 needs hours per pass there)
                # 2.1.0 honours the pass cap only with its window up (headless it routes until killed) and saves the SES on its own; 2.4.1 (Java 25) runs headless
                new=os.path.basename(jar)>='freerouting-2.4'; flags=(['-Djava.awt.headless=true'] if new else [])
                if not ses_file: subprocess.run([JAVA]+flags+[f"-Xmx{router.get('xmx','4g')}",'-jar',jar,'-de',dsn,'-do',ses,'-mp',str(passes),'-dct','2']+(['-mt','1'] if new else []),stdout=flog,stderr=subprocess.STDOUT,text=True,timeout=router.get('timeout',3*3600))
            class R: stdout=open(os.path.join(projdir,f'{name}.freerouting.log')).read()
            r=R()
            last=[l for l in r.stdout.splitlines() if 'unrouted' in l.lower()]
            m=re.search(r'\((\d+) unrouted',last[-1]) if last else None      # 1.9 "(N unrouted)", 2.1 "(N unrouted and M violations)"
            unrouted=int(m.group(1)) if m else None      # freerouting 1.9 logs no count when it gives up early; KiCad's DRC below is the gate
            print(f'  route attempt {attempt+1}: router reports {unrouted if unrouted is not None else "no unrouted count"}')
            if not os.path.exists(ses): print(r.stdout[-3000:]); raise SystemExit('freerouting produced no SES')
            pcbnew.ImportSpecctraSES(board,ses); os.remove(ses)
            add_rails(); apply_patches(board,plan); drop_one_layer_vias(board,handoffs); gnd_pour(); pcbnew.SaveBoard(pcb,board)
            for _ in range(2):
                if gnd_stitch(board,pcb,netobj,gnd_pour)==0: break
            n=unconnected(pcb)
            if n:       # which connections the router left open (freerouting 1.9 gives up on a few silently; the next attempt starts from these wires)
                for u in json.load(open(pcb.replace('.kicad_pcb','.drc.json'))).get('unconnected_items',[]): print('     open:',' <-> '.join(i['description'] for i in u['items']))
                done=[l for l in r.stdout.splitlines() if 'completed in' in l]; print('     router:',' | '.join(l.split('INFO')[-1].strip()[:60] for l in done[-3:]))
            if best is None or n<best[0]:
                best=(n,pcb.replace('.kicad_pcb','.best.kicad_pcb')); import shutil; shutil.copy(pcb,best[1])
            if n==0: break
        os.remove(dsn)
        if best and best[0]==0:
            for f in glob.glob(dsn+'.attempt*'): os.remove(f)      # (kept when a connection stayed open, for a look at what the router was given)
        if best and best[0]>0:      # keep the best attempt, not the last
            board=pcbnew.LoadBoard(best[1]); netobj={n:board.FindNet(n) for n in nets}
            def gnd_pour():
                for z in list(board.Zones()):
                    if not z.GetIsRuleArea(): board.Remove(z)     # the router keepouts stay (a retry exports them again)
                if plan['extra'].get('no_pour'): return
                pour('GND',GND_LAYER)
        if best and os.path.exists(best[1]): os.remove(best[1])
        for z in [z for z in board.Zones() if z.GetIsRuleArea()]: board.Remove(z)     # the router keepouts (the board reloaded from best has its own copies)
        outline(0); gnd_pour(); pcbnew.SaveBoard(pcb,board)
    sync_project(projdir,name,tw,cl)     # again: SaveBoard rewrites the project file with KiCad's defaults (0.2 mm clearance)
    fit_silk_apart(projdir,name)
    return pcb

def drop_one_layer_vias(board,handoffs):
    """Remove a hand-off via the router left with tracks on one layer only. A hand-off via (a plan via with a fourth field True) is the
    end of a hand-led track for the router to wire on: it takes a via as a target, a bare track end it does not (the hub's CLK and RST
    led past the banana sockets). When the router carries on in the same layer the via joins nothing, KiCad's DRC says so (via_dangling),
    and without it the two tracks still meet at the point. Only hand-off vias are looked at: on the pour cards a plan via is a stub on
    one layer meeting the pour on the other, which is not a track and must stay."""
    tracks=[t for t in board.GetTracks() if t.GetClass()=='PCB_TRACK']; n=0
    for v in handoffs:
        p=v.GetPosition(); layers={t.GetLayer() for t in tracks if t.GetStart()==p or t.GetEnd()==p}
        if len(layers)<2: board.Remove(v); n+=1
    if n: print(f'  {n} hand-off via{"s" if n>1 else ""} dropped (the router did not change layer there)')

def apply_patches(board,plan):
    """Hand fixes after the router (plan extra.patches): [{'net','layer','remove':[[x0,y0,x1,y1],...],'add':[[x0,y0,x1,y1],...],'width'}].
    A removed segment must match an existing track of that net and layer by its endpoints (0.01 mm); a patch whose segments are not
    all there is reported and skipped, so a re-route that no longer has the flaw is not damaged. The sequencer's v9 route left ENF
    hooked across CFQ_m1 on In2 in one spot (freerouting's own tracks crossing); the patch straightens ENF there."""
    patches=plan['extra'].get('patches',[])
    if not patches: return
    def key(x,y): return (round(x,2),round(y,2))
    # {'net','move_via':[[x,y],[nx,ny]]}: nudge a via (and the ends of its net's tracks that meet it); panelc's M6 via sat 0.48 mm
    # hole-to-hole from M4's, under JLCPCB's 0.5 mm, with every rule the router knew satisfied. Skipped when no via is there.
    for pt in [p for p in patches if 'move_via' in p]:
        (x,y),(nx,ny)=pt['move_via']; old=pcbnew.VECTOR2I(int(x*1e6),int(y*1e6)); new=pcbnew.VECTOR2I(int(nx*1e6),int(ny*1e6)); n=0
        for t in board.GetTracks():
            if t.GetNetname()!=pt['net']: continue
            if t.GetClass()=='PCB_VIA' and (t.GetPosition()-old).EuclideanNorm()<1000: t.SetPosition(new); n+=1
            elif t.GetClass()!='PCB_VIA':
                if (t.GetStart()-old).EuclideanNorm()<1000: t.SetStart(new); n+=1
                if (t.GetEnd()-old).EuclideanNorm()<1000: t.SetEnd(new); n+=1
        print(f"   patch {pt['net']}: via at {x},{y} moved to {nx},{ny} ({n} items)" if n else f"   patch {pt['net']}: no via at {x},{y}, skipped")
    patches=[p for p in patches if 'move_via' not in p]
    # read every track's geometry first: pcbnew loses the SWIG types after the first board.Remove in a process
    tracks=[(t,t.GetLayerName(),t.GetNetname(),{key(t.GetStart().x*1e-6,t.GetStart().y*1e-6),key(t.GetEnd().x*1e-6,t.GetEnd().y*1e-6)}) for t in board.GetTracks() if t.GetClass()!='PCB_VIA']
    todo=[]
    for pt in patches:
        found=[]
        for x0,y0,x1,y1 in pt.get('remove',[]):
            want={key(x0,y0),key(x1,y1)}
            hit=[t for t,l,n,ends in tracks if l==pt['layer'] and n==pt['net'] and ends==want and t not in found]
            if hit: found.append(hit[0])
        if len(found)==len(pt.get('remove',[])): todo.append((pt,found))
        else: print(f"   patch {pt['net']} on {pt['layer']}: {len(found)} of {len(pt['remove'])} segments found, skipped")
    for pt,found in todo:
        net=board.FindNet(pt['net']); lay=getattr(pcbnew,pt['layer'].replace('.','_'))
        for t in found: board.Remove(t)
        for x0,y0,x1,y1 in pt.get('add',[]):
            t=pcbnew.PCB_TRACK(board); t.SetStart(pcbnew.VECTOR2I(int(x0*1e6),int(y0*1e6))); t.SetEnd(pcbnew.VECTOR2I(int(x1*1e6),int(y1*1e6)))
            t.SetWidth(int(pt.get('width',0.2)*1e6)); t.SetLayer(lay); t.SetNet(net); board.Add(t)
        print(f"   patch {pt['net']} on {pt['layer']}: {len(found)} segments removed, {len(pt.get('add',[]))} added")

def repatch(projdir,name):
    """Apply the plan's patches to the routed board as it is (a route already done), refill the pour, save."""
    pcb=os.path.join(projdir,f'{name}.kicad_pcb'); plan=json.load(open(os.path.join(projdir,f'{name}.plan.json')))
    board=pcbnew.LoadBoard(pcb); apply_patches(board,plan)
    pcbnew.ZONE_FILLER(board).Fill(board.Zones()); pcbnew.SaveBoard(pcb,board); return pcb

def flip_top_bottom(m):
    """Turn a placed footprint over onto the back of the board in the holes it has: mirrored top to bottom about the middle of
    its pads. A two-row header at rot 90 (pin 1 bottom left, its even row above) ends with pin 1 top left, its even row below
    and its notch toward the top edge: pin 2k-1 in the hole pin 2k had (D059). The nets go with the pads."""
    xs=[p.GetPosition().x for p in m.Pads()]; ys=[p.GetPosition().y for p in m.Pads()]
    m.Flip(pcbnew.VECTOR2I((min(xs)+max(xs))//2,(min(ys)+max(ys))//2),pcbnew.FLIP_DIRECTION_TOP_BOTTOM)

def back_headers(projdir,name):
    """--back-header: the 2x32 bus headers of a routed board go onto its back, in place (D059). The schematic's header symbols
    are mirrored (pin 2k-1 where pin 2k was: the wires and labels stay), the footprints turned over, and every pad takes the
    net the schematic now gives its number, which must be the net its hole already had: no track, via or rail changes. The
    plan gets the placement ('B') and the header's labels, so a rebuild gives the same board. The pour is refilled (pad 1's
    square went to another hole)."""
    import bus
    pcb=os.path.join(projdir,f'{name}.kicad_pcb'); sch=os.path.join(projdir,f'{name}.kicad_sch'); pj=os.path.join(projdir,f'{name}.plan.json')
    import tempfile, shutil
    s=open(sch).read(); num=lambda v:f'{v:.4f}'.rstrip('0').rstrip('.')
    s,k=re.subn(r'(\(lib_id "Connector_Generic:Conn_02x32_Odd_Even"\)\s*)\(at ([\d.-]+) ([\d.-]+) 0\)(?!\s*\(mirror)(\s*)',
                lambda m:f'{m.group(1)}(at {num(float(m.group(2))+2.54)} {m.group(3)} 0){m.group(4)}(mirror y){m.group(4)}',s)
    tmp=tempfile.mkdtemp(prefix=f'back_{name}_'); open(os.path.join(tmp,f'{name}.kicad_sch'),'w').write(s)      # nothing of the project is written until every pad has agreed
    shutil.copy(os.path.join(projdir,f'{name}.kicad_pro'),tmp); net=os.path.join(tmp,f'{name}.net')
    subprocess.run([K,'sch','export','netlist','--format','kicadsexpr','-o',net,os.path.join(tmp,f'{name}.kicad_sch')],check=True,capture_output=True)
    nets,comps=knet.parse(net); padnet={(ref,pin):n for n,nodes in nets.items() for ref,pin in nodes}; shutil.rmtree(tmp,ignore_errors=True)
    board=pcbnew.LoadBoard(pcb); plan=json.load(open(pj)); moved=[]
    for m in board.GetFootprints():
        if not str(m.GetFPID().GetLibItemName()).startswith('IDC-Header_2x32') or m.IsFlipped(): continue
        ref=m.GetReference(); had={(p.GetPosition().x,p.GetPosition().y):p.GetNetname() for p in m.Pads()}
        flip_top_bottom(m)
        for p in m.Pads():
            want=padnet.get((ref,p.GetNumber()),''); was=had[(p.GetPosition().x,p.GetPosition().y)]; free=lambda n:not n or n.startswith('unconnected-')
            if (free(want)!=free(was)) or (not free(want) and want!=was): raise SystemExit(f'{name} {ref} pin {p.GetNumber()}: the schematic says {want or "nothing"}, its hole carries {was or "nothing"}')
            if free(want) and not want: p.SetNetCode(0); continue
            ni=board.FindNet(want)
            if ni is None: ni=pcbnew.NETINFO_ITEM(board,want); board.Add(ni)
            p.SetNet(ni)
        x,y,rot=plan['place'][ref][:3]; plan['place'][ref]=[x,y,rot,'B']; moved.append(ref)
        plan['silk']=[l for l in plan['silk'] if not (l[0]=='1' and abs(l[1]-(x-7.0))<0.01 and abs(l[2]-(y+0.9))<0.01)]+bus.header_labels(x,y)
    if not moved: print('   no bus header on the front of',name); return pcb
    if k!=len(moved): raise SystemExit(f'{name}: {len(moved)} headers on the front of the board, {k} unmirrored symbols on the schematic')
    open(sch,'w').write(s); json.dump(plan,open(pj,'w'),indent=0)
    pcbnew.ZONE_FILLER(board).Fill(board.Zones()); pcbnew.SaveBoard(pcb,board)
    print(f'   {name}: {", ".join(moved)} on the back, {k} symbol{"s" if k!=1 else ""} mirrored'); return resilk(projdir,name)

def refit(projdir,name,ref):
    """--refit REF: a placed part of a routed board takes the footprint its schematic now names, in its holes: the new footprint
    goes where the old one was (same position, rotation and side), every numbered pad must land where the old pad of that
    number was and keeps its net, so no track, via or rail changes; only the part's unnumbered holes (mounting legs), outline
    and silk are the new footprint's. For a part another maker's drawing fits the same pins (the clock's pot, Alpha to Bourns)."""
    pcb=os.path.join(projdir,f'{name}.kicad_pcb'); sch=os.path.join(projdir,f'{name}.kicad_sch')
    s=open(sch).read(); i=s.find(f'(property "Reference" "{ref}"')
    if i<0: raise SystemExit(f'{name}: no {ref} on the schematic')
    fp=re.search(r'\(property "Footprint" "([^"]+)"',s[i:]).group(1); lib,fn=fp.split(':')
    new=pcbnew.FootprintLoad(os.path.join(os.path.dirname(os.path.abspath(__file__)),'..','lib','nibble.pretty') if lib=='nibble' else f'{F}/{lib}.pretty',fn)
    if new is None: raise SystemExit(f'{name} {ref}: no footprint {fp}')
    board=pcbnew.LoadBoard(pcb); old=board.FindFootprintByReference(ref)
    if old is None: raise SystemExit(f'{name}: no {ref} on the board')
    if str(old.GetFPID().GetLibItemName())==fn: print(f'   {name} {ref} already has {fp}'); return pcb
    new.SetReference(ref); new.SetValue(old.GetValue()); new.Reference().SetVisible(old.Reference().IsVisible())
    new.SetPosition(old.GetPosition()); new.SetOrientation(old.GetOrientation())
    if old.IsFlipped(): new.Flip(old.GetPosition(),pcbnew.FLIP_DIRECTION_TOP_BOTTOM)
    had={p.GetNumber():(p.GetPosition().x,p.GetPosition().y,p.GetNetname()) for p in old.Pads() if p.GetNumber()}
    for p in new.Pads():
        if not p.GetNumber(): continue        # a mounting leg: a hole on no net, wherever the new drawing puts it
        if p.GetNumber() not in had: raise SystemExit(f'{name} {ref} pad {p.GetNumber()}: the old footprint had no such pad')
        x,y,net=had.pop(p.GetNumber())
        if (p.GetPosition().x,p.GetPosition().y)!=(x,y): raise SystemExit(f'{name} {ref} pad {p.GetNumber()}: would move from ({x/1e6:.3f},{y/1e6:.3f}) to ({p.GetPosition().x/1e6:.3f},{p.GetPosition().y/1e6:.3f})')
        if net: p.SetNet(board.FindNet(net))
    if had: raise SystemExit(f'{name} {ref}: pads {sorted(had)} of the old footprint have no new pad')
    board.Remove(old); board.Add(new)
    pcbnew.ZONE_FILLER(board).Fill(board.Zones()); pcbnew.SaveBoard(pcb,board)
    print(f'   {name} {ref}: {fp} in the old pins\' holes'); return pcb

def add_silk(board,plan):
    """Board-level silkscreen text from the plan (labels, then the big board name). A label is [text, x, y, size] and may go
    on with an angle and a face, 'B' for the back (mirrored, as the back is read)."""
    for text,x,y,size,*more in plan['silk']+plan['extra'].get('silk',[]):
        rot=more[0] if more else 0; back=len(more)>1 and more[1]=='B'
        t=pcbnew.PCB_TEXT(board); t.SetText(text); t.SetPosition(V(x,y)); t.SetLayer(pcbnew.B_SilkS if back else pcbnew.F_SilkS)
        t.SetTextSize(pcbnew.VECTOR2I(mm(size),mm(size))); t.SetTextThickness(mm(0.15)); t.SetHorizJustify(pcbnew.GR_TEXT_H_ALIGN_LEFT)
        if rot: t.SetTextAngleDegrees(rot)
        if back: t.SetMirrored(True)
        board.Add(t)
    for text,x,y,size in plan['extra'].get('silk_big',[]):
        t=pcbnew.PCB_TEXT(board); t.SetText(text); t.SetPosition(V(x,y)); t.SetLayer(pcbnew.F_SilkS)
        t.SetTextSize(pcbnew.VECTOR2I(mm(size),mm(size))); t.SetTextThickness(mm(0.25)); t.SetHorizJustify(pcbnew.GR_TEXT_H_ALIGN_LEFT); board.Add(t)

def resilk(projdir,name):
    """--silk: replace the board-level silkscreen text of an already routed board from the plan, without re-routing."""
    pcb=os.path.join(projdir,f'{name}.kicad_pcb'); board=pcbnew.LoadBoard(pcb)
    plan=json.load(open(os.path.join(projdir,f'{name}.plan.json')))
    hide=plan['extra'].get('hide_refs',[])
    for m in board.GetFootprints():          # the plan's hidden reference prefixes apply here too (a board routed before a prefix was added)
        if not any(m.GetReference().startswith(pfx) for pfx in hide): continue
        m.Reference().SetVisible(False)
        for t in m.GraphicalItems():
            t=t.Cast()
            if t.GetLayer()==pcbnew.F_SilkS and isinstance(t,pcbnew.PCB_TEXT): t.SetLayer(pcbnew.F_Fab)
    # (the footprint pass goes first: after board.Remove of a text, pcbnew hands back untyped footprint objects)
    for m in [m for m in board.GetFootprints() if m.GetReference()=='LOGO']: board.Remove(m)      # the logo off first (here, not in the fitter's process: a removal there leaves the next loaded board untyped, and every hidden reference became an obstacle; and after a text is removed the footprints are untyped too)
    for d in [d for d in board.GetDrawings() if isinstance(d,pcbnew.PCB_TEXT) and d.GetLayer() in (pcbnew.F_SilkS,pcbnew.B_SilkS)]: board.Remove(d)
    add_silk(board,plan); pcbnew.SaveBoard(pcb,board)
    rules=plan['extra'].get('rules',{}); sync_project(projdir,name,rules.get('track',0.25),rules.get('clearance',0.2))
    fit_silk_apart(projdir,name)
    return pcb

SILK_BOX=lambda b,g=0:(b.GetLeft()-g,b.GetTop()-g,b.GetRight()+g,b.GetBottom()+g)
def silk_obstacles(board,margin=0.3):
    """What board-level silkscreen may not lie on, per face: pads (0.12 mm round them), the parts' own printed outlines and
    visible names, vias (under the mask, but the hole takes the ink), the courtyards of the parts on that face (an LED's
    printed circle stands for its courtyard), and the strip of margin mm inside the board's edge.
    Returns (box, solid, yards, edge, hit, free): box(bbox[,grow]) -> (l,t,r,b) in nm; solid[layer] -> boxes;
    yards[layer] -> (courtyard shape, its box); hit(a,b) -> the two boxes overlap; free(b, near, yard) -> b lies on none."""
    SILK=(pcbnew.F_SilkS,pcbnew.B_SilkS); box=SILK_BOX
    solid={l:[] for l in SILK}; yards={l:[] for l in SILK}
    for m in board.GetFootprints():
        for pad in m.Pads():
            for l,cu in zip(SILK,(pcbnew.F_Cu,pcbnew.B_Cu)):
                if pad.IsOnLayer(cu): solid[l].append(box(pad.GetBoundingBox(),mm(0.12)))
        for g in list(m.GraphicalItems())+[m.Reference(),m.Value()]:
            if g.GetLayer() in SILK and (not isinstance(g,pcbnew.PCB_TEXT) or g.IsVisible()): solid[g.GetLayer()].append(box(g.GetBoundingBox(),mm(0.1)))
        if str(m.GetFPID().GetLibItemName()).startswith('LED'): continue
        m.BuildCourtyardCaches()
        for l,cy in zip(SILK,(pcbnew.F_CrtYd,pcbnew.B_CrtYd)):
            c=m.GetCourtyard(cy)
            if c.OutlineCount(): yards[l].append((c,box(c.BBox())))
    for t in board.GetTracks():
        if t.GetClass()=='PCB_VIA':
            for l in SILK: solid[l].append(box(t.GetBoundingBox(),mm(0.05)))
    e=board.GetBoardEdgesBoundingBox(); edge=(e.GetLeft()+mm(margin),e.GetTop()+mm(margin),e.GetRight()-mm(margin),e.GetBottom()-mm(margin))
    hit=lambda a,b:a[0]<b[2] and b[0]<a[2] and a[1]<b[3] and b[1]<a[3]
    def free(b,near,yard):
        if b[0]<edge[0] or b[1]<edge[1] or b[2]>edge[2] or b[3]>edge[3]: return False
        if any(hit(b,o) for o in near): return False
        for c,cb in yard:
            if hit(b,cb) and any(c.Contains(pcbnew.VECTOR2I(x,y)) for x in list(range(b[0],b[2],mm(0.2)))+[b[2]] for y in list(range(b[1],b[3],mm(0.2)))+[b[3]]): return False
        return True
    return box,solid,yards,edge,hit,free

LOGO_LIB=os.path.abspath(os.path.join(os.path.dirname(os.path.abspath(__file__)),'..','lib','nibble.pretty'))
def place_logo(projdir,name):
    """The Nibble logo (lib/nibble.pretty/Logo_Nibble*, from sim/logo.py), reference LOGO, on the front of a board whose
    plan says extra.logo = "auto" (the sequencer's: one maker's mark on the machine, not one on every card, which read as
    a product line): the icon and the word where a free patch 27 x 8 mm is to be had, the icon alone (8 x 8) otherwise,
    the nearest such patch to the board's name. Free: 0.5 mm clear of every pad, via, part outline, courtyard and label as
    the plan put it, 1 mm inside the edge; judged on a 0.5 mm grid. The same board gives the same place; the fitter then
    keeps the labels off it."""
    import math
    pcb=os.path.join(projdir,f'{name}.kicad_pcb'); board=pcbnew.LoadBoard(pcb)
    plan=json.load(open(os.path.join(projdir,f'{name}.plan.json')))
    if any(m.GetReference()=='LOGO' for m in board.GetFootprints()): raise SystemExit(f'{name} already has a logo: resilk takes it off first')
    if plan['extra'].get('logo') is None: print('   no logo on',name); return
    box,solid,yards,edge,hit,free=silk_obstacles(board,margin=1.0); L=pcbnew.F_SilkS
    texts=[d for d in board.GetDrawings() if isinstance(d,pcbnew.PCB_TEXT) and d.GetLayer()==L]
    near=solid[L]+[box(t.GetBoundingBox(),mm(0.5)) for t in texts]; yard=yards[L]
    big=max(texts,key=lambda t:(t.GetTextSize().x,-t.GetPosition().y),default=None); nb=box(big.GetBoundingBox()) if big else edge
    nx,ny=(nb[0]+nb[2])//2,(nb[1]+nb[3])//2
    G=mm(0.5); cols=range(edge[0],edge[2],G); rows=range(edge[1],edge[3],G)
    taken=set()           # the cells any obstacle touches: a candidate is read off the grid first, exactly only when the grid is clear
    for o in near:
        for cx in range((o[0]-edge[0])//G,(o[2]-edge[0])//G+1):
            for cy in range((o[1]-edge[1])//G,(o[3]-edge[1])//G+1): taken.add((cx,cy))
    for c,cb in yard:
        for cx in range((cb[0]-edge[0])//G,(cb[2]-edge[0])//G+1):
            for cy in range((cb[1]-edge[1])//G,(cb[3]-edge[1])//G+1):
                if (cx,cy) not in taken and c.Contains(pcbnew.VECTOR2I(edge[0]+cx*G+G//2,edge[1]+cy*G+G//2)): taken.add((cx,cy))
    for fp in ('Logo_Nibble','Logo_Nibble_Icon'):
        m=pcbnew.FootprintLoad(LOGO_LIB,fp); m.SetReference('LOGO'); m.SetPosition(pcbnew.VECTOR2I(0,0))
        b=box(m.GetBoundingBox(False,False),mm(0.5)); w,h=b[2]-b[0],b[3]-b[1]; cw,ch=w//G+2,h//G+2
        cands=sorted(((math.hypot(x+w//2-nx,y+h//2-ny),y,x) for x in cols for y in rows if x+w<=edge[2] and y+h<=edge[3]))
        for d,y,x in cands:
            cx0,cy0=(x-edge[0])//G,(y-edge[1])//G
            if any((cx,cy) in taken for cx in range(cx0,cx0+cw) for cy in range(cy0,cy0+ch)): continue
            if free((x,y,x+w,y+h),near,yard):
                m.SetPosition(pcbnew.VECTOR2I(x-b[0],y-b[1])); board.Add(m); pcbnew.SaveBoard(pcb,board)
                print(f'   logo: {fp} at ({(x-b[0])/1e6:.1f}, {(y-b[1])/1e6:.1f}), {d/1e6:.0f} mm from the name'); return
    print('   logo: NO ROOM on',name)

def fit_silk_apart(projdir,name):
    """fit_silk in a python of its own: once a text has been removed from a board, pcbnew hands this process untyped objects
    (a board loaded afterwards has no GetDrawings)."""
    r=subprocess.run([sys.executable,os.path.abspath(__file__),projdir,name,'--fit-silk'],capture_output=True,text=True)
    out=[l for l in r.stdout.splitlines() if l.startswith('   silk:') or l.startswith('   logo:') or l.startswith('   no logo')]
    if r.returncode or not out: print(r.stdout[-2000:],r.stderr[-2000:]); raise SystemExit('fit_silk failed')
    print('\n'.join(out))

SILK_MIN=1.0          # mm: the text height JLCPCB says it prints; 0.8 mm may or may not come out
def fit_silk(projdir,name):
    """Every board-level label to SILK_MIN where it fits, and out from under the parts. A label may not lie on a pad, on a
    via (it is under the mask, but its hole takes the ink: IR0 read dR0), on a part's printed outline or reference, on another
    label, in the courtyard of a part on its face (the name would be under the
    part; an LED's printed circle stands for its courtyard, which is 0.35 mm wider than the LED's flange), or within 0.3 mm of
    the board's edge. The labels that are large already stand first; each of the others takes the nearest place to where the
    plan put it that is free, on a 0.1 mm grid: at SILK_MIN within 1.2 mm, then the same turned upright (reading upward: a
    name in the gap between an LED and the next part), then the two again within 3 mm, then lying within 6 mm; only when
    SILK_MIN has no place does it try its own smaller size, in the same order to 3 mm; with no place at all it stays as the
    plan had it. A label is measured by its ink (its letters' height and stroke,
    and room below the line for a p or a bracket), not by KiCad's box around it, which is half as high again. KiCad's DRC,
    which knows the letters' shapes, then judges the result: a label it objects to is placed again by KiCad's box, and one it
    still objects to goes back to the plan's place and size. The plan is not touched: the same plan and the same board give
    the same silkscreen."""
    import tempfile, shutil, math
    place_logo(projdir,name)       # first, so that the labels are fitted around the logo
    pcb=os.path.join(projdir,f'{name}.kicad_pcb'); board=pcbnew.LoadBoard(pcb); SILK=(pcbnew.F_SilkS,pcbnew.B_SilkS)
    T=sorted([d for d in board.GetDrawings() if isinstance(d,pcbnew.PCB_TEXT) and d.GetLayer() in SILK],key=lambda t:(t.GetLayer(),t.GetPosition().y,t.GetPosition().x,t.GetText()))
    at0=[(t.GetPosition().x,t.GetPosition().y) for t in T]; size0=[t.GetTextSize().x for t in T]; turn0=[t.GetTextAngleDegrees() for t in T]
    box,solid,yards,edge,hit,free=silk_obstacles(board)
    ring=sorted(((dx*0.1,dy*0.1) for dx in range(-60,61) for dy in range(-60,61)),key=lambda d:(round(math.hypot(*d),3),d[1],d[0]))
    def put(k,d,size,turn=0):
        T[k].SetPosition(pcbnew.VECTOR2I(at0[k][0]+mm(d[0]),at0[k][1]+mm(d[1]))); T[k].SetTextSize(pcbnew.VECTOR2I(size,size)); T[k].SetTextAngleDegrees(turn0[k]+turn)
        T[k].SetHorizJustify(pcbnew.GR_TEXT_H_ALIGN_CENTER if turn else pcbnew.GR_TEXT_H_ALIGN_LEFT)       # a name turned upright here stands centred on the plan's point
    def ink(t,tight=True):
        """The label's box: KiCad's own, or with its height cut down to the letters (cap height, stroke, 0.05 mm; 0.35 of the
        height more below the line when a letter hangs under it)."""
        b=box(t.GetBoundingBox())
        if not tight: return b
        z=t.GetTextSize().x; h=z//2+t.GetTextThickness()//2+mm(0.05); low=int(0.35*z) if set(t.GetText())&set('gjpqy()[],;') else 0
        if int(round(t.GetTextAngleDegrees()))%180==0: c=(b[1]+b[3])//2; return (b[0],c-h,b[2],c+h+low)
        c=(b[0]+b[2])//2; return (c-h,b[1],c+h+low,b[3])          # upright, reading upward: under the line is to the right
    placed={l:{} for l in SILK}; lost=[]
    def place(k,tight):
        big=max(size0[k],mm(SILK_MIN)); l=T[k].GetLayer(); placed[l].pop(k,None)
        put(k,(0,0),big); b0=box(T[k].GetBoundingBox()); R=max(b0[2]-b0[0],b0[3]-b0[1])+mm(7)      # the label's length (it may be turned) and the 6 mm it may move
        here=(at0[k][0]-R,at0[k][1]-R,at0[k][0]+R,at0[k][1]+R)      # nothing farther than this from the plan's point can touch the label (12 mm was too near for a label 31 mm long: HEADER HERE lay across two vias)
        near=[o for o in solid[l]+list(placed[l].values()) if hit(here,o)]; yard=[y for y in yards[l] if hit(here,y[1])]
        for size,reach,turn in ((big,1.2,0),(big,1.2,90),(big,3.0,0),(big,3.0,90),(big,6.0,0),(size0[k],1.2,0),(size0[k],1.2,90),(size0[k],3.0,0),(size0[k],3.0,90)):      # every place at full size before any at the plan's smaller size (RUN and WRH stayed 0.8 mm lying down with room to stand at 1.0 mm)
            if turn and turn0[k]: continue      # (a name the plan stood upright stays as the plan turned it)
            put(k,(0,0),size,turn); b0=ink(T[k],tight)
            spot=next((d for d in ring if math.hypot(*d)<=reach+1e-9 and free((b0[0]+mm(d[0]),b0[1]+mm(d[1]),b0[2]+mm(d[0]),b0[3]+mm(d[1])),near,yard)),None)
            if spot is not None: put(k,spot,size,turn); break
        else:
            put(k,(0,0),size0[k])
            if k not in lost: lost.append(k)
        placed[l][k]=ink(T[k],tight)
    for k in sorted(range(len(T)),key=lambda k:size0[k]<mm(SILK_MIN)): place(k,True)      # the labels that are large already stand first: the others make room for them
    tmp=tempfile.mkdtemp(prefix=f'silk_{name}_'); tp=os.path.join(tmp,f'{name}.kicad_pcb'); shutil.copy(os.path.join(projdir,f'{name}.kicad_pro'),tmp)
    def objected():
        pcbnew.SaveBoard(tp,board); rep=os.path.join(tmp,'drc.json')
        subprocess.run([K,'pcb','drc','--format','json','--severity-all','-o',rep,tp],capture_output=True); ids={t.m_Uuid.AsString():k for k,t in enumerate(T)}
        return sorted({ids[i['uuid']] for v in json.load(open(rep))['violations'] if v['type'].startswith(('silk','text')) for i in v['items'] if i.get('uuid') in ids})
    again=objected()
    for k in again: place(k,False)
    back=objected() if again else []
    for k in back: put(k,(0,0),size0[k])
    still=objected() if back else []
    pcbnew.SaveBoard(pcb,board); shutil.rmtree(tmp,ignore_errors=True)
    rules=json.load(open(os.path.join(projdir,f'{name}.plan.json')))['extra'].get('rules',{}); sync_project(projdir,name,rules.get('track',0.25),rules.get('clearance',0.2))
    small=[k for k in range(len(T)) if T[k].GetTextSize().x<mm(SILK_MIN)]; far=[k for k in range(len(T)) if math.hypot(T[k].GetPosition().x-at0[k][0],T[k].GetPosition().y-at0[k][1])>mm(1.21)]
    moved=[k for k in range(len(T)) if (T[k].GetPosition().x,T[k].GetPosition().y)!=at0[k]]; names=lambda ks:', '.join(sorted(T[k].GetText() for k in ks))
    upright=[k for k in range(len(T)) if T[k].GetTextAngleDegrees()!=turn0[k]]
    print(f'   silk: {len(T)} labels, {sum(1 for z in size0 if z<mm(SILK_MIN))} under {SILK_MIN} mm in the plan, {len(small)} on the board; {len(moved)} moved'
          +(f'; under {SILK_MIN} mm: {names(small)}' if small else '')+(f'; turned upright: {names(upright)}' if upright else '')+(f'; moved more than 1.2 mm: {names(far)}' if far else '')
          +(f'; no free place, left as planned: {names(lost)}' if lost else '')+(f'; placed again by KiCad\'s box: {names(again)}' if again else '')+(f'; DRC sent back to the plan: {names(back)}' if back else '')+(f'; DRC still objects to: {names(still)}' if still else ''))

def gnd_stitch(board,pcb,netobj,refill,gndname='GND'):
    """For every GND pad DRC reports as not reached by the pour, add a via in a nearby free spot and a short track to it.
    Each candidate is verified with a real DRC run (the spot must actually reduce the unconnected count)."""
    import math
    rep=pcb.replace('.kicad_pcb','.drc.json')
    def drc_count():
        subprocess.run([K,'pcb','drc','--format','json','-o',rep,pcb],capture_output=True)
        return json.load(open(rep)).get('unconnected_items',[])
    items=drc_count(); todo=[]
    for u in items:
        for it in u['items']:
            d=it['description']
            if d.startswith('PTH pad') and f'[{gndname}]' in d and (it['pos']['x'],it['pos']['y']) not in todo: todo.append((it['pos']['x'],it['pos']['y']))
    if not todo: return 0
    gnd=netobj[gndname]
    pads=[(p.GetPosition().x/1e6,p.GetPosition().y/1e6,p.GetNetname()) for fp in board.GetFootprints() for p in fp.Pads()]
    segs=[]; vias=[]
    for t in board.GetTracks():
        if t.GetClass()=='PCB_VIA': vias.append((t.GetPosition().x/1e6,t.GetPosition().y/1e6,t.GetNetname()))
        else: segs.append((t.GetStart().x/1e6,t.GetStart().y/1e6,t.GetEnd().x/1e6,t.GetEnd().y/1e6,t.GetNetname(),t.GetLayer()))
    def dseg(px,py,x1,y1,x2,y2):
        dx,dy=x2-x1,y2-y1; L=dx*dx+dy*dy
        t=0 if L==0 else max(0,min(1,((px-x1)*dx+(py-y1)*dy)/L)); return math.hypot(px-(x1+t*dx),py-(y1+t*dy))
    def free_point(x,y):
        return all(math.hypot(x-px,y-py)>=1.6 for px,py,n in pads) and all(math.hypot(x-vx,y-vy)>=1.3 for vx,vy,n in vias) and all(dseg(x,y,*sg[:4])>=0.9 for sg in segs if sg[4]!=gndname)
    def cross(ax,ay,bx,by,cx,cy,dx,dy):
        def o(px,py,qx,qy,rx,ry): return (qy-py)*(rx-qx)-(qx-px)*(ry-qy)
        o1,o2,o3,o4=o(ax,ay,bx,by,cx,cy),o(ax,ay,bx,by,dx,dy),o(cx,cy,dx,dy,ax,ay),o(cx,cy,dx,dy,bx,by)
        return (o1*o2<0) and (o3*o4<0)
    def free_track(x1,y1,x2,y2,layer):
        for px,py,n in pads:
            if n!=gndname and dseg(px,py,x1,y1,x2,y2)<1.3: return False
        for sg in segs:
            if sg[4]!=gndname and sg[5]==layer:
                if cross(x1,y1,x2,y2,*sg[:4]): return False
                if min(dseg(sg[0],sg[1],x1,y1,x2,y2),dseg(sg[2],sg[3],x1,y1,x2,y2),dseg(x1,y1,*sg[:4]),dseg(x2,y2,*sg[:4]))<0.6: return False
        return True
    bb=board.GetBoardEdgesBoundingBox(); R=bb.GetRight()/1e6; B=bb.GetBottom()/1e6
    added=0; before=len(items)
    for (x,y) in todo:
        done=False; tried=0
        for r in (2.2,2.8,3.4,4.0,5.0,6.0):
            for k in range(16):
                a=2*math.pi*k/16; vx,vy=x+r*math.cos(a),y+r*math.sin(a)
                if not (2<vx<R-2 and 2<vy<B-2) or not free_point(vx,vy): continue
                layer=next((L for L in (pcbnew.F_Cu,pcbnew.B_Cu) if free_track(x,y,vx,vy,L)),None)
                if layer is None: continue
                v=pcbnew.PCB_VIA(board); v.SetPosition(V(vx,vy)); v.SetDrill(mm(0.4)); v.SetWidth(mm(0.8)); v.SetLayerPair(pcbnew.F_Cu,pcbnew.B_Cu); v.SetNet(gnd); board.Add(v)
                t=pcbnew.PCB_TRACK(board); t.SetStart(V(x,y)); t.SetEnd(V(vx,vy)); t.SetWidth(mm(0.4)); t.SetLayer(layer); t.SetNet(gnd); board.Add(t)
                refill(); pcbnew.SaveBoard(pcb,board)
                now=len(drc_count()); tried+=1
                if now<before:
                    before=now; vias.append((vx,vy,gndname)); segs.append((x,y,vx,vy,gndname,layer)); added+=1; done=True; break
                board.Remove(v); board.Remove(t)
                if tried>=10: break
            if done or tried>=10: break
        if not done: print('   gnd_stitch: no working spot near',x,y)
    refill(); pcbnew.SaveBoard(pcb,board)
    print(f'   gnd_stitch: {added} vias for {len(todo)} pads, unconnected now {before}')
    return added

def unconnected(pcb):
    rep=pcb.replace('.kicad_pcb','.drc.json')
    subprocess.run([K,'pcb','drc','--format','json','-o',rep,pcb],capture_output=True)
    n=len(json.load(open(rep)).get('unconnected_items',[])); print('   DRC unconnected:',n); return n

def sync_project(projdir,name,tw,cl):
    """kicad-cli reads design rules from <name>.kicad_pro, which ERC or KiCad may have filled with defaults (0.2 mm clearance):
    write the board's rules into it so DRC judges the board by the rules it was routed with."""
    pro=os.path.join(projdir,f'{name}.kicad_pro'); j=json.load(open(pro)) if os.path.exists(pro) else {}
    ds=j.setdefault('board',{}).setdefault('design_settings',{}); r=ds.setdefault('rules',{})
    r.update({'min_clearance':min(cl,0.2),'min_track_width':min(tw,0.25),'min_via_diameter':0.6,'min_through_hole_diameter':0.3,'min_resolved_spokes':1})
    ns=j.setdefault('net_settings',{}); cls=ns.setdefault('classes',[])
    if not cls: cls.append({'name':'Default'})
    cls[0].update({'clearance':cl,'track_width':tw,'via_diameter':0.6,'via_drill':0.3})     # 0.6/0.3 (JLCPCB's minimum): with 0.8/0.4 the router could not drop the last net past the bus header pins on a dense card
    json.dump(j,open(pro,'w'),indent=2)

def drc(pcb):
    rep=pcb.replace('.kicad_pcb','.drc.json')
    subprocess.run([K,'pcb','drc','--format','json','--severity-all','-o',rep,pcb],capture_output=True)
    j=json.load(open(rep)); import collections
    c=collections.Counter((v['severity'],v['type']) for v in j['violations'])
    unc=len(j.get('unconnected_items',[]))
    print('DRC:',dict(c),'unconnected:',unc)
    for v in j['violations'][:8]: print('  ',v['severity'],v['type'],v['description'][:80])
    return j

def outputs(pcb,name):
    d=os.path.dirname(pcb); fab=os.path.join(d,'fab'); os.makedirs(fab,exist_ok=True)
    subprocess.run([K,'pcb','export','gerbers','-o',fab+'/',pcb],capture_output=True)
    subprocess.run([K,'pcb','export','drill','-o',fab+'/',pcb],capture_output=True)
    subprocess.run([K,'pcb','export','pos','--format','csv','--units','mm','--exclude-dnp','-o',os.path.join(fab,f'{name}-pos.csv'),pcb],capture_output=True)
    subprocess.run([K,'sch','export','bom','--fields','Reference,Value,Footprint,${QUANTITY}','--group-by','Value,Footprint','--exclude-dnp','-o',os.path.join(fab,f'{name}-bom.csv'),os.path.join(d,f'{name}.kicad_sch')],capture_output=True)
    for side,fn in [('top',f'{name}-top.png'),('bottom',f'{name}-bottom.png')]:
        subprocess.run([K,'pcb','render','--side',side,'--width','2000','--height','1400','--quality','high','-o',os.path.join(fab,fn),pcb],capture_output=True)
    import order_check; order_check.write_zip(fab,name)      # fab/<name>-gerbers.zip: the nine files the fab takes, the file that gets uploaded
    import assembly; assembly.draw(name,d=d)                 # fab/<name>-assembly.svg: which value goes where (the cards print no values)
    print('fab outputs in',fab)

if __name__=='__main__':
    projdir,name=sys.argv[1],sys.argv[2]
    passes=int(sys.argv[sys.argv.index("--passes")+1]) if "--passes" in sys.argv else 300
    if '--fit-silk' in sys.argv: fit_silk(projdir,name); sys.exit(0)                               # (what resilk and build run at their end, in a process of its own)
    if '--dsn-only' in sys.argv: build(projdir,name,passes=passes,dsn_only=True); sys.exit(0)     # write the filtered DSN the router would get, and stop
    ses_file=sys.argv[sys.argv.index('--ses')+1] if '--ses' in sys.argv else None                 # import a session routed by hand from that DSN instead of running the router
    pcb=refit(projdir,name,sys.argv[sys.argv.index('--refit')+1]) if '--refit' in sys.argv else back_headers(projdir,name) if '--back-header' in sys.argv else resilk(projdir,name) if '--silk' in sys.argv else repatch(projdir,name) if '--patch' in sys.argv else build(projdir,name,route='--no-route' not in sys.argv,passes=passes,ses_file=ses_file)
    drc(pcb); outputs(pcb,name)
