nikolafilip/nibble/sim/build_panel.py

"""Generate boards/06-panel from panel.py: schematic + PCB placement plan."""
import os, ksch, frame, bus, panel
G=ksch.G; OUT=os.path.join(os.path.dirname(os.path.abspath(__file__)),'..','boards','06-panel'); PROJECT='panel'

def dip8_levels(w,x,y,names,title,pcb):
    """DIP-8 or DIP-4: left pins to +5V, right pins through 10k to the named lines. pcb=(x,y,rx,ry): switch and resistor column positions."""
    nn=len(names); sw=w.dipswitch(nn,x,y,title); px,py,rx,ry=pcb; w.at(sw,px,py,0); w.rails.append(('+5V','F.Cu',px,py,px,py+(nn-1)*2.54,0.5))
    top=y-(nn//2)*G; bot=top+(nn-1)*G
    w.W(x-3*G,top,x-3*G,bot); w.W(x-3*G,top,x-3*G,top-2*G); w.PW('+5V',x-3*G,top-2*G)
    for i in range(nn):
        sy=top+i*G
        if i not in (0,nn-1): w.J(x-3*G,sy)
        n=names[i]
        w.label(n or '-',px-9,py+i*2.54-0.6,1.0)
        if n is None:
            w.body+=f'\t(no_connect\n\t\t(at {ksch.f(x+3*G)} {ksch.f(sy)})\n\t\t(uuid "{ksch.U()}")\n\t)\n'; continue
        w.W(x+3*G,sy,x+4*G,sy); r=w.R('10k',x+5.5*G,sy,90); w.W(x+7*G,sy,x+8*G,sy); w.L(n,x+8*G,sy,0,'output')
        w.at(r,rx+(i%2)*6,ry+(i//2)*8,270)
def button(w,x,y,name,pcb):
    """+5V -> button -> 10k -> X (1u, 220k to GND) -> 100k -> N (label name_N); name_S2 -> 1Meg -> N; name_S2 -> 10k -> diode -> name"""
    px,py=pcb
    w.T(name+" button",x-4*G,y-4*G,1.27,True)
    w.PW('+5V',x-4*G,y-2*G); w.W(x-4*G,y-2*G,x-4*G,y); w.W(x-4*G,y,x-2*G,y)
    w.at(w.button(x,y,name),px,py,0); w.label(name,px+1,py-3.5,1.5)
    w.W(x+2*G,y,x+3*G,y); w.at(w.R('10k',x+4.5*G,y,90),px+14,py-2,270); w.W(x+6*G,y,x+8*G,y)
    xx=x+8*G; w.J(xx,y)
    w.W(xx,y,xx,y+G); w.at(w.C('1u',xx,y+2.5*G,True),px+19,py-2,270); w.W(xx,y+4*G,xx,y+5*G); w.PW('GND',xx,y+5*G)
    w.W(xx,y,xx+3*G,y); w.J(xx+3*G,y); w.W(xx+3*G,y,xx+3*G,y+G); w.at(w.R('220k',xx+3*G,y+2.5*G),px+24,py-2,270); w.W(xx+3*G,y+4*G,xx+3*G,y+5*G); w.PW('GND',xx+3*G,y+5*G)
    w.W(xx+3*G,y,xx+4*G,y); w.at(w.R('100k',xx+5.5*G,y,90),px+29,py-2,270); w.W(xx+7*G,y,xx+9*G,y); xn=xx+9*G; w.J(xn,y)
    w.L(name+'_N',xn,y,0,'output')
    w.L(name+'_S2',xn-G,y-4*G,180,'input'); w.W(xn-G,y-4*G,xn,y-4*G); w.W(xn,y-4*G,xn,y-3*G); w.at(w.R('1Meg',xn,y-1.5*G),px+34,py-2,270); w.W(xn,y-0*G,xn,y)
    xo=xn+6*G
    w.L(name+'_S2',xo,y,180,'input'); w.W(xo,y,xo+G,y); w.at(w.R('10k',xo+2.5*G,y,90),px+39,py-2,270); w.W(xo+4*G,y,xo+5*G,y)
    w.at(w.diode(xo+6.5*G,y,180),px+14,py+7,0); w.W(xo+8*G,y,xo+9*G,y); w.L(name,xo+9*G,y,0,'output')
    w.rails.append(('GND','F.Cu',px+19,py,px+24,py+3.08,0.5))      # debounce cap ground -> 220k ground (pre-routed)

def main():
    d=panel.build(); assert not d.check(), d.check()
    os.makedirs(OUT,exist_ok=True); root=ksch.U()
    w=ksch.Writer(PROJECT,root)
    w.T("NIBBLE BOARD 06 - FRONT PANEL: switches to force any bus line, debounced CLK and RST buttons, an LED on every line",10*G,6*G,3.5,True)
    w.T(f"{d.ntransistors()} transistors, {d.nleds()} LEDs.  Level switches connect a line to +5V through 10k: a switch left on can never fight a board that pulls the line low, it only adds a 1 where nothing else drives.\n"
        "Every switched or observed line has a 1Meg pull-down so it reads 0 when no board drives it.  The DATA switches are the input port: a closed switch is a 1, and while INP=1 the four bits are driven onto the bus (open drain) for the IN instruction.\n"
        "CLK and RST come from RC-debounced buttons through a Schmitt trigger and a diode, so the clock board can drive the same lines later.  Order 1 test: hub + panel + ALU: set A, B, SUB, EO; read S on the D3..D0 LEDs and CF/ZF.\n"
        "The M0..M7 LEDs have no pull-downs here: the M lines are pulled down on the hub (D021).",10*G,16*G,1.6)
    used=set(panel.LEVEL_SW+panel.CTRL_SW1+panel.CTRL_SW2+panel.CTRL_SW3+panel.OBSERVED+panel.BUTTONS+['BUS0#','BUS1#','BUS2#','BUS3#'])
    SX=170; BW=SX+76; BH=250; HY=BH-8; BY=HY-22; w.PCB_COL=15.24     # SX: left edge of the switch/pull-down area (LED matrix to its left); BY: the CLK/RST button row, above the header
    j=frame.bus_header(w,30*G,40*G,used); w.at(j,50,HY,90); w.label("BUS  (pin 1 left)",52,HY-8,1.2); frame.header_gnd(w,50,HY,+1)
    frame.power_flags(w,44*G,32*G)
    c1,c2=frame.decoupling(w,52*G,32*G); w.at(c1,140,BY,270); w.at(c2,146,BY,270); frame.cap_gnd(w,140,BY,2.5); frame.cap_gnd(w,146,BY,2.0)
    frame.holes(w,72*G,32*G,4)
    sx=100*G
    dip8_levels(w,sx,34*G,panel.LEVEL_SW,"A3..A0 B3..B0",(SX+4,12,SX+20,10))
    dip8_levels(w,sx+22*G,34*G,panel.CTRL_SW1," ".join(panel.CTRL_SW1),(SX+4,46,SX+20,44))
    dip8_levels(w,sx+44*G,34*G,panel.CTRL_SW2," ".join(panel.CTRL_SW2),(SX+4,80,SX+20,78))
    dip8_levels(w,sx+66*G,34*G,panel.CTRL_SW3," ".join(panel.CTRL_SW3),(SX+4,114,SX+20,112))
    dip8_levels(w,sx+88*G,34*G,panel.DATA_SW,"DATA (input port, read by IN)",(SX+44,12,SX+60,10))
    w.rails.append(('+5V','F.Cu',SX+4,12,SX+4,114,0.5))   # one +5V spine through the four DIP-8 switch columns
    w.label("A3..B0",SX+3,8,1.0); w.label("CONTROL",SX+3,42,1.0); w.label("CONTROL",SX+3,76,1.0); w.label("CONTROL",SX+3,110,1.0); w.label("DATA IN",SX+43,8,1.0)
    button(w,sx+80*G,30*G,'CLK',(8,BY)); button(w,sx+80*G,42*G,'RST',(64,BY))
    w.T("1Meg pull-downs: every line the panel switches or observes reads 0 when no board drives it",10*G,58*G,1.6,True)
    PR=12   # pull-downs per row
    for k,n in enumerate(panel.PULLDOWNS):
        r=frame.pulldown(w,n,12*G+(k%20)*4*G,60*G+(k//20)*8*G); w.at(r,SX+(k%PR)*6,178+(k//PR)*10,270)
    w.label("1Meg PULL-DOWNS",SX,176,1.0)
    nrow=(len(panel.PULLDOWNS)+PR-1)//PR
    for r in range(nrow):   # GND bar through each row's ground pads, joined at the left end
        last=SX+(min(PR,len(panel.PULLDOWNS)-r*PR)-1)*6
        w.rails.append(('GND','F.Cu',SX-3,178+r*10+5.08,last,178+r*10+5.08,0.5))
    w.rails.append(('GND','F.Cu',SX-3,183.08,SX-3,HY-2.54,0.5))   # joiner runs down to the header pin-64 ground via
    yend=w.layout(d.gates,panel.GROUP_TITLES,10*G,80*G,16,pcb_origin=(12.0,16.0),pcb_cols=10)
    assert w.pcb_extent[1]<BY-8, w.pcb_extent
    frame.header_gnd_link(w,50,HY,w.pcb_extent[1]+6)
    # header pin-64 ground via (placed by frame.header_gnd at x = pin 64 + 2.5) -> pull-down ground joiner (both at the bottom right)
    x64=50+((bus.N-1)//2)*2.54+2.5
    w.rails.append(('GND','B.Cu',x64,HY-2.54,SX-3,HY-2.54,0.5)); w.vias.append(('GND',SX-3,HY-2.54))
    W=10*G+16*w.CELL_W+30*G; H=yend+10*G
    open(os.path.join(OUT,f'{PROJECT}.kicad_sch'),'w').write(w.file(W,H))
    ksch.write_project(OUT,PROJECT)
    ksch.write_plan(w,os.path.join(OUT,f'{PROJECT}.plan.json'),(BW,BH),extra=dict(silk_big=[("NIBBLE FRONT PANEL",8,5,1.8)],hide_refs=['Q','R','D']))
    print("wrote",OUT,"transistors",d.ntransistors(),"leds",d.nleds(),"resistors",d.nresistors(),"pcb extent",w.pcb_extent)
if __name__=='__main__': main()
