nikolafilip/nibble/sim/nmos.py

"""Gate-level design description in Nibble's NMOS cell family (docs/gate-cell.md).

One cell = 2N7000s pulling an output down + one pull-up resistor.
  INV  : one transistor
  NAND : transistors in series (max 3)
  NOR  : transistors in parallel
  BUS  : open-drain driver, no pull-up (the hub has it)
  LED  : indicator: +5V -> 1k -> LED -> drain
A Design is emitted as a flat SPICE netlist (dev simulation) and drawn as a
KiCad sheet (ksch.py). Both come from the same gate list.
"""
import collections

PU_DEFAULT='47k'
MAX_SERIES=3
MAX_LOADS={'47k':8,'22k':16,'10k':32,'4.7k':64,'3.3k':96,'1k':300}   # rising-edge budget, see docs/gate-cell.md; 3.3k: the program card's rows (D048); 1k: the CLK and RST line drivers (D053)
LED_R='1k'

class Design:
    def __init__(self,name):
        self.name=name
        self.gates=[]            # dict(kind,out,ins,pu,group,note)
        self.inputs=set()        # primary inputs (header pins, constants)
        self.group='misc'
        self.ext_loads=collections.Counter()
    # ---- cells ----
    def _g(self,kind,out,ins,pu,note=''):
        ins=list(ins)
        if kind=='NAND': assert len(ins)<=MAX_SERIES, (out,ins)
        self.gates.append(dict(kind=kind,out=out,ins=ins,pu=pu,group=self.group,note=note)); return out
    def inv(self,out,a,pu=PU_DEFAULT,note=''):   return self._g('NAND',out,[a],pu,note)
    def nand(self,out,*ins,pu=PU_DEFAULT,note=''):return self._g('NAND',out,ins,pu,note)
    def nor(self,out,*ins,pu=PU_DEFAULT,note=''): return self._g('NOR',out,ins,pu,note)
    def bus(self,line,a,note=''):                  return self._g('BUS',line,[a],None,note)
    def led(self,name,a,note=''):                  return self._g('LED',name,[a],LED_R,note)
    def xor(self,out,a,b,pu=PU_DEFAULT):
        """7 transistors: out = NOR(NOR(a,b), AND(a,b))"""
        p=out+'_'
        self.nor(p+'n',a,b); self.nand(p+'a',a,b); self.inv(p+'d',p+'a')
        return self.nor(out,p+'n',p+'d',pu=pu)
    def ff(self,q,d,clk=None,qpu=PU_DEFAULT,ckn=None,ckb=None,rstn=None):
        """Positive-edge master-slave D flip-flop from NANDs (20 transistors, 18 when the clock pair ckn/ckb is shared).
        Master is transparent while clk is low, slave copies it on the rising edge.
        rstn: active-low asynchronous reset to 0 (two more transistors: a third input on the master's and the slave's
        feedback NAND). With rstn low the feedback NANDs are forced high, the master follows d AND ckn, and the slave's
        set NAND sees (d AND ckn) AND ckb, which the non-overlapping clock keeps at 0: q = 0 whatever the phase."""
        p=q+'_'
        if ckn is None: self.inv(p+'ckn',clk); ckn=p+'ckn'
        if ckb is None: self.inv(p+'ckb',ckn); ckb=p+'ckb'
        r=[rstn] if rstn else []
        self.inv(p+'dn',d)
        self.nand(p+'m1',d,ckn); self.nand(p+'m2',ckn,p+'dn')
        self.nand(p+'mq',p+'m1',p+'mqn'); self.nand(p+'mqn',p+'mq',p+'m2',*r)
        self.inv(p+'mqi',p+'mq')
        self.nand(p+'sa',p+'mq',ckb); self.nand(p+'sb',ckb,p+'mqi')      # not 's1'/'s2': <q>_s1 is the series node of the q NAND
        self.nand(q,p+'sa',p+'qn',pu=qpu); self.nand(p+'qn',q,p+'sb',*r)
        return q
    def latch(self,q,d,en,qpu=PU_DEFAULT,rstn=None):
        """Transparent D latch from NANDs (10 transistors): q follows d while en is high, holds when en is low.
        Used where a register is only ever loaded from a value that is stable for the whole tick and read
        when its enable is low (the sequencer's IR, OPR, RA and flags): enable = load line AND PH1, so the latch
        closes before the rising edge on which everything else changes. rstn as in ff()."""
        p=q+'_'; r=[rstn] if rstn else []
        self.inv(p+'dn',d)
        self.nand(p+'m1',d,en); self.nand(p+'m2',en,p+'dn')
        self.nand(q,p+'m1',p+'qn',pu=qpu); self.nand(p+'qn',q,p+'m2',*r)
        return q
    def pull(self,node,*ins,note=''):
        """An extra pull-down stack (transistors in series, no resistor) on a node that already has a pull-up:
        the node goes low when all of ins are high. Wired-AND onto a gate output, or an open-drain bus line."""
        assert len(ins)<=MAX_SERIES, (node,ins)
        return self._g('PULL',node,list(ins),None,note)
    def diode(self,row,col):
        """Diode-matrix crossing: the column is pulled high (through the diode) while the row is high."""
        return self._g('DIODE',col,[row],None)
    def pulldown(self,net,value='1Meg'):
        """Resistor from net to ground (a matrix column's pull-down)."""
        return self._g('PD',net,[],value)
    # ---- checks ----
    def outputs(self): return {g['out']:g for g in self.gates if g['kind'] not in ('BUS','LED','DIODE','PD','PULL')}
    def loads(self):
        c=collections.Counter(self.ext_loads)
        for g in self.gates:
            for i in g['ins']: c[i]+=1
        return c
    def check(self):
        outs=self.outputs(); c=self.loads(); pr=[]
        lower=collections.Counter(g['out'].lower() for g in self.gates if g['kind'] not in ('BUS','DIODE','PD','PULL'))
        pr+=[f"duplicate output {o}" for o,k in lower.items() if k>1]
        cols=set(g['out'] for g in self.gates if g['kind']=='DIODE'); pds=set(g['out'] for g in self.gates if g['kind']=='PD')
        for cc in cols:
            if cc not in pds: pr.append(f"matrix column {cc} has no pull-down")
        for g in self.gates:
            for i in g['ins']:
                if i not in outs and i not in self.inputs and i not in cols and i not in pds: pr.append(f"{g['out']}: input {i} is driven by nothing (floating gate)")   # a pull-down alone is a defined 0 (a matrix column no instruction uses yet)
        for net,n in c.items():
            if net in outs and n>MAX_LOADS[outs[net]['pu']]: pr.append(f"{net}: {n} loads on {outs[net]['pu']}")
        for g in self.gates:
            if g['kind']=='NAND' and len(g['ins'])>MAX_SERIES: pr.append(f"{g['out']}: {len(g['ins'])} in series")
        # a NAND's internal series nodes are <out>_s1, _s2: they must not collide with a net of that name
        nets=set(lower)|set(i.lower() for g in self.gates for i in g['ins'])
        for g in self.gates:
            if g['kind']=='NAND':
                for k in range(1,len(g['ins'])):
                    if f"{g['out']}_s{k}".lower() in nets: pr.append(f"{g['out']}: series node {g['out']}_s{k} collides with a net of that name")
        return pr
    def ntransistors(self): return sum(len(g['ins']) for g in self.gates if g['kind']!='DIODE')
    def nresistors(self): return sum(1 for g in self.gates if g['pu'])
    def nleds(self): return sum(1 for g in self.gates if g['kind']=='LED')
    def ndiodes(self): return sum(1 for g in self.gates if g['kind']=='DIODE')
    # ---- SPICE ----
    def spice(self,model='2N7000',vdd='VDD'):
        """Flat netlist lines. Node names are the net names; internal series nodes get _s<k>."""
        L=[]; q=1; r=1; pulls=collections.Counter()
        for g in self.gates:
            ins=g['ins']; out=g['out']; kind=g['kind']
            if kind=='LED':
                L.append(f"R{r} {vdd} {out}_a {g['pu']}"); r+=1
                L.append(f"D{r} {out}_a {out}_k LEDRED"); r+=1
                L.append(f"M{q} {out}_k {ins[0]} 0 {model}"); q+=1
                continue
            if kind=='BUS':
                L.append(f"M{q} {out} {ins[0]} 0 {model}"); q+=1
                continue
            if kind=='PULL':
                node=out; k0=pulls[out]; pulls[out]+=1
                for k,i in enumerate(ins):
                    nxt='0' if k==len(ins)-1 else f"{out}_p{k0}s{k+1}"
                    L.append(f"M{q} {node} {i} {nxt} {model}"); q+=1; node=nxt
                continue
            if kind=='DIODE':
                L.append(f"D{r} {ins[0]} {out} D1N4148"); r+=1
                continue
            if kind=='PD':
                L.append(f"R{r} {out} 0 {g['pu']}"); r+=1
                continue
            L.append(f"R{r} {vdd} {out} {g['pu']}"); r+=1
            if kind=='NAND':
                node=out
                for k,i in enumerate(ins):
                    nxt='0' if k==len(ins)-1 else f"{out}_s{k+1}"
                    L.append(f"M{q} {node} {i} {nxt} {model}"); q+=1; node=nxt
            else:
                for i in ins:
                    L.append(f"M{q} {out} {i} 0 {model}"); q+=1
        return L

LED_MODEL=".model LEDRED D(Is=1e-18 Rs=3 N=1.8 Cjo=20p)"
SW_MODEL=".model ODRV SW(VT=2.5 VH=0.2 RON=20 ROFF=1e9)"   # ideal open-drain driver for testbenches: closes to ground when its control is high
